thepinkmile/Enigma-NG/.copilot/checkpoints/179-stack-interposer-board-design-complete.md

# Checkpoint 179 — Stack-Interposer Board Design Complete

**Date:** 2026-07-25
**Session work:** Stack-Interposer Board design files created; connector decisions locked; library imports completed; front-view diagram added.

---

## Todo closed this session

| Todo | Status |
| --- | --- |
| `merge-create-stack-interposer` | ✅ done |

---

## Files created

| File | Description |
| --- | --- |
| `design/Electronics/Stack-Interposer/Design_Spec.md` | Full design specification — FR/DR, interconnects, stackup, BOM |
| `design/Electronics/Stack-Interposer/Board_Layout.md` | Pinout reference — J1/J2 connector MPNs, 2×15 pin map, mirror-routing note |
| `design/Datasheets/Samtec-sqt-tmmh-datasheet.md` | Markdown datasheet generated from Samtec-sqt-tmmh-datasheet.pdf |
| `design/Diagrams/renders/03-Mini-Stack-Front-View.png` | Front-elevation render of Rotor Mini-Stack |

---

## Files modified

| File | Change |
| --- | --- |
| `design/Diagrams/cypher-system-layout.drawio` | New page "Mini-Stack Front View" added (page 3) |
| `design/Electronics/Stack-Output/Design_Spec.md` | J6 connector updated: 2BHR-30-VUA → SQT-115-01-L-D-RA; DR-SOUT-06 updated |
| `design/Electronics/Stack-Input/Design_Spec.md` | J6 mating connector reference updated: 2BHR-30-VUA → TMMH-115-01-L-D-ES; DR-SIN-02 pinout ref resolved |
| `design/Datasheets/_generated_markdown_inventory.json` | Entry added for Samtec-sqt-tmmh-datasheet |
| `src/Electronics/Library/SamacSys_Parts.kicad_sym` | TMMH-115-01-L-D-ES + SQT-115-01-L-D-RA + 9 other parts completed |
| `src/Electronics/Library/SamacSys_Parts.lib` / `.dcm` | Same parts — legacy symbol/desc entries added |
| `src/Electronics/Library/SamacSys_Parts.mod` | Same parts — $MODULE blocks added |
| `src/Electronics/Library/SamacSys_Parts.pretty/` | TMMH-115-01-L-D-ES.kicad_mod + SQT-115-01-L-D-RA.kicad_mod + 9 others |
| `src/Electronics/Library/SamacSys_Parts.3dshapes/` | .stp files added for all imported parts |
| `src/Electronics/Library/3D_Models/` | .step files added for all imported parts |
| `src/Electronics/Library/LIBRARY_NOTES.md` | Component inventory + naming equivalences updated |
| `.copilot/agent-scripts/generate_markdown_datasheets.py` | Hardcoded `C:\` path replaced with `Path(__file__).resolve().parent.parent.parent` |
| `.copilot/todos/todos.sql` | merge-create-stack-interposer: pending → done |
| `.copilot/todos/index.md` | merge-create-stack-interposer: file link removed, status done |

---

## Key design decisions

| Decision | Detail |
| --- | --- |
| Stack-Interposer connectors | J1 and J2: TMMH-115-01-L-D-ES (Samtec 30-position 2×15 straight/vertical male) |
| Stack-Output J6 connector | Changed from 2BHR-30-VUA (Adam Tech THT male) to SQT-115-01-L-D-RA (Samtec RA female) — now matches Stack-Input J6 |
| Stack-Input J6 connector | SQT-115-01-L-D-RA (Samtec RA female) — unchanged, confirmed correct |
| Mirror-corrected routing | J1/J2 pin map is pin-to-pin (pin n → pin n); because connectors face each other in mirrored orientation, L2/L3 traces must be laid out as if mirrored (traces will cross). Rows preserved; documented in DR-SINT-04 and Board_Layout.md §3. |
| German data plate name | STAPELBRUCKE (printed on board as STAPELBRÜCKE) |
| Stackup | 4-layer standard GRS §2.3.1; GND pours on L1/L4; all signal traces on L2/L3 |

---

## Library imports completed

| Part | Type | Notes |
| --- | --- | --- |
| TMMH-115-01-L-D-ES | New — all 4 formats | Samtec 2×15 straight/vertical male; mating connector for Stack-Interposer J1/J2 |
| SQT-115-01-L-D-RA | Completed — was missing .pretty, .3dshapes, 3D_Models | Samtec 2×15 RA female; Stack-Input and Stack-Output J6 |
| 3310P-001-503L | Completed — was missing fp, .mod, .step | Bourns rotary potentiometer (Input-Cypher brightness dial) |
| APFA2507Y2G2C-C2 | Completed — was missing lib, dcm, fp, .mod, stp, step | Kingbright bicolor LED |
| DF40C-10DP/10DS/24DP/24DS/90DP/90DS-0.4V(51) | Completed — 6 parts | Hirose BtB connector family |
| PG151101S11 | Completed — was missing fp, .mod, .stp | Kailh hot-swap socket |

---

## Next session start point

Follow `.copilot/SESSION_START.md`, then read checkpoint 179 and resume with `merge-create-cypher-input`.

**Next sub-task: `merge-create-cypher-input`** — keyboard input panel board (ENC module BtB + mechanical keyboard switches + LED circuit). See `design-discussion-merge.md` for scope.

After Cypher-Input:
- `merge-create-cypher-output` — lightboard output panel
- `merge-ctl-dock-usb-allocation` → `merge-update-ctl-board`
- `merge-cypher-board-j3j6-pinouts`
