thepinkmile/Enigma-NG/design/Datasheets/Samtec-sqt-tmmh-datasheet.md

# Series: 2.00 mm (.079”) Pitch Socket & Terminal Strip

## Source

- **Source PDF:** [Samtec-sqt-tmmh-datasheet.pdf](Samtec-sqt-tmmh-datasheet.pdf)
- **Generated Markdown:** `Samtec-sqt-tmmh-datasheet.md`
- **Page count:** 8
- **Conversion method:** automated local PDF text extraction with pypdf/pdfplumber

## PDF Metadata

| Field | Value |
| :--- | :--- |
| Title | «Picture_Description» is depicted |
| Author | John Tozier |
| Subject |  |
| Creator | Microsoft® Word for Microsoft 365 |
| Producer | Microsoft® Word for Microsoft 365 |

## Extracted Technical Index

This markdown datasheet is meant to reduce the need to reopen the PDF during design work.
It preserves design-relevant extracted snippets first, followed by page-by-page text so the source content remains locally searchable.

### Part number and ordering information

- 4.8.1 Traditional Standoffs (SO) – Rigid design to statically support board-to-board applications. See / options here: SO - Board Stacking Standoff / 4.8.2 Jack Screw Standoffs (JSO) – Serve sam…
- construction facilitates the mating and unmating process. This is especially helpful for multiple / connector applications where the mating and unmating forces increase with the number of / conn…

### Pin, pad, and connection designations

- Product Specification / Series: 2.00 mm (.079”) Pitch Socket & Terminal Strip / Revision: A Date: September 26, 2025 © Samtec, Inc.
- 1.1 This specification covers performance, test ing and quality requirements for Samtec’s 0.51mm (.020”) square post / socket and terminal strip. All information contained in this specification …
- 1.1 This specification covers performance, test ing and quality requirements for Samtec’s 0.51mm (.020”) square post / socket and terminal strip. All information contained in this specification …
- 2.0 DETAILED INFORMATION / 2.1 Product prints, footprints, catalog pages, test reports and other specific, detailed information can be found at / SQT: <https://www.samtec.com/products/sqt;> TMMH…
- 3.0 TESTING / 3.1 Current Rating: 5.1 A (One pin powered per row) / 3.2 Voltage Rating: 250 VAC / 3.3 Operating Temperature Range: Gold plating: -55°C to +125°C
- Nitrogen gas infusion) in the reflow process to improve solderability. / 4.8 Hardware: Board-to-board standoffs are recommended to provide a robust mechanical connection. Samtec offers / two dif…
- two different types: / 4.8.1 Traditional Standoffs (SO) – Rigid design to statically support board-to-board applications. See / options here: SO - Board Stacking Standoff
- 5.0 ADDITIONAL RESOURCES / 5.1 For additional mechanical testing or product information, contact our Customer Engineering Support Group at / <CES@samtec.com>
- <CES@samtec.com> / 5.2 For additional information on high speed performance testing, contact our Signal Integrity Group at / <SIG@samtec.com>
- This Product Specification Sheet (“PSS”) is a brief summary of information related to the Product identified. As a summary, it should / only be used for the limited purpose of considering the pu…

### Specifications, ratings, and operating conditions

- Product Specification / Series: 2.00 mm (.079”) Pitch Socket & Terminal Strip
- See <www.samtec.com> for more information. / Product Specification / Series: 2.00 mm (.079”) Pitch Socket & Terminal Strip
- 1.0 SCOPE / 1.1 This specification covers performance, test ing and quality requirements for Samtec’s 0.51mm (.020”) square post / socket and terminal strip. All information contained in this sp…
- 1.1 This specification covers performance, test ing and quality requirements for Samtec’s 0.51mm (.020”) square post / socket and terminal strip. All information contained in this specification …
- 3.0 TESTING / 3.1 Current Rating: 5.1 A (One pin powered per row) / 3.2 Voltage Rating: 250 VAC / 3.3 Operating Temperature Range: Gold plating: -55°C to +125°C
- 3.1 Current Rating: 5.1 A (One pin powered per row) / 3.2 Voltage Rating: 250 VAC / 3.3 Operating Temperature Range: Gold plating: -55°C to +125°C / 3.4 Operating Humidity Range: up to 95% (Per …
- 3.5 Electrical: / ITEM TEST CONDITION REQUIREMENT STATUS / Withstanding Voltage EIA-364-20 (No Flashover, / Sparkover, or Breakdown) 750 VAC Pass / Insulation Resistance EIA-364-21 (1000 MΩ
- Normal Force EIA-364-04 30 grams minimum for Gold / interface Pass / Product Specification / Series: 2.00 mm (.079”) Pitch Socket & Terminal Strip
- ITEM TEST CONDITION RESULT STATUS / Thermal Shock / EIA-364-32 / Thermal Cycles: 100 (30 minute dwell)
- Thermal Shock / EIA-364-32 / Thermal Cycles: 100 (30 minute dwell) / Hot Temp: +85°C / Cold Temp: -55°C
- IR: >10,000 MΩ / Pass / Thermal Aging / (Temp Life) / EIA-364-17
- Exposure / LLCR: Δ 15 mΩ Pass / Product Specification / Series: 2.00 mm (.079”) Pitch Socket & Terminal Strip
- 4.1.2 Allowable final linear misalignment / Product Specification / Series: 2.00 mm (.079”) Pitch Socket & Terminal Strip
- 4.2.2 Allowable final angular misalignment / Product Specification / Series: 2.00 mm (.079”) Pitch Socket & Terminal Strip
- These guidelines should not be considered design requirements for all applications. / Samtec recommends testing interconnects on your boards in your process to guarantee optimum results. / Produ…
- 5.4 For RoHS, REACH or other environmental compliance information, contact our Product Environmental / Compliance Group at <PEC@samtec.com> / Product Specification / Series: 2.00 mm (.079”) Pitc…
- Page 8 / USE OF PRODUCT SPECIFICATION SHEET / This Product Specification Sheet (“PSS”) is a brief summary of information related to the Product identified. As a summary, it should
- USE OF PRODUCT SPECIFICATION SHEET / This Product Specification Sheet (“PSS”) is a brief summary of information related to the Product identified. As a summary, it should / only be used for the …

### Dimensions, package, and mechanical information

- 2.0 DETAILED INFORMATION / 2.1 Product prints, footprints, catalog pages, test reports and other specific, detailed information can be found at / SQT: <https://www.samtec.com/products/sqt;> TMMH…
- (Samtec defined)/ No damage Pass / 3.6 Mechanical: / ITEM TEST CONDITION RESULT STATUS
- No Events / Pass / Mechanical Shock / EIA-364-27 100 G, 6 milliseconds, / Half Sine wave, 12.3 fps, 3
- Nitrogen gas infusion) in the reflow process to improve solderability. / 4.8 Hardware: Board-to-board standoffs are recommended to provide a robust mechanical connection. Samtec offers / two dif…
- 5.0 ADDITIONAL RESOURCES / 5.1 For additional mechanical testing or product information, contact our Customer Engineering Support Group at / <CES@samtec.com>
- This Product Specification Sheet (“PSS”) is a brief summary of information related to the Product identified. As a summary, it should / only be used for the limited purpose of considering the pu…

### Formulas, equations, and configurable calculations

- TMMH Series / Other configurations available for: / Through Hole, Right Angle
- 1.1 This specification covers performance, test ing and quality requirements for Samtec’s 0.51mm (.020”) square post / socket and terminal strip. All information contained in this specification …
- ITEM TEST CONDITION RESULT STATUS / Durability EIA-364-09C 100 cycles Pass / Random Vibration / EIA-364-28 Condition V, Letter B / 7.56 G 'RMS', 50 to 2000 Hz, 2
- Test Temp: +25°C to +65°C Relative / Humidity: 90 to 95% / Test Duration: 240 hours / Visual Inspection: No Damage / LLCR: Δ 15 mΩ
- EIA-364-36 / Gas Exposure: Nitric Acid Vapor / Duration: 60 min. / Drying Temp.: 50°C +/- 3°C / Measurements: Within 1 hour of

### Reference designs, applications, and examples

- Page 6 / 4.3 Due to variances in equipment, solder pastes and applications (board design, component density, etc.), Samtec / does not specify a recommended reflow profile for our connectors. The…
- 4.3.1 / These guidelines should not be considered design requirements for all applications. / Samtec recommends testing interconnects on your boards in your process to guarantee optimum results.…
- two different types: / 4.8.1 Traditional Standoffs (SO) – Rigid design to statically support board-to-board applications. See / options here: SO - Board Stacking Standoff
- 4.8.2 Jack Screw Standoffs (JSO) – Serve same function as traditional standoffs but unique, nested / construction facilitates the mating and unmating process. This is especially helpful for mult…

## Page-by-Page Extracted Content

### Page 1

```text
Product Specification

Series: 2.00 mm (.079”) Pitch Socket & Terminal Strip

Revision: A Date: September 26, 2025 © Samtec, Inc.
 Page 1
SQT Series

 TMMH Series

Other configurations available for:

Through Hole, Right Angle

See www.samtec.com for more information.
```

### Page 2

```text
Product Specification

Series: 2.00 mm (.079”) Pitch Socket & Terminal Strip

Revision: A Date: September 26, 2025 © Samtec, Inc.
 Page 2

1.0 SCOPE

1.1 This specification covers performance, test ing and quality requirements for Samtec’s 0.51mm (.020”) square post
socket and terminal strip. All information contained in this specification is for a surface mount socket / surface mount
terminal mated configuration unless otherwise noted.

2.0 DETAILED INFORMATION

2.1 Product prints, footprints, catalog pages, test reports and other specific, detailed information can be found at
SQT: https://www.samtec.com/products/sqt; TMMH: https://www.samtec.com/products/tmmh

3.0 TESTING

3.1 Current Rating: 5.1 A (One pin powered per row)
3.2 Voltage Rating: 250 VAC
3.3 Operating Temperature Range: Gold plating: -55°C to +125°C
3.4 Operating Humidity Range: up to 95% (Per EIA-364-31)
3.5 Electrical:
ITEM TEST CONDITION REQUIREMENT STATUS
Withstanding Voltage EIA-364-20 (No Flashover,
Sparkover, or Breakdown) 750 VAC Pass
Insulation Resistance EIA-364-21 (1000 MΩ
minimum) >10,000 MΩ Pass
Contact Resistance
(LLCR) EIA-364-23 Δ 15 mΩ maximum
(Samtec defined)/ No damage Pass

3.6 Mechanical:

ITEM TEST CONDITION RESULT STATUS
Durability EIA-364-09C 100 cycles Pass
Random Vibration
EIA-364-28 Condition V, Letter B
7.56 G 'RMS', 50 to 2000 Hz, 2
hours per axis, 3 axis total , PSD
0.04 Nanosecond Event Detection:
EIA-364-87
Visual Inspection: No Damage
LLCR: Δ 15 mΩ
No Events
Pass
Mechanical Shock
EIA-364-27 100 G, 6 milliseconds,
Half Sine wave, 12.3 fps, 3
shocks/direction, 3 axis (18 total
shocks) Nanosecond Event
Detection: EIA-364-87
Visual Inspection: No Damage
LLCR: Δ 15 mΩ
No Events
Pass
Normal Force EIA-364-04 30 grams minimum for Gold
interface Pass
```

### Page 3

```text
Product Specification

Series: 2.00 mm (.079”) Pitch Socket & Terminal Strip

Revision: A Date: September 26, 2025 © Samtec, Inc.
 Page 3

3.7 Environmental:

ITEM TEST CONDITION RESULT STATUS
Thermal Shock
EIA-364-32
Thermal Cycles: 100 (30 minute dwell)
Hot Temp: +85°C
Cold Temp: -55°C
Hot/Cold Transition: Immediate
Visual Inspection: No Damage
LLCR: Δ 15 mΩ
DWV: 750 VAC
IR: >10,000 MΩ
Pass
Thermal Aging
(Temp Life)
EIA-364-17
Test Condition 4 @ 105°C
Condition B for 250 hours
Visual Inspection: No Damage
LLCR: Δ 15 mΩ Pass
Cyclic Humidity
EIA-364-31
Test Temp: +25°C to +65°C Relative
Humidity: 90 to 95%
Test Duration: 240 hours
Visual Inspection: No Damage
LLCR: Δ 15 mΩ
DWV: 750 VAC
IR: >10,000 MΩ
Pass
Gas Tight
EIA-364-36
Gas Exposure: Nitric Acid Vapor
Duration: 60 min.
Drying Temp.: 50°C +/- 3°C
Measurements: Within 1 hour of
Exposure
LLCR: Δ 15 mΩ Pass
```

### Page 4

```text
Product Specification

Series: 2.00 mm (.079”) Pitch Socket & Terminal Strip

Revision: A Date: September 26, 2025 © Samtec, Inc.
 Page 4

4.0 PROCESSING RECOMMENDATIONS:

4.1 Mating Alignment Requirements:

4.1.1 Allowable initial linear misalignment

4.1.2 Allowable final linear misalignment
```

### Page 5

```text
Product Specification

Series: 2.00 mm (.079”) Pitch Socket & Terminal Strip

Revision: A Date: September 26, 2025 © Samtec, Inc.
 Page 5

4.2 Mating Angle Requirements:

4.2.1 Allowable initial angular misalignment

4.2.2 Allowable final angular misalignment
```

### Page 6

```text
Product Specification

Series: 2.00 mm (.079”) Pitch Socket & Terminal Strip

Revision: A Date: September 26, 2025 © Samtec, Inc.
 Page 6

4.3 Due to variances in equipment, solder pastes and applications (board design, component density, etc.), Samtec
does not specify a recommended reflow profile for our connectors. The processing parameters provided by the
solder paste manufacturer should be employed and can usually be found on their website.

All of Samtec’s surface mount components are lead free reflow compatible and compliant with the profile
parameters detailed in IPC/JEDEC J-STD-020 which requires that components be capable of withstanding a peak
temperature of 260°C as well as 30 seconds above 255°C.

Samtec Recommended Temperature Profile Ranges (SMT)

Sn-Pb Eutectic Assembly

Preheat/Soak
(100°C-150°C)
Max Ramp Up
Rate
Reflow Time
(above 183°C)
Peak
Temp
Time within 5°C
of 235°C
Max Ramp
Down Rate
Time 25°C to
Peak Temp
60-120 sec. 3°C/s max. 40-150 sec. 235°C 20 sec. max. 6°C/s max. 6 min. max.

Pb-Free Assembly

Preheat/Soak
(150°C-200°C)
Max Ramp Up
Rate
Reflow Time
(above 217°C)
Peak
Temp
Time within 5°C
of 260°C
Max Ramp
Down Rate
Time 25°C to
Peak Temp
60-120 sec. 3°C/s max. 40-150 sec. 260°C 30 sec. max. 6°C/s max. 8 min. max.

4.3.1

These guidelines should not be considered design requirements for all applications.
Samtec recommends testing interconnects on your boards in your process to guarantee optimum results.
```

### Page 7

```text
Product Specification

Series: 2.00 mm (.079”) Pitch Socket & Terminal Strip

Revision: A Date: September 26, 2025 © Samtec, Inc.
 Page 7

4.4 Maximum Reflow Passes: The parts can withstand three reflow passes at a maximum component temperature of
260°C.

4.5 Stencil Thickness: The stencil thickness is 0.15mm [.006”].

4.6 Placement: Machine placement of the parts in the Z-axis is strongly recommended.

4.7 Reflow Environment: Samtec recommends the use of a low level oxygen environment (typically achieved through
Nitrogen gas infusion) in the reflow process to improve solderability.

4.8 Hardware: Board-to-board standoffs are recommended to provide a robust mechanical connection. Samtec offers
two different types:

4.8.1 Traditional Standoffs (SO) – Rigid design to statically support board-to-board applications. See
options here: SO - Board Stacking Standoff

4.8.2 Jack Screw Standoffs (JSO) – Serve same function as traditional standoffs but unique, nested
construction facilitates the mating and unmating process. This is especially helpful for multiple
connector applications where the mating and unmating forces increase with the number of
connectors used. See options here: JSO - Jack Screw Standoffs

4.9 Cleaning: Samtec, Inc. has verified that our connectors may be cleaned in accordance with the solvents
 and conditions designated in the EIA-364-11 standard.

5.0 ADDITIONAL RESOURCES

5.1 For additional mechanical testing or product information, contact our Customer Engineering Support Group at
CES@samtec.com

5.2 For additional information on high speed performance testing, contact our Signal Integrity Group at
SIG@samtec.com

5.3 For additional processing information, contact our Interconnect Processing Group at IPG@samtec.com.

5.4 For RoHS, REACH or other environmental compliance information, contact our Product Environmental
Compliance Group at PEC@samtec.com
```

### Page 8

```text
Product Specification

Series: 2.00 mm (.079”) Pitch Socket & Terminal Strip

Revision: A Date: September 26, 2025 © Samtec, Inc.
 Page 8

USE OF PRODUCT SPECIFICATION SHEET

This Product Specification Sheet (“PSS”) is a brief summary of information related to the Product identified. As a summary, it should
only be used for the limited purpose of considering the purchase/use of Product. For specific, detailed information, includi ng but not
limited to testing and Product footprint, refer to Section 2.0 of this document and the links there provided to test reports and prints. This
PSS is the property of Samtec, Inc. (“Samtec”) and contains proprietary information of Samtec, our various licensors, or both . Samtec
does not grant express or implied rights or license under any patent, copyright, trademark or other proprietary rights and th e use of the
PSS for building, reverse engineering or replication is strictly prohibited. By using the PSS, the user agrees to not infring e, directly or
indirectly, upon any intellectual property rights of Samtec and acknowledges that Samtec, our various licensors, or both own all
intellectual property therein. The PSS is presented “AS IS”. While Samtec makes every effort to present excellent information, the PSS
is only provided as a guideline and does not, therefore, warrant it is without error or defect or that the PSS contains all necessary and/or
relevant information about the Product. The user agrees that all access and use of the PSS is at its own risk. NO WARRANTIES
EXPRESSED OR IMPLIED, INCLUDING ANY WARRANTY OF MERCHANTABILITY, FITNESS FOR A PARTICULAR
PURPOSE OR OF ANY KIND WHATSOEVER ARE PROVIDED.
```
