thepinkmile/Enigma-NG/.copilot/todos/design-discussion-merge.md

# Merge design discussions into main design

**ID:** design-discussion-merge
**Status:** in-progress
**Category:** Electronics / Software / Mechanical
**Source:** User direction 2026-07-05
**Blocked by:** —

---

## Description

Top-level tracking item for the full migration of all decisions from
.copilot/discussions/cypher-system-discussion/ into the main design documentation.
Covers new board creation, CTL board updates, GRS updates, reviews, and BOM work.

## Notes

Sub-tasks (in approximate execution order):
1. merge-grs-6layer-stackup — GRS §2.3.x for 6-layer boards (NEXT)
2. merge-create-cypher-board — Cypher Board Design_Spec and Board_Layout (in-progress)
3. merge-cypher-board-j3j6-pinouts — Full 50-pin J3-J6 allocation
4. merge-ctl-dock-usb-allocation — USB D+/D- pin alloc in J1
5. merge-create-stack-input, merge-create-stack-output, merge-create-stack-blanking, merge-create-stack-interposer
6. merge-update-ctl-board
7. merge-create-cypher-input, merge-create-cypher-output
8. merge-update-top-level-docs
9. merge-remove-old-boards
10. merge-consistency-review, merge-missing-components, merge-final-review
