thepinkmile/Enigma-NG/.copilot/checkpoints/175-unified-cypher-extension-spec-created-awaiting-completeness-review.md

# Checkpoint 175: Unified Cypher/Extension Spec Created; Completeness Review Pending

**Date**: 2026-06-07  
**Status**: Complete  
**Scope**: Discussion/state consolidation only (no design implementation changes)

## Summary

Created a consolidated point-in-time design modification specification:

- `.copilot/discussions/cypher-extension-unified-discussion.md`

This file merges architecture, grounding model, interconnect maps, signal flows,
component baseline, and active-design modification tracking into one standalone
discussion/specification document.

## Work Completed

1. Created unified specification file with embedded implementation-critical content:
   - new board architecture and lifecycle intent,
   - `GND_CHASSIS` domain model + single-point bond constraints,
   - chassis ring geometry + connector-zone caveat,
   - Cypher interconnect pin map,
   - passive base-board 2x15 map,
   - `SIG-BLOCK-A..I` group table and explicit electronic flow descriptions,
   - consolidated component/procurement baseline,
   - active-design change matrix by standards/board.
2. Updated naming consistency (`GND_CHASSIS`) across the cypher grounding discussion.
3. Aligned board naming to active names (Cypher, Stack-Input, Stack-Output, Stack-Blanking).
4. Updated topology visual orientation in the unified file; user then finalized both unified and source discussion diagrams.
5. Synced session state files for new-session continuity:
   - `.copilot/plan.md`
   - `.copilot/handoff.md`

## Current Risk / Pending Validation

The unified file is now structurally complete, but user has flagged likely missing
historical detail due to the size/depth of the original extension discussion.

Pending work is a user-led completeness pass to identify gaps, followed by direct
patches to the unified file.

## Files Updated

- `.copilot/discussions/cypher-extension-unified-discussion.md` (new)
- `.copilot/discussions/cypher-block-connectors.md` (multiple consolidation/clarity updates)
- `.copilot/discussions/extension-mechanical-usage.md` (diagram iteration; final state user-adjusted)
- `.copilot/plan.md`
- `.copilot/handoff.md`
- `.copilot/checkpoints/index.md`
- `.copilot/checkpoints/175-unified-cypher-extension-spec-created-awaiting-completeness-review.md` (new)

## Next Start Hint

Resume from the unified specification review:

1. Read `.copilot/discussions/cypher-extension-unified-discussion.md` end-to-end.
2. Capture missing-detail list from user.
3. Patch only the unified file until user confirms it is complete and self-contained.
4. Do not start implementation into active design files until explicit user instruction.
