thepinkmile/Enigma-NG/design/Datasheets/2bhr-xx-vua-data-sheet.md

# Adam Tech 2BHR-XX-VUA 2.00 mm dual-row box header (dual-keyed)

## Source Reference

- Source PDF: [2bhr-xx-vua-data-sheet.pdf](2bhr-xx-vua-data-sheet.pdf)
- Source path: `design\Datasheets\2bhr-xx-vua-data-sheet.pdf`
- Generated markdown: `2bhr-xx-vua-data-sheet.md`
- Structured datasheet (JSON): [2BHR-30-VUA-structured-datasheet.json](2BHR-30-VUA-structured-datasheet.json) — comprehensive specifications generated via Google AI analysis
- Page count: 1
- Extracted text characters: 0
- Empty extraction pages: 1
- Conversion method: automated local PDF text extraction with pypdf and pdfplumber
- **Correction note (2026-06-06):** Pitch corrected from incorrectly assumed 2.54 mm to actual 2.00 mm per datasheet review. All specifications verified against Google AI–generated structured datasheet.

## Reviewed Summary

- Exact family: Adam Tech 2BHR-XX-VUA.
- Product: 2-row dual-keyed box header, vertical PCB mount, 2.00 mm pitch (0.0787 in), gold-flash plated.
  Dual-keyed variant of the BHR-XX-VUA series; polarisation key is present at both ends of the
  shroud to prevent misinsertion from either orientation.
- Pin counts available: series covers multiple positions (XX = number of positions per row x 2).
  The 30-pin variant (2x15) is `2BHR-30-VUA`.
- Dimensions / pattern: based on 2.00 mm pitch spacing - dimensions scale accordingly from base dimensions.
- Electrical / environmental: 250 VAC max, 2 A max per pin, 20 mΩ max contact resistance,
  5000 MΩ min insulation resistance, 500 VAC / minute dielectric withstand, -40 to +105 °C.
- Materials: PBT or Nylon 6T UL94V-0 insulator (black), brass or phosphor bronze contacts, gold flash over nickel underplate.
- Mating durability: 100 cycles minimum.
- Dimensions (2x15 variant): overall length A = 35.10 mm, shroud length B = 33.10 mm.

## Approved Part Numbers - 2BHR-30-VUA (30-pin, 2x15)

| Supplier | Part Number | Notes |
| :--- | :--- | :--- |
| DigiKey | 2057-2BHR-30-VUA-ND | MOQ 3000 (for reference only) |
| Mouser | 737-2BHR-30-VUA | MOQ 3000 (for reference only) |
| JLCPCB | C17346400 | MOQ 3 |

## Extraction Notes

- Native extraction was empty; this is an image-only mechanical drawing PDF.
- Reviewed summary and electrical specifications are taken from the same Adam Tech series datasheet
  as `bhr-xx-vua-data-sheet.md` - the 2BHR variant shares identical electrical ratings.

## Page-by-Page Extracted Content

### Page 1

_No text could be extracted from this page with the current local extractor. This is a
mechanical drawing / image-only PDF._
