thepinkmile/Enigma-NG/design/Datasheets/Samtec-sqt-1xx-xx-xxx-x-xxx-xxx-mkt-datasheet.md

# Samtec SQT-115-01-L-D-RA — 30-position shrouded rugged PCB socket (right-angle, 2.00 mm pitch)

## Source Reference

- Source PDF: [Samtec-sqt-1xx-xx-xxx-x-xxx-xxx-mkt-datasheet.pdf](Samtec-sqt-1xx-xx-xxx-x-xxx-xxx-mkt-datasheet.pdf)
- Source path: `design\Datasheets\Samtec-sqt-1xx-xx-xxx-x-xxx-xxx-mkt-datasheet.pdf`
- Generated markdown: `Samtec-sqt-1xx-xx-xxx-x-xxx-xxx-mkt-datasheet.md`
- Page count: 3
- Conversion method: automated local PDF text extraction with pypdf/pdfplumber

## Reviewed Summary

- **Exact family:** Samtec SQT-1XX-XX-XXX-X-XXX-XXX series
- **Product:** 30-position (15 × 2) shrouded rugged PCB socket, female IDC, right-angle mount, 2.00 mm pitch (0.0787 in)
- **Mating:** Mates with 2BHR-XX-VUA male headers (same pitch, dual-row configuration)
- **Contacts:** Brass, gold-flash plated
- **Insulation:** PBT (polybutylene terephthalate)
- **Electrical:** 2 A per contact, 500 V AC (1 min dielectric), 100-cycle durability per IPC-1212
- **Operating range:** −40°C to +105°C
- **Compliance:** Lead-free, RoHS-compliant

---

## PDF Metadata

| Field | Value |
| :--- | :--- |
| Title | SQT-1XX-XX-XXX-X-XXX-XXX-MKT |
| Author | SAMTECNT\34506 (DG-TOBINQIN) |
| Subject | - |
| Creator | SOLIDWORKS 2019 SP5.0 (2019304) |
| Producer | SOLIDWORKS PDF Publisher |

## Extracted Technical Index

This markdown datasheet is meant to reduce the need to reopen the PDF during design work.
It preserves design-relevant extracted snippets first, followed by page-by-page text so the source content remains locally searchable.

### Part number and ordering information

- -STL: 30µ" SELECTIVE GOLD IN CONTACT AREA, / SnPb ON TAIL. / POLARIZATION OPTION / -XXX: INDICATES POSITION / (SEE NOTE 10)
- -XXX: INDICATES POSITION / (SEE NOTE 10) / OPTION / -RA: RIGHT ANGLE / (-01 LEAD STYLE, ROWS -S, -D, -T ONLY)
- 02 / \* = NOT RELEASED FOR PRODUCTION / \*\* = MW OPTION, DO NOT DESIGN IN, SAMTEC WILL / ONLY SUPPORT EXISTING BUSINESS 02/06/2002 / C

### Pin, pad, and connection designations

- \* = NOT RELEASED FOR PRODUCTION / \*\* = MW OPTION, DO NOT DESIGN IN, SAMTEC WILL / ONLY SUPPORT EXISTING BUSINESS 02/06/2002 / C / C
- (5 POS MIN, 30 POS MAX) / \*\* -MW OPION, DO NOT DESIGN IN. SAMTEC WILL / ONLY SUPPORT EXISTING BUSINESS 2/06/02. / SHEET OF / 2MM SOCKET STRIP ASSEMBLY

### Specifications, ratings, and operating conditions

- (PER ROW) / -01 (SEE NOTE 3) / ROW SPECIFICATION / -S: SINGLE (USE SQT-61-S) / -D: DOUBLE (USE SQT-62-D)
- LEAD STYLE / (SEE TABLE 1) / PLATING SPECIFICATION / -F: 3µ" SELECTIVE GOLD IN CONTACT AREA, / MATTE TIN ON TAIL.
- UNLESS OTHERWISE SPECIFIED, / DIMENSIONS ARE IN INCHES. / TOLERANCES ARE: / DECIMALS ANGLES / .XX: .01 [.3] 2

### Dimensions, package, and mechanical information

- SHEET OF / UNLESS OTHERWISE SPECIFIED, / DIMENSIONS ARE IN INCHES. / TOLERANCES ARE: / DECIMALS ANGLES
- SQT-1XX-XX-XXX-X-XXX-XXX / DWG. NO. / DESCRIPTION:DO NOT SCALE DRAWING / BRATCHER 07/24/1995 31 / SHEET SCALE: 2:1
- MAX BOW ALLOWED: .004[.10] IN/IN / NOTES: / 1. REPRESENTS A CRITICAL DIMENSION. / 2. MINIMUM CONTACT RETENTION: .5 LB / 3. -01 POSITION OFFERED FOR SINGLE ROW& ONLY FOR -S, -D, & -T
- DWG. NO. / DESCRIPTION: / DO NOT SCALE DRAWING / BRATCHER 07/24/1995 32 / SHEET SCALE: 2:1
- DWG. NO. / DESCRIPTION: / DO NOT SCALE DRAWING / BRATCHER 07/24/1995 33 / SHEET SCALE: 1:1

### Formulas, equations, and configurable calculations

- No reliable text snippet was automatically extracted for this category. Review the raw page text below.

### Reference designs, applications, and examples

- No reliable text snippet was automatically extracted for this category. Review the raw page text below.

## Page-by-Page Extracted Content

### Page 1

```text
THIS DOCUMENT CONTAINS CONFIDENTIAL AND
PROPRIETARY INFORMATION AND ALL DESIGN,
MANUFACTURING, REPRODUCTION, USE, PATENT RIGHTS
AND SALES RIGHTS ARE EXPRESSLY RESERVED BY SAMTEC,
INC. THIS DOCUMENT SHALL NOT BE DISCLOSED, IN WHOLE
OR PART, TO ANY UNAUTHORIZED PERSON OR ENTITY NOR
REPRODUCED, TRANSFERRED OR INCORPORATED IN ANY
OTHER PROJECT IN ANY MANNER WITHOUT THE EXPRESS
WRITTEN CONSENT OF SAMTEC, INC.
PROPRIETARY NOTE* *
DO NOT
SCALE FROM
THIS PRINT
No OF POSITIONS
-02 THRU -50
 (PER ROW)
-01 (SEE NOTE 3)
ROW SPECIFICATION
-S: SINGLE (USE SQT-61-S)
-D: DOUBLE (USE SQT-62-D)
-T: TRIPLE (USE SQT-62-T)
-Q: QUAD (USE SQT-62-Q)
-5: FIVE ROW (USE SQT-62-5)
-6: SIX ROW (USE SQT-62-6)
LEAD STYLE
(SEE TABLE 1)
PLATING SPECIFICATION
-F: 3µ" SELECTIVE GOLD IN CONTACT AREA,
 MATTE TIN ON TAIL.
-L: 10µ" SELECTIVE GOLD IN CONTACT AREA,
 MATTE TIN ON TAIL.
-G: 20µ" SELECTIVE GOLD IN CONTACT AREA,
 3µ" SELECTIVE GOLD ON TAIL.
-S: 30µ" SELECTIVE GOLD IN CONTACT AREA,
 MATTE TIN ON TAIL.
-H: 50µ" SELECTIVE GOLD IN CONTACT AREA,
 3µ" SELECTIVE GOLD ON TAIL.
-FM: 3µ" SELECTIVE GOLD IN CONTACT AREA,
 MATTE TIN ON TAIL.
-LM: 10µ" SELECTIVE GOLD IN CONTACT AREA,
 MATTE TIN ON TAIL.
-SM: 30µ" SELECTIVE GOLD IN CONTACT AREA,
 MATTE TIN ON TAIL.
-STL: 30µ" SELECTIVE GOLD IN CONTACT AREA,
 SnPb ON TAIL.
POLARIZATION OPTION
-XXX: INDICATES POSITION
 (SEE NOTE 10)
OPTION
-RA: RIGHT ANGLE
 (-01 LEAD STYLE, ROWS -S, -D, -T ONLY)
 (NOT AVAILABLE ON -Q, -5 & -6 ROWS)
 (SINGLE, DOUBLE, TRIPLE ROW: SEE FIG 2, SHT 2)
 *-SD1: SOLDER DONUT (SEE FIG 3, SHT 2)
 (AVAILABLE ON -S, -D, -T ONLY)
**-MW: METAL WASHER (SHT 2, SEE FIG 4)
 (AVAILABLE ON LEAD STYLES -01 & -03 ONLY)
 (5 POS MIN, 30 POS MAX, .300 MAX TAIL)
SQT-1XX-XX-XXX-X-XXX-XXX
.015 0.38
REF
.250 6.35
REF
"A"
.0197 0.500
SQ REF (TYP)
.064 1.63 REF
2 MAX SWAY
(EITHER DIRECTION)
FIG 1
SQT-120-01-XX-6 SHOWN
(SEE NOTE 7)
{(No OF POS x .0787[2.000]) + .0117[0.300] ± .010[0.25]
(No OF POS x .0787[2.000] - .0787[2.000] REF
.0787 2.000
REF (TYP)
01
"B" REF
2 MAX SWAY
(EITHER DIRECTION)
C-79-XX-X
(SEE TABLE 1)
SQT-XX-X
(SEE TABLE 3)
01 02
(POSITON PATTERN SINGLE ROW ONLY)
C
02
 * = NOT RELEASED FOR PRODUCTION
** = MW OPTION, DO NOT DESIGN IN, SAMTEC WILL
 ONLY SUPPORT EXISTING BUSINESS 02/06/2002
C
C
SHEET OF
UNLESS OTHERWISE SPECIFIED,
DIMENSIONS ARE IN INCHES.
TOLERANCES ARE:
DECIMALS ANGLES
.XX: .01 [.3] 2
.XXX: .005 [.13]
.XXXX: .0020 [.051]
MATERIAL:
2MM SOCKET STRIP ASSEMBLY
BY:
SQT-1XX-XX-XXX-X-XXX-XXX
DWG. NO.
DESCRIPTION:DO NOT SCALE DRAWING
BRATCHER 07/24/1995 31
SHEET SCALE: 2:1
INSULATOR: LCP, UL 94 VO, COLOR: BLACK
CONTACT: PHOS BRONZE
REVISION CJ
F:\DWG\MISC\MKTG\SQT-1XX-XX-XXX-X-XXX-XXX-MKT.SLDDRW
MAX BOW ALLOWED: .004[.10] IN/IN
NOTES:
1. REPRESENTS A CRITICAL DIMENSION.
2. MINIMUM CONTACT RETENTION: .5 LB
3. -01 POSITION OFFERED FOR SINGLE ROW& ONLY FOR -S, -D, & -T
 ROWS RIGHT ANGLE ONLY.
4. SEE TABLE 2, SHEET 3 FOR PACKAGING.
5. STOCK 62 POSITION FOR -D AND 61 POSITION FOR
 -S, -01 LEAD STYLE ONLY. TO BE CUT TO POSITION FOR CUSTOMER.
6. MAXIMUM BURR: .005[0.13]
7. ENDWALL AFTER CUTTING: .031[.79]+/-.004[0.10], VOIDS MAY BE PRESENT.
 CONTACTS MUST NOT BE VISIBLE THROUGH THE ENDWALL
8. MAXIMUM CUT FLASH: .020[0.50]
9. MAXIMUM HEIGHT VARIATION: .005[0.13]
10. INSERT PK-07-N INTO SPECIFIED POSITION AND BREAK OFF TAB.
520 PARK EAST BLVD, NEW ALBANY, IN 47150
PHONE: 812-944-6733 FAX: 812-948-5047
e-Mail info@SAMTEC.com code 55322
```

### Page 2

```text
THIS DOCUMENT CONTAINS CONFIDENTIAL AND
PROPRIETARY INFORMATION AND ALL DESIGN,
MANUFACTURING, REPRODUCTION, USE, PATENT RIGHTS
AND SALES RIGHTS ARE EXPRESSLY RESERVED BY SAMTEC,
INC. THIS DOCUMENT SHALL NOT BE DISCLOSED, IN WHOLE
OR PART, TO ANY UNAUTHORIZED PERSON OR ENTITY NOR
REPRODUCED, TRANSFERRED OR INCORPORATED IN ANY
OTHER PROJECT IN ANY MANNER WITHOUT THE EXPRESS
WRITTEN CONSENT OF SAMTEC, INC.
PROPRIETARY NOTE* *
TOP VIEW
TOOLING
OPERATOR
REEL
FRONT VIEW
OPERATORREEL
WASHER REEL ASSEMBLY
ORIENTATION VIEW
90°
.600 15.24.208 5.28
.050±.010 1.27±0.25
.0787±.0050 (TYP)2.000±0.127
.090±.010 2.29±0.254
R.025 0.64
SQT-XX-X
(SEE TABLE 3)
C-79-53-X
(SHEAR TO LENGTH)
C-79-12-X
(SHEAR TO LENGTH)
C-79-12-X
(SHEAR TO LENGTH)
C
01
02
01 02
(POSITON PATTERN SINGLE row ONLY).0200 0.508
REFSD1
'A'
.065 1.65
REF
.025 0.64
REF
DETAIL 'A'
SCALE 4 : 1
'B'
.0030 MAX0.076
MEASURE AT THE TAIL
.0050 MAX0.127
MEASURE AT THE TAIL
2 MAX SWAY
(EITHER DIRECTION)
DETAIL 'B'
SCALE 6 : 1
SQT-01-MW-T
90°
.600 15.24
IN PROCESS 3
(LEAD STYLE -01-T-RA)
IN PROCESS 1
(LEAD STYLE -01-S,D,T-RA)
IN PROCESS 2
(LEAD STYLE -01-D,T-RA)
FIG 2
-RA: RIGHT ANGLE
(LEAD STYLE -01-S,D,T)
FIG 3
*-SD1: SOLDER DONUT
(ONE PER POSITION)
(ROW STYLE -S,-D,-T & -Q ONLY)
*NOT ENGINEERING APPROVED
FIG 4
**-MW: METAL WASHER
(ONE PER POSITION)
(AVAILABLE ON LEADSTYLES -01 & -03 ONLY
(5 POS MIN, 30 POS MAX)
** -MW OPION, DO NOT DESIGN IN. SAMTEC WILL
ONLY SUPPORT EXISTING BUSINESS 2/06/02.
SHEET OF
2MM SOCKET STRIP ASSEMBLY
BY:
SQT-1XX-XX-XXX-X-XXX-XXX
DWG. NO.
DESCRIPTION:
DO NOT SCALE DRAWING
BRATCHER 07/24/1995 32
SHEET SCALE: 2:1
REVISION CJ
F:\DWG\MISC\MKTG\SQT-1XX-XX-XXX-X-XXX-XXX-MKT.SLDDRW
520 PARK EAST BLVD, NEW ALBANY, IN 47150
PHONE: 812-944-6733 FAX: 812-948-5047
e-Mail info@SAMTEC.com code 55322
```

### Page 3

```text
THIS DOCUMENT CONTAINS CONFIDENTIAL AND
PROPRIETARY INFORMATION AND ALL DESIGN,
MANUFACTURING, REPRODUCTION, USE, PATENT RIGHTS
AND SALES RIGHTS ARE EXPRESSLY RESERVED BY SAMTEC,
INC. THIS DOCUMENT SHALL NOT BE DISCLOSED, IN WHOLE
OR PART, TO ANY UNAUTHORIZED PERSON OR ENTITY NOR
REPRODUCED, TRANSFERRED OR INCORPORATED IN ANY
OTHER PROJECT IN ANY MANNER WITHOUT THE EXPRESS
WRITTEN CONSENT OF SAMTEC, INC.
PROPRIETARY NOTE* *
SQT-1XX-05-XX-X
(LOCATE PLUG AS SHOWN)
(SEE TABLE 2)
PACKAGING VIEWS
SQT-1XX-03-XX-6 SHOWN
(SEE TABLE 2)
SQT-1XX-01-XX-D-RA SHOWN
(LOCATE PLUG AS SHOWN)
(SEE TABLE 2)
SQT-1XX-02-XX-D
(LOCATE PLUG AS SHOWN)
(SEE TABLE 2)
SQT-1XX-01-XX-D
(SEE TABLE 2)
SQT-1XX-03-XX-S SHOWN
(SEE TABLE 2)
SHEET OF
2MM SOCKET STRIP ASSEMBLY
BY:
DWG. NO.
DESCRIPTION:
DO NOT SCALE DRAWING
BRATCHER 07/24/1995 33
SHEET SCALE: 1:1
REVISION CJ
F:\DWG\MISC\MKTG\SQT-1XX-XX-XXX-X-XXX-XXX-MKT.SLDDRW
520 PARK EAST BLVD, NEW ALBANY, IN 47150
PHONE: 812-944-6733 FAX: 812-948-5047
e-Mail info@SAMTEC.com code 55322
SQT-1XX-XX-XXX-X-XXX-XXX
```
