thepinkmile/Enigma-NG/design/Datasheets/Yageo-AT_series-datasheet.md

# ⚫ Moisture sensitivity level: MSL 1

## Source

- **Source PDF:** [Yageo-AT_series-datasheet.pdf](Yageo-AT_series-datasheet.pdf)
- **Generated Markdown:** `Yageo-AT_series-datasheet.md`
- **Page count:** 9
- **Conversion method:** automated local PDF text extraction with pypdf/pdfplumber

## PDF Metadata

| Field | Value |
| :--- | :--- |
| Title |  |
| Author | SerenaC |
| Subject |  |
| Creator | 適用於 Microsoft 365 的 Microsoft® Word |
| Producer | 適用於 Microsoft 365 的 Microsoft® Word |

## Extracted Technical Index

This markdown datasheet is meant to reduce the need to reopen the PDF during design work.
It preserves design-relevant extracted snippets first, followed by page-by-page text so the source content remains locally searchable.

### Part number and ordering information

- SERIES AT 0402 to 1206 / ORDERING INFORMATION - GLOBAL PART NUMBER / Part number is identified by the serie s name , size, tolerance, packaging / type , temperature coefficient, t aping reel and…
- ORDERING INFORMATION - GLOBAL PART NUMBER / Part number is identified by the serie s name , size, tolerance, packaging / type , temperature coefficient, t aping reel and resistance value.
- ⚫ Non-forbidden materials used in / products/production / ORDERING EXAMPLE / The orde ring code of a AT0402 chip resistor, TC 25 value 56Ω with ± / 0.5% tolerance, supplied in 7 -inch tape reel …
- 2. On customized label, "LFP" or specific symbol can be printed. / GLOBAL PART NUMBER / A T XXXX X X X XX XXXXX L / (1) (2) (3) (4) (5) (6) (7)
- 1K = 1,000Ω / (7) DEFAULT CODE / Letter L is the system default code for ordering only. (NOTE) / Chip Resistor Surface Mount
- SERIES AT 0402 to 1206 / MARKING / AT0402 / No marking
- MARKING / AT0402 / No marking / AT0603
- E-96 series: including values 10/11/13/15/20/75 of E -24 series, 3 digits / E-24 series: exception values 10/11/13/15/20/75 of E -24 series, one short bar / under marking letter / AT0805 / AT1206
- NOTE / For further marking information, please see special data sheet “Chip resistors marking ”. / Fig. 4 Value = 10 K Ω
- protective coat / marking layer / resistive layer / inner electrode
- ±10 (B) 50 ≤ R < 20K / ±5 (A) 50 ≤ R < 20K --- / NOTE : 1. Global part number (code 7) / 2. Global part number (code 9) / TYPE L (mm) W (mm) H (mm) I1 (mm) I2 (mm)>
- ±5 (A) 50 ≤ R < 20K --- / NOTE : 1. Global part number (code 7) / 2. Global part number (code 9) / TYPE L (mm) W (mm) H (mm) I1 (mm) I2 (mm) / AT0402 1.00 ±0.10 0.50 ±0.05 0.30 ±0.05 0.20 ±0.10 …>

### Pin, pad, and connection designations

- ORDERING INFORMATION - GLOBAL PART NUMBER / Part number is identified by the serie s name , size, tolerance, packaging / type , temperature coefficient, t aping reel and resistance value. / SCOPE
- (3) PACKAGING TYPE / R = Paper taping reel / (4) TEMPERATURE COEFFICIENT OF RESISTANCE / A = ± 5 ppm/°C
- D = ± 25 ppm/°C / E = ± 50 ppm/°C / (5) TAPING REEL / 07 = 7 inch dia. Reel / (6) RESISTANCE VALUE
- For recommended footprint and soldering profiles, please see th e spec ial data sheet “Chip resistors moun ting”. / PRODUCT TYPE PATKING STYLE REEL DIMENSION QUANTITY PER REEL / AT0402 Paper tap…
- PRODUCT TYPE PATKING STYLE REEL DIMENSION QUANTITY PER REEL / AT0402 Paper taping reel 7" (178 mm) 10,000 Units / AT0603 Paper taping reel 7" (178 mm) 5,000 Units / AT0805 Paper taping reel 7" (…
- AT0402 Paper taping reel 7" (178 mm) 10,000 Units / AT0603 Paper taping reel 7" (178 mm) 5,000 Units / AT0805 Paper taping reel 7" (178 mm) 5,000 Units / AT1206 Paper taping reel 7" (178 mm) 5,0…
- AT0603 Paper taping reel 7" (178 mm) 5,000 Units / AT0805 Paper taping reel 7" (178 mm) 5,000 Units / AT1206 Paper taping reel 7" (178 mm) 5,000 Units / NOTE: for paper tape and reel specificati…
- SMD conditions: / (a) Method B, aging 4 hours at 155 °C dry heat, / dipping at 235± 3 °C for 5± 0.5 seconds. / (b) Method B, steam aging 8 hours, dipping at / 215± 3 °C for 5± 0.5 seconds.
- (a) Method B, aging 4 hours at 155 °C dry heat, / dipping at 235± 3 °C for 5± 0.5 seconds. / (b) Method B, steam aging 8 hours, dipping at / 215± 3 °C for 5± 0.5 seconds. / (c) Method D, steam a…
- (b) Method B, steam aging 8 hours, dipping at / 215± 3 °C for 5± 0.5 seconds. / (c) Method D, steam aging 8 hours, dipping at / 260± 3 °C for 7± 0.5 seconds

### Specifications, ratings, and operating conditions

- sizes 0402/0603/0805/1206 / RoHS compliant / Product specification – April 15, 2021 V.6 / Chip Resistor Surface Mount
- Apr. 15, 2021 V6 / Product specification / 2
- ORDERING INFORMATION - GLOBAL PART NUMBER / Part number is identified by the serie s name , size, tolerance, packaging / type , temperature coefficient, t aping reel and resistance value.
- SCOPE / This specification describes AT0402 to / AT1206 high precision-high stability / chip resistors made by thin film
- ORDERING EXAMPLE / The orde ring code of a AT0402 chip resistor, TC 25 value 56Ω with ± / 0.5% tolerance, supplied in 7 -inch tape reel is: AT0402DRD0756RL. / NOTE / 1. All our Rchip products me…
- (1) SIZE / 0402 / 0603 / 0805 / 1206 / (2) TOLERANCE / B = ± 0.1% / C = ± 0.25%
- Apr. 15, 2021 V6 / Product specification / 3
- Apr. 15, 2021 V6 / Product specification / 4
- SERIES AT 0402 to 1206 / ELECTRICAL CHARACTERISTICS / Table 2
- Max. / Working / Voltage / Max. / Overload
- Max. / Overload / Voltage / Dielectric / Withstanding
- Dielectric / Withstanding / Voltage / Resistance Range (E-24/E-96 series)(Ω) & Tolerance(1) / T.C.R.
- Withstanding / Voltage / Resistance Range (E-24/E-96 series)(Ω) & Tolerance(1) / T.C.R. / (ppm/°C)(2)
- Apr. 15, 2021 V6 / Product specification / 5
- AT1206 =1/4 W / RATED VOLTAGE / The DC or AC (rms) continuous workin g voltage / corresponding to the rated power is det ermin ed by
- RATED VOLTAGE / The DC or AC (rms) continuous workin g voltage / corresponding to the rated power is det ermin ed by / the following formula:
- V = / )PxR( / Or max. working voltage whichever is less / Where / V=Continuous rated DC
- Where / V=Continuous rated DC / or AC (rms) working voltage (v) / P=Rated power / R=Resistance value (Ω)
- AT0805 Paper taping reel 7" (178 mm) 5,000 Units / AT1206 Paper taping reel 7" (178 mm) 5,000 Units / NOTE: for paper tape and reel specification/dimensions, please see the special data sheet “p…
- Apr. 15, 2021 V6 / Product specification / 6

### Dimensions, package, and mechanical information

- Table 1 / DIMENSIONS / Chip Resistor Surface Mount
- R=Resistance value (Ω) / FOOTPRINT AND SOLDERING PROFILES / For recommended footprint and soldering profiles, please see th e spec ial data sheet “Chip resistors moun ting”. / PRODUCT TYPE PATKI…
- FOOTPRINT AND SOLDERING PROFILES / For recommended footprint and soldering profiles, please see th e spec ial data sheet “Chip resistors moun ting”. / PRODUCT TYPE PATKING STYLE REEL DIMENSION Q…
- FOOTPRINT AND SOLDERING PROFILES / For recommended footprint and soldering profiles, please see th e spec ial data sheet “Chip resistors moun ting”. / PRODUCT TYPE PATKING STYLE REEL DIMENSION Q…
- AT0805 Paper taping reel 7" (178 mm) 5,000 Units / AT1206 Paper taping reel 7" (178 mm) 5,000 Units / NOTE: for paper tape and reel specification/dimensions, please see the special data sheet “p…
- Version 5 Oct. 24, 2017 - - Add resistance range for ± 15 ppm/°C / Version 4 Mar. 16, 2016 - - Remove FOS 90°C test / Version 3 Dec. 11, 2015 - - Modify Outline / Version 2 May 11, 2015 - - Modi…

### Formulas, equations, and configurable calculations

- exemption / ⚫ Halogen free epoxy / ⚫ Superior resistance against sulfur / containing atmosphere / ⚫ Moisture sensitivity level: MSL 1
- The DC or AC (rms) continuous workin g voltage / corresponding to the rated power is det ermin ed by / the following formula: / V = / )PxR(
- Measurement at 24± 4 hours after test conclusion / ± (0.1%+0.05Ω) / Operational / Life / AEC-Q200 Test 8
- (T.C.R.) / IEC 60115-1 4.8 At +25/–55 °C and / +25/+125°C Formula: / T.C.R= / )1t2t −R1(

### Reference designs, applications, and examples

- process. / APPLICATIONS / ⚫ Automotive electronics / ⚫ Industrial and medical equipment
- ⚫ Non-forbidden materials used in / products/production / ORDERING EXAMPLE / The orde ring code of a AT0402 chip resistor, TC 25 value 56Ω with ± / 0.5% tolerance, supplied in 7 -inch tape reel …
- There are 2~4 digits indicated the resistor value. / Letter R/K/M is decimal point / Example: 100R = 100Ω / 1K = 1,000Ω / (7) DEFAULT CODE
- Yageo makes no representation, warranty, and/or guarantee about the fitness of its produ cts for any particular / purpose or the continuing production of any of its products. To the maximum exte…
- warranties, including warranties of fitness for a particular pur pose, non-infringement and merchantability. / Yageo statements regarding the suitability of products for certain types of applica…
- Yageo statements regarding the suitability of products for certain types of applications are based on Yageo’s / knowledge of typical operating conditions for such types of applications in a gene…
- knowledge of typical operating conditions for such types of applications in a generic nature. Such s tateme nts / are neither binding statements of Yageo nor intended to constitute any warranty …
- are neither binding statements of Yageo nor intended to constitute any warranty concerning the suitability for a / specific customer application or use. They are intended for use only by custome…
- specific customer application or use. They are intended for use only by customers with requisite knowledge and / experience for determi ning w hether Yageo products are the correct products for …
- safeguard measures to ensure tha t product failure would not result in personal injury or property damage. / Yageo products are not designed for application or use in medical, life -saving, or l…
- Yageo products are not designed for application or use in medical, life -saving, or life -sustainin g devic es or for / any other application or use in which the failure of Yageo product s could…

## Page-by-Page Extracted Content

### Page 1

```text
DATA SHEET

THIN FILM CHIP RESISTORS
AUTOMOTIVE GRADE
AT series
0.01% TO 1%, TC5 TO TC50
sizes 0402/0603/0805/1206
RoHS compliant
Product specification – April 15, 2021 V.6
```

### Page 2

```text
Chip Resistor Surface Mount

www.yageo.com
 Apr. 15, 2021 V6

Product specification

2
9

SERIES AT 0402 to 1206

ORDERING INFORMATION - GLOBAL PART NUMBER
Part number is identified by the serie s name , size, tolerance, packaging
type , temperature coefficient, t aping reel and resistance value.

SCOPE
This specification describes AT0402 to
AT1206 high precision-high stability
chip resistors made by thin film
process.

APPLICATIONS
⚫ Automotive electronics
⚫ Industrial and medical equipment
⚫ Test and measuring equipment
⚫ Telecom munications

FEATURES
⚫ AEC-Q200 qualified
⚫ Total lead free without RoHS
exemption
⚫ Halogen free epoxy
⚫ Superior resistance against sulfur
containing atmosphere
⚫ Moisture sensitivity level: MSL 1
⚫ Reducing environmentally
hazardous wastes
⚫ High component and equip ment
reliability
⚫ Non-forbidden materials used in
products/production
ORDERING EXAMPLE
The orde ring code of a AT0402 chip resistor, TC 25 value 56Ω with ±
0.5% tolerance, supplied in 7 -inch tape reel is: AT0402DRD0756RL.
NOTE
1. All our Rchip products meet RoHS compliant and Halogen Free. "LFP" of the
internal 2D reel label mentions "Lead Free Process".
2. On customized label, "LFP" or specific symbol can be printed.

GLOBAL PART NUMBER
A T XXXX X X X XX XXXXX L
 (1) (2) (3) (4) (5) (6) (7)
(1) SIZE
0402 / 0603 / 0805 / 1206
(2) TOLERANCE
 B = ± 0.1%
 C = ± 0.25%
D = ± 0.5%
 F = ± 1%
L = ± 0.01%
P = ± 0.02%
W = ± 0.05%

(3) PACKAGING TYPE
R = Paper taping reel
(4) TEMPERATURE COEFFICIENT OF RESISTANCE
A = ± 5 ppm/°C
B = ± 10 ppm/°C
C = ± 15 ppm/°C
D = ± 25 ppm/°C
 E = ± 50 ppm/°C
(5) TAPING REEL
07 = 7 inch dia. Reel
(6) RESISTANCE VALUE
There are 2~4 digits indicated the resistor value.
Letter R/K/M is decimal point
Example: 100R = 100Ω
 1K = 1,000Ω
(7) DEFAULT CODE
Letter L is the system default code for ordering only. (NOTE)
```

### Page 3

```text
Chip Resistor Surface Mount

www.yageo.com
 Apr. 15, 2021 V6

Product specification

3
9

SERIES AT 0402 to 1206

MARKING
AT0402
 No marking

AT0603
 E-96 series: including values 10/11/13/15/20/75 of E -24 series, 3 digits
 E-24 series: exception values 10/11/13/15/20/75 of E -24 series, one short bar
under marking letter

AT0805 / AT1206
 Both E-24 and E -96 series: 4 digits
First three digits for significant figure and 4th digit for number of zeros

NOTE
For further marking information, please see special data sheet “Chip resistors marking ”.
Fig. 4 Value = 10 K Ω

YNSC004

Fig. 1

ynsc007

CONSTRUCTION
A metal film layer is deposited on a high
grade ceramic body (aluminium oxide ).
This resistive layer is trimmed to its
nominal value and on both ends a contact
is made which will guarantee optimum
solderability. This is achieved by ap plying
several layers and for ease of soldering the
outer layer consists of Ni/matte tin. The
resis tive layer is covered with a protective
coating.

protective coat
marking layer
resistive layer
inner electrode
termination (Ni /matte tin)
ceramic substrate
H
I2
YNSC064
W
L
I1

 Fig. 5 Chip resistor outl ines

OOUUTTLLIINNEESS

Fig. 2 Value = 12.4 KΩ

Fig. 3 Value = 56 KΩ

ynsc003
```

### Page 4

```text
Chip Resistor Surface Mount

www.yageo.com
 Apr. 15, 2021 V6

Product specification

4
9

SERIES AT 0402 to 1206

ELECTRICAL CHARACTERISTICS

Table 2

TYPE
Operating
Temperature
Range
Power
Rating
Max.
Working
Voltage
Max.
Overload
Voltage
Dielectric
Withstanding
Voltage
Resistance Range (E-24/E-96 series)(Ω) & Tolerance(1)
T.C.R.
(ppm/°C)(2)
±0.01%
(L)
±0.02%
(P)
±0.05%
(W)
±0.1%
(B)
±0.25%
(C)
±0.5%
(D)
±1%
(F)
AT0402
–55 ° C
to
 +155 ° C
1/16W 50 V 100 V 100 V
±50 (E)

50 ≤ R < 11K
10 ≤ R ≤ 100K
±25 (D) 10 ≤ R ≤ 100K
±15 (C) 10 ≤ R < 11K
±10 (B) 50 ≤ R < 11K
±5 (A) 50 ≤ R < 11K ---
AT0603 1/10W 75V 150 V 100 V
±50 (E)

50 ≤ R < 14K
10 ≤ R ≤ 330K

±25 (D) 10 ≤ R ≤ 330K
±15 (C) 10 ≤ R < 14K
±10 (B) 50 ≤ R < 14K
±5 (A) 50 ≤ R < 14K ---
AT0805 1/8W 150 V 300 V 300 V
±50 (E)

50 ≤ R < 17K
10 ≤ R ≤ 1M
±25 (D) 10 ≤ R ≤ 1M
±15 (C) 10 ≤ R < 17K
±10 (B) 50 ≤ R < 17K
±5 (A) 50 ≤ R < 17K ---
AT1206 1/4W 200 V 400 V 500 V
±50 (E)

50 ≤ R < 20K
10 ≤ R ≤ 1M
±25 (D) 10 ≤ R ≤ 1M
±15 (C) 10 ≤ R < 20K
±10 (B) 50 ≤ R < 20K
±5 (A) 50 ≤ R < 20K ---
NOTE : 1. Global part number (code 7)
 2. Global part number (code 9)
TYPE L (mm) W (mm) H (mm) I1 (mm) I2 (mm)
AT0402 1.00 ±0.10 0.50 ±0.05 0.30 ±0.05 0.20 ±0.10 0.25 ±0.10
AT0603 1.60 ±0.10 0.80 ±0.10 0.45 ±0.10 0.25 ±0.15 0.25 ±0.15
AT0805 2.00 ±0.10 1.25 ±0.10 0.50 ±0.10 0.35 ±0.20 0.35 ±0.20
AT1206 3.10 ±0.10 1.60 ±0.10 0.55 ±0.10 0.45 ±0.20 0.40 ±0.20

Table 1

DIMENSIONS
```

### Page 5

```text
Chip Resistor Surface Mount

www.yageo.com
 Apr. 15, 2021 V6

Product specification

5
9

SERIES AT 0402 to 1206

P
handbook, halfpage
MLB206_1
70 10055 50
Tamb( C)o
(%P )rated
0
0
50
100
155

Fig. 6 Maximum dissipation (P max) in percentage of rated power
as a function of the operating am bient temperature (T amb)

FUNCTIONAL DESCRIPTION
OOPPEERRAATTIINNGG TTEEMMPPEERRAATTUURREE RRAANNGGEE
Range: –55 °C to +155 °C
PPOOWWEERR RRAATTIINNGG
Each type rated power at 7 0 °C:
AT0402=1/16 W
AT0603 =1/10 W
AT0805 =1/8 W
AT1206 =1/4 W

RATED VOLTAGE
The DC or AC (rms) continuous workin g voltage
corresponding to the rated power is det ermin ed by
the following formula:
V =
)PxR(
Or max. working voltage whichever is less
Where
V=Continuous rated DC
or AC (rms) working voltage (v)
P=Rated power
R=Resistance value (Ω)

FOOTPRINT AND SOLDERING PROFILES
For recommended footprint and soldering profiles, please see th e spec ial data sheet “Chip resistors moun ting”.
PRODUCT TYPE PATKING STYLE REEL DIMENSION QUANTITY PER REEL
AT0402 Paper taping reel 7" (178 mm) 10,000 Units
AT0603 Paper taping reel 7" (178 mm) 5,000 Units
AT0805 Paper taping reel 7" (178 mm) 5,000 Units
AT1206 Paper taping reel 7" (178 mm) 5,000 Units
NOTE: for paper tape and reel specification/dimensions, please see the special data sheet “packing” document.
PACKING STYLE AND PACKAGING QUANTITY

Table 3 Packing style and packaging quantity
```

### Page 6

```text
Chip Resistor Surface Mount

www.yageo.com
 Apr. 15, 2021 V6

Product specification

6
9

SERIES AT 0402 to 1206

TEST TEST METHOD PROCEDURE REQUIREMENTS
Short Time
Overload
IEC60115-1 4.13 2.5 times of rated voltage or maximum
overload voltage, the less of the above, for 5 sec
at room temperature
± (0.05%+0.05Ω)
High
Temperature
Exposure
AEC-Q200 Test 3
MIL-STD-202 Method 108
1,000 hours at Tamb = 125 °C, unpowered ± (0.1%+0.05Ω)
1,000 hours at Tamb = 155 °C, unpowered ± (0.3%+0.05Ω)
Moisture
Resistance
AEC-Q200 Test 6
MIL-STD-202 Method 106
Each temperature / humidity cycle is defined at
8 hours (method 106F), 3 cycles / 24 hours for
10d. with 25 °C / 65 °C 95% R.H, without steps
7a & 7b, unpowered
Parts mounted on test-boards, without
condensation on parts
± (0.1%+0.05Ω)
Biased
Humidity
AEC-Q200 Test 7
MIL-STD-202 Method 103
1,000 hours; 85 °C / 85% RH
10% of operating power
Measurement at 24± 4 hours after test conclusion
± (0.1%+0.05Ω)
Operational
Life
AEC-Q200 Test 8
MIL-STD-202 Method 108
1,000 hours at 70± 5 °C, RCWV applied for 1.5
hours on, 0.5 hour off, still air required
± (0.1%+0.05Ω)
1,000 hours at 125 °C, derated voltage applied for
1.5 hours on, 0.5 hour off, still air required
± (0.3%+0.05Ω)
Resistance to
Soldering
Heat
AEC-Q200 Test 15
MIL-STD-202 Method 210
Condition B, no pre-heat of samples
Lead-free solder, 260± 5 °C, 10± 1 seconds
immersion time
Procedure 2 for SMD: devices fluxed and
cleaned with isopropanol
± (0.05%+0.05Ω)
Thermal
Shock
AEC-Q200 Test 16
MIL-STD-202 Method 107
-55/+125 °C
Number of cycles is 300. Devices mounted
Maximum transfer time is 20 seconds.
Dwell time is 15 minutes. Air – Air
± (0.1%+0.05Ω)
No visible damage
Solderability
- Wetting
AEC-Q200 Test 18
J-STD-002
Electrical Test not required Magnification 50X
SMD conditions:
(a) Method B, aging 4 hours at 155 °C dry heat,
dipping at 235± 3 °C for 5± 0.5 seconds.
(b) Method B, steam aging 8 hours, dipping at
215± 3 °C for 5± 0.5 seconds.
(c) Method D, steam aging 8 hours, dipping at
260± 3 °C for 7± 0.5 seconds

Well tinned
(>95% covered)
No visible damage
Table 4 Test condition, procedure and requirements

TESTS AND REQUIREMENTS
```

### Page 7

```text
Chip Resistor Surface Mount

www.yageo.com
 Apr. 15, 2021 V6

Product specification

7
9

SERIES AT 0402 to 1206

TEST TEST METHOD PROCEDURE REQUIREMENTS
Board Flex /
Bending
AEC-Q200 Test 21
AEC-Q200-005
Chips mounted on a 90mm glass epoxy resin
PCB (FR4)
Bending for 0402: 5 mm
 0603/0805: 3 mm
 1206: 2mm
Holding time: minimum 60 second
± (0.1%+0.05Ω)
Temperature
Coefficient of
Resistance
(T.C.R.)
IEC 60115-1 4.8 At +25/–55 °C and
+25/+125°C Formula:
T.C.R=
)1t2t −R1(
R1-R2 × 106(ppm/°C)
Where
t1=+25 °C or specified room temperature
t2=–55 °C or +125 °C test temperature
R1=resistance at reference temperature in ohms
R2=resistance at test temperature in ohms
Refer to table 2
Flower of
Sulfur
ASTM-B-809-95*
* Modified
Sulfur 750 hours, 105°C, unpowered. ± (4.0%+0.05Ω)
```

### Page 8

```text
Chip Resistor Surface Mount

www.yageo.com
 Apr. 15, 2021 V6

Product specification

8
9

SERIES AT 0402 to 1206

REVISION HISTORY

REVISION DATE CHANGE NOTIFICATION DESCRIPTION
Version 6 Apr. 15, 2021 - - Add tol. ± 0.01%, 0.02%, 0.05% ; TCR 5ppm & 10ppm
Version 5 Oct. 24, 2017 - - Add resistance range for ± 15 ppm/°C
Version 4 Mar. 16, 2016 - - Remove FOS 90°C test
Version 3 Dec. 11, 2015 - - Modify Outline
Version 2 May 11, 2015 - - Modify FOS test
Version 1 Jun. 18, 2014 - - Modify FOS test
Version 0 May 07, 2014 - - First issue of this specification
```

### Page 9

```text
Chip Resistor Surface Mount

www.yageo.com
 Apr. 15, 2021 V6

Product specification

9
9

SERIES AT 0402 to 1206

LEGAL DISCLAIMER

Yageo, its distributors and agents (collectively, “Yageo”), hereby disclaims any and all liabilities for any errors,
inaccuracies or incompleteness co ntaine d in an y product related information, including but not limited to
product specific ations, datasheets, pictures and/or graphics. Yageo may make changes, modifications and/or
improvements to product related information at any time and without notice.

Yageo makes no representation, warranty, and/or guarantee about the fitness of its produ cts for any particular
purpose or the continuing production of any of its products. To the maximum extent permitted by law, Yageo
disclaims (i) any and all liability a rising out of the application or use of any Yageo product, (ii) any and all
liability, in cluding without limitation special, consequential or incidental damages, and (iii) any and all implied
warranties, including warranties of fitness for a particular pur pose, non-infringement and merchantability.

Yageo statements regarding the suitability of products for certain types of applications are based on Yageo’s
knowledge of typical operating conditions for such types of applications in a generic nature. Such s tateme nts
are neither binding statements of Yageo nor intended to constitute any warranty concerning the suitability for a
specific customer application or use. They are intended for use only by customers with requisite knowledge and
experience for determi ning w hether Yageo products are the correct products for their application or use. In
addition, unpredicatable and isolated cases of product failure may still occur, therefore, customer application or
use of Yageo products which requires higher degree of r eliabi lity or safety, shall employ additional protective
safeguard measures to ensure tha t product failure would not result in personal injury or property damage.

Yageo products are not designed for application or use in medical, life -saving, or life -sustainin g devic es or for
any other application or use in which the failure of Yageo product s could result in personal injury or death.
Customers using or selling Yageo products not expressly indicated for above -mentioned purposes shall do so at
their own ris k and agree t o fully indemnify Yageo and hold Yageo harmless.

Information provided here is intend ed to indicate product specifications only. Yageo reserves all the rights for
revising this content without further notification, as long as products are unch anged. Any pr oduct change will
be announced by PCN.
```
