thepinkmile/Enigma-NG/design/Datasheets/Bourns-3310-datasheet.md

# Bourns 3310P-001-503L

## Source

- **Source PDF:** [Bourns-3310-datasheet.pdf](Bourns-3310-datasheet.pdf)
- **Generated Markdown:** `Bourns-3310-datasheet.md`
- **Page count:** 5
- **Conversion method:** automated local PDF text extraction with pypdf/pdfplumber

## PDF Metadata

| Field | Value |
| :--- | :--- |
| Title | 3310 9 mm Square Sealed Panel Control |
| Author | Bourns, Inc. |
| Subject | Bourns® Panel Controls |
| Creator | Adobe InDesign 20.3 (Macintosh) |
| Producer | Adobe PDF Library 17.0 |

## Extracted Technical Index

This markdown datasheet is meant to reduce the need to reopen the PDF during design work.
It preserves design-relevant extracted snippets first, followed by page-by-page text so the source content remains locally searchable.

### Part number and ordering information

- Wave Soldering 96.5Sn/3.0Ag/0.5Cu solder with no-clean flux; 260 °C (500 °F) max for 5 seconds / Wash Processes For recommended wash processes, please refer to `http://wwwbournscom/pdfs/sldclenp…`

### Pin, pad, and connection designations

- Weight (Single Section) 4.5 grams / (Each Additional Section) 2.5 grams / Terminals Solderable pins / Soldering Condition / Manual Soldering 96.5Sn/3.0Ag/0.5Cu solid wire or no-clean rosin cored…
- Wave Soldering 96.5Sn/3.0Ag/0.5Cu solder with no-clean flux; 260 °C (500 °F) max for 5 seconds / Wash Processes For recommended wash processes, please refer to `http://wwwbournscom/pdfs/sldclenp…`
- Model Number Designator / 3310 = 9 mm Panel Control / Terminal Style Designator / Single Cup: / C = In-line Straight Terminals Side Exit 2.54 mm centers
- Terminal Style Designator / Single Cup: / C = In-line Straight Terminals Side Exit 2.54 mm centers / R = In-line Terminals Rear Exit 2.54 mm centers / P = 5.08 mm x 2.54 mm Triangular Pattern Re…
- Single Cup: / C = In-line Straight Terminals Side Exit 2.54 mm centers / R = In-line Terminals Rear Exit 2.54 mm centers / P = 5.08 mm x 2.54 mm Triangular Pattern Rear Exit / Y = 5.08 mm x 5.08…
- Y = 5.08 mm x 5.08 mm Triangular Pattern Rear Exit / Dual Cup (Pot/Pot or Pot/Switch): / H = Dual In-line Straight Terminals Rear Exit 2.54 mm centers / Shaft End Designator / 0 = Shaft End Slot…
- 1 = 6.35 mm x 6.35 mm Plastic / 5 = Bushingless (Board Level Control) / Pot/Switch Bushing Designator (use with “H” terminal style only) / 3 = 6.35 mm x 6.35 mm Plastic / 6 = Bushingless (Board …
- (.020 ± .002) / SOLDER PLATED / COPPER PINS / DIA. / 3.18 ± .05
- (.020 ± .002) / TIN PLATED / COPPER PINS / MOUNTING / SURFACE
- applications. Except as set forth in the bullet points below or unless expressly and specifically approved in writing on a case-by-case basis by an / authorized Bourns’ representative, use of an…
- Bourns® custom products are specially designed. Absent a written agreement between Bourns and the user regarding the use and level of such testing, / the above provisions applicable to Bourns® s…
- the above provisions applicable to Bourns® standard products shall also apply to such Bourns® custom products. / Use of Bourns® products or Bourns’ technology in military/defense applications mu…
- technology or technical data for use in activities which involve the design, development, production, use or stockpiling of nuclear, chemical or / biological weapons or missiles, nor shall they …
- to such devices. Further, Bourns® products and Bourns’ technology and technical data may not under any circumstance be exported or re-exported to / countries subject to international sanctions o…

### Specifications, ratings, and operating conditions

- n Compact package saves board and panel / space / Electrical Characteristics1 / Standard Resistance Range - Linear 1 K ohms to 1 megohm / Total Resistance Tolerance - Linear Tapers ±20 %
- Electrical Characteristics1 / Standard Resistance Range - Linear 1 K ohms to 1 megohm / Total Resistance Tolerance - Linear Tapers ±20 % / Independent Linearity ±5 % / End Resistance 2 % or 2 oh…
- Effective Electrical Angle 270 ° ±15 ° / Contact Resistance Variation 1 % or 1 ohm (whichever is greater) / Dielectric Withstanding Voltage (MIL-STD-202 – Method 301) / Sea Level 900 VAC minimum…
- 70,000 Feet 350 VAC minimum / Insulation Resistance 1,000 megohms minimum / Power Rating @ 70 °C (Derate to 0 at 125 °C - Voltage Limited By Power Dissipation or 200 VAC, Whichever is Less) 0.25…
- Vibration 30 G / Total Resistance Shift ±1 % maximum / Voltage Ratio Shift ±1 % maximum / Shock 100 G / Total Resistance Shift ±1 % maximum
- Shock 100 G / Total Resistance Shift ±1 % maximum / Voltage Ratio Shift ±1 % maximum / Load Life 1,000 hours / Total Resistance Shift ±10 % TRS maximum
- Detent Torque 0.5 oz-in min / Power Rating (Resistive Load) 100 mA @ 16 VDC / 1Electrical specifications tested at 60 RPM, at room ambient: +25 °C nominal / WARNING / Cancer and Reproductive Harm
- <www.P65Warnings.ca.gov> / \*RoHS Directive 2015/863, Mar 31, 2015 and Annex. / Specifications are subject to change without notice. Users should verify actual device performance in their specif…
- RoHS Identifier / L = Compliant / Specifications are subject to change without notice. / Users should verify actual device performance in their specific applications. / The products described he…
- Y YWWM / 3310 – 9 mm Square Sealed Panel Control / Specifications are subject to change without notice. / Users should verify actual device performance in their specific applications. / The prod…
- TYP. / 1/4-32 UNEF / Specifications are subject to change without notice. / Users should verify actual device performance in their specific applications. / The products described herein and this…
- “Bourns”). / Unless otherwise expressly indicated in writing, Bourns® products and data sheets relating thereto are subject to change without notice. Users should check / for and obtain the late…
- To the maximum extent permitted by applicable law, Bourns disclaims (i) any and all liability for special, punitive, consequential, incidental or indirect / damages or lost revenues or lost prof…

### Dimensions, package, and mechanical information

- n Withstands typical industrial washing / processes / n Compact package saves board and panel / space / Electrical Characteristics1
- Moisture Sensitivity Level 1 / ESD Classification (HBM) N/A / Mechanical Characteristics / Stop Strength 5.65 N-cm (8 oz-in) / Mechanical Angle 295 ° ±10 °
- Mechanical Characteristics / Stop Strength 5.65 N-cm (8 oz-in) / Mechanical Angle 295 ° ±10 ° / Torque / Starting 3.53 N-cm (5.0 oz-in) maximum
- Users should verify actual device performance in their specific applications. / The products described herein and this document are subject to specific legal disclaimers as set forth on the last…
- 2 / 3 / COMMON DIMENSIONS / 3310-001 / Plastic Bushing
- Slotted Shaft / MOUNTING HOLE PATTERN / COMMON DIMENSIONS / 3310C-101 / Plastic Flatted Shaft
- MOUNTING / SURFACE / DIMENSIONS: MM / (INCHES) / 3310 – 9 mm Square Sealed Panel Control
- (INCHES) / 3310 – 9 mm Square Sealed Panel Control / Product Dimensions / 6.35 ± .08 / (.250 ± .003)
- NOTE: \* Only recommended shaft length / for bushingless version / DIMENSIONS: MM / (INCHES) / Hardware
- 0.46 ± 0.05 / (.018 ± .002) / DIMENSIONS: MM / (INCHES) / NUT H-38-1
- Users should verify actual device performance in their specific applications. / The products described herein and this document are subject to specific legal disclaimers as set forth on the last…
- DIA. / REV 11/25 / COMMON DIMENSIONS / 3310H-003 / Pot/Switch Dual Cup
- (.125 ± .002) / DIA. / DIMENSIONS: MM / (INCHES) / COMMON DIMENSIONS
- DIMENSIONS: MM / (INCHES) / COMMON DIMENSIONS / 3310H-003 / Pot/Switch Dual Cup

### Formulas, equations, and configurable calculations

- Storage Temperature Range -55 °C to +125 °C (-67 °F to +257 °F) / Temperature Coefficient Over Storage Temperature Range ±1,000 ppm/°C / Vibration 30 G / Total Resistance Shift ±1 % maximum / Vo…
- Vibration 30 G / Total Resistance Shift ±1 % maximum / Voltage Ratio Shift ±1 % maximum / Shock 100 G / Total Resistance Shift ±1 % maximum
- Shock 100 G / Total Resistance Shift ±1 % maximum / Voltage Ratio Shift ±1 % maximum / Load Life 1,000 hours / Total Resistance Shift ±10 % TRS maximum
- authorized Bourns’ representative, use of any Bourns® products in such unauthorized high-risk applications is at the user’s sole risk. / • Bourns considers implantable/invasive devices and devic…
- • Bourns expressly identifies Bourns® standard products that are suitable for use in the typical aviation applications/systems requiring System / Design Assurance Level (RTCA DO-254 DAL) of C, D…

### Reference designs, applications, and examples

- \*RoHS Directive 2015/863, Mar 31, 2015 and Annex. / Specifications are subject to change without notice. Users should verify actual device performance in their specific / applications. The prod…
- L = Compliant / Specifications are subject to change without notice. / Users should verify actual device performance in their specific applications. / The products described herein and this docu…
- 3310 – 9 mm Square Sealed Panel Control / Specifications are subject to change without notice. / Users should verify actual device performance in their specific applications. / The products desc…
- 1/4-32 UNEF / Specifications are subject to change without notice. / Users should verify actual device performance in their specific applications. / The products described herein and this docume…
- for and obtain the latest relevant information and verify that such information is current and complete before placing orders for Bourns® products. / The characteristics and parameters of a Bour…
- The characteristics and parameters of a Bourns® product set forth in its data sheet are based on laboratory conditions, and statements regarding the / suitability of products for certain “typica…
- suitability of products for certain “typical” applications are based on Bourns’ knowledge of typical requirements in generic applications. Bourns assumes / that “typical” applications include fa…
- avoid scrap of a device solely due to malfunctioning Bourns® product. The characteristics and parameters of a Bourns® product in a user application / may vary from the data sheet characteristics…
- may vary from the data sheet characteristics and parameters due to (i) the combination of the Bourns® product with other components in the user’s / application, or (ii) the environment of the us…
- application, or (ii) the environment of the user application itself. The characteristics and parameters of a Bourns® product also can and do vary in / different applications and actual performan…
- different applications and actual performance may vary over time. Thus, users should always verify the actual performance of the Bourns® product in / their specific devices and applications and …
- 16949\) or a particular qualification (e.g., UL listed or recognized), Bourns is not responsible for any failure of an individual Bourns® product to meet / the requirements of such industry stan…
- the requirements of such industry standard or particular qualification even if such industry standard or qualification is a “state of art” . Users of Bourns® / products are responsible for ensur…
- Bourns® products are not recommended, authorized or intended for use in applications where failure or malfunction may result in personal injury, / death, or severe property or environmental dama…
- death, or severe property or environmental damage, such as without limitation nuclear, life-critical medical and certain automotive and aviation / applications. Except as set forth in the bullet…
- authorized Bourns’ representative, use of any Bourns® products in such unauthorized high-risk applications is at the user’s sole risk. / • Bourns considers implantable/invasive devices and devic…
- • Bourns considers implantable/invasive devices and devices/procedures designed as life-supporting or life-sustaining by the U.S. Food and Drug / Administration or equivalent organizations outsi…
- Bourns® standard products that are suitable for use in typical medical applications that are not life-critical in its publication entitled “Bourns / Medical Grade Component Guide. ” / • Bourns e…
- Automate Safety Integrity Level (ASIL) in its publication entitled “Bourns Automotive Grade Component Guide. ” Bourns’ designation of Bourns® / product as compliant with the AEC-Q standard does …
- product as compliant with the AEC-Q standard does not by itself mean that Bourns has approved such product for use in an automotive / application. / • Bourns expressly identifies Bourns® standar…

## Page-by-Page Extracted Content

### Page 1

```text
3310 – 9 mm Square Sealed Panel Control
Features
n Conductive plastic
n PC board and bushing mount
n Plastic bushing and plastic shaft
n Withstands typical industrial washing
processes
n Compact package saves board and panel
space
Electrical Characteristics1
Standard Resistance Range - Linear 1 K ohms to 1 megohm
Total Resistance Tolerance - Linear Tapers ±20 %
Independent Linearity ±5 %
End Resistance 2 % or 2 ohms maximum (whichever is greater)
Effective Electrical Angle 270 ° ±15 °
Contact Resistance Variation 1 % or 1 ohm (whichever is greater)
Dielectric Withstanding Voltage (MIL-STD-202 – Method 301)
 Sea Level 900 VAC minimum
 70,000 Feet 350 VAC minimum
Insulation Resistance 1,000 megohms minimum
Power Rating @ 70 °C (Derate to 0 at 125 °C - Voltage Limited By Power Dissipation or 200 VAC, Whichever is Less) 0.25 watts
Theoretical Resolution Essentially infinite
Environmental Characteristics
Operating Temperature Range -40 °C to +125 °C (-40 °F to +257 °F)
Storage Temperature Range -55 °C to +125 °C (-67 °F to +257 °F)
Temperature Coefficient Over Storage Temperature Range ±1,000 ppm/°C
Vibration 30 G
 Total Resistance Shift ±1 % maximum
 Voltage Ratio Shift ±1 % maximum
Shock 100 G
 Total Resistance Shift ±1 % maximum
 Voltage Ratio Shift ±1 % maximum
Load Life 1,000 hours
 Total Resistance Shift ±10 % TRS maximum
Rotational Life (No Load) 50,000 cycles
 Total Resistance Shift ±5 % TRS maximum
 Contact Resistance Variation 3 % or 3 ohms (whichever is greater)
Moisture Resistance MIL-STD-202, Method 103, Condition B
 Total Resistance Shift ±10 % TRS maximum
IP Rating IP67
Moisture Sensitivity Level 1
ESD Classification (HBM) N/A
Mechanical Characteristics
Stop Strength 5.65 N-cm (8 oz-in)
Mechanical Angle 295 ° ±10 °
Torque
 Starting 3.53 N-cm (5.0 oz-in) maximum
 Running 3.53 N-cm (5.0 oz-in) maximum
 Mounting (Torque on Bushing) 45 N-cm (4.0 lb-in) max [plastic bushing]; 79 N-cm (7.0 lb-in) max [metal bushing]
Weight (Single Section) 4.5 grams
 (Each Additional Section) 2.5 grams
Terminals Solderable pins
 Soldering Condition
 Manual Soldering 96.5Sn/3.0Ag/0.5Cu solid wire or no-clean rosin cored wire; 370 °C (700 °F) max for 3 seconds
 Wave Soldering 96.5Sn/3.0Ag/0.5Cu solder with no-clean flux; 260 °C (500 °F) max for 5 seconds
 Wash Processes For recommended wash processes, please refer to http://wwwbournscom/pdfs/sldclenpdf
Marking Manufacturer’s trademark, model number, product code, terminal style, resistance code and date code
Ganging 2 cups maximum
Hardware One lockwasher (H-37-5) and one mounting nut (H-38-1) is shipped with each potentiometer, except bushingless versions
Flammability Conforms to UL94V-0
Epoxy Conforms to UL 94V-1
IP Rating IP67
Switch Characteristics
Switch Life 10K cycles
Contact Resistance 2 ohms max
Dielectric Strength 350 VDC
Detent Torque 0.5 oz-in min
Power Rating (Resistive Load) 100 mA @ 16 VDC
1Electrical specifications tested at 60 RPM, at room ambient: +25 °C nominal
WARNING
Cancer and Reproductive Harm
www.P65Warnings.ca.gov
*RoHS Directive 2015/863, Mar 31, 2015 and Annex.
Specifications are subject to change without notice. Users should verify actual device performance in their specific
applications. The products described herein and this document are subject to specific legal disclaimers as set forth on the
last page of this document, and at www.bourns.com/docs/legal/disclaimer.pdf.
Additional Information
Click these links for more information:
PRODUCT
SELECTOR
TECHNICAL
LIBRARY
INVENTORY SAMPLES CONTACT
```

### Page 2

```text
3310 – 9 mm Square Sealed Panel Control
Additional Features
n Audio taper versions available as special order
n RoHS compliant*
Standard Resistance Table
 Resistance Resistance
 (Ohms) Code
 1,000 102
 2,000 202
 5,000 502
 10,000 103
 20,000 203
 50,000 503
 100,000 104
 200,000 204
 500,000 504
 1,000,000 105
Popular values listed in boldface Consult factory
for special resistances
 How To Order
3310 Y - 0 0 1 - 103 L
Model Number Designator
 3310 = 9 mm Panel Control
Terminal Style Designator
 Single Cup:
 C = In-line Straight Terminals Side Exit 2.54 mm centers
 R = In-line Terminals Rear Exit 2.54 mm centers
 P = 5.08 mm x 2.54 mm Triangular Pattern Rear Exit
 Y = 5.08 mm x 5.08 mm Triangular Pattern Rear Exit
 Dual Cup (Pot/Pot or Pot/Switch):
 H = Dual In-line Straight Terminals Rear Exit 2.54 mm centers
Shaft End Designator
 0 = Shaft End Slotted
 1 = Shaft End Flatted
Shaft Length Designator
 0 = 12.7 mm FMS Long Plastic Shaft (Available w/bushing only)
 1 = 19.05 mm FMS Long Plastic Shaft (Available w/bushing only)
 2 = 5.59 mm FMS Long Plastic Shaft (Bushingless version only)
Bushing Designator
 Pot (or Pot/Pot):
 1 = 6.35 mm x 6.35 mm Plastic
 5 = Bushingless (Board Level Control)
 Pot/Switch Bushing Designator (use with “H” terminal style only)
 3 = 6.35 mm x 6.35 mm Plastic
 6 = Bushingless (Board Level)
Resistance Code
 (1st 2 digits are significant, 3rd digit is number of 0s to follow)
RoHS Identifier
 L = Compliant
Specifications are subject to change without notice.
Users should verify actual device performance in their specific applications.
The products described herein and this document are subject to specific legal disclaimers as set forth on the last page of this document, and at www.bourns.com/docs/legal/disclaimer.pdf.
Date Code Description
 YY = LAST TWO DIGITS OF YEAR
 MANUFACTURED
 WW = WEEK NUMBER
 M = COUNTRY OF MANUFACTURE
 (MEXICO)
Y YWWM
```

### Page 3

```text
3310 – 9 mm Square Sealed Panel Control
Specifications are subject to change without notice.
Users should verify actual device performance in their specific applications.
The products described herein and this document are subject to specific legal disclaimers as set forth on the last page of this document, and at www.bourns.com/docs/legal/disclaimer.pdf.
Product Dimensions
1
1
1
1
2
2
2
2
3
3
3
3
1
2
3
COMMON DIMENSIONS
3310-001
Plastic Bushing
Slotted Shaft
MOUNTING HOLE PATTERN
COMMON DIMENSIONS
3310C-101
Plastic Flatted Shaft
3310C-001 3310Y-001
3310P-001
3310R-001
9.53 ± .25
(.375 ± .010)
9.53 ± .25
(.375 ± .010)
9.53 ± .25
(.375 ± .010)
9.53 ± .25
(.375 ± .010)
9.53 ± .25
(.375 ± .010)
.391 ± .38
(.154 ± .015)
9.53 ± .25
(.375 ± .010)
5.97 ± .89
(.235 ± .035)
2.54 ± .25
(.100 ± .010)
2.54 ± .25
(.100 ± .010)
2.54 ± .25
(.100 ± .010)
2.54 ± .38
(.100 ± .015)
MOUNTING
SURFACE
4.83
(.190)
2.39
(.094)
5.08 ± .25
(.200 ± .010)
5.97 ± .89
(.235 ± .035)
2.54 ± .25
(.100 ± .010)
2.54 ± .25
(.100 ± .010)
2.54 ± .25
(.100 ± .010)
2.54 ± .25
(.100 ± .010)
2.54 ± .25
(.100 ± .010)
2.54 ± .25
(.100 ± .010)
5.97 ± .89
(.235 ± .035)
5.97 ± .89
(.235 ± .035)
2.54 ± .25
(.100 ± .010)
.51 ± .05
(.020 ± .002)
SOLDER PLATED
COPPER PINS
DIA.
3.18 ± .05
(.125 ± .002)
DIA.
.64 ± .10
(.025 ± .004) WIDE
.76 ± .25
(.030 ± .010) DEEPX
.51
(.020) 4 PLACES
DIA. MOUNTING
SURFACE
1.70 ± 0.03
(.067 ± .001)
DIA.
6.53 ± 0.03
(.257 ± .001)
DIA.
4.78
(.188)
4.78
(.188)
7.62
(.300)
.38
(.015)
MIN.
STANDOFF
.76 ± .05 X .76
(.030 ± .002 X .030)
ANTI-ROTATION
BOSS
HIGHR
6.35 ± .08
(.250 ± .003)
MOUNTING
DIA.
4.83 ± .25
(.190 ± .010)
4.83 ± .38
(.190 ± .015) 6.35 ± .08
(.250 ± .003)
MOUNTING DIA.
12.70 ± .64
(.500 ± .025)
FROM MOUNTING
SURFACE
5.18 ± .38
(.204 ± .015)
12.70 ± .64
(.500 ± .025)
ADJUSTMENT SLOT
4.75
(.187)
MIN. FULL
THREAD
6.35
(.250)
.38
(.015)
MIN.
STANDOFF
1/4-32 UNEF-2A
THREADED PLASTIC
BUSHING
MOUNTING
SURFACE
DIMENSIONS: MM
(INCHES)
```

### Page 4

```text
3310 – 9 mm Square Sealed Panel Control
Product Dimensions
6.35 ± .08
(.250 ± .003)
MOUNTING DIA.
7.62 ± .20
(.300 ± .008)DIA.
6.35 ± .20
(.250 ± .008)DIA.
.51 ± .10
(.020 ± .004)
5.18 ± .64
(.204 ± .025)
5.59 ± .38
(.220 ± .015)
4.83 ± .25
(.190 ± .009)
6.35 ± .64
(.250 ± .025)
12.70 ± .64
(.500 ± .025)
.38
(.015)
MIN. STANDOFF
.38
(.015)
MIN. STANDOFF
.38
(.015)
MIN. STANDOFF
.76
(.030)
6.35
(.250)
1/4-32 UNEF-2A
THREADED METAL
BUSHING
MOUNTING
SURFACE
.76 ± .05 X .97
(.030 ± .002 X .038)
ANTI-ROTATION
BOSS
HIGHR
DIA. MOUNTING
SURFACE
7.62
(.300)
.38
(.015)
MIN.
STANDOFF
.51
(.020)2 PLACES
5.08 ± .51
(.200 ± .020)BC A
NOTE: * Only recommended shaft length
 for bushingless version
DIMENSIONS: MM
(INCHES)
Hardware
LOCKWASHER H-37-5
6.5 ± 0.23
(.256 ± .011)
10.06 ± 0.31
(.396 ± .012)
0.46 ± 0.05
(.018 ± .002)
DIMENSIONS: MM
(INCHES)
NUT H-38-1
7.95 +0/-0.30
(.313 +0/-.012)
9.17 +0/-0.43
(.361 +0/-.017)
1.98 ± 0.25
(.078 ± .010)
30 ° ± 5 °
TYP.
1/4-32 UNEF
Specifications are subject to change without notice.
Users should verify actual device performance in their specific applications.
The products described herein and this document are subject to specific legal disclaimers as set forth on the last page of this document, and at www.bourns.com/docs/legal/disclaimer.pdf.
COMMON DIMENSIONS
3310H-003
Pot/Switch Dual Cup
Plastic Bushing
3310H-025*
Pot/Pot Dual Cup
Bushingless
Pot/Pot Dual Cup Pot/Switch Dual Cup
Pot Single Cup
3310H-002
Pot/Pot Dual Cup
Metal Bushing
9.53 ± .25
(.375 ± .010)
PRIMARY
ELEMENT
PRIMARY
ELEMENT
SECONDARY
ELEMENT
SWITCH
32 1
BC A
32 1
65 4
PRIMARY
ELEMENT
SECONDARY
ELEMENT
MOUNTING
SURFACE
ANTI-ROTATION LUG
1/4-32 UNEF-2A
THREADED
METAL BUSHING
32 1
65 4
2.54 ± .25
(0.10 ± .010)
5.08 ± .25
(0.20 ± .010)
7.54 ± .64
(0.297 ± .025)
12.70 ± .64
(0.50 ± .025)
6.35 ± .08
(0.25 ± .003)
MOUNTING DIA.
5.59 ± .38
(0.220 ± .015)
1
2
3
4
5
6
PRIMARY
WIPER
SECONDARY
CWCCW
CWCCW
CLOCKWISE
CLOCKWISE
1
2
3
A
C
B
PRIMARY
CWCCW
CW
COMMON
SWITCH
CCW
CLOCKWISE
CLOCKWISE
1
2
3
PRIMARY
CWCCW
CLOCKWISE
6.35 ± .08
(0.25 ± .003)MOUNTING DIA.
.36 ± .10
(0.14 ± .004)
12.70 ± .64
(0.50 ± .025)
7.62 ± .64
(0.29 ± .025)
5.97 ± .89
(0.235 ± .035)
.64 ± .10
(.025 ± .004)ADJ. SLOT DEEPWIDE X .76 ± .08
(.03 ± .004)
.69 ± .10
(.027 ± .004)ADJ. SLOT DEEPWIDE X .76 ± .08
(.03 ± .004)
5.97 ± .89
(.235 ± .035)
2.54 ± .25
(0.10 ± .010)
3.18 ± .05
(.125 ± .002)
DIA.
9.75 ± .38
(.383 ± .015)
.38
(.015)
MIN.
STANDOFF
.38
(.015)
MIN.
STANDOFF
.38
(.015)
MIN.
STANDOFF
.76
(.03)
6.35
(0.25)
7.62
(0.30) TYP.
1.14
(0.045)TYP.
6.35
(0.25)
.51 ± .05
(.020 ± .002)
TIN PLATED
COPPER PINS
MOUNTING
SURFACE
ANTI-ROTATION LUG
1/4-32 UNEF-2A
THREADED
PLASTIC BUSHING
DIA.
.48
(.019)
4 PLCS.
NOTE: * Only recommended shaft length
 for bushingless version
7.62 ± .20
(0.30 ± .008)
MOUNTING
SURFACE
DIA. 3.18 ± .05
(.125 ± .002)
DIA.
REV 11/25
COMMON DIMENSIONS
3310H-003
Pot/Switch Dual Cup
Plastic Bushing
3310H-025*
Pot/Pot Dual Cup
Bushingless
Pot/Pot Dual Cup Pot/Switch Dual Cup
Pot Single Cup
3310H-002
Pot/Pot Dual Cup
Metal Bushing
9.53 ± .25
(.375 ± .010)
PRIMARY
ELEMENT
PRIMARY
ELEMENT
SECONDARY
ELEMENT
SWITCH
32 1
BC A
32 1
65 4
PRIMARY
ELEMENT
SECONDARY
ELEMENT
MOUNTING
SURFACE
ANTI-ROTATION LUG
1/4-32 UNEF-2A
THREADED
METAL BUSHING
32 1
65 4
2.54 ± .25
(0.10 ± .010)
5.08 ± .25
(0.20 ± .010)
7.54 ± .64
(0.297 ± .025)
12.70 ± .64
(0.50 ± .025)
6.35 ± .08
(0.25 ± .003)
MOUNTING DIA.
5.59 ± .38
(0.220 ± .015)
1
2
3
4
5
6
PRIMARY
WIPER
SECONDARY
CWCCW
CWCCW
CLOCKWISE
CLOCKWISE
1
2
3
A
C
B
PRIMARY
CWCCW
CW
COMMON
SWITCH
CCW
CLOCKWISE
CLOCKWISE
1
2
3
PRIMARY
CWCCW
CLOCKWISE
6.35 ± .08
(0.25 ± .003)MOUNTING DIA.
.36 ± .10
(0.14 ± .004)
12.70 ± .64
(0.50 ± .025)
7.62 ± .64
(0.29 ± .025)
5.97 ± .89
(0.235 ± .035)
.64 ± .10
(.025 ± .004)ADJ. SLOT DEEPWIDE X .76 ± .08
(.03 ± .004)
.69 ± .10
(.027 ± .004)ADJ. SLOT DEEPWIDE X .76 ± .08
(.03 ± .004)
5.97 ± .89
(.235 ± .035)
2.54 ± .25
(0.10 ± .010)
3.18 ± .05
(.125 ± .002)
DIA.
9.75 ± .38
(.383 ± .015)
.38
(.015)
MIN.
STANDOFF
.38
(.015)
MIN.
STANDOFF
.38
(.015)
MIN.
STANDOFF
.76
(.03)
6.35
(0.25)
7.62
(0.30) TYP.
1.14
(0.045)TYP.
6.35
(0.25)
.51 ± .05
(.020 ± .002)
TIN PLATED
COPPER PINS
MOUNTING
SURFACE
ANTI-ROTATION LUG
1/4-32 UNEF-2A
THREADED
PLASTIC BUSHING
DIA.
.48
(.019)
4 PLCS.
NOTE: * Only recommended shaft length
 for bushingless version
7.62 ± .20
(0.30 ± .008)
MOUNTING
SURFACE
DIA. 3.18 ± .05
(.125 ± .002)
DIA.
DIMENSIONS: MM
(INCHES)
COMMON DIMENSIONS
3310H-003
Pot/Switch Dual Cup
Plastic Bushing
3310H-025*
Pot/Pot Dual Cup
Bushingless
Pot/Pot Dual Cup Pot/Switch Dual Cup
Pot Single Cup
3310H-002
Pot/Pot Dual Cup
Metal Bushing
9.53 ± .25
(.375 ± .010)
PRIMARY
ELEMENT
PRIMARY
ELEMENT
SECONDARY
ELEMENT
SWITCH
32 1
BC A
32 1
65 4
PRIMARY
ELEMENT
SECONDARY
ELEMENT
MOUNTING
SURFACE
ANTI-ROTATION LUG
1/4-32 UNEF-2A
THREADED
METAL BUSHING
32 1
65 4
2.54 ± .25
(0.10 ± .010)
5.08 ± .25
(0.20 ± .010)
7.54 ± .64
(0.297 ± .025)
12.70 ± .64
(0.50 ± .025)
6.35 ± .08
(0.25 ± .003)
MOUNTING DIA.
5.59 ± .38
(0.220 ± .015)
1
2
3
4
5
6
PRIMARY
WIPER
SECONDARY
CWCCW
CWCCW
CLOCKWISE
CLOCKWISE
1
2
3
A
C
B
PRIMARY
CWCCW
CW
COMMON
SWITCH
CCW
CLOCKWISE
CLOCKWISE
1
2
3
PRIMARY
CWCCW
CLOCKWISE
6.35 ± .08
(0.25 ± .003)MOUNTING DIA.
.36 ± .10
(0.14 ± .004)
12.70 ± .64
(0.50 ± .025)
7.62 ± .64
(0.29 ± .025)
5.97 ± .89
(0.235 ± .035)
.64 ± .10
(.025 ± .004)ADJ. SLOT DEEPWIDE X .76 ± .08
(.03 ± .004)
.69 ± .10
(.027 ± .004)ADJ. SLOT DEEPWIDE X .76 ± .08
(.03 ± .004)
5.97 ± .89
(.235 ± .035)
2.54 ± .25
(0.10 ± .010)
3.18 ± .05
(.125 ± .002)
DIA.
9.75 ± .38
(.383 ± .015)
.38
(.015)
MIN.
STANDOFF
.38
(.015)
MIN.
STANDOFF
.38
(.015)
MIN.
STANDOFF
.76
(.03)
6.35
(0.25)
7.62
(0.30) TYP.
1.14
(0.045)TYP.
6.35
(0.25)
.51 ± .05
(.020 ± .002)
TIN PLATED
COPPER PINS
MOUNTING
SURFACE
ANTI-ROTATION LUG
1/4-32 UNEF-2A
THREADED
PLASTIC BUSHING
DIA.
.48
(.019)
4 PLCS.
NOTE: * Only recommended shaft length
 for bushingless version
7.62 ± .20
(0.30 ± .008)
MOUNTING
SURFACE
DIA. 3.18 ± .05
(.125 ± .002)
DIA.
```

### Page 5

```text
This legal disclaimer applies to purchasers and users of Bourns® products manufactured by or on behalf of Bourns, Inc. and its affiliates (collectively,
“Bourns”).
Unless otherwise expressly indicated in writing, Bourns® products and data sheets relating thereto are subject to change without notice. Users should check
for and obtain the latest relevant information and verify that such information is current and complete before placing orders for Bourns® products.
The characteristics and parameters of a Bourns® product set forth in its data sheet are based on laboratory conditions, and statements regarding the
suitability of products for certain “typical” applications are based on Bourns’ knowledge of typical requirements in generic applications. Bourns assumes
that “typical” applications include failsafe/backup features to address critical risks to users and are designed to allow rework of Bourns® product to
avoid scrap of a device solely due to malfunctioning Bourns® product. The characteristics and parameters of a Bourns® product in a user application
may vary from the data sheet characteristics and parameters due to (i) the combination of the Bourns® product with other components in the user’s
application, or (ii) the environment of the user application itself. The characteristics and parameters of a Bourns® product also can and do vary in
different applications and actual performance may vary over time. Thus, users should always verify the actual performance of the Bourns® product in
their specific devices and applications and make their own independent judgments regarding the suitability of Bourns® product and the amount of
additional test margin to design into their device or application to compensate for differences between laboratory and real-world conditions.
Unless Bourns has explicitly designated an individual Bourns® product as meeting the requirements of a particular industry standard (e.g., IATF
16949) or a particular qualification (e.g., UL listed or recognized), Bourns is not responsible for any failure of an individual Bourns® product to meet
the requirements of such industry standard or particular qualification even if such industry standard or qualification is a “state of art” . Users of Bourns®
products are responsible for ensuring compliance with safety-related requirements and standards applicable to their devices or applications.
Bourns® products are not recommended, authorized or intended for use in applications where failure or malfunction may result in personal injury,
death, or severe property or environmental damage, such as without limitation nuclear, life-critical medical and certain automotive and aviation
applications. Except as set forth in the bullet points below or unless expressly and specifically approved in writing on a case-by-case basis by an
authorized Bourns’ representative, use of any Bourns® products in such unauthorized high-risk applications is at the user’s sole risk.
• Bourns considers implantable/invasive devices and devices/procedures designed as life-supporting or life-sustaining by the U.S. Food and Drug
 Administration or equivalent organizations outside of the United States as “life-critical” medical applications. Bourns expressly identifies those
 Bourns® standard products that are suitable for use in typical medical applications that are not life-critical in its publication entitled “Bourns
 Medical Grade Component Guide. ”
• Bourns expressly identifies those Bourns® standard products that are suitable for use in typical automotive applications associated with any
 Automate Safety Integrity Level (ASIL) in its publication entitled “Bourns Automotive Grade Component Guide. ” Bourns’ designation of Bourns®
 product as compliant with the AEC-Q standard does not by itself mean that Bourns has approved such product for use in an automotive
 application.
• Bourns expressly identifies Bourns® standard products that are suitable for use in the typical aviation applications/systems requiring System
 Design Assurance Level (RTCA DO-254 DAL) of C, D or E in its publication entitled “Bourns Civilian Aerospace/Aviation Grade Component Guide. ”
 Bourns does not test its products for compliance with United States Federal Aviation Administration standards or any other generally equivalent
 governmental organization standard applicable to products designed or manufactured for use in aviation applications. Use of Bourns® standard
 components in aviation applications associated with RTCA DO-254 DAL A or B without proper approval noted above shall be at the user’s sole
 risk.
• Bourns will review and authorize on a case-by-case basis the use of Bourns® standard products which are at least AEC-Q compliant in space-
 related civil applications (rockets, satellites) with a negotiated cross-waiver and indemnity agreement.
The use and level of testing applicable to Bourns® custom products shall be negotiated on a case-by-case basis by Bourns and the user for which such
Bourns® custom products are specially designed. Absent a written agreement between Bourns and the user regarding the use and level of such testing,
the above provisions applicable to Bourns® standard products shall also apply to such Bourns® custom products.
Use of Bourns® products or Bourns’ technology in military/defense applications must be reviewed with Bourns for compliance with applicable export
control laws and embargoes. Users shall not sell, transfer, export or re-export (which includes transfers within a country) any Bourns® products or
technology or technical data for use in activities which involve the design, development, production, use or stockpiling of nuclear, chemical or
biological weapons or missiles, nor shall they use Bourns® products or technology or technical data in any facility which engages in activities relating
to such devices. Further, Bourns® products and Bourns’ technology and technical data may not under any circumstance be exported or re-exported to
countries subject to international sanctions or embargoes. Bourns® products and technology may not, without prior authorization from Bourns and/or
the Government of a country where such product/technology is designed and/or manufactured, be resold, transferred, or re-exported (including within
the same country) to any party not eligible to receive commodities, software, and technical data originating in such country.
To the maximum extent permitted by applicable law, Bourns disclaims (i) any and all liability for special, punitive, consequential, incidental or indirect
damages or lost revenues or lost profits, and (ii) any and all implied warranties (those not based on parameters specified in Bourns’ data sheets and/or
specifications), including implied warranties of fitness for particular purpose, non-infringement and merchantability.
For your convenience, copies of this Legal Disclaimer Notice with German, Spanish, Japanese, Traditional Chinese and Simplified Chinese bilingual versions are
available at:
 Web Page: https://www.bourns.com/legal/disclaimers-terms-and-policies
 PDF: https://www.bourns.com/docs/Legal/disclaimer.pdf
 Legal Disclaimer Notice
K2540 05/26R
```
