thepinkmile/Enigma-NG/design/Datasheets/Cherry-MX2A SILENT RED-datasheet.md

# Cherry MX2A SILENT RED

## Source

- **Source PDF:** [Cherry-MX2A SILENT RED-datasheet.pdf](Cherry-MX2A SILENT RED-datasheet.pdf)
- **Generated Markdown:** `Cherry-MX2A SILENT RED-datasheet.md`
- **Page count:** 2
- **Conversion method:** automated local PDF text extraction with pypdf/pdfplumber

## PDF Metadata

| Field | Value |
| :--- | :--- |
| Title | Datasheet BU-components pdfreactor |
| Author | `cherry.scriptuser@sdzecom.de` |
| Subject | |
| Creator | RealObjects PDFreactor(R) 11.6.12 (16335), Serial No: 5501, Licensed for: Cherry Europe GmbH |
| Producer | RealObjects PDFreactor(R) 11.6.12 (16335), Serial No: 5501, Licensed for: Cherry Europe GmbH |

## Extracted Technical Index

This markdown datasheet is meant to reduce the need to reopen the PDF during design work.
It preserves design-relevant extracted snippets first, followed by page-by-page text so the source content remains locally searchable.

### Part number and ordering information

- No reliable text snippet was automatically extracted for this category. Review the raw page text below.

### Pin, pad, and connection designations

- unprecedented production quality "Made in / Germany" are unique. The MX2A series introduces a / new level typing experience, setting a new standard / for mechanical key switches. / FUNCTION AND …
- 5 cN / 1 / 2 © Cherry Americas • 9522 58th Place Suite 100 • Kenosha WI 53144 • USA / Phone: 262.942.6508 • <keyboardsupport@cherryamericas.com> • cherryamericas.com / Produktname Bestellnummer …
- 1 / 2 © Cherry Americas • 9522 58th Place Suite 100 • Kenosha WI 53144 • USA / Phone: 262.942.6508 • <keyboardsupport@cherryamericas.com> • cherryamericas.com / Produktname Bestellnummer Mountin…
- bridge RGB Switches / MX2A SILENT / RED MX2A-71NA without pins - faceplate / mount (3 Pins) / without
- MX2A SILENT / RED MX2A-71NA without pins - faceplate / mount (3 Pins) / without / diode yes
- diode yes / MX2A SILENT / RED MX2A-71NB with pin - PCB mount (5 / Pins) / without
- MX2A SILENT / RED MX2A-71NB with pin - PCB mount (5 / Pins) / without / diode yes
- diode yes / MX2A SILENT / RED MX2A-71NN without pins - faceplate / mount (3 Pins) / without
- MX2A SILENT / RED MX2A-71NN without pins - faceplate / mount (3 Pins) / without / diode no
- diode no / MX2A SILENT / RED MX2A-71NW with pin - PCB mount (5 / Pins) / without
- MX2A SILENT / RED MX2A-71NW with pin - PCB mount (5 / Pins) / without / diode no
- without / diode no / Please contact your local CHERRY service and support teams or your CHERRY sales partners for versions available in your country. / 2 / 2 © Cherry Americas • 9522 58th Place …
- Please contact your local CHERRY service and support teams or your CHERRY sales partners for versions available in your country. / 2 / 2 © Cherry Americas • 9522 58th Place Suite 100 • Kenosha W…

### Specifications, ratings, and operating conditions

- dimension: / 19,05 mm / Switching voltage: 2 - 12V AC/DC / Switching current: max. 10 mA / min. 10 μA
- 19,05 mm / Switching voltage: 2 - 12V AC/DC / Switching current: max. 10 mA / min. 10 μA / Spring: Stainless steel

### Dimensions, package, and mechanical information

- Models may vary from the image shown / Original CHERRY MX is the world´s leading precision / technology for mechanical key switches. The / CHERRY Gold Crosspoint contact concept and the / unprec…
- Germany" are unique. The MX2A series introduces a / new level typing experience, setting a new standard / for mechanical key switches. / FUNCTION AND PERFORMANCE / Linear switching characteristi…
- Actuation force: 45 cN / Standard grid / dimension: / 19,05 mm / Switching voltage: 2 - 12V AC/DC

### Formulas, equations, and configurable calculations

- No reliable text snippet was automatically extracted for this category. Review the raw page text below.

### Reference designs, applications, and examples

- No reliable text snippet was automatically extracted for this category. Review the raw page text below.

## Page-by-Page Extracted Content

### Page 1

```text
MX2A SILENT RED
Smooth and silent
Models may vary from the image shown
Original CHERRY MX is the world´s leading precision
technology for mechanical key switches. The
CHERRY Gold Crosspoint contact concept and the
unprecedented production quality "Made in
Germany" are unique. The MX2A series introduces a
new level typing experience, setting a new standard
for mechanical key switches.
FUNCTION AND PERFORMANCE
 Linear switching characteristics
 45 cN operating force
 1.9 mm pre travel
 3.7 mm total travel
 > 50 mil. keystrokes
 Lubricated
 Silent
→
→
→
→
→
→
→
TECHNICAL DATA
Actuation
characteristic:
linear
Actuator travel: 3,7 mm
Pre-Travel: 1,9 mm
Actuation force: 45 cN
Standard grid
dimension:
19,05 mm
Switching voltage: 2 - 12V AC/DC
Switching current: max. 10 mA
min. 10 μA
Spring: Stainless steel
IP protection class: 40
Bounce time: typically < 1 ms
Designation: CHERRY MX2A SILENT RED
Hotswap: no
USP: Smooth and silent
Noise level: Silent
Actuation force: medium (45-55 cN)
Reset force –
automatic:
5 cN
1 / 2 © Cherry Americas • 9522 58th Place Suite 100 • Kenosha WI 53144 • USA
Phone: 262.942.6508 • keyboardsupport@cherryamericas.com • cherryamericas.com
```

### Page 2

```text
Produktname Bestellnummer Mounting pins LED diode LED wire
bridge RGB Switches
MX2A SILENT
RED MX2A-71NA without pins - faceplate
mount (3 Pins)
without
diode yes
MX2A SILENT
RED MX2A-71NB with pin - PCB mount (5
Pins)
without
diode yes
MX2A SILENT
RED MX2A-71NN without pins - faceplate
mount (3 Pins)
without
diode no
MX2A SILENT
RED MX2A-71NW with pin - PCB mount (5
Pins)
without
diode no
Please contact your local CHERRY service and support teams or your CHERRY sales partners for versions available in your country.
2 / 2 © Cherry Americas • 9522 58th Place Suite 100 • Kenosha WI 53144 • USA
Phone: 262.942.6508 • keyboardsupport@cherryamericas.com • cherryamericas.com
```
