thepinkmile/Enigma-NG/design/Datasheets/erm8-erf8-product-spec.md

# Series: ERF8 / ERM8 0,80 mm (.0315”) Edge Rate™ Rugged High Speed Socket / Terminal Strip

## Source

- **Source PDF:** [erm8-erf8-product-spec.pdf](erm8-erf8-product-spec.pdf)
- **Generated Markdown:** `erm8-erf8-product-spec.md`
- **Page count:** 9
- **Conversion method:** automated local PDF text extraction with pypdf/pdfplumber

## PDF Metadata

| Field | Value |
| :--- | :--- |
| Title | «Picture_Description» is depicted |
| Author | John Tozier |
| Subject |  |
| Creator | Microsoft® Word for Microsoft 365 |
| Producer | Microsoft® Word for Microsoft 365 |

## Extracted Technical Index

This markdown datasheet is meant to reduce the need to reopen the PDF during design work.
It preserves design-relevant extracted snippets first, followed by page-by-page text so the source content remains locally searchable.

### Part number and ordering information

- Other configurations available for: / Coplanar and perpendicular board-to-board applications / Rugged features / end options / Packaging options
- Coplanar and perpendicular board-to-board applications / Rugged features / end options / Packaging options / See <www.samtec.com> for more information.

### Pin, pad, and connection designations

- Product Specification / Series:  ERF8 / ERM8 0,80 mm (.0315”) Edge Rate™ Rugged High Speed Socket / Terminal Strip / Revision: L Date: May 23, 2025 © 2013 Samtec, Inc.
- ERF8 Series – Socket, Vertical Orientation / ERM8 Series – Terminal, Vertical Orientation / Other configurations available for:
- 2.0 DETAILED INFORMATION / 2.1 Product prints, footprints, catalog pages, test reports and other specific, detailed information can be found at / <www.samtec.com?ERF8> and <www.samtec.com?ERM8.>
- 6.1 Based on a 3 dB insertion loss / Stack Height Single-Ended Signaling Differential Pair Signaling / 7 mm 12.00 GHz / 24 Gbps 15.50 GHz / 31 Gbps / 10 mm 16.00 GHz / 32 Gbps 20.00 GHz / 40 Gbps
- Nitrogen gas infusion) in the reflow process to improve solderability. / 7.8 Hardware: Board-to-board standoffs are recommended to provide a robust mechanical connection.  Samtec offers / severa…
- 8.0 ADDITIONAL RESOURCES / 8.1 For additional mechanical testing or product information, contact our Customer Engineering Support Group at / <CES@samtec.com> / 8.2 For additional information on …
- 8.1 For additional mechanical testing or product information, contact our Customer Engineering Support Group at / <CES@samtec.com> / 8.2 For additional information on high speed performance test…
- This Product Specification Sheet (“PSS”) is a brief summary of information related to the Product identified.  As a summary, it should / only be used for the limited purpose  of considering the …

### Specifications, ratings, and operating conditions

- Product Specification / Series:  ERF8 / ERM8 0,80 mm (.0315”) Edge Rate™ Rugged High Speed Socket / Terminal Strip
- See <www.samtec.com> for more information. / Product Specification / Series:  ERF8 / ERM8 0,80 mm (.0315”) Edge Rate™ Rugged High Speed Socket / Terminal Strip
- 1.0 SCOPE / 1.1 This specification covers performance, testing and quality requirements for Samtec’s ERF8/ERM8 Series 0,80 mm / pitch Edge Rate™ Rugged High Speed connectors.  All information co…
- 1.1 This specification covers performance, testing and quality requirements for Samtec’s ERF8/ERM8 Series 0,80 mm / pitch Edge Rate™ Rugged High Speed connectors.  All information contained in t…
- 3.0 TESTING / 3.1 Current Rating: 2.2A / 3.2 Voltage Rating: 225 VAC / 3.3 Operating Temperature Range: -55°C to +125°C
- 3.1 Current Rating: 2.2A / 3.2 Voltage Rating: 225 VAC / 3.3 Operating Temperature Range: -55°C to +125°C / 3.4 Operating Humidity Range: 90% to 95% (Per EIA-364-31)
- ITEM TEST CONDITION REQUIREMENT STATUS / Withstanding Voltage EIA-364-20 (No Flashover, / Sparkover, or Breakdown) 675 VAC Pass / Insulation Resistance EIA-364-21 (1000 MΩ
- Normal Force EIA-364-04 30 grams minimum for gold / interface Pass / Product Specification / Series:  ERF8 / ERM8 0,80 mm (.0315”) Edge Rate™ Rugged High Speed Socket / Terminal Strip
- ITEM TEST CONDITION REQUIREMENT STATUS / Thermal Shock / EIA-364-32 / Thermal Cycles: 100 (30 minute dwell)
- Thermal Shock / EIA-364-32 / Thermal Cycles: 100 (30 minute dwell) / Hot Temp: 85°C / Cold Temp: -55°C
- IR: >50,000 MΩ / Pass / Thermal Aging / (Temp Life) / EIA-364-17
- Mated view information can be found at link below: / <http://www.samtec.com/documents/webfiles/cpdf/ERX8%20Mated%20Document> -MKT.pdf / Product Specification / Series:  ERF8 / ERM8 0,80 mm (.031…
- 6.2 System Impedance: 50 ohm for single-ended and 100 ohm for differential pair / Product Specification / Series:  ERF8 / ERM8 0,80 mm (.0315”) Edge Rate™ Rugged High Speed Socket / Terminal Str…
- 7.1.2 Allowable final linear misalignment. / Product Specification / Series:  ERF8 / ERM8 0,80 mm (.0315”) Edge Rate™ Rugged High Speed Socket / Terminal Strip
- 7.2.2 Allowable final angular misalignment / Product Specification / Series:  ERF8 / ERM8 0,80 mm (.0315”) Edge Rate™ Rugged High Speed Socket / Terminal Strip
- These guidelines should not be considered design requirements for all applications. / Samtec recommends testing interconnects on your boards in your process to guarantee optimum results. / Produ…
- -08.0 13.00 XXXX-1300 15.00 XXXX-1500 17.00 XXXX-1700 18.00 XXXX-1800 / -09.0 14.00 XXXX-1400 16.00 XXXX-1600 18.00 XXXX-1800 19.00 XXXX-1900 / Product Specification / Series:  ERF8 / ERM8 0,80 …
- Compliance Group at <PEC@samtec.com> / USE OF PRODUCT SPECIFICATION SHEET / This Product Specification Sheet (“PSS”) is a brief summary of information related to the Product identified.  As a su…
- USE OF PRODUCT SPECIFICATION SHEET / This Product Specification Sheet (“PSS”) is a brief summary of information related to the Product identified.  As a summary, it should / only be used for the…

### Dimensions, package, and mechanical information

- 2.0 DETAILED INFORMATION / 2.1 Product prints, footprints, catalog pages, test reports and other specific, detailed information can be found at / <www.samtec.com?ERF8> and <www.samtec.com?ERM8.>
- (Samtec defined)/ No damage Pass / 3.6 Mechanical: / ITEM TEST CONDITION REQUIREMENT STATUS
- 50 nanoseconds / Pass / Mechanical Shock / EIA-364-27  100 G, 6 / milliseconds, sawtooth wave,
- Nitrogen gas infusion) in the reflow process to improve solderability. / 7.8 Hardware: Board-to-board standoffs are recommended to provide a robust mechanical connection.  Samtec offers / severa…
- 8.0 ADDITIONAL RESOURCES / 8.1 For additional mechanical testing or product information, contact our Customer Engineering Support Group at / <CES@samtec.com> / 8.2 For additional information on …
- This Product Specification Sheet (“PSS”) is a brief summary of information related to the Product identified.  As a summary, it should / only be used for the limited purpose  of considering the …

### Formulas, equations, and configurable calculations

- ERM8 Series – Terminal, Vertical Orientation / Other configurations available for: / Coplanar and perpendicular board-to-board applications / Rugged features / end options
- 1.1 This specification covers performance, testing and quality requirements for Samtec’s ERF8/ERM8 Series 0,80 mm / pitch Edge Rate™ Rugged High Speed connectors.  All information contained in t…
- ITEM TEST CONDITION REQUIREMENT STATUS / Durability EIA-364-09C 1000 cycles (30µ Au) Pass / Random Vibration / EIA-364-28 Condition V, Letter B / 7.56 G 'RMS', 50 to 2000 Hz, 2
- Test Temp:  25°C to 65°C / Relative Humidity: 90 to 95% / Test Duration: 240 hours / Visual Inspection:  No Damage / LLCR: Δ 15 mΩ
- EIA-364-36 / Gas Exposure:  Nitric Acid Vapor / Duration:  60 min. / Drying Temp.:  50°C +/- 3°C / Measurements:  Within 1 hour of

### Reference designs, applications, and examples

- Other configurations available for: / Coplanar and perpendicular board-to-board applications / Rugged features / end options / Packaging options
- Revision: L Date: May 23, 2025 © 2013 Samtec, Inc. / Page 7 / 7.3 Due to variances in equipment, solder pastes and applications (board design, component density, etc.), Samtec / does not specify…
- 7.3.1 / These guidelines should not be considered design requirements for all applications. / Samtec recommends testing interconnects on your boards in your process to guarantee optimum results.…

## Page-by-Page Extracted Content

### Page 1

```text
Product Specification

Series:  ERF8 / ERM8 0,80 mm (.0315”) Edge Rate™ Rugged High Speed Socket / Terminal Strip

Revision: L Date: May 23, 2025 © 2013 Samtec, Inc.
 Page 1
ERF8 Series – Socket, Vertical Orientation

ERM8 Series – Terminal, Vertical Orientation

Other configurations available for:
Coplanar and perpendicular board-to-board applications
Rugged features / end options
Packaging options

See www.samtec.com for more information.
```

### Page 2

```text
Product Specification

Series:  ERF8 / ERM8 0,80 mm (.0315”) Edge Rate™ Rugged High Speed Socket / Terminal Strip

Revision: L Date: May 23, 2025 © 2013 Samtec, Inc.
 Page 2

1.0 SCOPE

1.1 This specification covers performance, testing and quality requirements for Samtec’s ERF8/ERM8 Series 0,80 mm
pitch Edge Rate™ Rugged High Speed connectors.  All information contained in this specification is for a 10 mm
mated height vertical configuration unless otherwise noted.

2.0 DETAILED INFORMATION

2.1 Product prints, footprints, catalog pages, test reports and other specific, detailed information can be found at
www.samtec.com?ERF8 and www.samtec.com?ERM8.

3.0 TESTING

3.1 Current Rating: 2.2A
3.2 Voltage Rating: 225 VAC
3.3 Operating Temperature Range: -55°C to +125°C
3.4 Operating Humidity Range: 90% to 95% (Per EIA-364-31)
3.5 Electrical:

ITEM TEST CONDITION REQUIREMENT STATUS
Withstanding Voltage EIA-364-20 (No Flashover,
Sparkover, or Breakdown) 675 VAC Pass
Insulation Resistance EIA-364-21 (1000 MΩ
minimum) 50,000 MΩ Pass
Contact Resistance
(LLCR) EIA-364-23 Δ 15 mΩ maximum
(Samtec defined)/ No damage Pass

3.6 Mechanical:

ITEM TEST CONDITION REQUIREMENT STATUS
Durability EIA-364-09C 1000 cycles (30µ Au) Pass
Random Vibration
EIA-364-28 Condition V, Letter B
7.56 G 'RMS', 50 to 2000 Hz, 2
hours per axis, 3 axis total, PSD
0.04
Visual Inspection: No Damage
LLCR: Δ 15 mΩ maximum
Event Detection: No interruption >
50 nanoseconds
Pass
Mechanical Shock
EIA-364-27  100 G, 6
milliseconds, sawtooth wave,
11.3 fps, 3 shocks/direction, 3
axis (18 total shocks)
Visual Inspection: No Damage
LLCR: Δ 15 mΩ maximum
Event Detection: No interruption >
50 nanoseconds
Pass
Normal Force EIA-364-04 30 grams minimum for gold
interface Pass
```

### Page 3

```text
Product Specification

Series:  ERF8 / ERM8 0,80 mm (.0315”) Edge Rate™ Rugged High Speed Socket / Terminal Strip

Revision: L Date: May 23, 2025 © 2013 Samtec, Inc.
 Page 3
3.7 Environmental:

ITEM TEST CONDITION REQUIREMENT STATUS
Thermal Shock
EIA-364-32
Thermal Cycles: 100 (30 minute dwell)
Hot Temp: 85°C
Cold Temp: -55°C
Hot/Cold Transition:  Immediate
Visual Inspection:  No Damage
LLCR: Δ 15 mΩ
DWV: 675 VAC
IR: >50,000 MΩ
Pass
Thermal Aging
(Temp Life)
EIA-364-17
Test Condition 4 @ 105°C Condition B
for 250 hours
Visual Inspection:  No Damage
LLCR: Δ 15 mΩ
DWV: 675 VAC
IR: >50,000 MΩ
Pass
Cyclic Humidity
EIA-364-31
Test Temp:  25°C to 65°C
Relative Humidity: 90 to 95%
Test Duration: 240 hours
Visual Inspection:  No Damage
LLCR: Δ 15 mΩ
DWV: 675 VAC
IR: >50,000 MΩ
Pass
Gas Tight
EIA-364-36
Gas Exposure:  Nitric Acid Vapor
Duration:  60 min.
Drying Temp.:  50°C +/- 3°C
Measurements:  Within 1 hour of
Exposure
LLCR:  Δ 15 mΩ Pass

4.0 MATED SYSTEM

4.1 Mated Views
Mated view information can be found at link below:
http://www.samtec.com/documents/webfiles/cpdf/ERX8%20Mated%20Document -MKT.pdf
```

### Page 4

```text
Product Specification

Series:  ERF8 / ERM8 0,80 mm (.0315”) Edge Rate™ Rugged High Speed Socket / Terminal Strip

Revision: L Date: May 23, 2025 © 2013 Samtec, Inc.
 Page 4
5.0 POLARIZING FEATURES

6.0 HIGH SPEED PERFORMANCE

6.1 Based on a 3 dB insertion loss

Stack Height Single-Ended Signaling Differential Pair Signaling
7 mm 12.00 GHz / 24 Gbps 15.50 GHz / 31 Gbps
10 mm 16.00 GHz / 32 Gbps 20.00 GHz / 40 Gbps
16 mm 16.00 GHz / 32 Gbps 20.00 GHz / 40 Gbps
ERM8-EM/ERF8 13.50 GHz / 27 Gbps 14.00 GHz / 28 Gbps
ERM8-RA/ERF8
(Short Row) 17.00 GHz / 34 Gbps 17.50 GHz / 35 Gbps
ERM8-RA/ERF8-RA
(Short Row)  8.00 GHz / 16 Gbps 7.50 GHz / 15 Gbps

6.2 System Impedance: 50 ohm for single-ended and 100 ohm for differential pair
```

### Page 5

```text
Product Specification

Series:  ERF8 / ERM8 0,80 mm (.0315”) Edge Rate™ Rugged High Speed Socket / Terminal Strip

Revision: L Date: May 23, 2025 © 2013 Samtec, Inc.
 Page 5
7.0 PROCESSING RECOMMENDATIONS

7.1 Mating Alignment Requirements:

7.1.1 Allowable initial linear misalignment.

7.1.2 Allowable final linear misalignment.
```

### Page 6

```text
Product Specification

Series:  ERF8 / ERM8 0,80 mm (.0315”) Edge Rate™ Rugged High Speed Socket / Terminal Strip

Revision: L Date: May 23, 2025 © 2013 Samtec, Inc.
 Page 6

7.2 Mating Angle Requirements:

7.2.1 Allowable initial angular misalignment

7.2.2 Allowable final angular misalignment
```

### Page 7

```text
Product Specification

Series:  ERF8 / ERM8 0,80 mm (.0315”) Edge Rate™ Rugged High Speed Socket / Terminal Strip

Revision: L Date: May 23, 2025 © 2013 Samtec, Inc.
 Page 7
7.3 Due to variances in equipment, solder pastes and applications (board design, component density, etc.), Samtec
does not specify a recommended reflow profile for our connectors. The processing parameters provided by the
solder paste manufacturer should be employed and can usually be found on their website.

All of Samtec’s surface mount components are lead free reflow compatible and compliant with the profile
parameters detailed in IPC/JEDEC J-STD-020 which requires that components be capable of withstanding a peak
temperature of 260°C as well as 30 seconds above 255°C.

Samtec Recommended Temperature Profile Ranges (SMT)

Sn-Pb Eutectic Assembly

Preheat/Soak
(100°C-150°C)
Max Ramp Up
Rate
Reflow Time
(above 183°C)
Peak
Temp
Time within 5°C
of 235°C
Max Ramp
Down Rate
Time 25°C to
Peak Temp
60-120 sec. 3°C/s max. 40-150 sec. 235°C 20 sec. max. 6°C/s max. 6 min. max.

Pb-Free Assembly

Preheat/Soak
(150°C-200°C)
Max Ramp Up
Rate
Reflow Time
(above 217°C)
Peak
Temp
Time within 5°C
of 260°C
Max Ramp
Down Rate
Time 25°C to
Peak Temp
60-120 sec. 3°C/s max. 40-150 sec. 260°C 30 sec. max. 6°C/s max. 8 min. max.

7.3.1

These guidelines should not be considered design requirements for all applications.
Samtec recommends testing interconnects on your boards in your process to guarantee optimum results.
```

### Page 8

```text
Product Specification

Series:  ERF8 / ERM8 0,80 mm (.0315”) Edge Rate™ Rugged High Speed Socket / Terminal Strip

Revision: L Date: May 23, 2025 © 2013 Samtec, Inc.
 Page 8
7.4 Maximum Reflow Passes: The parts can withstand three reflow passes at a maximum component temperature of
260°C.

7.5 Stencil Thickness: The stencil thickness is 0.15 [.006].

7.6 Placement: Machine placement of the parts in the Z-axis is strongly recommended.

7.7 Reflow Environment:  Samtec recommends the use of a low level oxygen environment (typically achieved through
Nitrogen gas infusion) in the reflow process to improve solderability.

7.8 Hardware: Board-to-board standoffs are recommended to provide a robust mechanical connection.  Samtec offers
several different types, which can be found here: Samtec Standoff Offerings.

ERF8 LEAD STYLE
-05.0 -07.0 -09.0 -10.0
ERM8
LEAD STYLE
Nominal
Connector
Stack Height
"A" (mm)
Standoff
Nominal
Connector
Stack Height
"A" (mm)
Standoff
Nominal
Connector
Stack Height
"A" (mm)
Standoff
Nominal
Connector
Stack Height
"A" (mm)
Standoff
-02.0 7.00 XXXX-0700 9.00 XXXX-0900 11.00 XXXX-1100 12.00 XXXX-1200
-03.0 8.00 XXXX-0800 10.00 XXXX-1000 12.00 XXXX-1200 13.00 XXXX-1300
-05.0 10.00 XXXX-1000 12.00 XXXX-1200 14.00 XXXX-1400 15.00 XXXX-1500
-08.0 13.00 XXXX-1300 15.00 XXXX-1500 17.00 XXXX-1700 18.00 XXXX-1800
-09.0 14.00 XXXX-1400 16.00 XXXX-1600 18.00 XXXX-1800 19.00 XXXX-1900
```

### Page 9

```text
Product Specification

Series:  ERF8 / ERM8 0,80 mm (.0315”) Edge Rate™ Rugged High Speed Socket / Terminal Strip

Revision: L Date: May 23, 2025 © 2013 Samtec, Inc.
 Page 9
7.9 Cleaning: Samtec, Inc. has verified that our connectors may be cleaned in accordance with the solvents and
conditions designated in the EIA-364-11 standard.

8.0 ADDITIONAL RESOURCES

8.1 For additional mechanical testing or product information, contact our Customer Engineering Support Group at
CES@samtec.com
8.2 For additional information on high speed performance testing, contact our Signal Integrity Group at
SIG@samtec.com
8.3 For additional processing information, contact our Interconnect Processing Group at IPG@samtec.com.
8.4 For RoHS, REACH or other environmental compliance information, contact our Product Environmental
Compliance Group at PEC@samtec.com

USE OF PRODUCT SPECIFICATION SHEET

This Product Specification Sheet (“PSS”) is a brief summary of information related to the Product identified.  As a summary, it should
only be used for the limited purpose  of considering the purchase/use of Product.  For specific, detailed information, including but not
limited to testing and Product footprint, refer to Section 2.0 of this document and the links there provided to test reports and prints.  This
PSS is the property of  Samtec, Inc. (“Samtec”) and contains proprietary information of Samtec, our various licensors, or both. Samtec
does not grant express or implied rights or license under any patent, copyright, trademark or other proprietary rights and the use of the
PSS for building, reverse engineering or replication is strictly prohibited. By using the PSS, the u ser agrees to not infringe, directly or
indirectly, upon any intellectual property rights of Samtec and acknowledges that Samtec , our various licensors, or both  own all
intellectual property therein. The PSS is presented “AS IS”. While Samtec makes every effort to present excellent information, the PSS
is only provided as a guideline and does not, therefore, warrant it is without error or defect or that the PSS contains all necessary and/or
relevant information about the Product.  The user agrees that all access and use of the PSS is at its own risk. NO WARRANTIES
EXPRESSED OR IMPLIED, INCLUDING ANY WARRANTY OF MERCHANTABILITY, FITNESS FOR A PARTICULAR
PURPOSE OR OF ANY KIND WHATSOEVER ARE PROVIDED.
```
