thepinkmile/Enigma-NG/design/Datasheets/HanElectricity-CPG151101S11-16-datasheet.md

# HanElectricity CPG151101S11-16

## Source

- **Source PDF:** [HanElectricity-CPG151101S11-16-datasheet.pdf](HanElectricity-CPG151101S11-16-datasheet.pdf)
- **Generated Markdown:** `HanElectricity-CPG151101S11-16-datasheet.md`
- **Page count:** 1
- **Conversion method:** automated local PDF text extraction with pypdf/pdfplumber

## PDF Metadata

| Field | Value |
| :--- | :--- |
| Title | 模型 |
| Author | |
| Subject | |
| Creator | AutoCAD 2019 - 简体中文 (Simplified Chinese) 2019 (23.0s (LMS Tech)) |
| Producer | pdfplot15.hdi 15.00.046.000 |

## Extracted Technical Index

This markdown datasheet is meant to reduce the need to reopen the PDF during design work.
It preserves design-relevant extracted snippets first, followed by page-by-page text so the source content remains locally searchable.

### Part number and ordering information

- No reliable text snippet was automatically extracted for this category. Review the raw page text below.

### Pin, pad, and connection designations

- No reliable text snippet was automatically extracted for this category. Review the raw page text below.

### Specifications, ratings, and operating conditions

- HanElectricity  Co.,LTD / UNLESS OTHERWISE / SPECIFIED,TOLERANCE: / X.                 ±0.25 / X.x               ±0.20
- ■ / Specification : / ●1.Rating: / Voltage :12V AC/DC max.,2V DC min.
- Specification : / ●1.Rating: / Voltage :12V AC/DC max.,2V DC min. / Current: 10mA AC/DC max.,10µA DC min. / ●2.Contact Resistance : 100m
- ●1.Rating: / Voltage :12V AC/DC max.,2V DC min. / Current: 10mA AC/DC max.,10µA DC min. / ●2.Contact Resistance : 100m / Ω Max
- Ω Max / ●3.Insulation Resistance :100MΩ at 500V / ●4.Withstand Voltage :AC100V(50-60Hz) / for 1 minute / ●5.Mating Force :3.0kgf max

### Dimensions, package, and mechanical information

- Mikey / FILE.NO.3RD ANGLE PROJ / SCALE: 3:1DESIGNED CHECKED APPROVAL DRAWING NUMBER / PART NAME / MODEL NAMETom Jerry

### Formulas, equations, and configurable calculations

- No reliable text snippet was automatically extracted for this category. Review the raw page text below.

### Reference designs, applications, and examples

- No reliable text snippet was automatically extracted for this category. Review the raw page text below.

## Page-by-Page Extracted Content

### Page 1

```text
DATE.
Mikey
FILE.NO.3RD ANGLE PROJ
SCALE: 3:1DESIGNED CHECKED APPROVAL DRAWING NUMBER
PART NAME
MODEL NAMETom Jerry
ECN BO.
DESCRIPTION.
new
REV.
A
SCALT: 1/2
2015/5/3
瀚源
HanElectricity  Co.,LTD
UNLESS OTHERWISE
SPECIFIED,TOLERANCE:
X.                 ±0.25
X.x               ±0.20
X.xx             ±0.15
ANGULAR   ±3°
■

Specification :
●1.Rating:
   Voltage :12V AC/DC max.,2V DC min.
   Current: 10mA AC/DC max.,10µA DC min.
●2.Contact Resistance : 100m
Ω Max
●3.Insulation Resistance :100MΩ at 500V
●4.Withstand Voltage :AC100V(50-60Hz)
   for 1 minute
●5.Mating Force :3.0kgf max
●6.Operating Life :5000 Cycles
CPG151101S11-16
CPG151101S11-16
```
