thepinkmile/Enigma-NG/design/Datasheets/Kingbright-APFA2507Y2G2C_C2-datasheet.md

# © 2023 Kingbright. All Rights Reserved. Spec No: DSAQ1758 / 1203016110 Rev No: V.3B Date: 05/18/2023

## Source

- **Source PDF:** [Kingbright-APFA2507Y2G2C_C2-datasheet.pdf](Kingbright-APFA2507Y2G2C_C2-datasheet.pdf)
- **Generated Markdown:** `Kingbright-APFA2507Y2G2C_C2-datasheet.md`
- **Page count:** 4
- **Conversion method:** automated local PDF text extraction with pypdf/pdfplumber

## PDF Metadata

| Field | Value |
| :--- | :--- |
| Title | APFA2507Y2G2C-C2(Ver.3B) |
| Author | rd15f15 |
| Subject |  |
| Creator | PScript5.dll Version 5.2.2 |
| Producer | Acrobat Distiller 9.0.0 (Windows) |

## Extracted Technical Index

This markdown datasheet is meant to reduce the need to reopen the PDF during design work.
It preserves design-relevant extracted snippets first, followed by page-by-page text so the source content remains locally searchable.

### Part number and ordering information

- RECOMMENDED SOLDERING PATTERN / (units : mm; tolerance : ± 0.1) / Part Number  Emitting Color / (Material)  Lens Type / Iv (mcd) @ 20mA [2]                                          Viewing Angle…
- PRECAUTIONARY NOTES / 1. The information included in this document reflects represent ative usage scenarios and is intended for technical reference only. / 2. The part number, type, and specific…

### Pin, pad, and connection designations

-   Package: 3000 pcs / reel /  Moisture sensitivity level: 3 /   Tinned pads for improved solderability /   Halogen-free /  RoHS compliant
-  Status indicator /  Home and smart appliances /  Wearable and portable devices /  Healthcare applications
- Notes: / 1. 1/10 Duty Cycle, 0.1ms Pulse Width. / 2. Rth JA ,Rth JS  Results from mounting on PC board FR4 (pad size ≥ 16 mm 2 per pad). / 3. Relative humidity levels maintained between 40% and …

### Specifications, ratings, and operating conditions

- 2.5 x 0.7 mm Right Angle SMD Chip LED Lamp / RECOMMENDED SOLDERING PATTERN / (units : mm; tolerance : ± 0.1) / Part Number  Emitting Color / (Material)  Lens Type
- Notes: / 1. All dimensions are in millimeters (inches). / 2. Tolerance is ±0.15(0.006") unless otherwise noted. / 3. The specifications, characteristics and technical data described in the datas…
- 1. All dimensions are in millimeters (inches). / 2. Tolerance is ±0.15(0.006") unless otherwise noted. / 3. The specifications, characteristics and technical data described in the datasheet are …
- 3. The specifications, characteristics and technical data described in the datasheet are subject to / change without prior notice. / 4. The device has a single mounting surface. The device must …
- ELECTRICAL / OPTICAL CHARACTERISTICS at TA=25°C / Notes: / 1. The dominant wavelength (λd) above is the setup value of the sorting machine. (Tolerance  λd: ±1nm. ) / 2. Forward voltage: ±0.1V. /…
- Notes: / 1. The dominant wavelength (λd) above is the setup value of the sorting machine. (Tolerance  λd: ±1nm. ) / 2. Forward voltage: ±0.1V. / 3. Wavelength value is traceable to CIE127-2007 s…
- 2. Forward voltage: ±0.1V. / 3. Wavelength value is traceable to CIE127-2007 standards. / 4. Excess driving current and / or operating temperature higher than recommended conditions may result i…
- 15 / - pF / Forward Voltage IF = 20mA     VF [2] Super Bright Yellow / Green / 2.0
- 2.5 / V / Reverse Current (VR = 5V)    IR Super Bright Yellow / Green - 10 / 10
- -1.9 / - mV/°C / ABSOLUTE MAXIMUM RATINGS at TA=25°C / Parameter  Symbol / Value
- Super Bright Yellow  Green / Power Dissipation PD 75 75 mW / Reverse Voltage VR 5 5 V / Junction Temperature TJ 115 115 °C / Operating Temperature Top -40 To +85  °C
- Operating Temperature Top -40 To +85  °C / Storage Temperature Tstg -40 To +85  °C / DC Forward Current  IF 30 30 mA / Peak Forward Current  IFM [1] 175 150 mA / Electrostatic Discharge Threshol…
- Storage Temperature Tstg -40 To +85  °C / DC Forward Current  IF 30 30 mA / Peak Forward Current  IFM [1] 175 150 mA / Electrostatic Discharge Threshold (HBM)  - 3000 3000 V / Thermal Resistance…
- Peak Forward Current  IFM [1] 175 150 mA / Electrostatic Discharge Threshold (HBM)  - 3000 3000 V / Thermal Resistance (Junction / Ambient)  Rth JA [2] 680 700 °C/W / Thermal Resistance (Junctio…
- Electrostatic Discharge Threshold (HBM)  - 3000 3000 V / Thermal Resistance (Junction / Ambient)  Rth JA [2] 680 700 °C/W / Thermal Resistance (Junction / Solder point)     Rth JS [2] 580 590 °C…
- 1.5 1.7 1.9 2.1 2.3 2.5 / Ta = 25 °C / Forward voltage (V) / Forward current (mA) / 0.0
- Ta = 25 °C / Forward voltage (V) / Forward current (mA) / 0.0 / 0.5
- 0 1 02 03 04 05 0 / Ta = 25 °C / Forward current (mA) / Luminous intensity normalised at / 20 mA
- - 4 0 - 2 0 0 2 04 06 08 0 1 0 0 / Ambient temperature (°C) / Permissible forward current (mA) 0.0 / 0.5 / 1.0
- Luminous intensity normalised at / Ta = 25 °C / Forward Current vs. / Forward Voltage / Luminous Intensity vs.

### Dimensions, package, and mechanical information

-  Wide viewing angle /  Ideal for backlight and indicator /   Package: 3000 pcs / reel /  Moisture sensitivity level: 3 /   Tinned pads for improved solderability
- Observe precautions for handling / electrostatic discharge sensitive devices / PACKAGE DIMENSIONS / SELECTION GUIDE / Notes:
- ■ Green (AlGaInP) 20 45 / Notes: / 1. All dimensions are in millimeters (inches). / 2. Tolerance is ±0.15(0.006") unless otherwise noted. / 3. The specifications, characteristics and technical d…
- PACKING & LABEL SPECIFICATIONS / TAPE SPECIFICATIONS (units : mm) / REEL DIMENSION (units : mm) / REFLOW SOLDERING PROFILE for LEAD-FREE SMD PROCESS / APFA2507Y2G2C-C2

### Formulas, equations, and configurable calculations

- DESCRIPTIONS /  The Super Bright Yellow device is made with / AlGaInP (on GaAs substrate) light emitting diode chip /  The Green source color devices are made with / AlGaInP on GaAs substrate …
- AlGaInP (on GaAs substrate) light emitting diode chip /  The Green source color devices are made with / AlGaInP on GaAs substrate Light Emitting Diode /  Electrostatic discharge and power surg…
- APFA2507Y2G2C-C2 / ■ Super Bright Yellow / (AlGaInP) / Water Clear / 80 130
- 80 130 / 130° / ■ Green (AlGaInP) 20 45 / Notes: / 1. All dimensions are in millimeters (inches).

### Reference designs, applications, and examples

-  RoHS compliant / APPLICATIONS /  Backlight /  Status indicator
-  Home and smart appliances /  Wearable and portable devices /  Healthcare applications / ATTENTION
- 3. When using the products referenced in this document, please make sure the product is being operated within the environmenta l and electrical limits specified in the datasheet. If / customer u…
- liabilities, such as automotive or medical usage, please consult with Kingbright representative for further assistance. / 5. The contents and information of this document may not be rep roduced …

## Page-by-Page Extracted Content

### Page 1

```text
© 2023 Kingbright. All Rights Reserved.   Spec No: DSAQ1758 / 1203016110   Rev No: V.3B   Date: 05/18/2023
 Page  1 / 4
DESCRIPTIONS
 The Super Bright Yellow device is made with
   AlGaInP (on GaAs substrate) light emitting diode chip
 The Green source color devices are made with
   AlGaInP on GaAs substrate Light Emitting Diode
 Electrostatic discharge and power surge could
   damage the LEDs
 It is recommended to use a wrist band or
   anti-electrostatic glove when handling the LEDs
 All devices, equipments and machineries must be
   electrically grounded

FEATURES
  2.5 x 1.0 x 0.7 mm right angle SMD LED, 0.7 mm
   thickness
 Low power consumption
 Wide viewing angle
 Ideal for backlight and indicator
  Package: 3000 pcs / reel
 Moisture sensitivity level: 3
  Tinned pads for improved solderability
  Halogen-free
 RoHS compliant

APPLICATIONS
 Backlight
 Status indicator
 Home and smart appliances
 Wearable and portable devices
 Healthcare applications

ATTENTION
Observe precautions for handling
electrostatic discharge sensitive devices
PACKAGE DIMENSIONS
SELECTION GUIDE
Notes:
1. θ1/2 is the angle from optical centerline where the luminous intensity is 1/2 of the optical peak value.
2. Luminous intensity / luminous flux: +/-15%.
3. Luminous intensity value is traceable to CIE127-2007 standards.
APFA2507Y2G2C-C2
2.5 x 0.7 mm Right Angle SMD Chip LED Lamp
RECOMMENDED SOLDERING PATTERN
(units : mm; tolerance : ± 0.1)
Part Number  Emitting Color
(Material)  Lens Type
Iv (mcd) @ 20mA [2]                                          Viewing Angle [1]
Min.  Typ.  2θ1/2
APFA2507Y2G2C-C2
 ■ Super Bright Yellow
       (AlGaInP)
Water Clear
80 130
130°
 ■ Green (AlGaInP) 20 45
Notes:
1. All dimensions are in millimeters (inches).
2. Tolerance is ±0.15(0.006") unless otherwise noted.
3. The specifications, characteristics and technical data described in the datasheet are subject to
    change without prior notice.
4. The device has a single mounting surface. The device must be mounted according to the specifications.
5. For right angle SMD LEDs, the solder stencil should be at least 5mil in thickness, to prevent poor solder wetting
   due to insufficient solder paste.
```

### Page 2

```text
© 2023 Kingbright. All Rights Reserved.   Spec No: DSAQ1758 / 1203016110   Rev No: V.3B   Date: 05/18/2023
 Page  2 / 4
ELECTRICAL / OPTICAL CHARACTERISTICS at TA=25°C
Notes:
1. The dominant wavelength (λd) above is the setup value of the sorting machine. (Tolerance  λd: ±1nm. )
2. Forward voltage: ±0.1V.
3. Wavelength value is traceable to CIE127-2007 standards.
4. Excess driving current and / or operating temperature higher than recommended conditions may result in severe light degradation or premature failure.
APFA2507Y2G2C-C2
Parameter  Symbol   Emitting Color
Value
Unit
Typ. Max.
Wavelength at Peak Emission IF = 20mA     λpeak Super Bright Yellow
Green
590
574
- nm
Dominant Wavelength IF = 20mA    λdom [1] Super Bright Yellow
Green
590
570
- nm
Spectral Bandwidth at 50% Φ REL MAX
 IF = 20mA  Δλ Super Bright Yellow
Green
20
20
- nm
Capacitance C Super Bright Yellow
Green
20
15
- pF
Forward Voltage IF = 20mA     VF [2] Super Bright Yellow
Green
2.0
2.1
2.5
2.5
V
Reverse Current (VR = 5V)    IR Super Bright Yellow
Green - 10
10
μA
Temperature Coefficient of λpeak
IF = 20mA, -10°C ≤ T ≤ 85°C      TCλpeak Super Bright Yellow
Green
0.12
0.12
- nm/°C
Temperature Coefficient of λdom
IF = 20mA, -10°C ≤ T ≤ 85°C      TCλdom Super Bright Yellow
Green
0.07
0.08
- nm/°C
Temperature Coefficient of  VF
IF = 20mA, -10°C ≤ T ≤ 85°C      TCV Super Bright Yellow
Green
-1.9
-1.9
- mV/°C
ABSOLUTE MAXIMUM RATINGS at TA=25°C
Parameter  Symbol
Value
Unit
Super Bright Yellow  Green
Power Dissipation PD 75 75 mW
Reverse Voltage VR 5 5 V
Junction Temperature TJ 115 115 °C
Operating Temperature Top -40 To +85  °C
Storage Temperature Tstg -40 To +85  °C
DC Forward Current  IF 30 30 mA
Peak Forward Current  IFM [1] 175 150 mA
Electrostatic Discharge Threshold (HBM)  - 3000 3000 V
Thermal Resistance (Junction / Ambient)  Rth JA [2] 680 700 °C/W
Thermal Resistance (Junction / Solder point)     Rth JS [2] 580 590 °C/W
Notes:
1. 1/10 Duty Cycle, 0.1ms Pulse Width.
2. Rth JA ,Rth JS  Results from mounting on PC board FR4 (pad size ≥ 16 mm 2 per pad).
3. Relative humidity levels maintained between 40% and 60% in production area are recommended to avoid the build-up of static electricity – Ref JEDEC/JESD625-A and JEDEC/J-STD-033.
```

### Page 3

```text
© 2023 Kingbright. All Rights Reserved.   Spec No: DSAQ1758 / 1203016110   Rev No: V.3B   Date: 05/18/2023
 Page  3 / 4
0.5 0.5 0.0
-90°
-75°
-60°
-45°
-30°
-15°
75°
60°
45°
30°
0° 15°
90°
1.0 1.0
Ta = 25 °C
TECHNICAL DATA
0%
20%
40%
60%
80%
100%
350 400 450 500 550 600 650 700 750 800
T
a = 25 °C
Green
Wavelength (nm)
Relative Intensity (a. u.)
Yellow
RELATIVE INTENSITY vs. WAVELENGTH SPATIAL DISTRIBUTION
APFA2507Y2G2C-C2
0
10
20
30
40
50
1.5 1.7 1.9 2.1 2.3 2.5
Ta = 25 °C
Forward voltage (V)
Forward current (mA)
0.0
0.5
1.0
1.5
2.0
2.5
0 1 02 03 04 05 0
Ta = 25 °C
Forward current (mA)
Luminous intensity normalised at
20 mA
0
10
20
30
40
50
- 4 0 - 2 0 0 2 04 06 08 0 1 0 0
Ambient temperature (°C)
Permissible forward current (mA) 0.0
0.5
1.0
1.5
2.0
2.5
- 4 0 - 2 00 2 04 06 08 0 1 0 0
Ambient temperature (°C)
Luminous intensity normalised at
Ta = 25 °C
0
10
20
30
40
50
1.5 1.7 1.9 2.1 2.3 2.5
Ta = 25 °C
Forward voltage (V)
Forward current (mA)
0.0
0.5
1.0
1.5
2.0
2.5
0 1 02 03 04 05 0
Ta = 25 °C
Forward current (mA)
Luminous intensity normalised at
20 mA
0
10
20
30
40
50
- 4 0 - 2 0 0 2 04 06 08 0 1 0 0
Ambient temperature (°C)
Permissible forward current (mA) 0.0
0.5
1.0
1.5
2.0
2.5
- 4 0 - 2 00 2 04 06 08 0 1 0 0
Ambient temperature (°C)
Luminous intensity normalised at
Ta = 25 °C
Forward Current vs.
Forward Voltage
Luminous Intensity vs.
Forward Current
Forward Current Derating  Curve Luminous Intensity vs.
Ambient Temperature
SUPER BRIGHT YELLOW
Forward Current vs.
Forward Voltage
Luminous Intensity vs.
Forward Current
Forward Current Derating  Curve Luminous Intensity vs.
Ambient Temperature
GREEN
```

### Page 4

```text
© 2023 Kingbright. All Rights Reserved.   Spec No: DSAQ1758 / 1203016110   Rev No: V.3B   Date: 05/18/2023
 Page  4 / 4
PACKING & LABEL SPECIFICATIONS
TAPE SPECIFICATIONS (units : mm)
 REEL DIMENSION (units : mm)
REFLOW SOLDERING PROFILE for LEAD-FREE SMD PROCESS
APFA2507Y2G2C-C2
Notes:
1. Don't cause stress to the LEDs while it is exposed to high temperature.
2. The maximum number of reflow soldering passes is 2 times.
3. Reflow soldering is recommended. Other soldering methods are not recommended as they might
    cause damage to the product.
PRECAUTIONARY NOTES
1. The information included in this document reflects represent ative usage scenarios and is intended for technical reference only.
2. The part number, type, and specifications mentioned in this document are subject to future change and improvement without n otice. Before production usage customer should refer
to the latest datasheet for the updated specifications.
3. When using the products referenced in this document, please make sure the product is being operated within the environmenta l and electrical limits specified in the datasheet. If
customer usage exceeds the specified limits, Kingbright will not be responsible for any subsequent issues.
4. The information in this document applies to typical usage in  consumer electronics applications. If customer's application h as special reliability requirements or have life-threatening
liabilities, such as automotive or medical usage, please consult with Kingbright representative for further assistance.
5. The contents and information of this document may not be rep roduced or re-transmitted without permission by Kingbright.
6. All design applications should refer to Kingbright applicati on notes available at https://www.KingbrightUSA.com/ApplicationNotes
```
