thepinkmile/Enigma-NG/design/Datasheets/Samtec-hsc-report_qts-qss-05mm.md

# Report Revision: 5/12/2005

## Source

- **Source PDF:** [Samtec-hsc-report_qts-qss-05mm.pdf](Samtec-hsc-report_qts-qss-05mm.pdf)
- **Generated Markdown:** `Samtec-hsc-report_qts-qss-05mm.md`
- **Page count:** 34
- **Conversion method:** automated local PDF text extraction with pypdf/pdfplumber

## PDF Metadata

| Field | Value |
| :--- | :--- |
| Title | Microsoft Word - hsc-report_QTS-QSS-05mm_05-12-2005_final.doc |
| Author | coreyk |
| Subject |  |
| Creator | PScript5.dll Version 5.2 |
| Producer | Acrobat Distiller 5.0.5 (Windows) |

## Extracted Technical Index

This markdown datasheet is meant to reduce the need to reopen the PDF during design work.
It preserves design-relevant extracted snippets first, followed by page-by-page text so the source content remains locally searchable.

### Part number and ordering information

- No reliable text snippet was automatically extracted for this category. Review the raw page text below.

### Pin, pad, and connection designations

- 520 Park East Blvd. 1-800-SAMTEC-9 (US & Canada) Fax: 812-948-5047 / New Albany IN 47151-1147 USA <SIG@samtec.com> / Report Revision: 5/12/2005 / ©Samtec, Inc. 2005   All Rights Reserved
- ©Samtec, Inc. 2005   All Rights Reserved / High Speed Characterization Report / QTS-025-01-L-D-A
- Description: / Parallel Board-to-Board, 0.635mm Pitch, 5mm (0.197”) Stack Height / High Speed Characterization Report / Series:  QSS / QTS
- 520 Park East Blvd. 1-800-SAMTEC-9 (US & Canada) Fax: 812-948-5047 / New Albany IN 47151-1147 USA <SIG@samtec.com> / Report Revision: 5/12/2005 / ©Samtec, Inc. 2005 Page:ii All Rights Reserved
- Characterization Details .................................................................................................. 5 / Differential and Single-Ended Data................................…
- Differential Application – Propagation Delay.............................................................. 19 / Differential Application – NEXT, “Worst Case” Configuration ......................…
- 520 Park East Blvd. 1-800-SAMTEC-9 (US & Canada) Fax: 812-948-5047 / New Albany IN 47151-1147 USA <SIG@samtec.com> / Report Revision: 5/12/2005 / ©Samtec, Inc. 2005 Page:iii All Rights Reserved
- Crosstalk ................................................................................................................ 30 / Appendix F – Glossary of Terms....................................…
- 520 Park East Blvd. 1-800-SAMTEC-9 (US & Canada) Fax: 812-948-5047 / New Albany IN 47151-1147 USA <SIG@samtec.com> / Report Revision: 5/12/2005 / ©Samtec, Inc. 2005 Page:1 All Rights Reserved
- Q Strip® .635mm (.025”) pitch interfaces (QSS/QTS Series) are available with up to 250 / I/Os and with standard board-to-board spacing of 5mm (0.197"), 8mm (0.315"), 11mm / (0.433"),  and 16mm (…
- QSS/QTS Series, / Parallel Board-to-Board, 0.635mm Pitch, 5mm (0.197")Stack Height / Signaling Speed Rating / Single-Ended: 9.0 GHz / 18 Gbps / Differential: 8.5 GHz / 17 Gbps
- The Speed Rating is based on the -3 dB insertion loss point of the connector system. / The -3 dB point can be used to estimate usable system bandwidth in a typical, two-level / signaling environ…
- To calculate the Speed Rating, the measured -3 dB point is rounded up to the nearest / half-GHz level.  The up-rounding corrects for a portion of the test board’s trace loss, / since trace losse…
- To calculate the Speed Rating, the measured -3 dB point is rounded up to the nearest / half-GHz level.  The up-rounding corrects for a portion of the test board’s trace loss, / since trace losse…
- GHz/ 16 Gbps.  A connector with a -3 dB point of 7.2 GHz would have a Speed Rating / of 7.5 GHz/ 15 Gbps. / High Speed Characterization Report / Series:  QSS / QTS
- 520 Park East Blvd. 1-800-SAMTEC-9 (US & Canada) Fax: 812-948-5047 / New Albany IN 47151-1147 USA <SIG@samtec.com> / Report Revision: 5/12/2005 / ©Samtec, Inc. 2005 Page:2 All Rights Reserved
- Xrow, GAAG to GQQG < -40dB to 8.08GHz / Connector System Insertion Loss / Single E nded & Differential Signal Response / Series QSS-01 / QTS-01 / -9
- single ended / differential / High Speed Characterization Report / Series:  QSS / QTS
- 520 Park East Blvd. 1-800-SAMTEC-9 (US & Canada) Fax: 812-948-5047 / New Albany IN 47151-1147 USA <SIG@samtec.com> / Report Revision: 5/12/2005 / ©Samtec, Inc. 2005 Page:3 All Rights Reserved
- Table 3 - Single-Ended Impedance (Ω) / Signal Risetime 30±5ps 50 ps 100 ps 250 ps 500 ps 750 ps 1 ns / Maximum / Impedance 59.5 53.2 52.1 51.8 51.3 51.1 50.9

### Specifications, ratings, and operating conditions

- Samtec connectors are most often designed for generic applications, and can be im- / plemented using various signal and ground pin assignments.  In high speed systems, / provisions must be made …
- ing.  For example, in a single-ended system, a pin-out of “SSSS”, or four adjacent single / ended signals, might be encountered, as opposed to the “GSG” and “GSSG” configura- / tions tested in t…
- Crosstalk or coupled noise data is provided for various signal configurations.  All meas- / urements are single disturber. Crosstalk is calculated as a ratio of the input line voltage / to the c…
- Crosstalk or coupled noise data is provided for various signal configurations.  All meas- / urements are single disturber. Crosstalk is calculated as a ratio of the input line voltage / to the c…
- the delay of the mated SUT. The measurement is a one-way propagation result.  Termi- / nation of the adjacent signal lines into the test systems characteristic impedance elimi- / nate alternate …

### Dimensions, package, and mechanical information

- Sampling Head.  For this series of tests, four of the eight TDR/Sampling Head capability / is used (Figure 4).  The 8720ES serves as a supporting test instrument for verification / or troublesho…
- The probe stations illuminated video microscopy system, microprobe positioners, and / 40GHz capable probes provide both the mechanical properties and electrical character- / istics for obtaining…

### Formulas, equations, and configurable calculations

- Characterization Details .................................................................................................. 5 / Differential and Single-Ended Data................................…
- Single-Ended Application – Impedance..................................................................... 14 / Single-Ended Application – Propagation Delay ......................................…
- Single-Ended Application – Propagation Delay ......................................................... 14 / Single-Ended Application – NEXT, “Worst Case” Configuration...........................…
- Single-Ended Application – NEXT, “Worst Case” Configuration................................ 15 / Single-Ended Application – FEXT, “Worst Case” Configuration ................................ 15 /…
- Single-Ended Application – FEXT, “Worst Case” Configuration ................................ 15 / Single-Ended Application – NEXT, “Best Case” Configuration .................................. 16…
- Differential Application – Impedance ......................................................................... 19 / Differential Application – Propagation Delay..................................…
- ©Samtec, Inc. 2005 Page:iii All Rights Reserved / Differential Application – FEXT, “Worst Case” Configuration..................................... 20 / Differential Application – NEXT, “Best Cas…
- Differential Application – FEXT, “Worst Case” Configuration..................................... 20 / Differential Application – NEXT, “Best Case” Configuration .................................…
- Differential Application – FEXT, “Worst Case” Configuration..................................... 20 / Differential Application – NEXT, “Best Case” Configuration .................................…
- signaling environment. / To calculate the Speed Rating, the measured -3 dB point is rounded up to the nearest / half-GHz level.  The up-rounding corrects for a portion of the test board’s trace …
- Table 1 - Single-Ended Connector System Performance / Test Parameter Configuration / Insertion Loss GSG -3dB @ 8.72GHz / Return Loss GSG < -5 dB to 8.72GHz
- Table 2 - Differential Connector System Bandwidth / Test Parameter Configuration / Insertion Loss GSSG -3dB @ 8.08GHz / Return Loss GSSG < -5dB to 8.08GHz
- Additionally, intermediate test signal connections can mask the connectors’ true per- / formance.   Such connection effects are minimized by using high performance test ca- / bles, adapters, and…
- narios. / Connector Signal to Ground Ratio / Samtec connectors are most often designed for generic applications, and can be im- / plemented using various signal and ground pin assignments.  In h…
- In general, the more pins dedicated to ground, the better electrical performance will be. / But dedicating pins to ground reduces signal density of a connector. So care must be / taken when choo…
- ©Samtec, Inc. 2005 Page:6 All Rights Reserved / For this connector, the following configurations were evaluated: / Single-Ended Impedance:
- urements. / Other configurations can be evaluated upon request. Please contact <sig@samtec.com> / for more information.
- In this report, propagation delay is defined as the signal propagation time through the / PCB connector pads and connector pair. It does not include PCB traces. Delay is / measured at 30 ± 5 pic…
- ©Samtec, Inc. 2005 Page:8 All Rights Reserved / Crosstalk or coupled noise data is provided for various signal configurations.  All meas- / urements are single disturber. Crosstalk is calculated…
- Crosstalk or coupled noise data is provided for various signal configurations.  All meas- / urements are single disturber. Crosstalk is calculated as a ratio of the input line voltage / to the c…

### Reference designs, applications, and examples

- Time Domain Data....................................................................................................... 7 / Appendix A – Frequency Domain Response Graphs.........................…
- Appendix A – Frequency Domain Response Graphs...................................................... 9 / Single-Ended Application – Insertion Loss ................................................…
- Single-Ended Application – Insertion Loss .................................................................. 9 / Single-Ended Application – Return Loss ..........................................…
- Single-Ended Application – Return Loss ..................................................................... 9 / Single-Ended Application – NEXT .................................................…
- Single-Ended Application – NEXT ............................................................................. 10 / Single-Ended Application – FEXT................................................…
- Single-Ended Application – FEXT.............................................................................. 10 / Differential Application – Insertion Loss......................................…
- Differential Application – Insertion Loss..................................................................... 11 / Differential Application – Return Loss........................................…
- Differential Application – Return Loss........................................................................ 11 / Differential Application – NEXT ..............................................…
- Differential Application – FEXT.................................................................................. 12 / Appendix B – Time Domain Response Graphs...................................…
- Appendix B – Time Domain Response Graphs............................................................. 13 / Single-Ended Application – Input Pulse.................................................…
- Single-Ended Application – Input Pulse..................................................................... 13 / Single-Ended Application – Impedance.............................................…
- Single-Ended Application – Impedance..................................................................... 14 / Single-Ended Application – Propagation Delay ......................................…
- Single-Ended Application – Propagation Delay ......................................................... 14 / Single-Ended Application – NEXT, “Worst Case” Configuration...........................…
- Single-Ended Application – NEXT, “Worst Case” Configuration................................ 15 / Single-Ended Application – FEXT, “Worst Case” Configuration ................................ 15 /…
- Single-Ended Application – FEXT, “Worst Case” Configuration ................................ 15 / Single-Ended Application – NEXT, “Best Case” Configuration .................................. 16…
- Single-Ended Application – NEXT, “Best Case” Configuration .................................. 16 / Single-Ended Application – FEXT, “Best Case” Configuration .................................. 1…
- Single-Ended Application – FEXT, “Best Case” Configuration .................................. 16 / Single-Ended Application – NEXT, Across Power/Ground Blade .............................. 17 / …
- Single-Ended Application – NEXT, Across Power/Ground Blade .............................. 17 / Single-Ended Application – FEXT, Across Power/Ground Blade .............................. 17 / Diff…
- Single-Ended Application – FEXT, Across Power/Ground Blade .............................. 17 / Differential Application – Input Pulse ............................................................…
- Differential Application – Input Pulse ......................................................................... 18 / Differential Application – Impedance .......................................…

## Page-by-Page Extracted Content

### Page 1

```text
Samtec Inc. WWW.SAMTEC.COM Phone: 812-944-6733
520 Park East Blvd. 1-800-SAMTEC-9 (US & Canada) Fax: 812-948-5047
New Albany IN 47151-1147 USA SIG@samtec.com
 Report Revision: 5/12/2005
©Samtec, Inc. 2005   All Rights Reserved

High Speed Characterization Report

QTS-025-01-L-D-A

Mated With

QSS-025-01-L-D-A

Description:
Parallel Board-to-Board, 0.635mm Pitch, 5mm (0.197”) Stack Height
```

### Page 2

```text
High Speed Characterization Report

Series:  QSS / QTS
Description: Parallel Board-to-Board, 0.635mm Pitch, 5mm (0.197”) Stack Height

Samtec Inc. WWW.SAMTEC.COM Phone: 812-944-6733
520 Park East Blvd. 1-800-SAMTEC-9 (US & Canada) Fax: 812-948-5047
New Albany IN 47151-1147 USA SIG@samtec.com
 Report Revision: 5/12/2005
©Samtec, Inc. 2005 Page:ii All Rights Reserved

Table of Contents

Connector Overview........................................................................................................ 1
Connector System Speed Rating .................................................................................... 1
Frequency Domain Data Summary ................................................................................. 2
Table 1 - Single-Ended Connector System Performance ............................................ 2
Table 2 - Differential Connector System Bandwidth .................................................... 2
Time Domain Data Summary .......................................................................................... 3
Table 3 - Single-Ended Impedance (Ω) ....................................................................... 3
Table 4 - Differential Impedance (Ω)............................................................................ 3
Table 5 - Single-Ended Crosstalk (%).......................................................................... 4
Table 6 - Differential Crosstalk (%).............................................................................. 4
Table 7 - Propagation Delay (Mated Connector) ......................................................... 4
Characterization Details .................................................................................................. 5
Differential and Single-Ended Data.............................................................................. 5
Connector Signal to Ground Ratio............................................................................... 5
Frequency Domain Data.............................................................................................. 7
Time Domain Data....................................................................................................... 7
Appendix A – Frequency Domain Response Graphs...................................................... 9
Single-Ended Application – Insertion Loss .................................................................. 9
Single-Ended Application – Return Loss ..................................................................... 9
Single-Ended Application – NEXT ............................................................................. 10
Single-Ended Application – FEXT.............................................................................. 10
Differential Application – Insertion Loss..................................................................... 11
Differential Application – Return Loss........................................................................ 11
Differential Application – NEXT ................................................................................. 12
Differential Application – FEXT.................................................................................. 12
Appendix B – Time Domain Response Graphs............................................................. 13
Single-Ended Application – Input Pulse..................................................................... 13
Single-Ended Application – Impedance..................................................................... 14
Single-Ended Application – Propagation Delay ......................................................... 14
Single-Ended Application – NEXT, “Worst Case” Configuration................................ 15
Single-Ended Application – FEXT, “Worst Case” Configuration ................................ 15
Single-Ended Application – NEXT, “Best Case” Configuration .................................. 16
Single-Ended Application – FEXT, “Best Case” Configuration .................................. 16
Single-Ended Application – NEXT, Across Power/Ground Blade .............................. 17
Single-Ended Application – FEXT, Across Power/Ground Blade .............................. 17
Differential Application – Input Pulse ......................................................................... 18
Differential Application – Impedance ......................................................................... 19
Differential Application – Propagation Delay.............................................................. 19
Differential Application – NEXT, “Worst Case” Configuration .................................... 20
```

### Page 3

```text
High Speed Characterization Report

Series:  QSS / QTS
Description: Parallel Board-to-Board, 0.635mm Pitch, 5mm (0.197”) Stack Height

Samtec Inc. WWW.SAMTEC.COM Phone: 812-944-6733
520 Park East Blvd. 1-800-SAMTEC-9 (US & Canada) Fax: 812-948-5047
New Albany IN 47151-1147 USA SIG@samtec.com
 Report Revision: 5/12/2005
©Samtec, Inc. 2005 Page:iii All Rights Reserved

Differential Application – FEXT, “Worst Case” Configuration..................................... 20
Differential Application – NEXT, “Best Case” Configuration ...................................... 21
Differential Application – FEXT, “Best Case” Configuration....................................... 21
Differential Application – NEXT, Across Power/Ground Blade .................................. 22
Differential Application – FEXT, Across Power/Ground Blade................................... 22
Appendix C – Product and Test System Descriptions................................................... 23
Product Description ................................................................................................... 23
Test System Description............................................................................................ 23
Appendix D – Test and Measurement Setup................................................................. 25
Test Instruments........................................................................................................ 26
Measurement Station Accessories ............................................................................ 26
Test Cables & Adapters............................................................................................. 26
Appendix E - Frequency and Time Domain Measurements.......................................... 27
Frequency (S-Parameter) Domain Procedures ......................................................... 27
CSA8000 Setup ..................................................................................................... 27
Insertion Loss......................................................................................................... 28
Return Loss............................................................................................................ 28
Near-End Crosstalk (NEXT)................................................................................... 29
Far-End Crosstalk (FEXT)...................................................................................... 29
Time Domain Procedures .......................................................................................... 30
Impedance ............................................................................................................. 30
Propagation Delay.................................................................................................. 30
Crosstalk ................................................................................................................ 30
Appendix F – Glossary of Terms................................................................................... 31
```

### Page 4

```text
High Speed Characterization Report

Series:  QSS / QTS
Description: Parallel Board-to-Board, 0.635mm Pitch, 5mm (0.197”) Stack Height

Samtec Inc. WWW.SAMTEC.COM Phone: 812-944-6733
520 Park East Blvd. 1-800-SAMTEC-9 (US & Canada) Fax: 812-948-5047
New Albany IN 47151-1147 USA SIG@samtec.com
 Report Revision: 5/12/2005
©Samtec, Inc. 2005 Page:1 All Rights Reserved

Connector Overview
Q Strip® .635mm (.025”) pitch interfaces (QSS/QTS Series) are available with up to 250
I/Os and with standard board-to-board spacing of 5mm (0.197"), 8mm (0.315"), 11mm
(0.433"),  and 16mm (0.630") between boards.   The data in this report is applicable
only to the 5mm (0.197") board-to-board stack height version.

Connector System Speed Rating

QSS/QTS Series,
Parallel Board-to-Board, 0.635mm Pitch, 5mm (0.197")Stack Height
Signaling Speed Rating
Single-Ended: 9.0 GHz / 18 Gbps
Differential: 8.5 GHz / 17 Gbps

The Speed Rating is based on the -3 dB insertion loss point of the connector system.
The -3 dB point can be used to estimate usable system bandwidth in a typical, two-level
signaling environment.

To calculate the Speed Rating, the measured -3 dB point is rounded up to the nearest
half-GHz level.  The up-rounding corrects for a portion of the test board’s trace loss,
since trace losses are included in the loss data in this report.  The resulting loss value is
then doubled to determine the approximate maximum data rate in Gigabits per second
(Gbps).

For example, a connector with a -3 dB point of 7.8 GHz would have a Speed Rating of 8
GHz/ 16 Gbps.  A connector with a -3 dB point of 7.2 GHz would have a Speed Rating
of 7.5 GHz/ 15 Gbps.
```

### Page 5

```text
High Speed Characterization Report

Series:  QSS / QTS
Description: Parallel Board-to-Board, 0.635mm Pitch, 5mm (0.197”) Stack Height

Samtec Inc. WWW.SAMTEC.COM Phone: 812-944-6733
520 Park East Blvd. 1-800-SAMTEC-9 (US & Canada) Fax: 812-948-5047
New Albany IN 47151-1147 USA SIG@samtec.com
 Report Revision: 5/12/2005
©Samtec, Inc. 2005 Page:2 All Rights Reserved

Frequency Domain Data Summary

Table 1 - Single-Ended Connector System Performance
Test Parameter Configuration
Insertion Loss GSG -3dB @ 8.72GHz
Return Loss GSG < -5 dB to 8.72GHz
GAQG < -8 dB to 8.72GHz
GAGQG < -22 dB to 8.72GHz Near-End Crosstalk
Xrow, GAG to GQG < -38 dB to 8.72GHz
GAQG < -25 dB to 8.72GHz
GAGQG < -25 dB to 8.72GHz Far-End Crosstalk
Xrow, GAG to GQG < -38 dB to 8.72GHz

Table 2 - Differential Connector System Bandwidth
Test Parameter Configuration
Insertion Loss GSSG -3dB @ 8.08GHz
Return Loss GSSG < -5dB to 8.08GHz
GAAQQG < -18dB to 8.08GHz
GAAGQQG < -35dB to 8.08GHz Near-End Crosstalk
Xrow, GAAG to GQQG < -40dB to 8.08GHz
GAAQQG                                           < -30dB to 8.08GHz
GAAGQQG                                        < -32dB to 8.08GHz Far-End Crosstalk
Xrow, GAAG to GQQG < -40dB to 8.08GHz
Connector System Insertion Loss
Single E nded & Differential Signal Response
Series QSS-01 / QTS-01
-9
-8
-7
-6
-5
-4
-3
-2
-1
0
1
0.0 1.0 2.0 3.0 4.0 5.0 6.0 7.0 8.0 9.0
Frequency (GHz)
Insertion Loss (dB)
single ended
differential
```

### Page 6

```text
High Speed Characterization Report

Series:  QSS / QTS
Description: Parallel Board-to-Board, 0.635mm Pitch, 5mm (0.197”) Stack Height

Samtec Inc. WWW.SAMTEC.COM Phone: 812-944-6733
520 Park East Blvd. 1-800-SAMTEC-9 (US & Canada) Fax: 812-948-5047
New Albany IN 47151-1147 USA SIG@samtec.com
 Report Revision: 5/12/2005
©Samtec, Inc. 2005 Page:3 All Rights Reserved

Time Domain Data Summary

Table 3 - Single-Ended Impedance (Ω)
Signal Risetime 30±5ps 50 ps 100 ps 250 ps 500 ps 750 ps 1 ns
Maximum
Impedance 59.5 53.2 52.1 51.8 51.3 51.1 50.9
Minimum
Impedance 39.0 44.0 47.0 48.3 49.3 49.7 49.7

 Single-Ended Application
Im pedan ce vs. Risetim e
30
35
40
45
50
55
60
65
70
75
35 50 1 0 0 2 50 50 0 750 100 0
Risetime (pSec)
maximum
minimum

Table 4 - Differential Impedance (Ω)
Signal Risetime 30±5ps 50 ps 100 ps 250 ps 500 ps 750 ps 1 ns
Maximum
Impedance 106.5 106.2 106.0 105.5 104.9 104.5 104.2
Minimum
Impedance 71.4 80.7 86.0 90.8 95.6 97.5 98.4

 Differential Application
Im pedan ce vs. Risetim e
50
60
70
80
90
10 0
110
12 0
35 50 1 0 0 250 50 0 750 100 0
Risetime (pSec)
maximum
minimum
```

### Page 7

```text
High Speed Characterization Report

Series:  QSS / QTS
Description: Parallel Board-to-Board, 0.635mm Pitch, 5mm (0.197”) Stack Height

Samtec Inc. WWW.SAMTEC.COM Phone: 812-944-6733
520 Park East Blvd. 1-800-SAMTEC-9 (US & Canada) Fax: 812-948-5047
New Albany IN 47151-1147 USA SIG@samtec.com
 Report Revision: 5/12/2005
©Samtec, Inc. 2005 Page:4 All Rights Reserved

Table 5 - Single-Ended Crosstalk (%)
Input
(tr)
  30±5ps  50 ps  100 ps  250 ps  500 ps  750 ps  1 ns
GAQG 14.7 13.2 11.1 6.3 3.6 2.5 2.0
GAGQG 3.2 2.4 1.9 1.1 < 1.0 < 1.0 < 1.0 NEXT
Xrowse < 1.0 < 1.0 < 1.0 < 1.0 < 1.0 < 1.0 < 1.0
GAQG 4.0 2.7 1.9 < 1. 0 < 1.0 < 1.0 < 1.0
GAGQG 2.8 2.0 1.2 < 1. 0 < 1.0 < 1.0 < 1.0 FEXT
Xrowse < 1.0 < 1.0 < 1.0 < 1.0 < 1.0 < 1.0 < 1.0
Table 6 - Differential Crosstalk (%)
Input
(tr)
  30±5ps  50 ps  100 ps  250 ps  500 ps  750 ps  1 ns
GAAQQG 4.3 4.0 3.4 2. 0 1.1 < 1.0 < 1.0
GAAGQQG < 1.0 < 1.0 < 1.0 < 1.0 < 1.0 < 1.0 < 1.0 NEXT
Xrowdiff < 1.0 < 1.0 < 1.0 < 1.0 < 1.0 < 1.0 < 1.0
GAAQQG 1.0 < 1.0 < 1.0 < 1.0 < 1.0 < 1.0 < 1.0
GAAGQQG < 1.0 < 1.0 < 1.0 < 1.0 < 1.0 < 1.0 < 1.0 FEXT
Xrowdiff < 1.0 < 1.0 < 1.0 < 1.0 < 1.0 < 1.0 < 1.0
Table 7 - Propagation Delay (Mated Connector)
Single-Ended 81.0 ps
Differential  84.0 ps
```

### Page 8

```text
High Speed Characterization Report

Series:  QSS / QTS
Description: Parallel Board-to-Board, 0.635mm Pitch, 5mm (0.197”) Stack Height

Samtec Inc. WWW.SAMTEC.COM Phone: 812-944-6733
520 Park East Blvd. 1-800-SAMTEC-9 (US & Canada) Fax: 812-948-5047
New Albany IN 47151-1147 USA SIG@samtec.com
 Report Revision: 5/12/2005
©Samtec, Inc. 2005 Page:5 All Rights Reserved

Characterization Details
This report presents data which characterizes the signal integrity response of a connec-
tor pair in a controlled printed circuit board (PCB) environment.  All efforts are made to
reveal typical best-case responses inherent to the system under test (SUT).

In this report, the SUT includes the test PCB from drive side probe tips to receive side
probe tips.  PCB effects are not removed or de-embedded from the test data. PCB de-
signs with impedance mismatch, large losses, skew, cross talk, or similar impairments
can have a significant impact on observed test data.  Therefore, great design effort is
put forth to limit these effects in the PCB utilized in these tests. Some board related ef-
fects, such as pad-to-ground capacitance and trace loss, are included in the data pre-
sented in this report. But other effects, such as via coupling or stub resonance, are not
evaluated here.  Such effects are addressed and characterized fully by the Samtec
Final Inch®
 products.

Additionally, intermediate test signal connections can mask the connectors’ true per-
formance.   Such connection effects are minimized by using high performance test ca-
bles, adapters, and microwave probes.  Where appropriate, calibration and de-
embedding routines are also used to reduce residual effects.

Differential and Single-Ended Data
Most Samtec connectors can be used successfully in both differential and single-ended
applications. However, electrical performance will differ depending on the signal drive
type.  In this report, data is presented for both differential and single-ended drive sce-
narios.

Connector Signal to Ground Ratio
Samtec connectors are most often designed for generic applications, and can be im-
plemented using various signal and ground pin assignments.  In high speed systems,
provisions must be made in the interconnect for signal return currents. Such paths are
often referred to as “ground”. In some connectors, a ground plane or blade, or an outer
shield is used as the signal return, while in others, connector pins are used as signal
returns.  Various combinations of signal pins, ground blades, and shields can also be
utilized.  Electrical performance can vary significantly depending upon the number and
location of ground pins.

In general, the more pins dedicated to ground, the better electrical performance will be.
But dedicating pins to ground reduces signal density of a connector. So care must be
taken when choosing signal/ground ratios in cost- or density-sensitive applications.
```

### Page 9

```text
High Speed Characterization Report

Series:  QSS / QTS
Description: Parallel Board-to-Board, 0.635mm Pitch, 5mm (0.197”) Stack Height

Samtec Inc. WWW.SAMTEC.COM Phone: 812-944-6733
520 Park East Blvd. 1-800-SAMTEC-9 (US & Canada) Fax: 812-948-5047
New Albany IN 47151-1147 USA SIG@samtec.com
 Report Revision: 5/12/2005
©Samtec, Inc. 2005 Page:6 All Rights Reserved

For this connector, the following configurations were evaluated:

Single-Ended Impedance:

• GSG (ground-signal-ground)

Single-Ended Crosstalk:
• Electrical “worst case”: GA QG (ground-active-quiet-ground)
• Electrical “best case”: GAGQG (ground-active-ground-quiet-ground)
• Across row: Xrow se  (from one row of terminals to the other row across the ground
blade)

Differential Impedance:

• GSSG (Ground-positive si gnal-negative signal-ground)

Differential Crosstalk:

• Electrical “worst case”: GAAQQG (g round-active-active-quiet-quiet-ground)
• Electrical “best case”: GAAGQQG (ground-active-active-ground-quiet-quiet-
ground)
• Across row:Xrow diff (from one row of terminals to the other row across the ground
blade)

In all cases in this report, the center ground blade of the connector was grounded to the
PCB. Only one single-ended signal or differential pair was driven for crosstalk meas-
urements.

Other configurations can be evaluated upon request. Please contact sig@samtec.com

for more information.

In a real system environment, active signals might be located at the outer edges of the
signal contacts of concern, as opposed to the ground signals utilized in laboratory test-
ing.  For example, in a single-ended system, a pin-out of “SSSS”, or four adjacent single
ended signals, might be encountered, as opposed to the “GSG” and “GSSG” configura-
tions tested in the laboratory.  Electrical characteristics in such applications could vary
slightly from laboratory results. But in most applications, performance can safely be con-
sidered equivalent.
```

### Page 10

```text
High Speed Characterization Report

Series:  QSS / QTS
Description: Parallel Board-to-Board, 0.635mm Pitch, 5mm (0.197”) Stack Height

Samtec Inc. WWW.SAMTEC.COM Phone: 812-944-6733
520 Park East Blvd. 1-800-SAMTEC-9 (US & Canada) Fax: 812-948-5047
New Albany IN 47151-1147 USA SIG@samtec.com
 Report Revision: 5/12/2005
©Samtec, Inc. 2005 Page:7 All Rights Reserved

Signal Edge Speed (Rise Time):
In pulse signaling applications, the perceived performance of an interconnect can vary
significantly depending on the edge rate or rise time of the exciting signal.  For this re-
port, the fastest rise time used was 30 +/-5 ps.  Generally, this should demonstrate
worst case performance.

In many systems, the signal edge rate will be significantly slower at the connector than
at the driver launch point. To estimate interconnect performance at other edge rates,
data is provided for several rise times between 30 ps and 1.0 ns.

For this report, rise times were measured at 10%-90% signal levels.

Frequency Domain Data
Frequency domain parameters are helpful in evaluating the connector system’s signal
loss and crosstalk characteristics across a range of sinusoidal frequencies.  In this re-
port, parameters presented in the frequency domain are insertion loss, return loss, and
near-end and far-end crosstalk. Other parameters or formats, such as VSWR or S-
parameters, may be available upon request. Please contact our Signal Integrity Group
at sig@samtec.com
 for more information.

Frequency performance characteristics for the SUT are generated from time domain
measurements using Fourier Transform calculations. Procedures and methods used in
generating the SUT’s frequency domain data are provided in the frequency domain test
procedures in Appendix E
 of this report.

Time Domain Data
Time Domain parameters indicate impedance mismatch versus length, signal propaga-
tion time, and crosstalk in a pulsed signal environment.  Time Domain data is provided
in Appendix E of this report. Parameters or formats not included in this report may be
available upon request. Please contact our Signal Integrity Group at sig@samtec.com
for more information.

Reference plane impedance is 50 ohms for single-ended measurements and 100 ohms
for differential measurements.   The fastest risetime signal exciting the SUT is 30 ± 5
picoseconds.

In this report, propagation delay is defined as the signal propagation time through the
PCB connector pads and connector pair. It does not include PCB traces. Delay is
measured at 30 ± 5 picoseconds signal risetime.  Delay is calculated as the difference
in time measured between the 50% amplitude levels of the input and output pulses.
```

### Page 11

```text
High Speed Characterization Report

Series:  QSS / QTS
Description: Parallel Board-to-Board, 0.635mm Pitch, 5mm (0.197”) Stack Height

Samtec Inc. WWW.SAMTEC.COM Phone: 812-944-6733
520 Park East Blvd. 1-800-SAMTEC-9 (US & Canada) Fax: 812-948-5047
New Albany IN 47151-1147 USA SIG@samtec.com
 Report Revision: 5/12/2005
©Samtec, Inc. 2005 Page:8 All Rights Reserved

Crosstalk or coupled noise data is provided for various signal configurations.  All meas-
urements are single disturber. Crosstalk is calculated as a ratio of the input line voltage
to the coupled line voltage.  The input line is sometimes described as the active or drive
line. The coupled line is sometimes described as the quiet or victim line.   Crosstalk ratio
is tabulated in this report as a percentage.  Measurements are made at both the near-
end and far-end of the SUT.

Data for other configurations may be available. Please contact our Signal Integrity
Group at sig@samtec.com
 for further information.

As a rule of thumb, 10% crosstalk levels are often used as a general first pass limit for
determining acceptable interconnect performance. But modern system crosstalk toler-
ance can vary greatly.  For advice on connector suitability for specific applications,
please contact our Signal Integrity Group at sig@samtec.com
.

Additional information concerning test conditions and procedures is located in the ap-
pendices of this report.  Further information may be obtained by contacting our Signal
Integrity Group at sig@samtec.com
.
```

### Page 12

```text
High Speed Characterization Report

Series:  QSS / QTS
Description: Parallel Board-to-Board, 0.635mm Pitch, 5mm (0.197”) Stack Height

Samtec Inc. WWW.SAMTEC.COM Phone: 812-944-6733
520 Park East Blvd. 1-800-SAMTEC-9 (US & Canada) Fax: 812-948-5047
New Albany IN 47151-1147 USA SIG@samtec.com
 Report Revision: 5/12/2005
©Samtec, Inc. 2005 Page:9 All Rights Reserved

Appendix A – Frequency Domain Response Graphs

Single-Ended Application – Insertion Loss
PCB /Connector Test System
Single E nded Application
Series QSS-01 / QTS-01
-9
-8
-7
-6
-5
-4
-3
-2
-1
0
1
0.0 1.0 2.0 3.0 4.0 5.0 6.0 7.0 8.0 9.0
Frequency (GHz)
Insertion Loss (dB)
single ended

Single-Ended Application – Return Loss
PCB /Connector Test System
Single E nded Application
Series QSS-01 / QTS-01
-90
-80
-70
-60
-50
-40
-30
-20
-10
0
0.0 1.0 2.0 3.0 4.0 5.0 6.0 7.0 8.0 9.0
Frequency (GHz)
Return Loss (dB)
single ended
```

### Page 13

```text
High Speed Characterization Report

Series:  QSS / QTS
Description: Parallel Board-to-Board, 0.635mm Pitch, 5mm (0.197”) Stack Height

Samtec Inc. WWW.SAMTEC.COM Phone: 812-944-6733
520 Park East Blvd. 1-800-SAMTEC-9 (US & Canada) Fax: 812-948-5047
New Albany IN 47151-1147 USA SIG@samtec.com
 Report Revision: 5/12/2005
©Samtec, Inc. 2005 Page:10 All Rights Reserved

Single-Ended Application – NEXT
PCB /Connector Test System
Single E nded Application
Series QSS-01 / QTS-01
-90.0
-80.0
-70.0
-60.0
-50.0
-40.0
-30.0
-20.0
-10.0
0.0
0.0 1.0 2.0 3.0 4.0 5.0 6.0 7.0 8.0 9.0
Frequency (GHz)
Near-End Crosstalk (dB)
w orst case
best case
across ground blade

Single-Ended Application – FEXT
PCB /Connector Test System
Single E nded Application
Series QSS-01 / QTS-01
-90.0
-80.0
-70.0
-60.0
-50.0
-40.0
-30.0
-20.0
-10.0
0.0
0.0 1.0 2.0 3.0 4.0 5.0 6.0 7.0 8.0 9.0
Frequency (GHz)
Far-End Crosstalk (dB)
w orst case
best case
across ground blade
```

### Page 14

```text
High Speed Characterization Report

Series:  QSS / QTS
Description: Parallel Board-to-Board, 0.635mm Pitch, 5mm (0.197”) Stack Height

Samtec Inc. WWW.SAMTEC.COM Phone: 812-944-6733
520 Park East Blvd. 1-800-SAMTEC-9 (US & Canada) Fax: 812-948-5047
New Albany IN 47151-1147 USA SIG@samtec.com
 Report Revision: 5/12/2005
©Samtec, Inc. 2005 Page:11 All Rights Reserved

Differential Application – Insertion Loss
PCB /Connector Test System
Differential Application
Series QSS-01 / QTS-01
-9
-8
-7
-6
-5
-4
-3
-2
-1
0
1
0.0 1.0 2.0 3.0 4.0 5.0 6.0 7.0 8.0 9.0
Frequency (GHz)
Insertion Loss (dB)
differential

Differential Application – Return Loss
PCB /Connector Test System
Differential Application
Series QSS-01 / QTS-01
-90
-80
-70
-60
-50
-40
-30
-20
-10
0
0.0 1.0 2.0 3.0 4.0 5.0 6.0 7.0 8.0 9.0
Frequency (GHz)
Return Loss (dB)
differential
```

### Page 15

```text
High Speed Characterization Report

Series:  QSS / QTS
Description: Parallel Board-to-Board, 0.635mm Pitch, 5mm (0.197”) Stack Height

Samtec Inc. WWW.SAMTEC.COM Phone: 812-944-6733
520 Park East Blvd. 1-800-SAMTEC-9 (US & Canada) Fax: 812-948-5047
New Albany IN 47151-1147 USA SIG@samtec.com
 Report Revision: 5/12/2005
©Samtec, Inc. 2005 Page:12 All Rights Reserved

Differential Application – NEXT
PCB /Connector Test System
Differential Application
Series QSS-01 / QTS-01
-90.0
-80.0
-70.0
-60.0
-50.0
-40.0
-30.0
-20.0
-10.0
0.0
0.0 1.0 2.0 3.0 4.0 5.0 6.0 7.0 8.0 9.0
Frequency (GHz)
Near-End Crosstalk (dB)
w orst case
best case
across ground blade

Differential Application – FEXT
PCB /Connector Test System
Differential Application
Series QSS-01 / QTS-01
-90.0
-80.0
-70.0
-60.0
-50.0
-40.0
-30.0
-20.0
-10.0
0.0
0.0 1.0 2.0 3.0 4.0 5.0 6.0 7.0 8.0 9.0
Frequency (GHz)
Far-End Crosstalk (dB)
w orst case
best case
across ground blade
```

### Page 16

```text
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
 Report Revision: 5/12/2005
©Samtec, Inc. 2005 Page:21 All Rights Reserved

Differential Application – NEXT, “Best Case” Configuration

Differential Application – FEXT, “Best Case” Configuration
```

### Page 25

```text
High Speed Characterization Report

Series:  QSS / QTS
Description: Parallel Board-to-Board, 0.635mm Pitch, 5mm (0.197”) Stack Height

Samtec Inc. WWW.SAMTEC.COM Phone: 812-944-6733
520 Park East Blvd. 1-800-SAMTEC-9 (US & Canada) Fax: 812-948-5047
New Albany IN 47151-1147 USA SIG@samtec.com
 Report Revision: 5/12/2005
©Samtec, Inc. 2005 Page:22 All Rights Reserved

Differential Application – NEXT, Across Power/Ground Blade

Differential Application – FEXT, Across Power/Ground Blade
```

### Page 26

```text
High Speed Characterization Report

Series:  QSS / QTS
Description: Parallel Board-to-Board, 0.635mm Pitch, 5mm (0.197”) Stack Height

Samtec Inc. WWW.SAMTEC.COM Phone: 812-944-6733
520 Park East Blvd. 1-800-SAMTEC-9 (US & Canada) Fax: 812-948-5047
New Albany IN 47151-1147 USA SIG@samtec.com
 Report Revision: 5/12/2005
©Samtec, Inc. 2005 Page:23 All Rights Reserved

Appendix C – Product and Test System Descriptions

Product Description
Product samples are the 5mm (0.197”) stack height Q Strip® High Speed QSS Series
sockets P/N QSS-025-01-X-D-A and P/N QSS-050-01-X-D-A. The mating QTS Series
headers are P/N QTS-025-01-X-D-A and P/N QTS-050-01-X-D-A respectively.

Each connector structure consists of 2 rows of 25 or 50 positions mounted into a plastic
housing with a surface mount design.   A conductive ground/power blade lies lengthwise
between terminal rows in the housing.  The contacts are evenly spaced at a.635mm
(.025”) pitch

Test System Description

The Test fixtures are composed of a 4-layer FR-4 material with 50Ω and100Ω signal
trace and pad configurations designed for the electrical characterization of Samtec hi-
speed connector products.  The pictured fixtures are specific to the QSS/QTS series
connector and are identified by Samtec P/N PCB-100245-TST-01 and P/N PCB-
100245-TST-02 (Figure 1)

Terminated onto P/N PCB-100245-TST-01 (Figure 2) are three QSS socket series con-
nectors.  The 25 position (Rt.) standard connector is setup for characterizing single
ended type signals (GSG).  The 50 position connector (Lt.) characterizes differential
type signals(GSSG).  The 16 pair connector pictured in the middle characterizes differ-
ential pairs with specified grounded terminals or in a totally open pin field fashion.
However, test results from this connector type are documented in a separate report
Figure 1 Mated PCB Test Fixture with Mounted Test Connectors
```

### Page 27

```text
High Speed Characterization Report

Series:  QSS / QTS
Description: Parallel Board-to-Board, 0.635mm Pitch, 5mm (0.197”) Stack Height

Samtec Inc. WWW.SAMTEC.COM Phone: 812-944-6733
520 Park East Blvd. 1-800-SAMTEC-9 (US & Canada) Fax: 812-948-5047
New Albany IN 47151-1147 USA SIG@samtec.com
 Report Revision: 5/12/2005
©Samtec, Inc. 2005 Page:24 All Rights Reserved

P/N PCB-100245-TST-02 accepts the QTS terminal connectors (Figure 3) and is de-
signed to mate with PCB-100245-TST-01.   Design differences are that signal traces
propagate through the board through via's to signal trace and probing pads located on
the opposite side from the connector.  QTS trace transitions can be observed on the top
board of Figure 1.

Test point signal paths coincide with each other upon mating and are marked accord-
ingly.   Single ended 25 position signal terminal paths are J4, J7, J8, J46 and J48. Dif-
ferential signal terminal paths for the 50 position connector are J4_6, J9_11, J10_12,
J78_80 and J82_84.  All signal paths are for monitoring through or adjacent signaling
test conditions with the exception of the J7 and J9_11.  These conditions are setup for
monitoring signal conditions across the terminal rows.

Both the single-ended and differential fixtures “J” number represents each terminal’s
designated position within the connector.  Signals can be launched or received from ei-
ther the socket or header side of the connector.  All data and waveforms presented in
the report are results from a socket side signal launch.
Figure 3 (Lt. to Rt.)  QTS-050-01-X-D-A, QTS-016-01-X-D-A, QTS-025-01-X-D-A
Figure 2 (Lt. to Rt.)  QSS-050-01-X-D-A, QSS-016-01-X-D-A, QSS-025-01-X-D-A
```

### Page 28

```text
High Speed Characterization Report

Series:  QSS / QTS
Description: Parallel Board-to-Board, 0.635mm Pitch, 5mm (0.197”) Stack Height

Samtec Inc. WWW.SAMTEC.COM Phone: 812-944-6733
520 Park East Blvd. 1-800-SAMTEC-9 (US & Canada) Fax: 812-948-5047
New Albany IN 47151-1147 USA SIG@samtec.com
 Report Revision: 5/12/2005
©Samtec, Inc. 2005 Page:25 All Rights Reserved

Appendix D – Test and Measurement Setup

Test instruments are a Tektronix CSA8000 Communication Signal Analyzer Mainframe
and the Agilent 8720ES Vector Network Analyzer.  Four bays of the CSA8000 are oc-
cupied with three Tektronix 80E04 TDR/Sampling Heads and one Tektronix 80E03
Sampling Head.  For this series of tests, four of the eight TDR/Sampling Head capability
is used (Figure 4).  The 8720ES serves as a supporting test instrument for verification
or troubleshooting results obtained from the TDA Systems IConnect Software package.
IConnect is a TDR based measurement software tool used in generating frequency do-
main related responses from high speed interconnects.

The probe stations illuminated video microscopy system, microprobe positioners, and
40GHz capable probes provide both the mechanical properties and electrical character-
istics for obtaining the precise signal launch and calibrations that are critical in obtaining
accurate high speed measurements. The 450 micron pitch probes are located to PCB
launch points with 25X to 175X magnification and XYZ fine positioning adjustments
available from both the probe table and micro-probe positioners.  Electrically the micro-
wave probes rate a < 1.0 dB insertion loss, a < 18 dB return loss, and an isolation of 38
dB to 40 GHz (Figure 4).   Test cables and interconnect adapters are high quality and
insure high-bandwidth and low parasitic measurements.

 Figure 4 – Probe Station Measurements Capability
```

### Page 29

```text
High Speed Characterization Report

Series:  QSS / QTS
Description: Parallel Board-to-Board, 0.635mm Pitch, 5mm (0.197”) Stack Height

Samtec Inc. WWW.SAMTEC.COM Phone: 812-944-6733
520 Park East Blvd. 1-800-SAMTEC-9 (US & Canada) Fax: 812-948-5047
New Albany IN 47151-1147 USA SIG@samtec.com
 Report Revision: 5/12/2005
©Samtec, Inc. 2005 Page:26 All Rights Reserved

Test Instruments
QTY Description
1 Tektronix CSA8000 Comm unication Signal Analyzer
3 Tektronix 80E04 Dual Channel  20 GHz TDR Sampling Module
1 Tektronix 80E03 Dual Channel  20 GHz  Sampling Module
1 Agilent 8720ES Vector Networ k Analyzer, 50 MHz to 20 GHz

Measurement Station Accessories
QTY Description
1 GigaTest Labs Model (GTL3030) Probe Station
4 GTL Micro-Probe Positioners
2 Picoprobe by GGB Ind. Model 40A  GSG (single ended applications)
2 Picoprobe by GGB Ind. Dual Model 40A  GSG-GSG (differential applications)
1 Keyence VH-5910 High Resolution Video Microscope
1 Keyence VH-W100 Fixed Magnification Lens 100 X
1 Keyence VH-Z25 Standard Zoom Lens 25X-175X
1 CS-9 GSG Picoprobe Cali bration Substrate (U9450.sq)
1 CS-11 GS-SG Picoprobe Cali bration Substrate (U11450.sq)

Test Cables & Adapters
QTY
 Description
4 Micro-Coax Cable Assembly 48” 3. 5mm Male to 3.5mm Female, 26.5 GHz
(IL = .33 dB@ 10 GHz)
2 Huber-Suhner Cable Assembly 36” SM A Female to SMA Female 26.5 GHz
(IL = .34 dB @ 10 GHz)
4 Pasternack Precision Adapters, 3. 5 mm Male to 2.9(K) Male,
Max.VSWR 1.25 @ 34GHz
Figure 5 – 40 GHz High Performance Microwave Probes
```

### Page 30

```text
High Speed Characterization Report

Series:  QSS / QTS
Description: Parallel Board-to-Board, 0.635mm Pitch, 5mm (0.197”) Stack Height

Samtec Inc. WWW.SAMTEC.COM Phone: 812-944-6733
520 Park East Blvd. 1-800-SAMTEC-9 (US & Canada) Fax: 812-948-5047
New Albany IN 47151-1147 USA SIG@samtec.com
 Report Revision: 5/12/2005
©Samtec, Inc. 2005 Page:27 All Rights Reserved

Appendix E - Frequency and Time Domain Measurements

It is important to note before gathering measurement data that TDA Systems IConnect
measurements and CSA8000 measurements are virtually the same measurements with
diverse formats.  This means that the operator, being extremely aware, can obtain SI
time and frequency characteristics in an almost simultaneous fashion.

Since IConnect setup procedures are specific to the frequency information sought, it is
mandatory that the sample preparation
 and CSA8000 functional setups be consistent
throughout the waveform gathering process.   If the operators test equipment permits
recall sequencing between the various test parameter setups, it insures IConnect func-
tional setups remain consistent with the TDR/TDT waveforms previously recorded.  Re-
lated time and frequency test parameter data recorded for this report were gathered si-
multaneously.

Frequency (S-Parameter) Domain Procedures
Frequency data extraction involves two steps that first measure the frequency related
time domain waveform followed by post-processing of the time domain waveforms into
loss and crosstalk response parameters versus frequency.  The first step utilizes the
Tektronix CSA8000 time based instrument to capture frequency related single-ended or
differential signal types propagating through an appropriately prepared SUT.  The sec-
ond step involves a correlation of the time based waveforms using the TDA Systems
IConnect software tool to post-process these waveforms into frequency response pa-
rameters. TDA Systems labels these frequency related waveform relationships as the
Step and DUT reference.  This report establishes the setup procedures for defining the
Step and DUT reference for frequency parameters of interest.  Once established, the
Step and DUT references are post-processed in IConnect’s S-parameter computations
window.

CSA8000 Setup

Listed below are the CSA 8000 functional menu setups used for single-ended and dif-
ferential frequency response extractions.  Both signal types utilize I-Connect software
tools to generate S-parameter upper and lower frequency boundaries along with the
step frequency.  These frequency boundaries are determined by a time domain instru-
ments functional settings such as window length, number of points and averaging capa-
bility. Once window length, number of points and averaging functions are set, maintain
the same instrument settings throughout the extraction process.
```

### Page 31

```text
High Speed Characterization Report

Series:  QSS / QTS
Description: Parallel Board-to-Board, 0.635mm Pitch, 5mm (0.197”) Stack Height

Samtec Inc. WWW.SAMTEC.COM Phone: 812-944-6733
520 Park East Blvd. 1-800-SAMTEC-9 (US & Canada) Fax: 812-948-5047
New Albany IN 47151-1147 USA SIG@samtec.com
 Report Revision: 5/12/2005
©Samtec, Inc. 2005 Page:28 All Rights Reserved

 Single-Ended Signal  Differential Signal
Vertical Scale: 100 mV/ Div:  100 mV/ Div:
Offset: Default / Scroll Default / Scroll
Horizontal Scale: 1nSec/ Div = 20 MHz step
frequency
1nSec/ Div = 20 MHz step
frequency
Max. Record Length: 4000 = Min. Resolution 4000 = Min. Resolution
Averages: ≥ 128 ≥ 128

Insertion Loss

SUT Preparation – Use J8 or J4 signal paths to establish single ended waveforms and
J10_12 or J4_6 signal paths to establish differential waveforms (Figure 1) Adjacent
transmission paths are terminated 50Ω to GND single-ended or 100Ω differential.

Step Reference - Establish this waveform by making a TDT transmission measurement
that includes all cables, adapters, and probes connected in the test systems transmis-
sion path.  The transmission path is completed by inserting a negligible length of trans-
mission standard (Figure 5) between the microwave probes.

DUT Reference - Establish this waveform by making an active TDT transmission meas-
urement that includes all cables, adapters, and probes connected in the test systems
transmission path.  Manually insert the SUT between the probes in place of the trans-
mission standard (Figure 5).

Return Loss

SUT Preparation – Use J8 or J4 signal paths to establish single ended waveforms and
J10_12 or J4_6 signal paths to establish differential waveforms (Figure 1) Adjacent
transmission paths are terminated 50Ω to GND single-ended or 100Ω differential.

Step Reference - Establish the waveform by making an active TDR reflection measure-
ment that includes all cables, adapters, and probes connected in the test systems elec-
trical path to the open standard.

DUT Reference - Establish the waveform by making a TDT (matched) transmission
measurement that includes all cables, adapters, and probes connected in the test sys-
tems transmission path (Figure 5).  Cables and adapters located on the far-end of the
inserted SUT providing a resistive load impedance that matches the test system input
impedance condition. (i.e.; 50Ω single-ended or 100Ω differential)
```

### Page 32

```text
High Speed Characterization Report

Series:  QSS / QTS
Description: Parallel Board-to-Board, 0.635mm Pitch, 5mm (0.197”) Stack Height

Samtec Inc. WWW.SAMTEC.COM Phone: 812-944-6733
520 Park East Blvd. 1-800-SAMTEC-9 (US & Canada) Fax: 812-948-5047
New Albany IN 47151-1147 USA SIG@samtec.com
 Report Revision: 5/12/2005
©Samtec, Inc. 2005 Page:29 All Rights Reserved

Near-End Crosstalk (NEXT)
SUT Preparation - Establish 50Ω to GND terminations at J4, J7, J8, J46, & J48 on the
PCB (-02) terminal fixture.   Establish 50Ω to GND terminations or 100Ω across signal
paths at J4_6, J9_11 , J10_12, J78_80 & J82_84 on the PCB (-02) terminal fixture (Fig-
ure 3).

Step Reference - Establish this waveform by making an active measurement that in-
cludes all cables, adapters, and probes connected in the test systems electrical path to
the open standard.

DUT Reference - Establish these waveforms by driving an active signal line (i.e.; J8)
and recording the TDR coupled energy at the adjacent near-end (i.e.; J4).  Maintain
same procedures to establish the waveforms for worse case, best case, and across row
(xrow) crosstalk conditions.  These conditions are present for both single-ended and dif-
ferential configurations.

Far-End Crosstalk (FEXT)

SUT Preparation - Establish 50Ω to GND terminations at J4, J7, & J46 on the PCB (-01)
socket fixture (Figure 2) and at J8 & J48 of the PCB (-02) terminal fixture (Figure 3).
Differential paths are terminated 50Ω to GND or 100Ω across signal paths at J4_6,
J9_11, & J78_80 on the PCB (-01) socket fixture (Figure 2) and at J1012 & J82_84 of the
PCB (-02) terminal fixture (Figure 3)

Step Reference - Establish this waveform by making a TDT transmission measurement
that includes all cables, adapters, and probes connected in the test systems transmis-
sion path.  The transmission path is completed by inserting a negligible length of trans-
mission standard (Figure 5) between the microwave probes.

DUT Reference - Establish these waveforms by driving an active signal line (i.e.; J8)
and recording the TDR coupled energy at the adjacent near-end (i.e., J4).  Maintain
same procedures to establish the waveforms for worse case, best case, and across row
(xrow) crosstalk conditions.  These conditions are present for both single-ended and dif-
ferential configurations.
```

### Page 33

```text
High Speed Characterization Report

Series:  QSS / QTS
Description: Parallel Board-to-Board, 0.635mm Pitch, 5mm (0.197”) Stack Height

Samtec Inc. WWW.SAMTEC.COM Phone: 812-944-6733
520 Park East Blvd. 1-800-SAMTEC-9 (US & Canada) Fax: 812-948-5047
New Albany IN 47151-1147 USA SIG@samtec.com
 Report Revision: 5/12/2005
©Samtec, Inc. 2005 Page:30 All Rights Reserved

Time Domain Procedures
Measurements involving digital type pulses are performed utilizing either Time Domain
Reflectometer (TDR) or Time Domain Transmission (TDT) methods. For this series of
tests, TDR methods are employed for the impedance and propagation delay measure-
ments. Crosstalk measurements utilize TDT methods. The Tektronix 80E04 TDR/ Sam-
pling Head provide both the signaling type and sampling capability necessary to accurately
and fully characterize the SUT.

Impedance

The signal line(s) of the SUT’s signal configuration is energized with a TDR pulse.  The
far-end of the energized signal line is terminated in the test systems characteristic im-
pedance (e.g.; 50Ω or 100Ω terminations).  By terminating the adjacent signal lines in
the test systems characteristic impedance, the effects on the resultant impedance
shape of the waveform is limited.

Propagation Delay

This connector series uses the fastest edge rate (30ps) of the TDR impedance wave-
form to measure propagation delay.  .  Differential or single ended signal delay is the
measured difference of propagation between the known signal trace length delay and
the delay of the mated SUT. The measurement is a one-way propagation result.  Termi-
nation of the adjacent signal lines into the test systems characteristic impedance elimi-
nate alternate current paths providing for better measurement accuracy.

Crosstalk
An active pulsed waveform is transmitted through a selected SUT signal line.  The adja-
cent quiet signal lines are monitored for the coupled energy at the near-end and far-end.
Active and quiet lines not being monitored are terminated in the test systems character-
istic impedance. Signal lines adjacent to the quiet lines remain terminated on both ends
throughout the test sequence.   Failing to terminate the active near or far end, quiet
lines, or in some cases, signal lines adjacent to the quiet line may have an effect on
amplitude and shape of the coupled energy.
```

### Page 34

```text
High Speed Characterization Report

Series:  QSS / QTS
Description: Parallel Board-to-Board, 0.635mm Pitch, 5mm (0.197”) Stack Height

Samtec Inc. WWW.SAMTEC.COM Phone: 812-944-6733
520 Park East Blvd. 1-800-SAMTEC-9 (US & Canada) Fax: 812-948-5047
New Albany IN 47151-1147 USA SIG@samtec.com
 Report Revision: 5/12/2005
©Samtec, Inc. 2005 Page:31 All Rights Reserved

Appendix F – Glossary of Terms

BC – Best Case crosstalk configuration
DP – Differential Pair signal configuration
DUT – Device under test; TDA IConnect reference waveform
FEXT – Far-End Crosstalk
GSG – Ground–Signal-Ground; geometric configuration
NEXT – Near-End Crosstalk
PCB – Printed Circuit Board
SE – Single-Ended
SI – Signal Integrity
SUT – System under test
TDR – Time Domain Reflectometry
TDT – Time Domain Transmission
WC – Worse Case crosstalk configuration
Xrowse – Cross ground/ power bar crosstalk, single-ended signal
Xrowdiff – Cross ground/ power bar crosstalk, differential signal
Z – Impedance (expressed in ohms)
```
