thepinkmile/Enigma-NG/design/Datasheets/Samtec-qss-qts-product-specification.md

# Series: QSS / QTS 0,635mm High Speed Socket / Terminal Strips

## Source

- **Source PDF:** [Samtec-qss-qts-product-specification.pdf](Samtec-qss-qts-product-specification.pdf)
- **Generated Markdown:** `Samtec-qss-qts-product-specification.md`
- **Page count:** 9
- **Conversion method:** automated local PDF text extraction with pypdf/pdfplumber

## PDF Metadata

| Field | Value |
| :--- | :--- |
| Title | «Picture_Description» is depicted |
| Author | John Tozier |
| Subject |  |
| Creator | Microsoft® Word for Microsoft 365 |
| Producer | Microsoft® Word for Microsoft 365 |

## Extracted Technical Index

This markdown datasheet is meant to reduce the need to reopen the PDF during design work.
It preserves design-relevant extracted snippets first, followed by page-by-page text so the source content remains locally searchable.

### Part number and ordering information

- Other configurations available for: / Co-planar and perpendicular board-to-board applications / Rugged features / end options / Packaging options
- Co-planar and perpendicular board-to-board applications / Rugged features / end options / Packaging options / See <www.samtec.com> for more information.

### Pin, pad, and connection designations

- Product Specification / Series:  QSS / QTS 0,635mm High Speed Socket / Terminal Strips / Revision: K Date: February 20, 2025 © 2012 Samtec, Inc.
- QSS Series – Socket, Vertical Orientation / QTS Series – Terminal, Vertical Orientation / Other configurations available for:
- 1.1 This specification covers performance, testing and quality requirements for Samtec QSS/QTS Series 0,635 mm / High Speed Socket/Terminal Strips.  These socket and terminal strips are availabl…
- 2.0 DETAILED INFORMATION / 2.1 Product prints, footprints, catalog pages, test reports and other specific, detailed information can be found at / <www.samtec.com?QSS> and <www.samtec.com?QTS.>
- 6.2 System Impedance: 50 ohm for single-ended and 100 ohm for differential pair / Stack Height Single-Ended Signaling Differential Pair Signaling / 5mm 9.00 GHz 8.50 GHz / 11mm 6.00 GHz 5.50 GHz
- Rework Methods / 7.10 Hardware: Board-to-board standoffs are recommended to provide a robust mechanical connection. Samtec offers / several different types, which can be found here: Samtec Stand…
- 9.0 ADDITIONAL RESOURCES / 9.1 For additional mechanical testing or product information, contact our Customer Engineering Support Group at / <CES@samtec.com>
- <CES@samtec.com> / 9.2 For additional information on high speed performance testing, contact our Signal Integrity Group at / <SIG@samtec.com>
- This Product Specification Sheet (“PSS”) is a brief summary of information related to the Product identified.  As a summary, it should / only be used for the limited purpose  of considering the …

### Specifications, ratings, and operating conditions

- Product Specification / Series:  QSS / QTS 0,635mm High Speed Socket / Terminal Strips
- See <www.samtec.com> for more information. / Product Specification / Series:  QSS / QTS 0,635mm High Speed Socket / Terminal Strips
- 1.0 SCOPE / 1.1 This specification covers performance, testing and quality requirements for Samtec QSS/QTS Series 0,635 mm / High Speed Socket/Terminal Strips.  These socket and terminal strips …
- High Speed Socket/Terminal Strips.  These socket and terminal strips are available in vertical, edge mount and right / angle configurations for parallel, perpendicular and co-planar board-to-boa…
- 3.0 TESTING / 3.1 Current Rating: 1.3A / 3.2 Voltage Rating: 275 VAC / 3.3 Operating Temperature Range: -55°C to +125°C
- 3.1 Current Rating: 1.3A / 3.2 Voltage Rating: 275 VAC / 3.3 Operating Temperature Range: -55°C to +125°C / 3.4 Electrical:
- ITEM TEST CONDITION REQUIREMENT STATUS / Withstanding Voltage EIA-364-20 (No Flashover, / Sparkover, or Breakdown) 825 VAC Pass / Insulation Resistance EIA-364-21 (5000 MΩ
- Normal Force EIA-364-04 30 grams minimum for gold / interface Pass / Product Specification / Series:  QSS / QTS 0,635mm High Speed Socket / Terminal Strips
- ITEM TEST CONDITION REQUIREMENT STATUS / Thermal Shock / EIA-364-32 / Thermal Cycles: 100 (30 minute dwell)
- Thermal Shock / EIA-364-32 / Thermal Cycles: 100 (30 minute dwell) / Hot Temp: 85°C / Cold Temp: -55°C
- IR: >15,000 MΩ / Pass / Thermal Aging / (Temp Life) / EIA-364-17
- Exposure / LLCR:  Δ 15 mΩ Pass / Product Specification / Series:  QSS / QTS 0,635mm High Speed Socket / Terminal Strips
- 11mm 6.00 GHz 5.50 GHz / 16mm 5.00 GHz 5.00 Ghz / Product Specification / Series:  QSS / QTS 0,635mm High Speed Socket / Terminal Strips
- 7.1.2 Allowable final linear misalignment / Product Specification / Series:  QSS / QTS 0,635mm High Speed Socket / Terminal Strips
- 7.3 Multiple Connector Applications: Not recommended for applications in which multiple connectors are mated to a single / daughtercard. For more information, please contact <IPG@samtec.com>. / …
- These guidelines should not be considered design requirements for all applications. / Samtec recommends testing interconnects on your boards in your process to guarantee optimum results. / Produ…
- -05 .748 [19.00] XXXX-1915 / -06 .866 [22.00] XXXX-2015 / Product Specification / Series:  QSS / QTS 0,635mm High Speed Socket / Terminal Strips
- Compliance Group at <PEC@samtec.com> / USE OF PRODUCT SPECIFICATION SHEET / This Product Specification Sheet (“PSS”) is a brief summary of information related to the Product identified.  As a su…
- USE OF PRODUCT SPECIFICATION SHEET / This Product Specification Sheet (“PSS”) is a brief summary of information related to the Product identified.  As a summary, it should / only be used for the…

### Dimensions, package, and mechanical information

- 2.0 DETAILED INFORMATION / 2.1 Product prints, footprints, catalog pages, test reports and other specific, detailed information can be found at / <www.samtec.com?QSS> and <www.samtec.com?QTS.>
- (Samtec defined)/ No damage Pass / 3.5 Mechanical: / ITEM TEST CONDITION REQUIREMENT STATUS
- 1.0 microsecond / Pass / Mechanical Shock / EIA-364-27  100 G, 6 / milliseconds, sawtooth wave,
- Rework Methods / 7.10 Hardware: Board-to-board standoffs are recommended to provide a robust mechanical connection. Samtec offers / several different types, which can be found here: Samtec Stand…
- 9.0 ADDITIONAL RESOURCES / 9.1 For additional mechanical testing or product information, contact our Customer Engineering Support Group at / <CES@samtec.com>
- This Product Specification Sheet (“PSS”) is a brief summary of information related to the Product identified.  As a summary, it should / only be used for the limited purpose  of considering the …

### Formulas, equations, and configurable calculations

- QTS Series – Terminal, Vertical Orientation / Other configurations available for: / Co-planar and perpendicular board-to-board applications / Rugged features / end options
- 1.1 This specification covers performance, testing and quality requirements for Samtec QSS/QTS Series 0,635 mm / High Speed Socket/Terminal Strips.  These socket and terminal strips are availabl…
- High Speed Socket/Terminal Strips.  These socket and terminal strips are available in vertical, edge mount and right / angle configurations for parallel, perpendicular and co-planar board-to-boa…
- Durability EIA-364-09C 100 cycles (10µ" Au), 500 cycles / (30µ" Au) Pass / Random Vibration / EIA-364-28 Condition V, Letter B / 7.56 G 'RMS', 50 to 2000 Hz, 2
- Test Temp:  25°C to 65°C / Relative Humidity: 90 to 95% / Test Duration: 240 hours / Visual Inspection:  No Damage / LLCR: Δ 15 mΩ
- EIA-364-36 / Gas Exposure:  Nitric Acid Vapor / Duration:  60 min. / Drying Temp.:  50°C +/- 3°C / Measurements:  Within 1 hour of
- 8.0 DIRECTION OF BOARD TRAVEL THROUGH REFLOW OVEN / 8.1  To minimize the potential for connector warpage, Samtec recommends the layout configuration shown below left. / This allows the connector…

### Reference designs, applications, and examples

- Other configurations available for: / Co-planar and perpendicular board-to-board applications / Rugged features / end options / Packaging options
- 1.1 This specification covers performance, testing and quality requirements for Samtec QSS/QTS Series 0,635 mm / High Speed Socket/Terminal Strips.  These socket and terminal strips are availabl…
- 7.2.2 Allowable final angular misalignment / 7.3 Multiple Connector Applications: Not recommended for applications in which multiple connectors are mated to a single / daughtercard. For more inf…
- Revision: K Date: February 20, 2025 © 2012 Samtec, Inc. / Page 7 / 7.4 Due to variances in equipment, solder pastes and applications (board design, component density, etc.) , Samtec / does not s…
- 7.4.1 / These guidelines should not be considered design requirements for all applications. / Samtec recommends testing interconnects on your boards in your process to guarantee optimum results.…

## Page-by-Page Extracted Content

### Page 1

```text
Product Specification

Series:  QSS / QTS 0,635mm High Speed Socket / Terminal Strips

Revision: K Date: February 20, 2025 © 2012 Samtec, Inc.
 Page 1
QSS Series – Socket, Vertical Orientation

QTS Series – Terminal, Vertical Orientation

Other configurations available for:
Co-planar and perpendicular board-to-board applications
Rugged features / end options
Packaging options

See www.samtec.com for more information.
```

### Page 2

```text
Product Specification

Series:  QSS / QTS 0,635mm High Speed Socket / Terminal Strips

Revision: K Date: February 20, 2025 © 2012 Samtec, Inc.
 Page 2

1.0 SCOPE

1.1 This specification covers performance, testing and quality requirements for Samtec QSS/QTS Series 0,635 mm
High Speed Socket/Terminal Strips.  These socket and terminal strips are available in vertical, edge mount and right
angle configurations for parallel, perpendicular and co-planar board-to-board applications.  All information
contained in this specification is for a 5,00 mm mated height vertical configuration unless otherwise noted.

2.0 DETAILED INFORMATION

2.1 Product prints, footprints, catalog pages, test reports and other specific, detailed information can be found at
www.samtec.com?QSS and www.samtec.com?QTS.

3.0 TESTING

3.1 Current Rating: 1.3A
3.2 Voltage Rating: 275 VAC
3.3 Operating Temperature Range: -55°C to +125°C
3.4 Electrical:

ITEM TEST CONDITION REQUIREMENT STATUS
Withstanding Voltage EIA-364-20 (No Flashover,
Sparkover, or Breakdown) 825 VAC Pass
Insulation Resistance EIA-364-21 (5000 MΩ
minimum) 15,000 MΩ Pass
Contact Resistance
(LLCR) EIA-364-23 Δ 15 mΩ maximum
(Samtec defined)/ No damage Pass

3.5 Mechanical:

ITEM TEST CONDITION REQUIREMENT STATUS
Durability EIA-364-09C 100 cycles (10µ" Au), 500 cycles
(30µ" Au) Pass
Random Vibration
EIA-364-28 Condition V, Letter B
7.56 G 'RMS', 50 to 2000 Hz, 2
hours per axis, 3 axis total , PSD
0.04
Visual Inspection: No Damage
LLCR: Δ 15 mΩ maximum
Event Detection: No interruption >
1.0 microsecond
Pass
Mechanical Shock
EIA-364-27  100 G, 6
milliseconds, sawtooth wave,
11.3 fps, 3 shocks/direction, 3
axis (18 total shocks)
Visual Inspection: No Damage
LLCR: Δ 15 mΩ maximum
Event Detection: No interruption >
1.0 microsecond
Pass
Normal Force EIA-364-04 30 grams minimum for gold
interface Pass
```

### Page 3

```text
Product Specification

Series:  QSS / QTS 0,635mm High Speed Socket / Terminal Strips

Revision: K Date: February 20, 2025 © 2012 Samtec, Inc.
 Page 3

3.6 Environmental:

ITEM TEST CONDITION REQUIREMENT STATUS
Thermal Shock
EIA-364-32
Thermal Cycles: 100 (30 minute dwell)
Hot Temp: 85°C
Cold Temp: -55°C
Hot/Cold Transition:  Immediate
Visual Inspection:  No Damage
LLCR: Δ 15 mΩ
DWV: 825 VAC
IR: >15,000 MΩ
Pass
Thermal Aging
(Temp Life)
EIA-364-17
Test Condition 4 @ 105°C Condition B
for 250 hours
Visual Inspection:  No Damage
LLCR: Δ 15 mΩ
DWV: 825 VAC
IR: >15,000 MΩ
Pass
Cyclic Humidity
EIA-364-31
Test Temp:  25°C to 65°C
Relative Humidity: 90 to 95%
Test Duration: 240 hours
Visual Inspection:  No Damage
LLCR: Δ 15 mΩ
DWV: 825 VAC
IR: >15,000 MΩ
Pass
Gas Tight
EIA-364-36
Gas Exposure:  Nitric Acid Vapor
Duration:  60 min.
Drying Temp.:  50°C +/- 3°C
Measurements:  Within 1 hour of
Exposure
LLCR:  Δ 15 mΩ Pass
```

### Page 4

```text
Product Specification

Series:  QSS / QTS 0,635mm High Speed Socket / Terminal Strips

Revision: K Date: February 20, 2025 © 2012 Samtec, Inc.
 Page 4

4.0 MATED SYSTEM

4.1 Mated Views:
Mated view information can be found at link below:
             https://suddendocs.samtec.com/prints/qss - qts mated document-mkt.pdf

5.0 POLARIZING FEATURES

6.0 HIGH SPEED PERFORMANCE

6.1 Based on a 3 dB insertion loss
6.2 System Impedance: 50 ohm for single-ended and 100 ohm for differential pair

Stack Height Single-Ended Signaling Differential Pair Signaling
5mm 9.00 GHz 8.50 GHz
11mm 6.00 GHz 5.50 GHz
16mm 5.00 GHz 5.00 Ghz
```

### Page 5

```text
Product Specification

Series:  QSS / QTS 0,635mm High Speed Socket / Terminal Strips

Revision: K Date: February 20, 2025 © 2012 Samtec, Inc.
 Page 5
7.0 PROCESSING RECOMMENDATIONS

7.1 Mating Alignment Requirements:

7.1.1 Allowable initial linear misalignment

7.1.2 Allowable final linear misalignment
```

### Page 6

```text
Product Specification

Series:  QSS / QTS 0,635mm High Speed Socket / Terminal Strips

Revision: K Date: February 20, 2025 © 2012 Samtec, Inc.
 Page 6

7.2 Mating Angle Requirements:

7.2.1 Allowable initial angular misalignment

7.2.2 Allowable final angular misalignment

7.3 Multiple Connector Applications: Not recommended for applications in which multiple connectors are mated to a single
daughtercard. For more information, please contact IPG@samtec.com.
```

### Page 7

```text
Product Specification

Series:  QSS / QTS 0,635mm High Speed Socket / Terminal Strips

Revision: K Date: February 20, 2025 © 2012 Samtec, Inc.
 Page 7
7.4 Due to variances in equipment, solder pastes and applications (board design, component density, etc.) , Samtec
does not specify a recommended reflow profile for our connectors. The processing parameters provided by the
solder paste manufacturer should be employed and can usually be found on their website.

All of Samtec’s surface mount components are lead free reflow compatible and compliant with the profile
parameters detailed in IPC/JEDEC J-STD-020 which requires that components be capable of withstanding a peak
temperature of 260°C as well as 30 seconds above 255°C.

Samtec Recommended Temperature Profile Ranges (SMT)

Sn-Pb Eutectic Assembly

Preheat/Soak
(100°C-150°C)
Max Ramp Up
Rate
Reflow Time
(above 183°C)
Peak
Temp
Time within 5°C
of 235°C
Max Ramp
Down Rate
Time 25°C to
Peak Temp
60-120 sec. 3°C/s max. 40-150 sec. 235°C 20 sec. max. 6°C/s max. 6 min. max.

Pb-Free Assembly

Preheat/Soak
(150°C-200°C)
Max Ramp Up
Rate
Reflow Time
(above 217°C)
Peak
Temp
Time within 5°C
of 260°C
Max Ramp
Down Rate
Time 25°C to
Peak Temp
60-120 sec. 3°C/s max. 40-150 sec. 260°C 30 sec. max. 6°C/s max. 8 min. max.

7.4.1

These guidelines should not be considered design requirements for all applications.
Samtec recommends testing interconnects on your boards in your process to guarantee optimum results.
```

### Page 8

```text
Product Specification

Series:  QSS / QTS 0,635mm High Speed Socket / Terminal Strips

Revision: K Date: February 20, 2025 © 2012 Samtec, Inc.
 Page 8
7.5 Maximum Reflow Passes: The parts can withstand 3 reflow passes at a maximum component temperature of
260°C.

7.6 Stencil Thickness: The recommended stencil thickness is .006” (.15mm).

7.7 Placement: Machine placement of the parts is recommended.

7.8 Reflow Environment:  Samtec recommends the use of a low level oxygen environment (typically achieved
through Nitrogen gas infusion) in the reflow process to improve solderability.

7.9 Rework Guidelines:  Samtec recommends following these rework guidelines as needed: QXX/BXX Connector
Rework Methods

7.10 Hardware: Board-to-board standoffs are recommended to provide a robust mechanical connection. Samtec offers
several different types, which can be found here: Samtec Standoff Offerings.

QSS LEAD STYLE
-01
QTS LEAD STYLE Nominal Connector Stack Height
"A" in [mm] Standoff
-01 .197 [5.00] XXXX-0515
-02 .315 [8.00] XXXX-0815
-03 .433 [11.00] XXXX-1115
-04 .630 [16.00] XXXX-1615
-05 .748 [19.00] XXXX-1915
-06 .866 [22.00] XXXX-2015
```

### Page 9

```text
Product Specification

Series:  QSS / QTS 0,635mm High Speed Socket / Terminal Strips

Revision: K Date: February 20, 2025 © 2012 Samtec, Inc.
 Page 9
7.11 Cleaning: Samtec, Inc. has verified that our connectors may be cleaned in accordance with the solvents and
conditions designated in the EIA-364-11 standard.

8.0 DIRECTION OF BOARD TRAVEL THROUGH REFLOW OVEN

8.1  To minimize the potential for connector warpage, Samtec recommends the layout configuration shown below left.
This allows the connectors to heat more evenly.

9.0 ADDITIONAL RESOURCES

9.1 For additional mechanical testing or product information, contact our Customer Engineering Support Group at
CES@samtec.com

9.2 For additional information on high speed performance testing, contact our Signal Integrity Group at
SIG@samtec.com

9.3 For additional processing information, contact our Interconnect Processing Group at IPG@samtec.com.

9.4 For RoHS, REACH or other environmental compliance information, contact our Product Environmental
Compliance Group at PEC@samtec.com

USE OF PRODUCT SPECIFICATION SHEET

This Product Specification Sheet (“PSS”) is a brief summary of information related to the Product identified.  As a summary, it should
only be used for the limited purpose  of considering the purchase/use of Product.  For specific, detailed information, including but not
limited to testing and Product footprint, refer to Section 2.0 of this document and the links there provided to test reports and prints.  This
PSS is the property of  Samtec, Inc. (“Samtec”) and contains proprietary information of Samtec, our various licensors, or both. Samtec
does not grant express or implied rights or license under any patent, copyright, trademark or other proprietary rights and the use of the
PSS for building, reverse engineering or replication is strictly prohibited. By using the PSS, the u ser agrees to not infringe, directly or
indirectly, upon any intellectual property rights of Samtec and acknowledges that Samtec , our various licensors, or both  own all
intellectual property therein. The PSS is presented “AS IS”. While Samtec makes every effort to present excellent information, the PSS
is only provided as a guideline and does not, therefore, warrant it is without error or defect or that the PSS contains all necessary and/or
relevant information about the Product.  The user agrees that all access and use of the PSS is at its own risk. NO WARRANTIES
EXPRESSED OR IMPLIED, INCLUDING ANY WARRANTY OF MERCHANTABILITY, FITNESS FOR A PARTICULAR
PURPOSE OR OF ANY KIND WHATSOEVER ARE PROVIDED.
```
