thepinkmile/Enigma-NG/design/Datasheets/Samtec-qss-xxx-xx-xxx-d-ra-xx-xxx-mkt-datasheet.md

# D: DOUBLE

## Source

- **Source PDF:** [Samtec-qss-xxx-xx-xxx-d-ra-xx-xxx-mkt-datasheet.pdf](Samtec-qss-xxx-xx-xxx-d-ra-xx-xxx-mkt-datasheet.pdf)
- **Generated Markdown:** `Samtec-qss-xxx-xx-xxx-d-ra-xx-xxx-mkt-datasheet.md`
- **Page count:** 6
- **Conversion method:** automated local PDF text extraction with pypdf/pdfplumber

## PDF Metadata

| Field | Value |
| :--- | :--- |
| Title | QSS-XXX-XX-XXX-D-RA-XX-XXX-MKT |
| Author | SAMTECNT\hensont (DG-HENSONT) |
| Subject |  |
| Creator | SOLIDWORKS 2017 SP5.0 (2017317) |
| Producer | SOLIDWORKS PDF Publisher |

## Extracted Technical Index

This markdown datasheet is meant to reduce the need to reopen the PDF during design work.
It preserves design-relevant extracted snippets first, followed by page-by-page text so the source content remains locally searchable.

### Part number and ordering information

- SEE TABLE 8, SHEET 6 / -RA: RIGHT ANGLE / OPTION / -LS1: LOCKING SCREW / (SEE FIG 2, SHT 4)
- -MTI: THREADED INSERT / (NOT AVAILABLE / W/ LS1 OPTION) / (SEE FIG 5, SHT 6) / -SP: SOLDER PIN
- -SP: SOLDER PIN / (NOT AVAILABLE / W/LS1 OPTION) / (USE SP-19-T) / (SEE FIG 3, SHT 5)
- 3.  MINIMUM PUSHOUT FORCE: 6 OZ. / 4.  WELD TABS (WT-16-XX-T) NOT AVAILABLE ON -025 POSITION. / WT OPTION MUST BE SELECTED FOR -050, -075 & -100 POSITIONS. / 5.  IF NEEDED, -L PLATING CAN BE SUB…
- C / FIG 4 / -K OPTION / QSS-075-01-XXX-D-RA-WT-K SHOWN / (SAME AS FIG. 1, EXCEPT AS SHOWN)
- QSS-075-01-XXX-D-RA-WT-SP SHOWN / (SAME AS FIG. 1, EXCEPT AS SHOWN) / (NOT AVAILABLE WITH LS1 OPTION) / (SOME CENTER DETAILS REMOVED FOR CLARITY) / \* = SEE NOTE 12 SHEET     OF

### Pin, pad, and connection designations

- W/ LS1 OPTION) / (SEE FIG 5, SHT 6) / -SP: SOLDER PIN / (NOT AVAILABLE / W/LS1 OPTION)
- (USE SP-19-T) / (SEE FIG 3, SHT 5) / -K: KAPTON PAD / (SEE FIG 4, SHT 5) / (USE K-500-300)
- SHEET SCALE: 1.5:1 / INSULATOR: LCP, COLOR: BLACK / TERMINAL, GROUND PLANE & / WELD TAB: PHOS BRONZE / F:\\DWG\\MISC\\MKTG\\QSS-XXX-XX-XXX-D-RA-XX-XXX-MKT.SLDDRW

### Specifications, ratings, and operating conditions

- (SEE NOTE 4) / \*(SEE NOTE 12) / ROW SPECIFICATION / -D: DOUBLE / (USE QSS-25-01-D-XX-RA)
- (USE QSS-25-01-D-XX-RA) / LEAD STYLE / PLATING SPECIFICATION / SEE TABLE 8, SHEET 6 / -RA: RIGHT ANGLE
- UNLESS  OTHERWISE  SPECIFIED, / DIMENSIONS ARE IN INCHES. / TOLERANCES  ARE: / DECIMALS                     ANGLES / .XX: .01 [.3]               2

### Dimensions, package, and mechanical information

- SHEET     OF / UNLESS  OTHERWISE  SPECIFIED, / DIMENSIONS ARE IN INCHES. / TOLERANCES  ARE: / DECIMALS                     ANGLES
- QSS-XXX-XX-XXX-D-RA-XX-XXX / DWG.  NO. / DESCRIPTION:DO  NOT  SCALE  DRAWING / KEVIN B 01/22/02 61 / SHEET SCALE: 1.5:1
- F:\\DWG\\MISC\\MKTG\\QSS-XXX-XX-XXX-D-RA-XX-XXX-MKT.SLDDRW / NOTES: / 1.         REPRESENTS A CRITICAL DIMENSION. / 2.  BURR ALLOWANCE: .0010 MAX. / 3.  MINIMUM PUSHOUT FORCE: 6 OZ.
- TO SECOND ROW FILL. / 7.  DESIGNED FOR USE WITH A .062 OR .093 THICK PCB / 8.  ASSEMBLIES TO BE PACKAGED IN TRAYS. / 9.  NOTE DELETED / 10. TORQUE TO BE 10.0 IN-OZ USING 4-40 UNC SCREW.
- DWG.  NO. / DESCRIPTION: / DO  NOT  SCALE  DRAWING / KEVIN B 01/22/02 62 / SHEET SCALE: 6:1
- DWG.  NO. / DESCRIPTION: / DO  NOT  SCALE  DRAWING / KEVIN B 01/22/02 63 / SHEET SCALE: 1.5:1
- DWG.  NO. / DESCRIPTION: / DO  NOT  SCALE  DRAWING / KEVIN B 01/22/02 64 / SHEET SCALE: 1.5:1
- DWG.  NO. / DESCRIPTION: / DO  NOT  SCALE  DRAWING / KEVIN B 01/22/02 65 / SHEET SCALE: 1:0.666667
- DWG.  NO. / DESCRIPTION: / DO  NOT  SCALE  DRAWING / KEVIN B 01/22/02 66 / SHEET SCALE: 1:0.666667

### Formulas, equations, and configurable calculations

- No reliable text snippet was automatically extracted for this category. Review the raw page text below.

### Reference designs, applications, and examples

- No reliable text snippet was automatically extracted for this category. Review the raw page text below.

## Page-by-Page Extracted Content

### Page 1

```text
THIS DOCUMENT CONTAINS CONFIDENTIAL AND
PROPRIETARY INFORMATION AND ALL DESIGN,
MANUFACTURING, REPRODUCTION, USE, PATENT RIGHTS
AND SALES RIGHTS ARE EXPRESSLY RESERVED BY SAMTEC,
INC. THIS DOCUMENT SHALL NOT BE DISCLOSED, IN WHOLE
OR PART, TO ANY UNAUTHORIZED PERSON OR ENTITY NOR
REPRODUCED, TRANSFERRED OR INCORPORATED IN ANY
OTHER PROJECT IN ANY MANNER WITHOUT THE EXPRESS
WRITTEN CONSENT OF SAMTEC, INC.
PROPRIETARY NOTE* *
DO NOT
SCALE FROM
THIS PRINT
QSS-XXX-XX-XXX-D-RA-XX-XXX
No OF POSITIONS
-025, -050, -075, *-100
(PER ROW)
(SEE NOTE 4)
*(SEE NOTE 12)
ROW SPECIFICATION
-D: DOUBLE
     (USE QSS-25-01-D-XX-RA)
LEAD STYLE
PLATING SPECIFICATION
SEE TABLE 8, SHEET 6
-RA: RIGHT ANGLE
OPTION
-LS1: LOCKING SCREW
        (SEE FIG 2, SHT 4)
        (FOR MATING WITH
         QTS-...-RA-..LS1)
-MTI: THREADED INSERT
        (NOT AVAILABLE
         W/ LS1 OPTION)
         (SEE FIG 5, SHT 6)
-SP: SOLDER PIN
       (NOT AVAILABLE
         W/LS1 OPTION)
        (USE SP-19-T)
        (SEE FIG 3, SHT 5)
  -K: KAPTON PAD
       (SEE FIG 4, SHT 5)
       (USE K-500-300)
-WT: WELD TAB
(SEE NOTE 4)
(USE WT-16-XX-T)
-01: .062 BOARD
-02: .093 BOARD
.012  REF0.30
.025  SQ0.64
 REF (TYP)
 (SEE NOTE 4)
"D"  REF
.7838  REF19.91
.069  REF1.75
(SEE TABLE 2)
 "E" REF
"C"  REF
.186  REF4.71
.328  REF8.33
.245  6.22
REF
 .600  15.24
24 EQ SPACES
@ .0250[.635] =
.560 14.22
7 EQ SPACES @ .080[2.03] =
.096  REF2.44
.114 ±.003 2.89 ±0.08
   (TYP) (SEE NOTE 4)
01CL
C
C
C
CL CL
QSS-25-01-D-XX-RA
02
.250  REF (TYP)6.35
"A"  REF
.280  REF7.11
.006  REF0.15
"B"  REF
.560 14.22
REF
.250  MAX REF (TYP)6.35
.1240  INSCRIBED3.15
    REF (TYP)
CONNECTOR TO
PCB MOUNTING
POINT (2 PLCS)
(SEE NOTE 10)
C
.125  REF3.18
FIG 1
QSS-075-01-XXX-D-RA-WT SHOWN
(SOME CENTER DETAILS REMOVED FOR CLARITY)
* = SEE NOTE 12
C
SHEET     OF
UNLESS  OTHERWISE  SPECIFIED,
DIMENSIONS ARE IN INCHES.
TOLERANCES  ARE:
DECIMALS                     ANGLES
.XX: .01 [.3]               2
.XXX: .005 [.13]
.XXXX: .0020 [.051]
MATERIAL:
.635mm DOUBLE ROW RIGHT ANGLE SOCKET STRIP
BY:
QSS-XXX-XX-XXX-D-RA-XX-XXX
DWG.  NO.
DESCRIPTION:DO  NOT  SCALE  DRAWING
KEVIN B 01/22/02 61
SHEET SCALE: 1.5:1
INSULATOR: LCP, COLOR: BLACK
TERMINAL, GROUND PLANE &
  WELD TAB: PHOS BRONZE
F:\DWG\MISC\MKTG\QSS-XXX-XX-XXX-D-RA-XX-XXX-MKT.SLDDRW
NOTES:
1.         REPRESENTS A CRITICAL DIMENSION.
2.  BURR ALLOWANCE: .0010 MAX.
3.  MINIMUM PUSHOUT FORCE: 6 OZ.
4.  WELD TABS (WT-16-XX-T) NOT AVAILABLE ON -025 POSITION.
     WT OPTION MUST BE SELECTED FOR -050, -075 & -100 POSITIONS.
5.  IF NEEDED, -L PLATING CAN BE SUBSTITUTED FOR -F PLATING.
6.  IM-1G18-XX-1-XX RETENTION TO BE 1.0 LBS. MINIMUM PRIOR
     TO SECOND ROW FILL.
7.  DESIGNED FOR USE WITH A .062 OR .093 THICK PCB
8.  ASSEMBLIES TO BE PACKAGED IN TRAYS.
9.  NOTE DELETED
10. TORQUE TO BE 10.0 IN-OZ USING 4-40 UNC SCREW.
11. USE -Z- DATUM ZONE ONLY FOR MEASUREMENTS.
12. AVAILABLE FOR EXISTING CUSTOMERS ONLY.
520 PARK EAST BLVD, NEW ALBANY, IN 47150
PHONE: 812-944-6733       FAX: 812-948-5047
e-Mail   info@SAMTEC.com        code  55322
REVISION AQ
```

### Page 2

```text
THIS DOCUMENT CONTAINS CONFIDENTIAL AND
PROPRIETARY INFORMATION AND ALL DESIGN,
MANUFACTURING, REPRODUCTION, USE, PATENT RIGHTS
AND SALES RIGHTS ARE EXPRESSLY RESERVED BY SAMTEC,
INC. THIS DOCUMENT SHALL NOT BE DISCLOSED, IN WHOLE
OR PART, TO ANY UNAUTHORIZED PERSON OR ENTITY NOR
REPRODUCED, TRANSFERRED OR INCORPORATED IN ANY
OTHER PROJECT IN ANY MANNER WITHOUT THE EXPRESS
WRITTEN CONSENT OF SAMTEC, INC.
PROPRIETARY NOTE* *
"F"
(SEE NOTE 4 & 11)
.442  REF11.21
.010  REF0.25
"G" REF
(SEE NOTE 11)
.113 2.87
REF
.040  REF1.02.025  REF0.64
.285  REF7.24
.1700 4.318  REF
 .148 3.75
 (SEE NOTE 4)
.354  REF8.99
.0040 0.102
"F"
C-178-02-XXX
(SEE TABLE 8, SHEET 6)
IM-1G18-XX-1-XXX
 (SEE TABLE 4 & TABLE 8, SHEET 6)
C-177-01-XXX
(SEE TABLE 8, SHEET 6)
C
C
C
C
C
C
(LOCATE ASSY ON DATUM -C-
FOR MEASUREMENT)
C
SEE BOTTOM ROW-TAIL DETAIL
          WT-16-XX-T
(SEE NOTE 4 )
(SEE TABLE 4)
C
C
SEE TOP ROW-TAIL DETAIL
SEE TABLE 3
TOP ROW & BOTTOM ROW
-C-
.018  0.457
REF
30°  TYP REF
DETAIL "F"
SCALE 10 : 1
.004 REF0.10
(BOTTOM ROW)
(MEAS BOTH ENDS)
(SEE NOTE 11)
C-177-01-XXX
(SEE TABLE 8, SHEET 6)C
BOTTOM ROW - TAIL DETAIL
(LOCATE ASSEMBLY ON
DATUM -C- FOR MEASUREMENT)
-C-
.004  REF0.10
(TOP ROW)
(MEAS BOTH ENDS)
(SEE NOTE 11)
TOP ROW - TAIL DETAIL
(LOCATE ASSEMBLY ON
DATUM -C- FOR MEASUREMENT)
C-178-02-XXX
(SEE TABLE 8, SHEET 6)
C
-C-
* = SEE NOTE 12
SHEET     OF
.635mm DOUBLE ROW RIGHT ANGLE SOCKET STRIP
BY:
QSS-XXX-XX-XXX-D-RA-XX-XXX
DWG.  NO.
DESCRIPTION:
DO  NOT  SCALE  DRAWING
KEVIN B 01/22/02 62
SHEET SCALE: 6:1
F:\DWG\MISC\MKTG\QSS-XXX-XX-XXX-D-RA-XX-XXX-MKT.SLDDRW
REVISION AQ
520 PARK EAST BLVD, NEW ALBANY, IN 47150
PHONE: 812-944-6733       FAX: 812-948-5047
e-Mail   info@SAMTEC.com        code  55322
```

### Page 3

```text
THIS DOCUMENT CONTAINS CONFIDENTIAL AND
PROPRIETARY INFORMATION AND ALL DESIGN,
MANUFACTURING, REPRODUCTION, USE, PATENT RIGHTS
AND SALES RIGHTS ARE EXPRESSLY RESERVED BY SAMTEC,
INC. THIS DOCUMENT SHALL NOT BE DISCLOSED, IN WHOLE
OR PART, TO ANY UNAUTHORIZED PERSON OR ENTITY NOR
REPRODUCED, TRANSFERRED OR INCORPORATED IN ANY
OTHER PROJECT IN ANY MANNER WITHOUT THE EXPRESS
WRITTEN CONSENT OF SAMTEC, INC.
PROPRIETARY NOTE* *
.285  REF7.24 .004  REF0.10
(BOTTOM ROW)
(SEE NOTE 11)
QSS-25-01-D-XX-RA
IN-PROCESS 1
(FILL BOTTOM ROW)
(SEE INSPECTION VIEW 1 FOR ORIENTATION AND CPC'S)
C-177-01-XXX
(SEE TABLE 8, SHEET 6)
-C-
SEE TABLE 3, SHT 2
WITHIN ROW
"G"  REF
(SEE NOTE 11)
(SEE TABLE 4, SHEET 2)
.354  REF8.99
.424  REF10.77
IM-1G18-XX-1-XXX
 (SEE TABLE 4, SHEET 2
& TABLE 8, SHEET 6)
IN-PROCESS 2
(FILL IM-1G18)
(SEE INSPECTION VIEW 2 FOR ORIENTATION AND CPC'S)
-C-
.285  (TYP)7.24
.046 1.17
REF
INSPECTION VIEW 1
(FILL BOTTOM ROW)
(LOCATE ASSEMBLY ON DATUM -C- FOR MEASURMENT)
C-177-01-XXX
(SEE TABLE 8, SHEET 6)
C
-C-
Z1
Z2
'G' 'H'
.004 ±.002 0.10 ±0.05
(BOTTOM ROW)
(SEE NOTE 11)
DETAIL 'G'
SCALE 6 : 1
C
Z1
.004 ±.002 0.10 ±0.05
(BOTTOM ROW)
(SEE NOTE 11)
DETAIL 'H'
SCALE 6 : 1
C
C
SEE TABLE 3, SHT 2
WITHIN ROW
Z2
.354 8.99
.046 1.17  REF
INSPECTION VIEW 2
(FILL IM-1G18)
IM-1G18-XX-1-XXX
 (SEE TABLE 4, SHEET 2
& TABLE 8, SHEET 6)
C
-C-
Z1 Z2
"G"
(SEE TABLE 4, SHEET 2)
(SEE NOTE 11)
"G"
(SEE TABLE 4, SHEET 2)
(SEE NOTE 11)
C C
Z1 Z2
.046  REF1.17
ISO VIEW OF
-Z- DATUM ZONE
Zx
SHEET     OF
.635mm DOUBLE ROW RIGHT ANGLE SOCKET STRIP
BY:
QSS-XXX-XX-XXX-D-RA-XX-XXX
DWG.  NO.
DESCRIPTION:
DO  NOT  SCALE  DRAWING
KEVIN B 01/22/02 63
SHEET SCALE: 1.5:1
F:\DWG\MISC\MKTG\QSS-XXX-XX-XXX-D-RA-XX-XXX-MKT.SLDDRW
REVISION  AQ
520 PARK EAST BLVD, NEW ALBANY, IN 47150
PHONE: 812-944-6733       FAX: 812-948-5047
e-Mail   info@SAMTEC.com        code  55322
```

### Page 4

```text
THIS DOCUMENT CONTAINS CONFIDENTIAL AND
PROPRIETARY INFORMATION AND ALL DESIGN,
MANUFACTURING, REPRODUCTION, USE, PATENT RIGHTS
AND SALES RIGHTS ARE EXPRESSLY RESERVED BY SAMTEC,
INC. THIS DOCUMENT SHALL NOT BE DISCLOSED, IN WHOLE
OR PART, TO ANY UNAUTHORIZED PERSON OR ENTITY NOR
REPRODUCED, TRANSFERRED OR INCORPORATED IN ANY
OTHER PROJECT IN ANY MANNER WITHOUT THE EXPRESS
WRITTEN CONSENT OF SAMTEC, INC.
PROPRIETARY NOTE* *
FIG 2
QSS-075-01-XXX-D-RA-WT-LS1 SHOWN
(SAME AS FIG. 1, EXCEPT AS SHOWN)
(SOME CENTER DETAILS REMOVED FOR CLARITY)
"H"  REF
"E"  REF (SEE TABLE 2, SHEET 1)
C
.442  REF11.21
.004  REF0.10
(TOP ROW)
(SEE NOTE 11)
.1700 4.318
C-178-02-XXX
(SEE TABLE 8, SHEET 6)
IN-PROCESS 3
(FILL TOP ROW)
(SEE INSPECTION VIEW 3 FOR ORIENTATION AND CPC'S)
SEE TABLE 3, SHT 2
WITHIN ROW
'J'
INSPECTION VIEW 3
(FILL TOP ROW)
(LOCATE ASSEMBLY ON DATUM -C- FOR MEASURMENT)
.1700 - .005
+.001
4.318 - 0.13
+0.03

DETAIL 'J'
SCALE 6 : 1
C
.442 11.21
.046 1.17  REF
C
-C-
Z1 Z2
'K' 'L'C-178-02-XXX
(SEE TABLE 8, SHEET 6)
.004 ±.002 0.10 ±0.05
(TOP ROW)
(SEE NOTE 11)
DETAIL 'K'
SCALE 6 : 1
C
Z1
.004 ±.002 0.10 ±0.05
TOP ROW
(SEE NOTE 11)
DETAIL 'L'
SCALE 6 : 1
C
C
SEE TABLE 3, SHT 2
WITHIN ROW
Z2
* = SEE NOTE 12
SHEET     OF
.635mm DOUBLE ROW RIGHT ANGLE SOCKET STRIP
BY:
QSS-XXX-XX-XXX-D-RA-XX-XXX
DWG.  NO.
DESCRIPTION:
DO  NOT  SCALE  DRAWING
KEVIN B 01/22/02 64
SHEET SCALE: 1.5:1
F:\DWG\MISC\MKTG\QSS-XXX-XX-XXX-D-RA-XX-XXX-MKT.SLDDRW
REVISION  AQ
520 PARK EAST BLVD, NEW ALBANY, IN 47150
PHONE: 812-944-6733       FAX: 812-948-5047
e-Mail   info@SAMTEC.com        code  55322
```

### Page 5

```text
THIS DOCUMENT CONTAINS CONFIDENTIAL AND
PROPRIETARY INFORMATION AND ALL DESIGN,
MANUFACTURING, REPRODUCTION, USE, PATENT RIGHTS
AND SALES RIGHTS ARE EXPRESSLY RESERVED BY SAMTEC,
INC. THIS DOCUMENT SHALL NOT BE DISCLOSED, IN WHOLE
OR PART, TO ANY UNAUTHORIZED PERSON OR ENTITY NOR
REPRODUCED, TRANSFERRED OR INCORPORATED IN ANY
OTHER PROJECT IN ANY MANNER WITHOUT THE EXPRESS
WRITTEN CONSENT OF SAMTEC, INC.
PROPRIETARY NOTE* *
.065 ±.010 1.65 ±0.25
.790  REF20.07
.250  REF6.35
"J" ±.020  [0.51]
C
FIG 4
-K OPTION
QSS-075-01-XXX-D-RA-WT-K SHOWN
(SAME AS FIG. 1, EXCEPT AS SHOWN)
(SOME CENTER DETAILS REMOVED FOR CLARITY)
"B"
(SEE TABLE 1, SHEET 1)
.035  REF0.89
.055 1.40
SP-19-T
QSS-25-01-D-XX-RA-SP
C
C
.081  REF2.06
.333  REF8.46
FIG 3
QSS-075-01-XXX-D-RA-WT-SP SHOWN
(SAME AS FIG. 1, EXCEPT AS SHOWN)
(NOT AVAILABLE WITH LS1 OPTION)
(SOME CENTER DETAILS REMOVED FOR CLARITY)
* = SEE NOTE 12 SHEET     OF
.635mm DOUBLE ROW RIGHT ANGLE SOCKET STRIP
BY:
QSS-XXX-XX-XXX-D-RA-XX-XXX
DWG.  NO.
DESCRIPTION:
DO  NOT  SCALE  DRAWING
KEVIN B 01/22/02 65
SHEET SCALE: 1:0.666667
F:\DWG\MISC\MKTG\QSS-XXX-XX-XXX-D-RA-XX-XXX-MKT.SLDDRW
REVISION  AQ
520 PARK EAST BLVD, NEW ALBANY, IN 47150
PHONE: 812-944-6733       FAX: 812-948-5047
e-Mail   info@SAMTEC.com        code  55322
```

### Page 6

```text
THIS DOCUMENT CONTAINS CONFIDENTIAL AND
PROPRIETARY INFORMATION AND ALL DESIGN,
MANUFACTURING, REPRODUCTION, USE, PATENT RIGHTS
AND SALES RIGHTS ARE EXPRESSLY RESERVED BY SAMTEC,
INC. THIS DOCUMENT SHALL NOT BE DISCLOSED, IN WHOLE
OR PART, TO ANY UNAUTHORIZED PERSON OR ENTITY NOR
REPRODUCED, TRANSFERRED OR INCORPORATED IN ANY
OTHER PROJECT IN ANY MANNER WITHOUT THE EXPRESS
WRITTEN CONSENT OF SAMTEC, INC.
PROPRIETARY NOTE* *
.274 6.96
REF
FIG 5
QSS-075-01-XXX-D-RA-WT-MTI SHOWN
(SAME AS FIG. 1, EXCEPT AS SHOWN)
(SOME CENTER DETAILS REMOVED FOR CLARITY)
"K"  REF
"L"  REF
#4-40 THREAD REF
C
C
* = SEE NOTE 12
SHEET     OF
.635mm DOUBLE ROW RIGHT ANGLE SOCKET STRIP
BY:
QSS-XXX-XX-XXX-D-RA-XX-XXX
DWG.  NO.
DESCRIPTION:
DO  NOT  SCALE  DRAWING
KEVIN B 01/22/02 66
SHEET SCALE: 1:0.666667
F:\DWG\MISC\MKTG\QSS-XXX-XX-XXX-D-RA-XX-XXX-MKT.SLDDRW
REVISION  AQ
520 PARK EAST BLVD, NEW ALBANY, IN 47150
PHONE: 812-944-6733       FAX: 812-948-5047
e-Mail   info@SAMTEC.com        code  55322
```
