thepinkmile/Enigma-NG/design/Datasheets/Samtec-qss-xxx-xx-xxx-d-xxx-x-xx-mkt-datasheet.md

# D: DOUBLE (USE QSS-25-XX-D-XX)

## Source

- **Source PDF:** [Samtec-qss-xxx-xx-xxx-d-xxx-x-xx-mkt-datasheet.pdf](Samtec-qss-xxx-xx-xxx-d-xxx-x-xx-mkt-datasheet.pdf)
- **Generated Markdown:** `Samtec-qss-xxx-xx-xxx-d-xxx-x-xx-mkt-datasheet.md`
- **Page count:** 3
- **Conversion method:** automated local PDF text extraction with pypdf/pdfplumber

## PDF Metadata

| Field | Value |
| :--- | :--- |
| Title | QSS-XXX-XX-XXX-D-XXX-X-XX-MKT |
| Author | SAMTECNT\41440 (CR-OWENV) |
| Subject |  |
| Creator | SOLIDWORKS 2022 SP5.0 (2022290) |
| Producer | SOLIDWORKS PDF Publisher |

## Extracted Technical Index

This markdown datasheet is meant to reduce the need to reopen the PDF during design work.
It preserves design-relevant extracted snippets first, followed by page-by-page text so the source content remains locally searchable.

### Part number and ordering information

- \*SEE NOTES 11 & 14 / -D: DOUBLE (USE QSS-25-XX-D-XX) / OPTION / PLATING SPECIFICATION / LEAD STYLE
- CONTACT AREA, TIN LEAD ON TAIL / (USE C-126-21-FTL & T-1G2-01-FTL) / (SEE NOTES 8 & 11) PICK AND PLACE OPTION / PACKAGING / BLANK: TRAY (SEE NOTES 15 & 16)
- C / FIG 1 / -A: ALIGNMENT PIN OPTION / (QSS-075-01-XXX-D-A SHOWN) / SHEET     OF
- 10. NOTE DELETED. / 11. FOR -100 AND -125 POSITIONS USE C-269-11-X, DO NOT SUB C-126-01-X. / 12. DUE TO THE HIGH AMOUNT OF INSERTION FORCE NEEDED, THE –LC OPTION / IS NOT COMPATIBLE WITH AUTO PL…
- 12. DUE TO THE HIGH AMOUNT OF INSERTION FORCE NEEDED, THE –LC OPTION / IS NOT COMPATIBLE WITH AUTO PLACEMENT. SAMTEC RECOMMENDS / MANUAL PLACEMENT FOR ALL ASSEMBLIES WITH THE –LC OPTION. / 13. C…
- LC-08-TM-01 / FIG 2 / -LC: LOCKING CLIP OPTION / (QSS-075-01-XXX-D-LC SHOWN) / (DIFFERENT AS SHOWN, OTHERWISE SAME AS FIG 1)
- QSS-25-01-D-XXX-A-GP / FIG 4 / -GP: GUIDE POST OPTION / (QSS-075-01-XXX-D-GP SHOWN) / (DIFFERENT AS SHOWN, OTHERWISE SAME AS FIG 1)
- "F" REF / FIG 5 / -LS2: LOCKING SCREW OPTION / (QSS-075-01-XXX-D-LS2 SHOWN) / (DIFFERENT AS SHOWN, OTHERWISE SAME AS FIG 1)
- (QSS-075-01-XXX-D-LS2 SHOWN) / (DIFFERENT AS SHOWN, OTHERWISE SAME AS FIG 1) / (NOT AVAILABLE WITH -GP OPTION) / C / SHEET     OF

### Pin, pad, and connection designations

- No OF BANKS / ROW SPECIFICATION / -A: ALIGNMENT PINS / (USE QSS-25-XX-D-XX-A) / (NOT AVAILABLE WITH -LC)
- FOR 75 POS MAX, 50 POS MAX / FOR -GP) / -K: POLYIMIDE FILM PAD / (USE K-DOT-.325-.450-.005) / (SEE FIG 3, SHT 2)
- C / FIG 1 / -A: ALIGNMENT PIN OPTION / (QSS-075-01-XXX-D-A SHOWN) / SHEET     OF
- 17. ATTACH LABEL -4X2 TO EACH REEL. / 18. ANY CHANGES TO SHOULD ALSO BE APPLIED TO QSE, QSS, BSH, BSE, AND BSS. / 19. DIMENSION MEASURED, ON EACH BANK, FROM A PLANE CREATED FROM THE SIGNAL PINS.…
- 18. ANY CHANGES TO SHOULD ALSO BE APPLIED TO QSE, QSS, BSH, BSE, AND BSS. / 19. DIMENSION MEASURED, ON EACH BANK, FROM A PLANE CREATED FROM THE SIGNAL PINS. / 20. COPLANARITY INCLUDES SIGNAL PIN…
- "S"±.020[0.51] / FIG 3 / -K: POLYIMIDE FILM PAD / (USE K-DOT-.325-.450-.005) / C

### Specifications, ratings, and operating conditions

- -D: DOUBLE (USE QSS-25-XX-D-XX) / OPTION / PLATING SPECIFICATION / LEAD STYLE / -01: .1430[3.632]
- -01: .1430[3.632] / No OF BANKS / ROW SPECIFICATION / -A: ALIGNMENT PINS / (USE QSS-25-XX-D-XX-A)
- UNLESS  OTHERWISE  SPECIFIED, / DIMENSIONS ARE IN INCHES[MM] / TOLERANCES  ARE: / DECIMALS                     ANGLES / .XX: .01[.3]                  2

### Dimensions, package, and mechanical information

- SHEET     OF / UNLESS  OTHERWISE  SPECIFIED, / DIMENSIONS ARE IN INCHES[MM] / TOLERANCES  ARE: / DECIMALS                     ANGLES
- QSS-XXX-XX-XXX-D-XXX-X-XX / DWG.  NO. / DESCRIPTION:DO  NOT  SCALE  DRAWING / DEAN P 6/28/1999 31 / SHEET SCALE: 1.5:1
- 1. MINIMUM CONTACT RETENTION: 6 OZ / 2. MINIMUM GROUND PLANE RETENTION: 8 OZ / 3.       REPRESENTS A CRITICAL DIMENSION. / 4. PARTS ARE MOLD TO POSITION. / 5. NOTE DELETED.
- 14. AVAILABLE FOR EXISTING CUSTOMERS ONLY. / 15. TRAYS ARE STANDARD PACKAGING. / 16. ORDERS WILL BE PACKAGED ACCORDING TO THE SAMTEC PACKAGING EFFICIENCY / STANDARDS (SPES) FOUND ON WWW.SAMTEC.C…
- 17. ATTACH LABEL -4X2 TO EACH REEL. / 18. ANY CHANGES TO SHOULD ALSO BE APPLIED TO QSE, QSS, BSH, BSE, AND BSS. / 19. DIMENSION MEASURED, ON EACH BANK, FROM A PLANE CREATED FROM THE SIGNAL PINS.…
- DWG.  NO. / DESCRIPTION: / DO  NOT  SCALE  DRAWING / DEAN P 6/28/1999 32 / SHEET SCALE: 2:1
- DWG.  NO. / DESCRIPTION: / DO  NOT  SCALE  DRAWING / DEAN P 6/28/1999 33 / SHEET SCALE: 2.5:1

### Formulas, equations, and configurable calculations

- No reliable text snippet was automatically extracted for this category. Review the raw page text below.

### Reference designs, applications, and examples

- No reliable text snippet was automatically extracted for this category. Review the raw page text below.

## Page-by-Page Extracted Content

### Page 1

```text
THIS DOCUMENT CONTAINS CONFIDENTIAL AND
PROPRIETARY INFORMATION AND ALL DESIGN,
MANUFACTURING, REPRODUCTION, USE, PATENT RIGHTS
AND SALES RIGHTS ARE EXPRESSLY RESERVED BY SAMTEC,
INC. THIS DOCUMENT SHALL NOT BE DISCLOSED, IN WHOLE
OR PART, TO ANY UNAUTHORIZED PERSON OR ENTITY NOR
REPRODUCED, TRANSFERRED OR INCORPORATED IN ANY
OTHER PROJECT IN ANY MANNER WITHOUT THE EXPRESS
WRITTEN CONSENT OF SAMTEC, INC.
PROPRIETARY NOTE* *
DO NOT
SCALE FROM
THIS PRINT
.2850  REF7.239
.2450 6.223
        REF
.6250 15.875
         REF
"A" REF
.7875 20.003  (TYP)
.144 3.66  REF
.006 0.15  REF
=.600[15.24]
24 EQ SPCS
 @ .0250[0.635]
.0275 0.699
REF
C
02
01
QSS-XXX-XX-XXX-D-XXX-X-XX
No OF POSITIONS
-025, -050, -075,
*-100, *-125
*SEE NOTES 11 & 14
-D: DOUBLE (USE QSS-25-XX-D-XX)
OPTION
PLATING SPECIFICATION
LEAD STYLE
-01: .1430[3.632]
No OF BANKS
ROW SPECIFICATION
-A: ALIGNMENT PINS
     (USE QSS-25-XX-D-XX-A)
     (NOT AVAILABLE WITH -LC)
-LC: LOCKING CLIPS (SEE NOTE 12)
     (USE LC-08-TM-01, SEE FIG 2, SHT 2)
     (NOT AVAILABLE WITH -A)
-GP: GUIDE POSTS (SEE FIG 4, SHT 3)
      (USE QSS-25-01-D-XX-X-GP)
      (NOT AVAILABLE WITH -LS2)
-LS2: LOCKING SCREW (SEE FIG 5, SHT 3)
      (USE QSS-25-01-D-XX-LS2)
      (NOT AVAILABLE WITH -GP)
      (FOR MATING WITH
         QTS-...-RA-..LS2)
-F: 3µ" FLASH SELECTIVE GOLD IN
     CONTACT AREA, MATTE TIN ON TAIL
    (USE C-126-21-F & T-1G2-01-F)
    (SEE NOTE 8)
-L: 10µ" LIGHT SELECTIVE GOLD, IN
      CONTACT AREA, MATTE TIN ON TAIL
    (USE C-126-21-L & T-1G2-01-L)
-H: 30µ" HEAVY GOLD IN CONTACT
      AREA, 3µ" GOLD ON TAIL
    (USE C-126-21-H & T-1G2-01-G)
-C: 50µ" HEAVY GOLD IN CONTACT
      AREA, MATTE TIN ON TAIL
    (USE C-126-21-C & T-1G2-01-L)
-STL: 30µ" HEAVY SELECTIVE GOLD IN
        CONTACT AREA, TIN LEAD ON TAIL
    (USE C-126-21-STL & T-1G2-01-STL)
-FTL: 3µ" FLASH SELECTIVE GOLD IN
        CONTACT AREA, TIN LEAD ON TAIL
    (USE C-126-21-FTL & T-1G2-01-FTL)
(SEE NOTES 8 & 11) PICK AND PLACE OPTION
PACKAGING
BLANK: TRAY (SEE NOTES 15 & 16)
-TR: TAPE & REEL (SEE NOTES 16&17)
-FR: FULL REEL QTY TAPE & REEL
       (SEE NOTES 16&17)
(-TR & -FR PACKAGING AVAILABLE
 FOR 75 POS MAX, 50 POS MAX
  FOR -GP)
-K: POLYIMIDE FILM PAD
     (USE K-DOT-.325-.450-.005)
     (SEE FIG 3, SHT 2)
.135 3.43
REF
.7250  REF18.415
 "B" REF
.0375 0.953
REF
"A"
"A"
QSS-25-01-D-XX-A
.035 0.89  REF
.105 2.65  REFT-1G2-01-XXX
.1430-.001
+.003  3.632-0.03
+0.08
.295 7.49
.0070  REF0.178
.165+
-
.006
.002 4.19+
-
0.152
0.051
.0030  REF0.076
.017±.005 0.44±0.13
(SEE NOTE 13)
.070 1.765  REF
'B'
SECTION "A"-"A"
SCALE 3 : 1
C
C-126-21-XXX
C
C
C
(SEE NOTE 18)
SEE TABLE 1
(SEE NOTE 20)
.0010+
-
.0025
.0020 0.025+
-
0.064
0.051
(SEE NOTE 19)
DETAIL 'B'
SCALE 6 : 1
C
FIG 1
-A: ALIGNMENT PIN OPTION
(QSS-075-01-XXX-D-A SHOWN)
SHEET     OF
UNLESS  OTHERWISE  SPECIFIED,
DIMENSIONS ARE IN INCHES[MM]
TOLERANCES  ARE:
DECIMALS                     ANGLES
.XX: .01[.3]                  2
.XXX: .005[.13]
.XXXX: .0020.051]
MATERIAL:
.635mm DOUBLE ROW HS SOCKET ASSEMBLY
BY:
QSS-XXX-XX-XXX-D-XXX-X-XX
DWG.  NO.
DESCRIPTION:DO  NOT  SCALE  DRAWING
DEAN P 6/28/1999 31
SHEET SCALE: 1.5:1
INSULATOR: LCP, UL94V-0; COLOR: BLACK
CONTACT: PHOS BRONZE
GROUND PLANE: PHOS BRONZE
c:\enterprisevault\DWG\MISC\MKTG\QSS-XXX-XX-XXX-D-XXX-X-XX-MKT.SLDDRW
NOTES:
   1. MINIMUM CONTACT RETENTION: 6 OZ
   2. MINIMUM GROUND PLANE RETENTION: 8 OZ
   3.       REPRESENTS A CRITICAL DIMENSION.
   4. PARTS ARE MOLD TO POSITION.
   5. NOTE DELETED.
   6. NOTE DELETED.
   7. NOTE DELETED.
   8. -L PLATING CAN BE SUBSTITUTED FOR -F PLATING.
   9. NOTE DELETED.
 10. NOTE DELETED.
 11. FOR -100 AND -125 POSITIONS USE C-269-11-X, DO NOT SUB C-126-01-X.
 12. DUE TO THE HIGH AMOUNT OF INSERTION FORCE NEEDED, THE –LC OPTION
       IS NOT COMPATIBLE WITH AUTO PLACEMENT. SAMTEC RECOMMENDS
       MANUAL PLACEMENT FOR ALL ASSEMBLIES WITH THE –LC OPTION.
 13. CHECK ONCE PER BANK ALTERNATING SIDES FOR MULTIPLE BANK PARTS.
 14. AVAILABLE FOR EXISTING CUSTOMERS ONLY.
 15. TRAYS ARE STANDARD PACKAGING.
 16. ORDERS WILL BE PACKAGED ACCORDING TO THE SAMTEC PACKAGING EFFICIENCY
       STANDARDS (SPES) FOUND ON WWW.SAMTEC.COM.
 17. ATTACH LABEL -4X2 TO EACH REEL.
 18. ANY CHANGES TO SHOULD ALSO BE APPLIED TO QSE, QSS, BSH, BSE, AND BSS.
 19. DIMENSION MEASURED, ON EACH BANK, FROM A PLANE CREATED FROM THE SIGNAL PINS.
 20. COPLANARITY INCLUDES SIGNAL PINS AND GROUND PLANES.
520 PARK EAST BLVD, NEW ALBANY, IN 47150
PHONE: 812-944-6733       FAX: 812-948-5047
e-Mail   info@SAMTEC.com        code  55322
REVISION BB
```

### Page 2

```text
THIS DOCUMENT CONTAINS CONFIDENTIAL AND
PROPRIETARY INFORMATION AND ALL DESIGN,
MANUFACTURING, REPRODUCTION, USE, PATENT RIGHTS
AND SALES RIGHTS ARE EXPRESSLY RESERVED BY SAMTEC,
INC. THIS DOCUMENT SHALL NOT BE DISCLOSED, IN WHOLE
OR PART, TO ANY UNAUTHORIZED PERSON OR ENTITY NOR
REPRODUCED, TRANSFERRED OR INCORPORATED IN ANY
OTHER PROJECT IN ANY MANNER WITHOUT THE EXPRESS
WRITTEN CONSENT OF SAMTEC, INC.
PROPRIETARY NOTE* *
"R" REF
.020±.020 0.51±0.51
.325 8.26
"S"±.020[0.51]
FIG 3
-K: POLYIMIDE FILM PAD
(USE K-DOT-.325-.450-.005)
C
C
.1480 3.759
.055 1.40
"B"±.003[0.08]
(SEE TABLE 2, SHT 1)
.010 0.25  REF
QSS-25-XXX-D-XX
LC-08-TM-01
FIG 2
-LC: LOCKING CLIP OPTION
(QSS-075-01-XXX-D-LC SHOWN)
(DIFFERENT AS SHOWN, OTHERWISE SAME AS FIG 1)
C
.056 1.42  REF
.0375 0.953
SHEET     OF
.635mm DOUBLE ROW HS SOCKET ASSEMBLY
BY:
QSS-XXX-XX-XXX-D-XXX-X-XX
DWG.  NO.
DESCRIPTION:
DO  NOT  SCALE  DRAWING
DEAN P 6/28/1999 32
SHEET SCALE: 2:1
REVISION BB
c:\enterprisevault\DWG\MISC\MKTG\QSS-XXX-XX-XXX-D-XXX-X-XX-MKT.SLDDRW
520 PARK EAST BLVD, NEW ALBANY, IN 47150
PHONE: 812-944-6733       FAX: 812-948-5047
e-Mail   info@SAMTEC.com        code  55322
```

### Page 3

```text
THIS DOCUMENT CONTAINS CONFIDENTIAL AND
PROPRIETARY INFORMATION AND ALL DESIGN,
MANUFACTURING, REPRODUCTION, USE, PATENT RIGHTS
AND SALES RIGHTS ARE EXPRESSLY RESERVED BY SAMTEC,
INC. THIS DOCUMENT SHALL NOT BE DISCLOSED, IN WHOLE
OR PART, TO ANY UNAUTHORIZED PERSON OR ENTITY NOR
REPRODUCED, TRANSFERRED OR INCORPORATED IN ANY
OTHER PROJECT IN ANY MANNER WITHOUT THE EXPRESS
WRITTEN CONSENT OF SAMTEC, INC.
PROPRIETARY NOTE* *
"C" REF
.140  THRU REF3.556
"D" REF.102  REF2.59
.207  REF5.245
C
.139  REF3.53
QSS-25-01-D-XXX-A-GP
FIG 4
-GP: GUIDE POST OPTION
(QSS-075-01-XXX-D-GP SHOWN)
(DIFFERENT AS SHOWN, OTHERWISE SAME AS FIG 1)
(50 POS MAX FOR TAPE & REEL OFFERING)
"E" REF
.110  REF2.79
.096  REF2.44
(CLEARANCE HOLE FOR USE
WITH 2-56 SCREW)
 "F" REF
FIG 5
-LS2: LOCKING SCREW OPTION
(QSS-075-01-XXX-D-LS2 SHOWN)
(DIFFERENT AS SHOWN, OTHERWISE SAME AS FIG 1)
 (NOT AVAILABLE WITH -GP OPTION)
C
SHEET     OF
.635mm DOUBLE ROW HS SOCKET ASSEMBLY
BY:
QSS-XXX-XX-XXX-D-XXX-X-XX
DWG.  NO.
DESCRIPTION:
DO  NOT  SCALE  DRAWING
DEAN P 6/28/1999 33
SHEET SCALE: 2.5:1
REVISION  BB
c:\enterprisevault\DWG\MISC\MKTG\QSS-XXX-XX-XXX-D-XXX-X-XX-MKT.SLDDRW
520 PARK EAST BLVD, NEW ALBANY, IN 47150
PHONE: 812-944-6733       FAX: 812-948-5047
e-Mail   info@SAMTEC.com        code  55322
```
