thepinkmile/Enigma-NG/design/Datasheets/Samtec-qts-xxx-xx-xxx-d-ra-xx-xxx-mkt-datasheet.md

# .XX: .01[0.3] 2

## Source

- **Source PDF:** [Samtec-qts-xxx-xx-xxx-d-ra-xx-xxx-mkt-datasheet.pdf](Samtec-qts-xxx-xx-xxx-d-ra-xx-xxx-mkt-datasheet.pdf)
- **Generated Markdown:** `Samtec-qts-xxx-xx-xxx-d-ra-xx-xxx-mkt-datasheet.md`
- **Page count:** 5
- **Conversion method:** automated local PDF text extraction with pypdf/pdfplumber

## PDF Metadata

| Field | Value |
| :--- | :--- |
| Title | QTS-XXX-XX-XXX-D-RA-XX-XXX-MKT |
| Author | SAMTECNT\jennbr (NA-JENNIFERB) |
| Subject |  |
| Creator | SOLIDWORKS 2017 SP5.0 (2017317) |
| Producer | SOLIDWORKS PDF Publisher |

## Extracted Technical Index

This markdown datasheet is meant to reduce the need to reopen the PDF during design work.
It preserves design-relevant extracted snippets first, followed by page-by-page text so the source content remains locally searchable.

### Part number and ordering information

- PLATING SPECIFICATION / -RA: RIGHT ANGLE / OPTION / -WT: WELD TAB / (SEE NOTE 5, USE WT-16-XX-T)
- (USE PPP-63, SEE FIG 4, SHT 5) / -SP: SOLDER PIN / (NOT AVAILABLE W/ LSX OPTIONS) / (USE SP-19-T, SEE FIG 5, SHT 5) / OPTION
- (NOT AVAILABLE W/ LSX OPTIONS) / (USE SP-19-T, SEE FIG 5, SHT 5) / OPTION / (SEE TABLE 4, SHT 4) / -025, -050, -075, \*-100
- 3. MINIMUM PUSHOUT FORCE: 5 OZ. / 4. NOTE DELETED. / 5. -WT OPTION MUST BE SELECTED FOR -050, -075 & -100 POSITIONS. / 6. TIPS OF TERMINALS MAY NOT EXTEND BEYOND THIS SURFACE. / 7. IF NEEDED, -L…
- "H" / PPP-63 / -P OPTION / (QTS-075-01-XXX-D-RA-WT-P SHOWN) / (SAME AS FIG 1, EXCEPT AS SHOWN)
- QTS-25-01-D-XX-RA-LS2 / FIG 3 / -LS2 OPTION / (QTS-075-01-XXX-D-RA-WT-LS2 SHOWN) / (SAME AS FIG 2, EXCEPT AS SHOWN)
- "A" / FIG 2 / -LS1 OPTION / (QTS-075-01-XXX-D-RA-WT-LS1 SHOWN) / (SAME AS FIG 1, EXCEPT AS SHOWN)
- C / FIG 5 / -SP OPTION / (QTS-075-01-XXX-D-RA-WT-SP SHOWN) / (SAME AS FIG 1, EXCEPT AS SHOWN)

### Pin, pad, and connection designations

- -LS1: LOCKING SCREW / (FOR MATING WITH QSS...-RA...-LS1) / (USE WITH SP-18-01-TM SOLDER PIN) / (SEE NOTE 11 & FIG 2, SHT 5) / -LS2: LOCKING SCREW
- -LS2: LOCKING SCREW / (FOR MATING WITH QSS...-LS2) / (USE WITH SP-18-01-TM SOLDER PIN) / (SEE NOTE 11 & FIG 3, SHT 5) / -P: PICK AND PLACE PAD
- (USE WITH SP-18-01-TM SOLDER PIN) / (SEE NOTE 11 & FIG 3, SHT 5) / -P: PICK AND PLACE PAD / (USE PPP-63, SEE FIG 4, SHT 5) / -SP: SOLDER PIN
- -P: PICK AND PLACE PAD / (USE PPP-63, SEE FIG 4, SHT 5) / -SP: SOLDER PIN / (NOT AVAILABLE W/ LSX OPTIONS) / (USE SP-19-T, SEE FIG 5, SHT 5)
- SHEET     OF / MATERIAL: / .635mm DOUBLE ROW RIGHT ANGLE TERMINAL STRIP / BY: / QTS-XXX-XX-XXX-D-RA-XX-XXX
- SHEET SCALE: 1:0.8 / INSULATOR: LCP, COLOR: BLACK / TERMINAL, WELD TAB & GROUND PLANE: / PHOS BRONZE / SCREW: STEEL
- 4. NOTE DELETED. / 5. -WT OPTION MUST BE SELECTED FOR -050, -075 & -100 POSITIONS. / 6. TIPS OF TERMINALS MAY NOT EXTEND BEYOND THIS SURFACE. / 7. IF NEEDED, -L PLATING CAN BE SUBSTITUTED FOR -F…
- .1540 3.912 / (MEASURED / TERMINAL TO / TERMINAL)
- (MEASURED / TERMINAL TO / TERMINAL) / .025  REF0.64
- \* = SEE NOTE 14 / SHEET     OF / .635mm DOUBLE ROW RIGHT ANGLE TERMINAL STRIP / BY: / QTS-XXX-XX-XXX-D-RA-XX-XXX
- (SEE INSPECTION VIEW 2 FOR ORIENTATION AND CPC'S) / SHEET     OF / .635mm DOUBLE ROW RIGHT ANGLE TERMINAL STRIP / BY: / QTS-XXX-XX-XXX-D-RA-XX-XXX
- .1540 3.912  (TYP) / (MEASURED / TERMINAL TO / TERMINAL) / DETAIL 'K'
- (MEASURED / TERMINAL TO / TERMINAL) / DETAIL 'K' / SCALE 6 : 1
- (SEE INSPECTION VIEW 3 FOR ORIENTATION AND CPC'S) / SHEET     OF / .635mm DOUBLE ROW RIGHT ANGLE TERMINAL STRIP / BY: / QTS-XXX-XX-XXX-D-RA-XX-XXX
- C / SHEET     OF / .635mm DOUBLE ROW RIGHT ANGLE TERMINAL STRIP / BY: / QTS-XXX-XX-XXX-D-RA-XX-XXX

### Specifications, ratings, and operating conditions

- .XXX: .005[0.13] / .XXXX: .0020[0.051] / TOLERANCES  ARE: / UNLESS  OTHERWISE  SPECIFIED, / DIMENSIONS ARE IN INCHES.
- QTS-XXX-XX-XXX-D-RA-XX-XXX / No OF POSITIONS / ROW SPECIFICATION / -D: DOUBLE (USE QTS-25-01-D-XX-RA) / LEAD STYLE
- -01: .062 [1.57] BOARD / -02: .093 [2.36] BOARD / PLATING SPECIFICATION / -RA: RIGHT ANGLE / OPTION

### Dimensions, package, and mechanical information

- TOLERANCES  ARE: / UNLESS  OTHERWISE  SPECIFIED, / DIMENSIONS ARE IN INCHES. / DO NOT / SCALE FROM
- QTS-XXX-XX-XXX-D-RA-XX-XXX / DWG.  NO. / DESCRIPTION:DO  NOT  SCALE  DRAWING / KEVIN B 08/03/01 51 / SHEET SCALE: 1:0.8
- F:\\DWG\\MISC\\MKTG\\QTS-XXX-XX-XXX-D-RA-XX-XXX-MKT.SLDDRW / NOTES: / 1.       REPRESENTS A CRITICAL DIMENSION. / 2. MAXIMUM BURR ALLOWANCE: .0010 [0.025] . / 3. MINIMUM PUSHOUT FORCE: 5 OZ.
- 7. IF NEEDED, -L PLATING CAN BE SUBSTITUTED FOR -F PLATING. / 8. DESIGNED FOR USE WITH A .062 [1.57] OR .093 [2.36] THICK PCB. / 9. PACKAGE IN TRAYS AS STANDARD. / 10. NOTE DELETED. / 11. MAXIMU…
- DWG.  NO. / DESCRIPTION: / DO  NOT  SCALE  DRAWING / KEVIN B 08/03/01 52 / SHEET SCALE: 6:1
- DWG.  NO. / DESCRIPTION: / DO  NOT  SCALE  DRAWING / KEVIN B 08/03/01 53 / SHEET SCALE: 6:1
- DWG.  NO. / DESCRIPTION: / DO  NOT  SCALE  DRAWING / KEVIN B 08/03/01 54 / SHEET SCALE: 1.5:1
- DWG.  NO. / DESCRIPTION: / DO  NOT  SCALE  DRAWING / KEVIN B 08/03/01 55 / SHEET SCALE: 1.5:1

### Formulas, equations, and configurable calculations

- No reliable text snippet was automatically extracted for this category. Review the raw page text below.

### Reference designs, applications, and examples

- No reliable text snippet was automatically extracted for this category. Review the raw page text below.

## Page-by-Page Extracted Content

### Page 1

```text
THIS DOCUMENT CONTAINS CONFIDENTIAL AND
PROPRIETARY INFORMATION AND ALL DESIGN,
MANUFACTURING, REPRODUCTION, USE, PATENT RIGHTS
AND SALES RIGHTS ARE EXPRESSLY RESERVED BY SAMTEC,
INC. THIS DOCUMENT SHALL NOT BE DISCLOSED, IN WHOLE
OR PART, TO ANY UNAUTHORIZED PERSON OR ENTITY NOR
REPRODUCED, TRANSFERRED OR INCORPORATED IN ANY
OTHER PROJECT IN ANY MANNER WITHOUT THE EXPRESS
WRITTEN CONSENT OF SAMTEC, INC.
PROPRIETARY NOTE* *
DECIMALS                     ANGLES
.XX: .01[0.3]              2
.XXX: .005[0.13]
.XXXX: .0020[0.051]
TOLERANCES  ARE:
UNLESS  OTHERWISE  SPECIFIED,
DIMENSIONS ARE IN INCHES.
DO NOT
SCALE FROM
THIS PRINT
QTS-XXX-XX-XXX-D-RA-XX-XXX
No OF POSITIONS
ROW SPECIFICATION
-D: DOUBLE (USE QTS-25-01-D-XX-RA)
LEAD STYLE
-01: .062 [1.57] BOARD
-02: .093 [2.36] BOARD
PLATING SPECIFICATION
-RA: RIGHT ANGLE
OPTION
-WT: WELD TAB
(SEE NOTE 5, USE WT-16-XX-T)
-LS1: LOCKING SCREW
(FOR MATING WITH QSS...-RA...-LS1)
(USE WITH SP-18-01-TM SOLDER PIN)
(SEE NOTE 11 & FIG 2, SHT 5)
-LS2: LOCKING SCREW
(FOR MATING WITH QSS...-LS2)
(USE WITH SP-18-01-TM SOLDER PIN)
(SEE NOTE 11 & FIG 3, SHT 5)
-P: PICK AND PLACE PAD
(USE PPP-63, SEE FIG 4, SHT 5)
-SP: SOLDER PIN
(NOT AVAILABLE W/ LSX OPTIONS)
(USE SP-19-T, SEE FIG 5, SHT 5)
OPTION
(SEE TABLE 4, SHT 4)
-025, -050, -075, *-100
[PER ROW]
* = SEE NOTE 14
.371  REF9.42
.7875  REF20.00
"C" REF
.235  REF5.97
.015  REF0.38
.025  SQ REF (TYP)0.64
 (SEE NOTE 5)
.008  REF0.20
.062 1.56  REF
.186 4.71
7 EQ SPACES
@ .080[2.03]
 @ .0250[.635]
24 EQ SPACES
.094  REF2.38
.09375±.0030 2.3813±0.076
(TYP) (SEE NOTE 5)
(TYP)
2  MAX SWAY
QTS-25-01-D-XX-RA
02
01
CL
CL
C
C
FIG 1
QTS-075-01-XXX-D-RA-WT SHOWN
(SOME CENTER DETAIL REMOVED FOR CLARITY)
CL
"B" REF
"A"
.280  REF7.11
.405  REF10.29
.120  REF3.05
.250  REF (TYP)6.35 .250  MAX REF (TYP)6.35
.124 3.15  INSCRIBED
REF (TYP)
C
CONNECTOR TO PCB
MOUNTING POINT (2 PLCS)
(SEE NOTE 12)
.125  REF3.18
C * = SEE NOTE 14
SHEET     OF
MATERIAL:
.635mm DOUBLE ROW RIGHT ANGLE TERMINAL STRIP
BY:
QTS-XXX-XX-XXX-D-RA-XX-XXX
DWG.  NO.
DESCRIPTION:DO  NOT  SCALE  DRAWING
KEVIN B 08/03/01 51
SHEET SCALE: 1:0.8
INSULATOR: LCP, COLOR: BLACK
TERMINAL, WELD TAB & GROUND PLANE:
   PHOS BRONZE
SCREW: STEEL
F:\DWG\MISC\MKTG\QTS-XXX-XX-XXX-D-RA-XX-XXX-MKT.SLDDRW
NOTES:
 1.       REPRESENTS A CRITICAL DIMENSION.
 2. MAXIMUM BURR ALLOWANCE: .0010 [0.025] .
 3. MINIMUM PUSHOUT FORCE: 5 OZ.
 4. NOTE DELETED.
 5. -WT OPTION MUST BE SELECTED FOR -050, -075 & -100 POSITIONS.
 6. TIPS OF TERMINALS MAY NOT EXTEND BEYOND THIS SURFACE.
 7. IF NEEDED, -L PLATING CAN BE SUBSTITUTED FOR -F PLATING.
 8. DESIGNED FOR USE WITH A .062 [1.57] OR .093 [2.36] THICK PCB.
 9. PACKAGE IN TRAYS AS STANDARD.
10. NOTE DELETED.
11. MAXIMUM TORQUE ON STS-02 TO BE 20 IN-OZ.
12. TORQUE TO BE 10.0 IN-OZ USING 4-40 UNC SCREW.
13. USE -Z- DATUM ZONE ONLY FOR MEASUREMENTS.
14. AVAILABLE FOR EXISTING CUSTOMERS ONLY.
520 PARK EAST BLVD, NEW ALBANY, IN 47150
PHONE: 812-944-6733       FAX: 812-948-5047
e-Mail   info@SAMTEC.com        code  55322
REVISION BF
```

### Page 2

```text
THIS DOCUMENT CONTAINS CONFIDENTIAL AND
PROPRIETARY INFORMATION AND ALL DESIGN,
MANUFACTURING, REPRODUCTION, USE, PATENT RIGHTS
AND SALES RIGHTS ARE EXPRESSLY RESERVED BY SAMTEC,
INC. THIS DOCUMENT SHALL NOT BE DISCLOSED, IN WHOLE
OR PART, TO ANY UNAUTHORIZED PERSON OR ENTITY NOR
REPRODUCED, TRANSFERRED OR INCORPORATED IN ANY
OTHER PROJECT IN ANY MANNER WITHOUT THE EXPRESS
WRITTEN CONSENT OF SAMTEC, INC.
PROPRIETARY NOTE* *
.299 7.59
.024  REF0.61
.012  REF0.30
"E"
(SEE NOTES 5 & 13)
.1540 3.912
(MEASURED
TERMINAL TO
TERMINAL)

.025  REF0.64
.040  REF1.02
.098  REF2.49
.110 2.79
"F"
(SEE TABLE 2)
(SEE NOTE 13)
.052  REF  (SEE NOTE 5)1.31
.184±.008 4.66±0.20
.132  (SEE NOTE 5)3.35
T-1S52-01-XXX
IM-1G14-XX-1-XXX
(SEE TABLE 2)
T-1S53-03-XXX
WT-16-XX-XX
(SEE TABLE 2)
(SEE NOTE 5)
SEE BOTTOM ROW-TAIL DETAIL
SEE TOP ROW-TAIL DETAIL
C
C
C
C
C
C
(LOCATE ASSY ON
DATUM -C- FOR
MEASUREMENT)
C
C
C
SEE NOTE 6 SEE TABLE 3
TOP ROW & BOTTOM ROW
-C-
.004±.002 0.09±0.05
(BOTTOM ROW)
(MEAS BOTH ENDS)
(SEE NOTE 13)
BOTTOM ROW - TAIL DETAIL
(LOCATE ASSEMBLY ON
DATUM -C- FOR MEASUREMENT)
T-1S52-01-XXX
C
-C-
.002+
-
.006
.000 0.05+

0.15
0.00

(TOP ROW)
(MEAS BOTH ENDS)
(SEE NOTE 13)
TOP ROW - TAIL DETAIL
(LOCATE ASSEMBLY ON
DATUM -C- FOR MEASUREMENT)
C
T-1S53-03-XXX-C-
* = SEE NOTE 14
SHEET     OF
.635mm DOUBLE ROW RIGHT ANGLE TERMINAL STRIP
BY:
QTS-XXX-XX-XXX-D-RA-XX-XXX
DWG.  NO.
DESCRIPTION:
DO  NOT  SCALE  DRAWING
KEVIN B 08/03/01 52
SHEET SCALE: 6:1
REVISION  BF
F:\DWG\MISC\MKTG\QTS-XXX-XX-XXX-D-RA-XX-XXX-MKT.SLDDRW
520 PARK EAST BLVD, NEW ALBANY, IN 47150
PHONE: 812-944-6733       FAX: 812-948-5047
e-Mail   info@SAMTEC.com        code  55322
```

### Page 3

```text
THIS DOCUMENT CONTAINS CONFIDENTIAL AND
PROPRIETARY INFORMATION AND ALL DESIGN,
MANUFACTURING, REPRODUCTION, USE, PATENT RIGHTS
AND SALES RIGHTS ARE EXPRESSLY RESERVED BY SAMTEC,
INC. THIS DOCUMENT SHALL NOT BE DISCLOSED, IN WHOLE
OR PART, TO ANY UNAUTHORIZED PERSON OR ENTITY NOR
REPRODUCED, TRANSFERRED OR INCORPORATED IN ANY
OTHER PROJECT IN ANY MANNER WITHOUT THE EXPRESS
WRITTEN CONSENT OF SAMTEC, INC.
PROPRIETARY NOTE* *
"F"
(SEE NOTE 13)
.184  REF4.66
.275 6.99  REF
IM-IG14-XXX-1-X
.110  REF2.79
.004  REF0.09
(BOTTOM ROW)
(SEE NOTE 13)
QTS-25-01-D-XX-RA
T-1S52-01-XXX
SEE TABLE 3
WITHIN ROW
.110  (TYP)2.79C
T-1S52-01-XXX
C C
INSPECTION VIEW 1
(FILL BOTTOM ROW)
-C-
Z2Z1
'D' 'E'T-1S52-01-XXX
(BOTTOM ROW)
.004±.002 0.09±0.05
(BOTTOM ROW)
(SEE NOTE 13)
DETAIL 'D'
SCALE 8 : 1
C
Z1
.004±.002 0.09±0.05
(BOTTOM ROW)
(SEE NOTE 13) DETAIL 'E'
SCALE 8 : 1
C
C
SEE TABLE 3
WITHIN ROW
Z2
.184 4.66
IM-IG14-XXX-1-X
C
CL
-C-
Z1 Z2
"F"
(SEE SHEET 2)
(SEE NOTE 13)
"F"
(SEE SHEET 2)
(SEE NOTE 13)Z1 Z2
INSPECTION VIEW 2
(FILL IM-1G14)
IN-PROCESS 1
(FILL BOTTOM ROW)
(SEE INSPECTION VIEW 1 FOR ORIENTATION AND CPC'S)
IN-PROCESS 2
(FILL IM-1G14)
(SEE INSPECTION VIEW 2 FOR ORIENTATION AND CPC'S)
SHEET     OF
.635mm DOUBLE ROW RIGHT ANGLE TERMINAL STRIP
BY:
QTS-XXX-XX-XXX-D-RA-XX-XXX
DWG.  NO.
DESCRIPTION:
DO  NOT  SCALE  DRAWING
KEVIN B 08/03/01 53
SHEET SCALE: 6:1
REVISION  BF
F:\DWG\MISC\MKTG\QTS-XXX-XX-XXX-D-RA-XX-XXX-MKT.SLDDRW
520 PARK EAST BLVD, NEW ALBANY, IN 47150
PHONE: 812-944-6733       FAX: 812-948-5047
e-Mail   info@SAMTEC.com        code  55322
```

### Page 4

```text
THIS DOCUMENT CONTAINS CONFIDENTIAL AND
PROPRIETARY INFORMATION AND ALL DESIGN,
MANUFACTURING, REPRODUCTION, USE, PATENT RIGHTS
AND SALES RIGHTS ARE EXPRESSLY RESERVED BY SAMTEC,
INC. THIS DOCUMENT SHALL NOT BE DISCLOSED, IN WHOLE
OR PART, TO ANY UNAUTHORIZED PERSON OR ENTITY NOR
REPRODUCED, TRANSFERRED OR INCORPORATED IN ANY
OTHER PROJECT IN ANY MANNER WITHOUT THE EXPRESS
WRITTEN CONSENT OF SAMTEC, INC.
PROPRIETARY NOTE* *
'F' 'G'
T-1S53-03-XXX
(TOP ROW)
.002+
-
.006
.000 0.05+

0.15
0.00

(TOP ROW)
(SEE NOTE 13)
DETAIL 'G'
SCALE 8 : 1
C
C
SEE TABLE 3
WITHIN ROW
Z2
.002-.000
+.006 0.05 0.00
+0.15
(TOP ROW)
(SEE NOTE 13)
DETAIL 'F'
SCALE 8 : 1
C
Z1
.299 7.59 C
-C-
Z1 Z2
.299  REF7.59 .002  REF0.05
(TOP ROW)
(SEE NOTE 13)
.154 3.91
REF (TYP)

T-1S53-03-XXX
SEE TABLE 3
WITHIN ROW
'K'
.1540 3.912  (TYP)
(MEASURED
TERMINAL TO
TERMINAL)
DETAIL 'K'
SCALE 6 : 1
C
INSPECTION VIEW 3
(FILL TOP ROW)
IN-PROCESS 3
(FILL TOP ROW)
(SEE INSPECTION VIEW 3 FOR ORIENTATION AND CPC'S)
SHEET     OF
.635mm DOUBLE ROW RIGHT ANGLE TERMINAL STRIP
BY:
QTS-XXX-XX-XXX-D-RA-XX-XXX
DWG.  NO.
DESCRIPTION:
DO  NOT  SCALE  DRAWING
KEVIN B 08/03/01 54
SHEET SCALE: 1.5:1
REVISION BF
F:\DWG\MISC\MKTG\QTS-XXX-XX-XXX-D-RA-XX-XXX-MKT.SLDDRW
520 PARK EAST BLVD, NEW ALBANY, IN 47150
PHONE: 812-944-6733       FAX: 812-948-5047
e-Mail   info@SAMTEC.com        code  55322
```

### Page 5

```text
THIS DOCUMENT CONTAINS CONFIDENTIAL AND
PROPRIETARY INFORMATION AND ALL DESIGN,
MANUFACTURING, REPRODUCTION, USE, PATENT RIGHTS
AND SALES RIGHTS ARE EXPRESSLY RESERVED BY SAMTEC,
INC. THIS DOCUMENT SHALL NOT BE DISCLOSED, IN WHOLE
OR PART, TO ANY UNAUTHORIZED PERSON OR ENTITY NOR
REPRODUCED, TRANSFERRED OR INCORPORATED IN ANY
OTHER PROJECT IN ANY MANNER WITHOUT THE EXPRESS
WRITTEN CONSENT OF SAMTEC, INC.
PROPRIETARY NOTE* *
.575  REF14.61 "D"±.020 [0.51]
.195+
-
.005
.010 4.95+
-
0.13
0.25
"H"
"H"
PPP-63
-P OPTION
(QTS-075-01-XXX-D-RA-WT-P SHOWN)
(SAME AS FIG 1, EXCEPT AS SHOWN)
FIG 4
C
.055  (TYP)1.40
(SEE NOTE 13).035  REF0.89
"B"±.005 [0.13]
C C .097 2.45
SP-19-T
.900  REF22.86
.432  REF10.96
.300  7.62
VIEW "H"-"H"
SCALE 1 : 1
(ROTATED 90 CW)
.096  REF2.44
(CLEARANCE HOLE
 FOR USE WITH 2-56 SCREW)
.035 0.89
"B"±.005 [.0.13]
.055  (TYP)1.40
(SEE NOTE 13)
QTS-25-01-D-XX-RA-LS2
FIG 3
-LS2 OPTION
(QTS-075-01-XXX-D-RA-WT-LS2 SHOWN)
(SAME AS FIG 2, EXCEPT AS SHOWN)
CC
SP-18-01-TM
.100  REF2.54
(STS SCREW REMOVED FOR CLARITY)
2  MAX SWAY
(EITHER DIRECTION)
"A"
"A"
FIG 2
-LS1 OPTION
(QTS-075-01-XXX-D-RA-WT-LS1 SHOWN)
(SAME AS FIG 1, EXCEPT AS SHOWN)
(AVAILABLE ON -01 LEADSTYLE ONLY)
.097 2.45
.301±.010 7.65±0.25
SECTION "A"-"A"
SCALE 2:1
SCREW CANNOT
PROTRUDE BEYOND
THIS SURFACE STS-02
(SEE NOTE 11)C
SP-18-01-TM
.055  (TYP)1.40
(SEE NOTE 13).035  REF0.89
"B"±.005 [.0.13]
.072 1.83
REF
QTS-25-01-D-XX-RA-LS1
C
C
FIG 5
-SP OPTION
(QTS-075-01-XXX-D-RA-WT-SP SHOWN)
(SAME AS FIG 1, EXCEPT AS SHOWN)
C
C
SHEET     OF
.635mm DOUBLE ROW RIGHT ANGLE TERMINAL STRIP
BY:
QTS-XXX-XX-XXX-D-RA-XX-XXX
DWG.  NO.
DESCRIPTION:
DO  NOT  SCALE  DRAWING
KEVIN B 08/03/01 55
SHEET SCALE: 1.5:1
REVISION  BF
F:\DWG\MISC\MKTG\QTS-XXX-XX-XXX-D-RA-XX-XXX-MKT.SLDDRW
520 PARK EAST BLVD, NEW ALBANY, IN 47150
PHONE: 812-944-6733       FAX: 812-948-5047
e-Mail   info@SAMTEC.com        code  55322
```
