thepinkmile/Enigma-NG/design/Datasheets/Samtec-qts-xxx-xx-xxx-d-xx-x-xx-mkt-datasheet.md

# A: ALIGNMENT PIN OPTION

## Source

- **Source PDF:** [Samtec-qts-xxx-xx-xxx-d-xx-x-xx-mkt-datasheet.pdf](Samtec-qts-xxx-xx-xxx-d-xx-x-xx-mkt-datasheet.pdf)
- **Generated Markdown:** `Samtec-qts-xxx-xx-xxx-d-xx-x-xx-mkt-datasheet.md`
- **Page count:** 3
- **Conversion method:** automated local PDF text extraction with pypdf/pdfplumber

## PDF Metadata

| Field | Value |
| :--- | :--- |
| Title | QTS-XXX-XX-XXX-D-XX-X-XX-MKT |
| Author | SAMTECNT\41440 (CR-OWENV) |
| Subject |  |
| Creator | SOLIDWORKS 2022 SP5.0 (2022290) |
| Producer | SOLIDWORKS PDF Publisher |

## Extracted Technical Index

This markdown datasheet is meant to reduce the need to reopen the PDF during design work.
It preserves design-relevant extracted snippets first, followed by page-by-page text so the source content remains locally searchable.

### Part number and ordering information

- "A" T-1G1-XX-XXX / FIG 1 / -A: ALIGNMENT PIN OPTION / (QTS-075-01-XXX-D-A SHOWN) / QTS-25-XX-D-XX-A
- (-TR & -FR PACKAGING N/A ON / STYLE -05 & -06, 75 POS MAX) / PICK & PLACE OPTION / -K: POLYIMIDE FILM PAD / (USE K-DOT-.276-.375-.005,
- (USE K-DOT-.276-.375-.005, / SEE FIG 3, SHT 2) / OPTION / -LC: LOCKING CLIPS (SEE NOTE 10 &15) / (USE LC-08-TM-01)
- 8. NOTE DELETED. / 9. NOTE DELETED. / 10. LEAD STYLES -03 AND -05: TOP BODY (QTS) CANNOT HAVE -A OPTION AND / -04 AND -06 CAN USE EITHER -A OR -LC BODY. / 11. T-1SXX-XX-L CAN BE SUBSTITUTED FOR …
- 14. NOTE DELETED. / 15. DUE TO THE HIGH AMOUNT OF INSERTION FORCE NEEDED, THE –LC / OPTION IS NOT COMPATIBLE WITH AUTO PLACEMENT. SAMTEC / RECOMMENDS MANUAL PLACEMENT FOR ALL ASSEMBLIES WITH THE…
- 15. DUE TO THE HIGH AMOUNT OF INSERTION FORCE NEEDED, THE –LC / OPTION IS NOT COMPATIBLE WITH AUTO PLACEMENT. SAMTEC / RECOMMENDS MANUAL PLACEMENT FOR ALL ASSEMBLIES WITH THE –LC OPTION. / 16. P…
- LC-08-TM-01 / FIG 2 / -LC: LOCKING CLIP OPTION / (QTS-075-01-XXX-D-LC SHOWN) / (DIFFERENT AS SHOWN, OTHERWISE SAME AS FIG 1)
- (USE K-DOT-.276-.375-.005) / FIG 4 / -GP: GUIDE POST OPTION / (QTS-075-01-XXX-D-GP SHOWN) / (DIFFERENT AS SHOWN, OTHERWISE SAME AS FIG 1)

### Pin, pad, and connection designations

- "A" T-1G1-XX-XXX / FIG 1 / -A: ALIGNMENT PIN OPTION / (QTS-075-01-XXX-D-A SHOWN) / QTS-25-XX-D-XX-A
- STYLE -05 & -06, 75 POS MAX) / PICK & PLACE OPTION / -K: POLYIMIDE FILM PAD / (USE K-DOT-.276-.375-.005, / SEE FIG 3, SHT 2)
- -LC: LOCKING CLIPS (SEE NOTE 10 &15) / (USE LC-08-TM-01) / -A: ALIGNMENT PINS (SEE NOTE 10) / (USE QTS-25-XX-D-XX-A) / -GP: GUIDE POST,  (SEE FIG 4, SHT 2)
- .XXXX: .0020[.051] / MATERIAL: / H.635mm DOUBLE ROW HS TERMINAL ASSEMBLY / BY: / QTS-XXX-XX-XXX-D-XX-X-XX
- SHEET SCALE: 1.5:1 / INSULATOR: LCP, UL94V-0; COLOR: BLACK / TERMINAL: PHOS BRONZE / GROUND PLANE: PHOS BRONZE / c:\\enterprisevault\\DWG\\MISC\\MKTG\\QTS-XXX-XX-XXX-D-XX-X-XX-MKT.SLDDRW
- 2. NOTE DELETED. / 3. NOTE DELETED. / 4. MINIMUM TERMINAL RETENTION: 6 OZ. / 5. MINIMUM GROUND PLANE RETENTION: 1 LB. / 6.  NOTE DELETED.
- OPTION IS NOT COMPATIBLE WITH AUTO PLACEMENT. SAMTEC / RECOMMENDS MANUAL PLACEMENT FOR ALL ASSEMBLIES WITH THE –LC OPTION. / 16. PIN CAN EXTEND PAST WALL .003[0.08] MAX. / 17. AVAILABLE FOR EXIS…
- 21.ATTACH LABEL-4X2 TO EACH REEL. / 22. ANY CHANGES SHOULD ALSO BE APPLIED TO QTH, QTE, QTS, BTH, BTE, AND BTS. / 23. DIMENSION MEASURED, ON EACH BANK, FROM A PLANE CREATED FROM THE SIGNAL PINS.…
- 22. ANY CHANGES SHOULD ALSO BE APPLIED TO QTH, QTE, QTS, BTH, BTE, AND BTS. / 23. DIMENSION MEASURED, ON EACH BANK, FROM A PLANE CREATED FROM THE SIGNAL PINS. / 24. COPLANARITY INCLUDES SIGNAL P…
- .0800 2.032 / FIG 3 / -K: POLYIMIDE FILM PAD / (USE K-DOT-.276-.375-.005) / FIG 4
- (AVAILABLE ON STYLE -01 ONLY) / SHEET     OF / H.635mm DOUBLE ROW HS TERMINAL ASSEMBLY / BY: / QTS-XXX-XX-XXX-D-XX-X-XX
- (DIFFERENT AS SHOWN, OTHERWISE SAME AS FIG 1) / SHEET     OF / H.635mm DOUBLE ROW HS TERMINAL ASSEMBLY / BY: / QTS-XXX-XX-XXX-D-XX-X-XX

### Specifications, ratings, and operating conditions

- (PER ROW) / \*\* (SEE NOTE 17) / ROW SPECIFICATION / -D: DOUBLE (USE QTS-25-XX-D-XX / & QTSH-25-XX-D-XX )
- -D: DOUBLE (USE QTS-25-XX-D-XX / & QTSH-25-XX-D-XX ) / PLATING SPECIFICATION / LEAD STYLE / -01: .1680[4.267]
- UNLESS  OTHERWISE  SPECIFIED, / DIMENSIONS ARE IN INCHES. / TOLERANCES  ARE: / DECIMALS                       ANGLES / .XX: .01[.3]               2

### Dimensions, package, and mechanical information

- SHEET     OF / UNLESS  OTHERWISE  SPECIFIED, / DIMENSIONS ARE IN INCHES. / TOLERANCES  ARE: / DECIMALS                       ANGLES
- QTS-XXX-XX-XXX-D-XX-X-XX / DWG.  NO. / DESCRIPTION:DO  NOT  SCALE  DRAWING / DEAN P 09-14-2010 31 / SHEET SCALE: 1.5:1
- c:\\enterprisevault\\DWG\\MISC\\MKTG\\QTS-XXX-XX-XXX-D-XX-X-XX-MKT.SLDDRW / NOTES: / 1.         REPRESENTS A CRITICAL DIMENSION. / 2. NOTE DELETED. / 3. NOTE DELETED.
- 18. NOTE DELETED. / 19. TRAYS ARE STANDARD PACKAGING. / 20. ORDERS WILL BE PACKAGED ACCORDING TO THE SAMTEC PACKAGING EFFICIENCY / STANDARDS (SPES) FOUND ON WWW.SAMTEC.COM. / 21.ATTACH LABEL-4X2…
- 21.ATTACH LABEL-4X2 TO EACH REEL. / 22. ANY CHANGES SHOULD ALSO BE APPLIED TO QTH, QTE, QTS, BTH, BTE, AND BTS. / 23. DIMENSION MEASURED, ON EACH BANK, FROM A PLANE CREATED FROM THE SIGNAL PINS.…
- DWG.  NO. / DESCRIPTION: / DO  NOT  SCALE  DRAWING / DEAN P 09-14-2010 32 / SHEET SCALE: 2:1
- DWG.  NO. / DESCRIPTION: / DO  NOT  SCALE  DRAWING / DEAN P 09-14-2010 33 / SHEET SCALE: 1.75:1

### Formulas, equations, and configurable calculations

- No reliable text snippet was automatically extracted for this category. Review the raw page text below.

### Reference designs, applications, and examples

- No reliable text snippet was automatically extracted for this category. Review the raw page text below.

## Page-by-Page Extracted Content

### Page 1

```text
THIS DOCUMENT CONTAINS CONFIDENTIAL AND
PROPRIETARY INFORMATION AND ALL DESIGN,
MANUFACTURING, REPRODUCTION, USE, PATENT RIGHTS
AND SALES RIGHTS ARE EXPRESSLY RESERVED BY SAMTEC,
INC. THIS DOCUMENT SHALL NOT BE DISCLOSED, IN WHOLE
OR PART, TO ANY UNAUTHORIZED PERSON OR ENTITY NOR
REPRODUCED, TRANSFERRED OR INCORPORATED IN ANY
OTHER PROJECT IN ANY MANNER WITHOUT THE EXPRESS
WRITTEN CONSENT OF SAMTEC, INC.
PROPRIETARY NOTE* *
DO NOT
SCALE FROM
THIS PRINT
"B" REF
.7450  REF18.923
.0375 0.953
REF
"E" REF
"A"
"A" T-1G1-XX-XXX
FIG 1
-A: ALIGNMENT PIN OPTION
(QTS-075-01-XXX-D-A SHOWN)
QTS-25-XX-D-XX-A
R
"D" REF
.155  REF3.94
(SEE NOTE 16)
.235  REF5.97
.0080  REF0.203
.639  REF16.24
.7875 20.003
(TYP)
(TYP)
24 EQ SPACES
 @ .0250[0.635]
=.600[15.24]
.0325  REF0.826
C
02
01SEE NOTE 13
No OF POSITIONS
-025, -050, -075,
**-100, **-125
(PER ROW)
** (SEE NOTE 17)
ROW SPECIFICATION
-D: DOUBLE (USE QTS-25-XX-D-XX
                       & QTSH-25-XX-D-XX )
PLATING SPECIFICATION
LEAD STYLE
-01: .1680[4.267]
-02: .2861[7.264]
-03: .4043[10.269]
-04: .6001[15.246]
-05: .7181[18.240]
-06: .8361[21.237]
No OF BANKS
 = SEE SHEET 3
 *
 *
 * = NOT TOOLED
-F: 3µ" FLASH SELECTIVE GOLD IN
     CONTACT AREA, MATTE TIN ON TAIL
     (USE T-1SXX-XX-F & T-1G1-XX-F)
     (SEE NOTE 11)
-L: 10µ" LIGHT SELECTIVE GOLD IN
     CONTACT AREA, MATTE TIN ON TAIL
    (USE T-1SXX-XX-L & T-1G1-XX-L)
-H: 30µ" HEAVY GOLD IN CONTACT AREA,
     3µ" GOLD ON TAIL
    (USE T-1SXX-XX-H & T-1G1-XX-G)
-C: 50µ" HEAVY GOLD IN CONTACT AREA,
     MATTE TIN ON TAIL
    (USE T-1SXX-XX-C & T-1G1-XX-L)
-STL: 30µ" HEAVY SELECTIVE GOLD IN
     CONTACT AREA, TIN LEAD ON TAIL
    (USE T-1SXX-XX-STL & T-1G1-XX-STL)
-FTL: 3µ" FLASH SELECTIVE GOLD IN
     CONTACT AREA, TIN LEAD ON TAIL
    (USE T-1SXX-XX-FTL & T-1G1-XX-FTL)
PACKAGING
BLANK: TRAY (SEE NOTES 19 & 20)
-TR: TAPE & REEL (SEE NOTES 20 & 21)
-FR: FULL REEL QTY TAPE & REEL
       (SEE NOTES 20 & 21)

(-TR & -FR PACKAGING N/A ON
STYLE -05 & -06, 75 POS MAX)
PICK & PLACE OPTION
-K: POLYIMIDE FILM PAD
     (USE K-DOT-.276-.375-.005,
     SEE FIG 3, SHT 2)
OPTION
 -LC: LOCKING CLIPS (SEE NOTE 10 &15)
        (USE LC-08-TM-01)
   -A: ALIGNMENT PINS (SEE NOTE 10)
        (USE QTS-25-XX-D-XX-A)
-GP: GUIDE POST,  (SEE FIG 4, SHT 2)
        (AVAILABLE ON STYLE -01 ONLY)
QTS-XXX-XX-XXX-D-XX-X-XX
.015  REF0.38
"A"
.155-.005
+.003 3.94-0.115
+0.076
(SEE NOTE 16 & 22)
.280 7.11
.035 0.90  REF
SEE TABLE 2
'C'
SECTION "A"-"A"
SCALE 3:1
C
C
.003[.08]
.001[.03]
(SEE NOTE 24)
T-1S56-XX-XXX
C
.035 0.89  REF
.080 2.03
REF
.0010+
-
.0025
.0020 0.025+
-
0.064
0.051
(SEE NOTE 23)
DETAIL 'C'
SCALE 6 : 1
C
SHEET     OF
UNLESS  OTHERWISE  SPECIFIED,
DIMENSIONS ARE IN INCHES.
TOLERANCES  ARE:
DECIMALS                       ANGLES
.XX: .01[.3]               2
.XXX: .005[.13]
.XXXX: .0020[.051]
MATERIAL:
H.635mm DOUBLE ROW HS TERMINAL ASSEMBLY
BY:
QTS-XXX-XX-XXX-D-XX-X-XX
DWG.  NO.
DESCRIPTION:DO  NOT  SCALE  DRAWING
DEAN P 09-14-2010 31
SHEET SCALE: 1.5:1
INSULATOR: LCP, UL94V-0; COLOR: BLACK
TERMINAL: PHOS BRONZE
GROUND PLANE: PHOS BRONZE
c:\enterprisevault\DWG\MISC\MKTG\QTS-XXX-XX-XXX-D-XX-X-XX-MKT.SLDDRW
NOTES:
1.         REPRESENTS A CRITICAL DIMENSION.
2. NOTE DELETED.
3. NOTE DELETED.
4. MINIMUM TERMINAL RETENTION: 6 OZ.
5. MINIMUM GROUND PLANE RETENTION: 1 LB.
6.  NOTE DELETED.
7. PARTS TO BE MOLDED TO POSITION.
8. NOTE DELETED.
9. NOTE DELETED.
10. LEAD STYLES -03 AND -05: TOP BODY (QTS) CANNOT HAVE -A OPTION AND
      -04 AND -06 CAN USE EITHER -A OR -LC BODY.
11. T-1SXX-XX-L CAN BE SUBSTITUTED FOR T-1SXX-XX-F.
12. NOTE DELETED.
13. WINDOW NOT PRESENT ON LEAD STYLES -02 THRU -06 HEIGHT
      PER REV. E OF THE QTS-25-XX-D-XX-X-XX.
14. NOTE DELETED.
15. DUE TO THE HIGH AMOUNT OF INSERTION FORCE NEEDED, THE –LC
      OPTION IS NOT COMPATIBLE WITH AUTO PLACEMENT. SAMTEC
      RECOMMENDS MANUAL PLACEMENT FOR ALL ASSEMBLIES WITH THE –LC OPTION.
16. PIN CAN EXTEND PAST WALL .003[0.08] MAX.
17. AVAILABLE FOR EXISTING CUSTOMERS ONLY.
18. NOTE DELETED.
19. TRAYS ARE STANDARD PACKAGING.
20. ORDERS WILL BE PACKAGED ACCORDING TO THE SAMTEC PACKAGING EFFICIENCY
      STANDARDS (SPES) FOUND ON WWW.SAMTEC.COM.
21.ATTACH LABEL-4X2 TO EACH REEL.
22. ANY CHANGES SHOULD ALSO BE APPLIED TO QTH, QTE, QTS, BTH, BTE, AND BTS.
23. DIMENSION MEASURED, ON EACH BANK, FROM A PLANE CREATED FROM THE SIGNAL PINS.
24. COPLANARITY INCLUDES SIGNAL PINS AND GROUND PLANES.
520 PARK EAST BLVD, NEW ALBANY, IN 47150
PHONE: 812-944-6733       FAX: 812-948-5047
e-Mail: info@SAMTEC.com          code: 55322
REVISION AN
```

### Page 2

```text
THIS DOCUMENT CONTAINS CONFIDENTIAL AND
PROPRIETARY INFORMATION AND ALL DESIGN,
MANUFACTURING, REPRODUCTION, USE, PATENT RIGHTS
AND SALES RIGHTS ARE EXPRESSLY RESERVED BY SAMTEC,
INC. THIS DOCUMENT SHALL NOT BE DISCLOSED, IN WHOLE
OR PART, TO ANY UNAUTHORIZED PERSON OR ENTITY NOR
REPRODUCED, TRANSFERRED OR INCORPORATED IN ANY
OTHER PROJECT IN ANY MANNER WITHOUT THE EXPRESS
WRITTEN CONSENT OF SAMTEC, INC.
PROPRIETARY NOTE* *
"R" REF
.020±.020 0.508±0.50"S"±.020[0.50]
.276  REF7.010
         "C"
(SEE TABLE 3)
.3230 8.204
REF
.055 1.40
REF
QTS-25-01-D-XX-X-GP
"G"REF
"F"REF
.125 3.18
REF.206  REF5.24
.055 1.40
.010 0.25  REF
"E"±.003[0.08]
(SEE TABLE 6, SHT 1)
LC-08-TM-01
FIG 2
-LC: LOCKING CLIP OPTION
(QTS-075-01-XXX-D-LC SHOWN)
(DIFFERENT AS SHOWN, OTHERWISE SAME AS FIG 1)
QTS-25-XX-D-XX
.056 1.42  REF
.0800 2.032
FIG 3
-K: POLYIMIDE FILM PAD
(USE K-DOT-.276-.375-.005)
FIG 4
-GP: GUIDE POST OPTION
(QTS-075-01-XXX-D-GP SHOWN)
(DIFFERENT AS SHOWN, OTHERWISE SAME AS FIG 1)
(AVAILABLE ON STYLE -01 ONLY)
SHEET     OF
H.635mm DOUBLE ROW HS TERMINAL ASSEMBLY
BY:
QTS-XXX-XX-XXX-D-XX-X-XX
DWG.  NO.
DESCRIPTION:
DO  NOT  SCALE  DRAWING
DEAN P 09-14-2010 32
SHEET SCALE: 2:1
REVISION AN
c:\enterprisevault\DWG\MISC\MKTG\QTS-XXX-XX-XXX-D-XX-X-XX-MKT.SLDDRW
520 PARK EAST BLVD, NEW ALBANY, IN 47150
PHONE: 812-944-6733       FAX: 812-948-5047
e-Mail: info@SAMTEC.com          code: 55322
```

### Page 3

```text
THIS DOCUMENT CONTAINS CONFIDENTIAL AND
PROPRIETARY INFORMATION AND ALL DESIGN,
MANUFACTURING, REPRODUCTION, USE, PATENT RIGHTS
AND SALES RIGHTS ARE EXPRESSLY RESERVED BY SAMTEC,
INC. THIS DOCUMENT SHALL NOT BE DISCLOSED, IN WHOLE
OR PART, TO ANY UNAUTHORIZED PERSON OR ENTITY NOR
REPRODUCED, TRANSFERRED OR INCORPORATED IN ANY
OTHER PROJECT IN ANY MANNER WITHOUT THE EXPRESS
WRITTEN CONSENT OF SAMTEC, INC.
PROPRIETARY NOTE* *
.2781 7.064
        REF
.010  REF0.25
.055 1.40
"E"±.003[0.08]
(SEE TABLE 6, SHT 1)
"B"
"B" T-1G1-XX-XXX
QTS-25-02-D-XX (SEE NOTE 10)
QTSH-25-XX-D-XX
LC-08-TM-01
01
02
.2650 6.731
        REF
.035  REF0.89
"E" REF
(SEE TABLE 6, SHT 1)
QTSH-25-XX-D-XX-A
QTS-25-02-D-XX (SEE NOTE 10)
R
(STYLE -03, -04, -05 & -06)
.0525 1.334
        REF
.0375 0.953
        REF
 "A"
.037  REF0.94
.281 7.14
SECTION "B"-"B"
T-1S51-XX-XXX
.003[.08]
.001[.03]
(SEE SHEET 1)
C
SEE TABLE 2
FIG 5
(QTS-075-03-XXX-D-LC SHOWN)
(DIFFERENT AS SHOWN, OTHERWISE SAME AS FIG 1)
FIG 6
(QTS-075-04-XXX-D-A SHOWN)
(DIFFERENT AS SHOWN, OTHERWISE SAME AS FIG 1)
SHEET     OF
H.635mm DOUBLE ROW HS TERMINAL ASSEMBLY
BY:
QTS-XXX-XX-XXX-D-XX-X-XX
DWG.  NO.
DESCRIPTION:
DO  NOT  SCALE  DRAWING
DEAN P 09-14-2010 33
SHEET SCALE: 1.75:1
REVISION  AN
c:\enterprisevault\DWG\MISC\MKTG\QTS-XXX-XX-XXX-D-XX-X-XX-MKT.SLDDRW
520 PARK EAST BLVD, NEW ALBANY, IN 47150
PHONE: 812-944-6733       FAX: 812-948-5047
e-Mail: info@SAMTEC.com          code: 55322
```
