thepinkmile/Enigma-NG/design/Datasheets/TE-1-1674231-1-datasheet.md

# TE Connectivity 1-1674231-1 2.5 mm battery receptacle assembly

## Source

- Source PDF: [TE-1-1674231-1-datasheet.pdf](TE-1-1674231-1-datasheet.pdf)
- Generated Markdown: `TE-1-1674231-1-datasheet.md`
- Page count: 1
- Conversion method: automated local extraction with pypdf and pdfplumber

## Reviewed Summary

- Exact part: TE Connectivity 1-1674231-1.
- Product: 2.5 mm pitch battery connector receptacle assembly, 10 positions.
- Mechanical: reference PCB layout is for 0.8 to 1.2 mm PCB thickness; the drawing shows a 2.5 x 10 = 25 mm contact span and about 32.7 mm overall width.
- Materials / plating: black nylon housing UL94V-0, copper-alloy contacts, nickel underplate, gold on contact area, and tin on lead area.
- Special note: the laser-marking position is called out for 1-1674231-1 only.

## Electrical and Environmental Ratings (Source: Product Spec 108-5775)

> These ratings apply to the full 2.5 mm battery connector family and are sourced from TE Product
> Specification 108-5775 Rev. B2 (18 JUL 2019). See
> [TE-108-5775-product-specification.md](TE-108-5775-product-specification.md) for the full specification.

| Parameter | Rating |
| --- | --- |
| Voltage Rating | 30V DC max |
| **Current Rating** | **6A per contact** |
| **Operating Temperature** | **−20°C to +80°C** |
| Thermal shock qualification | −40°C / 30 min ↔ +85°C / 30 min × 5 cycles — passes (ΔR ≤ 20 mΩ) |
| Temperature rise at rated current | 30°C max at 6A |
| Contact resistance — initial | 30 mΩ max |
| Contact resistance — ΔR after tests | 20 mΩ max |
| Dielectric withstanding voltage | 1 kVAC for 1 min; leakage ≤ 0.5 mA |
| Insulation resistance | 1,000 MΩ min (initial); 100 MΩ min (after tests) |

> **DEFSTAN temperature note:** The operating rating lower bound (−20°C) does not cover the
> DEFSTAN design target (−40°C). The thermal shock test to −40°C is cited as supporting evidence.
> See `Certification_Evidence.md §5.1` for the full exception record.

## Extraction Notes

- Native extraction was empty; OCR text was inserted so the title block and drawing notes are searchable locally.
- As with any drawing-led document, use the original PDF for final tolerances and footprint release.

## Page-by-page extracted content

### Page 1

#### OCR extracted text

```text
4
3
2
RELEASED FOR PUBLICATION
OCT,2002.
LOC
DIST
REVISIONS
COPYRIGHT 2002Tyco Electronics Japan G.K.
ALL RIGHTS RESERVED.
ES
变更
P
LTR
DESCRIPTION
DATE
DWN
APVD
C2
REVISED (ECR-14017817)
24FEB2015
E.L
V.P
+0.1
+0.1
10°
28.7
10
D
@1
0.2x45°
1.4
32.7
5
2.5×10=25
±0.
0.8
基板取付参考寸法
REFERENCE P.C.BOARD LAYOUT
P.C.BOARD THK 0.8~1.2
(VIEW FROM CONNECTOR MOUNTING SIDE)
材料
0.3
：6、94、黑
0.9
：鋼合金
仕上试
：下地2m以上
接触部金0.3μm以上
R1
半田付部锡2～5μm
116742311の指位置
MATERIAL
·HOUSING:6T NYLON、UL94V-O、BLACK
0.2×45°
1.5
·CONTACT:COPPER ALLOY
2.5
△FINISH
B
·CONTACT: Ni ALL OVER UNDER PL. 2μm MIN.
B
2.5
GOLD PL. O.3μm MIN.AT CONTACT AREA
2.5x10=25
TIN PL. 2~5u m AT LEAD AREA
LASER MARKING TO THIS POSITION,
1-1674231-1 ONLY
1-1674231-1
1674231-1
NOTE
PART NO
WIRE RANGE
INSULATION DIA
抱合電镍断面
被覆外径
THIS DRAWING IS A CONTROLLED DOCUMENT.
DWN
010CT02
T.KATANO
TE
TE Connectivity
CHK
020CT02
K.IKEGAMI
:SNOISN3WIO
TOLERANCES UNLESS
单位：耗
OTHERWISE SPECIFIED:
APVD
030CT02
NAME
mm
般公差
K.KODAIRA
名称
2.5mm PITCH BATTERY CONNECTOR
OPLC
± 0.3
PRODUCT SPEC
A
1PLC
± 0.3
裂品规
-5775
RECEPTACLE ASSEMBLY (10P)
A
2 PLC
± 0.3
3 PLC
± 0.3
APPLICATION SPEC
4 PLC
± 0.3
取付適用规格
SIZE
CAGE CODE
DRAWING NO
RESTRICTEDFO
ANGLES
±3
号
MATERIAL
FINISH
WEIGHT
仕上
1.19
g
A3
00779
1674231
材料
RESTRICTED CUSTOMER
SCALE
SHEET
OF
REV
尺度
C2
1470-19(3/11)
```
