thepinkmile/Enigma-NG/design/Datasheets/TE-1123684-7-datasheet.md

# TE Connectivity 1-1123684-7 2.5 mm battery plug assembly

## Source

- Source PDF: [TE-1123684-7-datasheet.pdf](TE-1123684-7-datasheet.pdf)
- Generated Markdown: `TE-1123684-7-datasheet.md`
- Page count: 2
- Conversion method: automated local extraction with pypdf and pdfplumber

## Reviewed Summary

- Exact part: TE Connectivity 1-1123684-7.
- Product: 2.5 mm pitch battery connector plug assembly, 10 positions.
- Mechanical: recommended PCB layout is for 0.8 to 1.2 mm board thickness; this drawing is the mating plug in the same 2.5 mm battery connector family.
- Materials / plating: thermoplastic housing UL94V-0 black, copper-alloy contacts, stainless nut plate, nickel underplate, and gold in the contact area.
- Packaging / wiring: OCR shows reel-packaging details on page 2 plus wire-range / insulation-diameter information on page 1.

## Electrical and Environmental Ratings (Source: Product Spec 108-5775)

> These ratings apply to the full 2.5 mm battery connector family and are sourced from TE Product
> Specification 108-5775 Rev. B2 (18 JUL 2019). See
> [TE-108-5775-product-specification.md](TE-108-5775-product-specification.md) for the full specification.

| Parameter | Rating |
| --- | --- |
| Voltage Rating | 30V DC max |
| **Current Rating** | **6A per contact** |
| **Operating Temperature** | **−20°C to +80°C** |
| Thermal shock qualification | −40°C / 30 min ↔ +85°C / 30 min × 5 cycles — passes (ΔR ≤ 20 mΩ) |
| Temperature rise at rated current | 30°C max at 6A |
| Contact resistance — initial | 30 mΩ max |
| Contact resistance — ΔR after tests | 20 mΩ max |
| Dielectric withstanding voltage | 1 kVAC for 1 min; leakage ≤ 0.5 mA |
| Insulation resistance | 1,000 MΩ min (initial); 100 MΩ min (after tests) |

> **DEFSTAN temperature note:** The operating rating lower bound (−20°C) does not cover the
> DEFSTAN design target (−40°C). The thermal shock test to −40°C is cited as supporting evidence.
> See `Certification_Evidence.md §5.1` for the full exception record.

## Extraction Notes

- Native extraction was empty; OCR text was inserted. Some OCR on bilingual notes remains imperfect, but it is materially more searchable than the original blank extraction.

## Page-by-page extracted content

### Page 1

#### OCR extracted text

```text
4
3
2
TE Connectivity. All Rights Reserved.
REVISIONS
变更
(11.05)
P
LTR
DESCRIPTION
DATE
DWN
APVD
C4
REVISED AS PER ECR-25-239510
27MAR2025
MK
MS
(1.0)
(15.0)
D
D
5
-7/1-7:ASSHOWN
本
±0.05
MYLAR
11123684-7
AS SHOWN
M2
TYP.(2)
0OE
E
K
M
5
5
7
M
5
+ 0.1
10-01.4-0.05
0.1×Y
基板取付推奖寸法
RECOMMENDED P.C.BOARD LAYOUT
P.C.BOARDTHK0.8~1.2
0.7
(VIE記FROM CONNECTOR MOUNTING
SIDE)
5
材料：热可塑性树脂UL94V-0
5
2.5
3.5
色：黑
4
：合金
4
2
4
M
：
仕上：Ni下地
接触部金×y≠
半田付部金
0.8
COLOR;BLACK
2
B
2.3
CONTACT:COPPERALLOY
B
NUT-PLATE:STAINLESSSTEEL
2
 FINISH
CONTACT:NiALLOVERUNDERPL
GOLDPL.AT
CONTACTAREA
1
GOLD FLUSH
PL. AT LEAD AREA
中
中
FOR PACKAGING
TAPE& REEL WITH MYLAR.
28.7
32.9
3
7
25
10
1-1123684 - 7
25
10
1123684-7
WIRE RANGE
28
7
INSULATION DIA
7
6
3
拖合掌控断面精
根覆外径
26.2
30
34
6
9
1123684-6
THIS DRAWING IS A CONTROLLED DOCUMENT.
DWN
12FEB98
T.KUSUHARA
=TE
TE Connectivity
23.7
27.9
3
2
20
8
1123684-5
CHK
12FEB98
I.ENOMOTO
DIMENSIONS:
TOLERANCES UNLESS
单位：耗
OTHERWISE SPECIFIED:
APVO
12FEB98
NAME
21.
2
25
十
29
6
7
1123684-4
mm
一般公差
1.ENOMOTO
名称
PLUG ASSY
e=Pte
± 0.15
PRODUCT SPEC
A
18
7
22
2
15
6
1123684-3
PE
製品规格
2.5mm PITCH BATTERY CONNECTOR (1OPOS.)
3-5775
A
2PLC
16
2
20
24
12.5
5
1123684-2
3Pte
APPLICATION SPEC
6
4PLC
取付適用规格
SIZE
CAGE CODE
DRAWING NO
RESTRICTEDTO
X
ANGLES
13
垂号
2
10
4
1123684-1
MATERIAL
FINISH
材料
仕上
WEIGHT
100779
1123684
D
B
A
N
P /N
POS
CUSTOMER DRAWING
SCALE
2:1
SHEET
0F2
REV
尺度
C4
1470-19 (1/15)
```

### Page 2

#### OCR extracted text

```text
4
3
2
TE Connectivity. All Rights Reserved.
REVISIONS
变更
LTR
DESCRIPTION
DATE
DWN
APVD
SEE SHEET 1
2.0
4.0
1.75
1-1123684-7
D
β 1.5
ASSHOWN
ROUND SPROCKET HOLES
2
56.0
2
ENLONGATED SPROCKET HOLES
中中中中中中中中中中中中中中中中中中中
USER DIRECTION
F UNREELING
56.4
TRAILER
LOADED PRODUCTS
LEADER
200 MM MIN
62.4 REF
500PCS
200 MM MIN
B
TE
B
00800
?
100.0
QTY: 500 pcs per Reel
2000 pcs per Shipping Box
THIS DRAWING IS A CONTROLLED DOCUMENT.
DWN
12FEB98
T.KUSUHARA
=TE
TE Connectivity
CHK
12FEB98
DIMENSIONS:
TOLERANCES UNLESS
I.ENOMOTO
单位：耗
OTHERWISE SPECIFIED:
APVD
12FEB98
NAME
mm
一般公差
1.ENOMOTO
名称
PLUG ASSY
0PLC
土
PRODUCT SPEC
PLC
製品规择
2.5mm PITCH BATTERY CONNECTOR (1OPOS.)
A
108
3-5775
<
2
PLC
土
3 PLC
土
APPLICATION SPEC
4PLC
取付適用规格
SIZE
CAGE CODE
DRAWING NO
RESTRICTED TO
ANGLES
垂号
MATERIAL
FINISH
WEIGHT
0.000000
A300779
1123684
材料
仕上
CUSTOMERDRAWING
SCALE
2:1
SHEET
20 2
REV
尺度
C4
1470-19 (1/15)
```
