thepinkmile/Enigma-NG/.copilot/checkpoints/090-datasheet-design-content-clean.md

<overview>
This session continued the Enigma-NG BOM restructure and RefDes cleanup work. The primary goals were: completing minor BOM/RefDes corrections (Stator SW1/SW2 removal, Encoder BT1–BT64 rename to J3–J66), registering a deferred Rotor variant design todo, creating a persistent repo-local todo tracking file (`.copilot/todo-list.md`), and fixing an incorrect design-specific content leak into the SaiBuy jack socket pseudo-datasheet. All work follows strict directives: no commits without explicit "Let's lock this in", Design Log is append-only, and MPNs/supplier PNs must never be modified without user confirmation.
</overview>

<history>

1. **Session resumed from prior compaction (checkpoint 098/099)**
   - Prior sessions had completed: all 10 board-level BOM tables restructured to 12-column format, DEC-028 reverted, DEC-049 appended, agent-directives.md hardened
   - Pending at resumption: Encoder `BT1–BT64` RefDes correction, todo-list.md creation

2. **Stator SW1/SW2 removal** (carried from prior session summary)
   - User noted SW1 and SW2 on the Stator were shown with strikethrough "Removed — relocated to Settings Board"
   - Directive enforced: design specs are current-state-only snapshots; no historical/removed content
   - Both rows fully deleted from `design/Electronics/Stator/Design_Spec.md`

3. **Encoder BT1–BT64 → J3–J66 rename**
   - `BT` is IPC/EDA standard prefix for batteries only; blade terminals should be `J` (connector)
   - J1 = plugboard panel jacks (off-board), J2 = IDC service connector already taken → blade terminals start at J3, end at J66
   - Applied across 6 files / 10 occurrences
   - DEC-050 appended to Design Log with full rationale, alternatives, and impact list
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
