thepinkmile/Enigma-NG/.copilot/checkpoints/160-jtag-usm-ctl-library-imports-all-board-bom-ticks.md

# Checkpoint 160 — JTAG/USM/CTL Fixes, Library Imports, All-Board BOM Ticks

## Date
2026-05-15

## Summary
Post-Pass-9 housekeeping covering two phases of work: (1) JTAG formatting fixes, USM/CTL BOM
partial ticks, and initial ERJ-2RKF imports; (2) comprehensive Group 1/2/3 library imports and
full all-board `Pending` → `✔` BOM tick sweep. Also includes USM `Last Updated` date correction.

---

## Work Done

### Phase 1 — JTAG/USM/CTL Fixes and Initial Imports

#### design/Electronics/JTAG_Module/Design_Spec.md
- Code block (lines 119-121): C10 column realigned to position 76 across header, R1, R2 rows
- Markdown table (lines 124-145): Signal column widened to 11-char content width throughout
  (header, separator, all 20 data rows)
- `Last Updated`: 2026-05-14 → 2026-05-15

#### design/Electronics/User_Settings_Module/Design_Spec.md — Phase 1 (11 rows)
- BOM ticked Pending → ✔: C1-C4 (CL05B104KB5NNNC), R1 (ERJ-3EKF1002V),
  R18-R29 (ERJ-3EKF1500V), R30-R53 (ERJ-3EKF1000V), R66-R77 (SG73S1ERTTP4702D),
  SW1-SW10 (200MSP1T2B4M2QE), U1-U3 (MCP23017T-E/SO),
  D1-D12 (WP154A4SEJ3VBDZGW/CA), Q1-Q18 (BSS138), R2-R11 (ERJ-2RKF3300X),
  R78-R95 (ERJ-2RKF1003X)
- USM `Last Updated` corrected: 2026-05-27 → 2026-05-15

#### design/Electronics/Controller/Design_Spec.md
- D2 (1.5SMBJ36CA) footprint: Pending → ✔ (confirmed already in library)

#### src/Electronics/Library — ERJ-2RKF3300X, ERJ-2RKF1003X, WP154A4SEJ3VBDZGW/CA
- Both ERJ parts imported into `.lib`, `.kicad_sym` (30,532 → 30,625 lines)
- `ERJ-2RKF1003X.stp` added to `.3dshapes/`
- `WP154A4SEJ3VBDZGW_CA.stp` added to `.3dshapes/`
- `L-154A4SUREQBFZGEC.kicad_mod` added to `.pretty/`

Approved supplier PNs (user-confirmed):

| Part | DigiKey | Mouser | JLCPCB |
|---|---|---|---|
| ERJ-2RKF3300X | P330LCT-ND | 667-ERJ-2RKF3300X | C278592 |
| ERJ-2RKF1003X | P100KLCT-ND | 667-ERJ-2RKF1003X | C242161 |
| BSS138 → BSS138LT1G | BSS138CT-ND | 512-BSS138 | C52895 |
| WP154A4SEJ3VBDZGW/CA | 754-2029-ND | 604-WP154A43VBDZGWCA | C7151795 |
| 1.5SMBJ36CA | 118-1.5SMBJ36CACT-ND | 652-1.5SMBJ36CA | C5439937 |

---

### Phase 2 — Group 1/2/3 Comprehensive Library Imports and All-Board BOM Ticks

#### src/Electronics/Library — 17 parts imported
All imported into `.lib` (3287 → 3704 lines), `.dcm`, and `.kicad_sym` (30,625 → 31,943 lines):

| MPN | Footprint | 3D |
|-----|---|-----|
| ERJ-2RKF1001X | ERJ2RKD1004X (shared, existed) | ✔ |
| ERJ-2RKF75R0X | ERJ2RKD1004X (shared, existed) | ✔ |
| ERJ-2RKF10R0X | ERJ2RKD1004X (shared, existed) | ✔ |
| ERJ-2RKF8202X | ERJ2RKD1004X (shared, existed) | ✔ |
| ERJ-2RKF5232X | ERJ2RKD1004X (shared, existed) | ✔ |
| ERJ-3EKF2200V | RESC1608X55N (shared, existed) | ✔ |
| STD25NF20 | STD25NF20.kicad_mod (NEW) | ✔ |
| HI1206P121R-10 | BEADC3216X130N.kicad_mod (NEW) | ✔ |
| KAM05CR71A105KH | CAPC1005X70N.kicad_mod (NEW) | ✔ |
| 150060VS75000 | LEDC1608X70N.kicad_mod (NEW) | ✔ |
| SQ2319ADS-T1_BE3 | SOT95P237X112-3N.kicad_mod (NEW) | ✔ |
| ERF8-010-05.0-S-DV-K-TR | ERF8-010-XX.X-XXX-DV-K-TR.kicad_mod (NEW) | ✔ |
| BHR-20-VUA | SHDR20W64P254_2X10_3300X880X910P.kicad_mod (NEW) | ✔ |
| CWF1610A-180K | CWF1610A100K.kicad_mod (NEW) | ✔ |
| 219-6LPST (= 219-6LPSTR) | 2196LPST.kicad_mod (NEW) | ✔ |
| PH1-07-UA | HDRV7W64P0X254_1X7_1778X250X850P.kicad_mod (NEW) | ✔ |
| ERM8-005-05.0-S-DV-K-TR | ERM8-005-YYYY-XXX-DV-K-TR.kicad_mod (NEW) | — (no 3D in zip) |

Already in library before this session (confirmed, no import needed): `1.5SMBJ36CA`, `43650-0519`

**Note on 219-6LPST vs 219-6LPSTR**: Downloaded zip and library entry use `219-6LPST` (without
trailing R). BOM MPN `219-6LPSTR` unchanged per PRIMARY directive; same physical part.

#### All-board BOM footprint ticks (~179 rows total across 10 boards)

| Board | Rows ticked |
|---|---|
| Actuation_Module | 11 |
| Controller | 28 |
| Encoder_Module | 9 |
| Extension_Module | 9 |
| JTAG_Module | 8 |
| Power_Module | 62 (incl. J4 / 43650-0519 confirmed in lib) |
| Reflector_Module | 4 |
| Rotor_Module | 15 |
| Stator_Module | 17 |
| User_Settings_Module | 16 |

All 10 `Design_Spec.md` files set to `Last Updated: 2026-05-15`.

---

## Remaining `Pending` Footprints (no downloads available)

| Board | RefDes | MPN | Reason |
|---|---|-----|---|
| Extension | J3 | ERM8-010-05.0-S-DV-K-TR | 10-pin variant — not downloaded |
| Extension | J7, J8 | 2BHR-30-VUA | Not downloaded |
| Reflector | J3 | ERM8-010-05.0-S-DV-K-TR | Not downloaded |
| Reflector | J4 | 2BHR-30-VUA | Not downloaded |
| Rotor | C16-C19 | AC0402FRNPO9BN330 | No download available |
| Rotor | J3 | ERM8-010-05.0-S-DV-K-TR | Not downloaded |
| Rotor | J10 | RS1-07-G | Not downloaded |
| Rotor | R5-R6 | SG73S1ERTTP4701F | No download available |
| Stator | J10 | 2BHR-30-VUA | Not downloaded |
| Stator | J11, J12 | 2195620015 | Not downloaded |

---

## Files Modified

- `src/Electronics/Library/SamacSys_Parts.lib` — 21 new DEF blocks total; 3287 → 3704 lines
- `src/Electronics/Library/SamacSys_Parts.dcm` — 21 new $CMP blocks total
- `src/Electronics/Library/SamacSys_Parts.kicad_sym` — 19 new symbol blocks; 30,532 → 31,943 lines
- `src/Electronics/Library/SamacSys_Parts.pretty\` — 12 new `.kicad_mod` files added
- `src/Electronics/Library/SamacSys_Parts.3dshapes\` — 18 new `.stp` files added
- `design/Electronics/Actuation_Module/Design_Spec.md`
- `design/Electronics/Controller/Design_Spec.md`
- `design/Electronics/Encoder_Module/Design_Spec.md`
- `design/Electronics/Extension_Module/Design_Spec.md`
- `design/Electronics/JTAG_Module/Design_Spec.md`
- `design/Electronics/Power_Module/Design_Spec.md`
- `design/Electronics/Reflector_Module/Design_Spec.md`
- `design/Electronics/Rotor_Module/Design_Spec.md`
- `design/Electronics/Stator_Module/Design_Spec.md`
- `design/Electronics/User_Settings_Module/Design_Spec.md`

---

## Key Numbers
- Next checkpoint: **160** (to be assigned when user approves)
- Next DEC entry: **DEC-073**
- `review-report.md`: ~1487 lines, complete through Pass 9

## Standing Directives (all active)
- PRIMARY: Never modify MPN/supplier PN
- SECONDARY: NEVER git commit/add/unstage; trigger = "Let's lock this in" or "Save state"
- TERTIARY: `design/Design_Log.md` append-only; next entry = DEC-073
- QUATERNARY: Never permanently delete — move to `.recycle-bin/`
- QUINARY: Review sub-agents READ-ONLY
- SENARY: No file changes without explicit user approval
- SEPTENARY: Every sub-agent prompt must start with mandatory preamble block
- OCTONARY: Two-layer todo system (`todo-list.md` table + `.copilot/todos/<id>.md` detail files)
- No unsolicited checkpoints — write only when user approves
