thepinkmile/Enigma-NG/.copilot/checkpoints/174-extension-mechanical-components-final-locked.md

# Checkpoint 174: Extension Mechanical Components Finalised (All Remaining Parts Locked)

**Date**: 2026-06-07  
**Status**: Complete  
**Scope**: Discussion-state completion (no implementation changes — design files remain untouched)

## Summary

Completed the final unresolved discussion item in `.copilot/discussions/extension-mechanical-usage.md`:
all three remaining new component rows (14–17) are now fully specified with confirmed MPNs, manufacturers, and supplier part numbers.

The **New Component Requirements** table (rows 1–18) is now 100% populated with confirmed components across all boards.

## Work Completed

1. **Row 14: Keyboard LEDs (Kingbright APFA2507Y2G2C-C2)**
   - Status: Confirmed with full KiCAD assets (✓ symbol, ✓ footprint, ✓ 3D model)
   - Supplier coverage: Mouser, DigiKey, JLCPCB — all stocked
   - Variant documentation: 26-char (26 LEDs) and 64-char (41 LEDs) explicitly noted

2. **Row 15: Lightboard LEDs (identical Kingbright APFA2507Y2G2C-C2)**
   - Status: Confirmed as identical to row 14, reusing same supplier part numbers and KiCAD assets
   - Variant documentation: 26-char (26 LEDs) and 64-char (41 LEDs) with explicit resistor-value scaling

3. **Row 16: Keyboard LED Current-Limiting Resistor — Yellow (130 Ω, 0402)**
   - **MPN**: Yageo AT0402CRD07130RL
   - **Manufacturer**: Yageo
   - **Supplier PNs**:
     - DigiKey: `AT0402CRD07130RL-ND` (MOQ: 10,000)
     - Mouser: `603-AT0402CRD07130RL` (MOQ: 10,000)
     - JLCPCB: `C2142705` (MOQ: 110)
   - **Specs**: Thin-film ±0.25% tolerance, ±25 ppm/°C TCR, AEC-Q200 automotive grade, 1/16W power rating
   - **Notes**: MOQ documentation explicitly included; achievable with 2 prototype boards minimum
   - **KiCAD Assets**: Pending library import (symbol, footprint, 3D model)
   - **Variant documentation**: 26-char (×26 per board) and 64-char (×41 per board)

4. **Row 17: Keyboard LED Current-Limiting Resistor — Green (120 Ω, 0402)**
   - **MPN**: Yageo AT0402CRD07120RL
   - **Manufacturer**: Yageo
   - **Supplier PNs**:
     - DigiKey: `AT0402CRD07120RL-ND` (MOQ: 10,000)
     - JLCPCB: `C4286960` (MOQ: 90)
     - Mouser: Not Currently Stocking (documented in notes)
   - **Specs**: Thin-film ±0.25% tolerance, ±25 ppm/°C TCR, AEC-Q200 automotive grade, 1/16W power rating
   - **Notes**: MOQ documentation included; achievable with prototype build
   - **KiCAD Assets**: Pending library import (symbol, footprint, 3D model)
   - **Variant documentation**: 26-char (×26 per board) and 64-char (×41 per board)

5. **Datasheet Generation & Validation**
   - Generated markdown datasheets for both Yageo resistors from PDF sources
   - Confirmed electrical specifications against design requirements:
     - 130 Ω / 120 Ω values from E-24 standard series ✓
     - 0402 package (1.0 × 0.5 mm) ✓
     - 1/16W (62.5 mW) power rating handling 13 mW / 12 mW dissipation ✓
     - 50V max operating voltage >> 3.3V application ✓
     - AEC-Q200 qualified ✓

6. **Discussion Cleanup**
   - Removed completed "### 2026-06-04 — Next discussion order" section (all 3 items done)
   - Confirmed all 18 rows in "New Component Requirements" table are now populated and locked

## Critical Context for Next Session

### State of Extension Mechanical Usage Discussion

**Location**: `.copilot/discussions/extension-mechanical-usage.md`

**Current Status**:
- ✅ All 18 rows of "New Component Requirements" table fully populated
- ✅ Entries 1–20 complete (no open discussion items remain in scope)
- ✅ "Next discussion order" section removed (all items closed)
- **NOTE**: This discussion document is NOT ready for design implementation yet — it is still in discussion/pre-design phase

**Signal-Flow & Mapping Authority**:
- Entry 11: Mini-stack J1–J8 connector mappings (authoritative)
- Entry 19: Cypher-owned Input/Output-Cypher interconnect mapping (authoritative)
- Entry 20: Signal-block model + passive base-board mini-stack internal link (authoritative)
- All entries preserved for future reference; no entries modified

### What Must Happen Next

**BEFORE this discussion can be closed and merged into design specifications:**

1. **Library Import Task** (required for design implementation):
   - Yageo AT0402CRD07130RL: create symbol, footprint, and 3D model in both modern and legacy KiCAD library formats
   - Yageo AT0402CRD07120RL: create symbol, footprint, and 3D model in both modern and legacy KiCAD library formats
   - Update row 16 and 17 KiCAD asset columns from `–` to `✓` after import completion

2. **PR Merge Task** (per user instruction):
   - User instructed: "merge a PR with one of the other discussions"
   - This discussion (`extension-mechanical-usage`) will be merged with the other discussion once the PR is complete
   - **Next target**: Get that PR done and merge its discussion thread into the current one

3. **Design Implementation Gate**:
   - Once the library import is complete AND the external PR is merged with this discussion:
   - The combined discussion will be ready for formal implementation (DEC creation, board Design_Spec updates, schematic/PCB changes)
   - Current blockers before implementation:
     - [ ] Yageo resistor symbols/footprints/3D models imported to both KiCAD formats
     - [ ] External PR discussion merged into this discussion
     - [ ] Explicit user implementation approval (SENARY DIRECTIVE)

## Files Updated

- `.copilot/discussions/extension-mechanical-usage.md`
  - Rows 16–17 populated with full MPN / supplier / MOQ details
  - "### 2026-06-04 — Next discussion order" section removed
  - "New Component Requirements" table now 100% complete (18 rows, all locked)

- `.copilot/plan.md` (updated)
- `.copilot/handoff.md` (updated)
- `.copilot/checkpoints/index.md` (new entry added)

## New Datasheets Generated

- `design/Datasheets/VikingTech-TAR_Series-datasheet.md` (130 Ω candidate evaluation)
- `design/Datasheets/Yageo-AT_series-datasheet.md` (final 130 Ω & 120 Ω parts)

## Session State Sync Completed

- **Session-local memory preserved**: All component details, supplier coverage, and MOQ constraints documented in discussion file
- **Handoff clarity**: Next session will NOT need to re-ask for component specifications — all locked in place
- **PR merge roadmap**: User's instruction to merge external PR with this discussion is now documented in repo-local session state

## Implementation Prerequisites Status

| Item | Status | Notes |
| --- | --- | --- |
| All open questions answered | ✅ | 46 discussion entries complete; no unresolved architectural questions remain |
| All new component MPNs confirmed | ✅ | 18 components locked with full supplier part numbers and MOQ |
| KiCAD assets for new components | ⏳ | Yageo resistors pending library import; all others confirmed present |
| Review Pass 11 complete | ⏳ | Blocked by external PR merge; not required before library import |
| Explicit user implementation approval | ⏳ | Required gate; awaits user signal |
| DEC entries drafted | ⏳ | Will be created during implementation phase per TERTIARY DIRECTIVE |

## State After This Checkpoint

- **"Next discussion order"**: All items complete; section removed from discussion file
- **"New Component Requirements" table**: All 18 rows locked; no placeholders remain
- **Remaining blocking work**: 
  1. External PR completion & discussion merge (user instruction)
  2. Yageo resistor library import (KiCAD asset creation)
  3. User implementation approval (design file changes)
