thepinkmile/Enigma-NG/.copilot/checkpoints/086-rotor-j11-j14-renumber-bom-rewrite-complete.md

# Checkpoint 051 — Rotor J11–J14 renumber and BOM rewrite complete

## Status

All Rotor Board B connector renumbering (J7→J11, J8→J12, J9→J13, J10→J14) and Rotor BOM
description cleanup are complete. All files lint-clean.

## Files Modified This Session (checkpoint 050 → 051)

- `design/Electronics/Rotor/Design_Spec.md`
  - §5 BOM table fully rewritten: description cleanup (no circuit-function text), J1–J2/J4–J5/J7–J8/J11–J12/SW1–SW3/U5–U12 merged into ranges, Board B connectors renumbered J11–J14
  - §3.4 J_INT section updated: keying paragraph now explicit J11/J12 male, J13/J14 female; assembly note updated to 8 headers / 240 total; section headers updated to J7/J11, J8/J12, J9/J13, J10/J14; connector lines updated with (J_n) board callouts

- `design/Electronics/Rotor/Board_Layout.md`
  - Board A component summary: J10 reordered to after J9; "J10/J9 male on Board A" note removed
  - Board B ASCII diagram: `[ J10 F ] [ J7 M ] [ J8 M ] [ J9 F ]` → `[ J14 F ] [ J11 M ] [ J12 M ] [ J13 F ]`
  - Board B component summary: J7→J11, J8→J12, J9→J13, J10→J14; reordered J11, J12, J13, J14; "J10/J9 female on Board B" note removed

- `design/Electronics/Consolidated_BOM.md`
  - Board B J rows renumbered: J10→J14, J7–J8→J11–J12, J9→J13; reordered; descriptions updated with mating callouts

- `design/Mechanical/Rotor/Design_Spec.md`
  - Section 6: Updated to describe 8 headers (4 per board); Board A J7–J10 and Board B J11–J14 named with genders; J10/J14 unique footprint keying

- `design/Design_Log.md`
  - DEC-028: Connector count updated from 4 (22 pins) to 8 (44 pins) with explicit Board A/B callouts; section impact updated from J10/J7/J8/J9 to J7–J10 Board A, J11–J14 Board B; Consolidated_BOM impact updated to 240 total headers

- `design/Electronics/Stator/Design_Spec.md`
  - U9+U10-U12 merged to `U9–U12` (done in prior session, confirmed complete)

## Pending Work

- Settings_Board → User_Settings_Module rename (~17 files + Design_Log DEC entry)
- BOM description cleanup for Batches 1–4 boards (flagged as future work, not blocking)
- R2–R7 missing from Board_Layout.md Board A component summary (gap, not blocking)
