thepinkmile/Enigma-NG/.copilot/checkpoints/069-category-b-parts-sourced-datash.md

# Checkpoint 069 — Category B parts sourced, datasheets generated, committed

**Date:** 2026-05-06
**Scope:** All Category B parts for the Rotor board and Settings Board have been fully sourced.
Five new datasheet PDFs have been added, matching markdown companions generated via the canonical
script, and all changes committed.

## Outcome

The electronics deep-review sourcing cycle is now complete for Category A and Category B items.
Category C items remain deferred pending supplier email responses.
The `Consolidated_BOM.md` contains no remaining "Cat B, part TBD" placeholders.

## Approved parts (this session)

| Ref | Value | MPN | DigiKey | Mouser | JLCPCB |
| --- | ----- | --- | --- | --- | --- |
| Rotor L1 | 18 µH 600mA ferrite shielded inductor | Bourns CWF1610A-180K | 118-CWF1610A-180KCT-ND | 652-CWF1610A-180K | global/consignment |
| Rotor C15/C17/C19 | 33 pF NP0 50V 0402 AEC-Q200 | YAGEO AC0402FRNPO9BN330 | 13-AC0402FRNPO9BN330CT-ND | 603-0402FRNPO9BN330 | C1852937 |
| Rotor C20–C31 | 1 µF X7R 0402 AEC-Q200 | Kyocera KAM05CR71A105KH | 478-KAM05CR71A105KHCT-ND | 581-KAM05CR71A105KH | global/consignment |
| Rotor R6/R7 | 4.70 kΩ ±1% 0402 AEC-Q200 thin-film | KOA SG73S1ERTTP4701F | 2019-SG73S1ERTTP4701FTR-ND | 660-SG73S1ERTTP4701F | C6483673 |
| Settings R66–R77 | 47.0 kΩ ±0.5% 0402 AEC-Q200 thin-film | KOA SG73S1ERTTP4702D | 2019-SG73S1ERTTP4702DTR-ND | 660-SG73S1ERTTP4702D | C5915648 |
| Settings Q19–Q30 | P-Channel MOSFET SOT-323 AEC-Q101 | Vishay SQ2319ADS-T1\_BE3 | 742-SQ2319ADS-T1\_BE3CT-ND | 78-SQ2319ADS-T1\_BE3 | C3280190 |

## Files modified / created

### New datasheet PDFs (binary, untracked → tracked)

- `design/Datasheets/Bourns-cwf1610a-datasheet.pdf`
- `design/Datasheets/KAM05CR71A105KH-Datasheet.pdf`
- `design/Datasheets/KOA-SG73S-RT-Datasheet.pdf`
- `design/Datasheets/YAGEO-AC_NP0X7RX7S-datasheet.pdf`
- `design/Datasheets/vishay-sq2319ads-datasheet.pdf`

### New markdown datasheets (generated by canonical script)

- `design/Datasheets/Bourns-cwf1610a-datasheet.md` — Rotor L1
- `design/Datasheets/KAM05CR71A105KH-Datasheet.md` — Rotor C20–C31
- `design/Datasheets/KOA-SG73S-RT-Datasheet.md` — Rotor R6/R7 and Settings R66–R77
- `design/Datasheets/YAGEO-AC_NP0X7RX7S-datasheet.md` — Rotor C15/C17/C19
- `design/Datasheets/vishay-sq2319ads-datasheet.md` — Settings Q19–Q30
- `design/Datasheets/_generated_markdown_inventory.json` — rebuilt to include all 5 new entries

### Design specs and BOM (updated in prior sessions, lint-clean)

- `design/Electronics/Settings_Board/Design_Spec.md` — Q19–Q30 PMOS row updated for SQ2319ADS-T1\_BE3
- `design/Electronics/Consolidated_BOM.md` — SQ2319ADS-T1\_BE3 rows entered; no remaining TBD entries

### Canonical script improvements

- `.copilot/agent-scripts/generate_markdown_datasheets.py` — four fixes:
  1. `pick_title()` now strips trailing punctuation (MD026 prevention)
  2. `pick_title()` now filters out address/contact lines containing `www.`, `fax:`, phone numbers
  3. Page content rendered in ` ```text ``` ` fences (prevents MD004/MD013/MD029/MD034/MD037 in raw pages)
  4. Snippet bullet text escaped via `escape_snippet()`: `*`→`\*`, `_`→`\_`, bare URLs/emails wrapped in `<>`, lines truncated at 195 chars (prevents MD004/MD013/MD034/MD037 in snippet sections)

## Lint status

All 5 new markdown files: **only MD060** errors (pre-existing table-column-style; acceptable across
all generated datasheets including the pre-existing KEM file).

## Next session start point

Read `.copilot/plan.md`, `.copilot/handoff.md`, and this checkpoint.
Category C sourcing items are still pending supplier responses; those will be addressed in a future
session when responses arrive. No other sourcing work is outstanding.
