thepinkmile/Enigma-NG/.copilot/checkpoints/065-extension-am-bom-sync.md

# Checkpoint 065 — Extension review closed, AM BOM sync
## Date
2026-04-26

## Overview
This checkpoint captures the closeout of the non-mechanical Extension notch pass-through review in the
repo-local state and the matching consolidated-BOM completion work for the current shared Actuation
Module baseline.

## Work Done
### Extension review state sync
- Confirmed the non-mechanical Extension notch pass-through todo is closed
- Removed the stale repo-local open-workstream entry that still treated the architectural Extension
  pass-through question as active
- Preserved the separate mechanical Extension workstream because switch / linkage geometry remains a
  later mechanical-design task

### Consolidated BOM completion
- Checked active board BOM tables for open `TBD` / blank-supplier placeholders
- Confirmed the only intentional exception is the distributor-only CM5 row
- Updated the consolidated AM section to include explicit per-board/module quantities and Rev A totals
  for the current two-module baseline

## Validation
- Repo-local `.copilot/` state now matches the SQL todo state for the closed non-mechanical Extension
  review
- The consolidated BOM now records explicit AM quantities for the current Rev A baseline
- Updated repo-local markdown files lint cleanly with the repository markdownlint rules

## Commits
- Pending at checkpoint write time; the next commit should include the AM BOM sync, repo-local state
  refresh, and this checkpoint

## Technical Decisions
- The architectural answer to Extension boundary carry remains the shared local AM approach
- No additional electrical pass-through circuitry is currently required beyond the documented AM host /
  module contract
- Remaining Extension work in this area is mechanical, not electrical

## Open Questions
- Detailed mechanical Extension linkage / switch geometry remains to be defined later
- Coupon / PAS testing coverage still needs its dedicated review pass

## Next Steps
1. Commit the current AM documentation, BOM sync, datasheet, and repo-local checkpoint updates
2. Start the next session from `.copilot/plan.md`, `.copilot/handoff.md`, and this checkpoint
3. Continue with the remaining mechanical Extension workstream or the coupon / PAS testing review

## Files Updated
- `design/Electronics/Consolidated_BOM.md`
- `.copilot/plan.md`
- `.copilot/handoff.md`
- `.copilot/checkpoints/index.md`
- `.copilot/checkpoints/065-extension-am-bom-sync.md`
