thepinkmile/Enigma-NG/.copilot/checkpoints/045-components-todo-coverage-sync.md

# Checkpoint 045 — Components todo coverage sync
## Date
2026-04-16
## Overview
This checkpoint resyncs repo-local `.copilot\` state after the component verification workspace
advanced beyond what was recorded in `plan.md` and the checkpoint history. The handoff should now
reflect that `.copilot/components-todo.md` is no longer just a short TBD list: it includes both the
30-row supplier-detail table and a full BOM coverage checklist.
## Work Done
### Components verification handoff corrected
- Confirmed `.copilot/components-todo.md` now has two layers:
  - a 30-row detailed supplier-verification table
  - a 106-line BOM coverage checklist mirroring the active Consolidated BOM summary
- Confirmed connector verification work has already started in the detailed table
- Verified connector-related rows currently marked `VERIFIED`:
  - row 3 — `J_DSI1`
  - row 5 — `J_CFG` / `J_I2C`
  - row 23 — `J_SERVO`
  - row 26 — `J_FAN`
### Repo-local handoff rules tightened
- Updated `.github/copilot-instructions.md` to make repo-local `.copilot\` syncing explicit
- Clarified that a checkpoint is not complete until the checkpoint file, checkpoint index, plan,
  and related handoff artifacts all exist in repo-local `.copilot\`
### Repo-local `.copilot` guidance aligned
- Updated `.copilot/README.md` to match how the folder is actually being used
- Updated `.copilot/plan.md` so future sessions do not assume the component table is still only
  a 30-row TBD list
## Commits
None. These are repo-local handoff updates only.
## Key Technical Notes
### `.copilot` content review
No credentials, tokens, or API secrets were found in a targeted scan of `.copilot\`.
The folder does contain machine-specific metadata in markdown history, including absolute local
paths and Copilot session UUIDs, so that should still be reviewed before any future decision to
commit `.copilot\` into version control.
### Why this checkpoint was needed
Repo-local handoff state had drifted behind the actual table contents:

- `plan.md` still described `.copilot/components-todo.md` as a 30-row table
- checkpoint history did not yet capture the expansion to BOM-wide coverage tracking

This checkpoint records that expanded scope so later sessions start from the correct assumption.
## Next Steps
1. Continue the manual component re-verification pass from `.copilot/components-todo.md`
2. Promote remaining `NEEDS DETAIL ROW` coverage items into the detailed verification table as needed
3. Decide later whether `.copilot\` should remain gitignored or be normalized for version control
## Files Updated
- `.github/copilot-instructions.md`
- `.copilot/README.md`
- `.copilot/plan.md`
- `.copilot/checkpoints/045-components-todo-coverage-sync.md`
- `.copilot/checkpoints/index.md`
