thepinkmile/Enigma-NG/.copilot/checkpoints/056-component-closeout-and-handoff-consolidation.md

# Checkpoint 056 — Component closeout and handoff consolidation
## Date
2026-04-19
## Overview
This checkpoint closes the repo-local component verification phase and consolidates the Copilot
handoff state into a simpler persistent structure. The old component-tracker and per-topic
historical note files were audited against the active design docs, confirmed to be redundant as
design truth, and removed. A single generic repo-local handoff note now remains in
`.copilot/handoff.md`.
## Work Done
### Component verification closeout
- Removed the final stale resistor bucket rows from the component tracker before retiring it
- Confirmed there were no genuine unresolved component rows still hidden behind those bucket entries
- Verified the active design docs already carried the important final component selections and
  supplier references
### Handoff note audit and consolidation
- Audited:
  - `.copilot/components-todo.md`
  - `.copilot/component-types-summary.md`
  - all markdown files previously under `.copilot/files/`
- Confirmed the design-bearing content from those notes was already represented in the active
  design docs, especially:
  - final Settings Board RGB architecture, address map, resistor values, and current budget
  - 40-position HID keyboard layout and shift-key behavior
  - verified component selections and supplier references
- Added `.copilot/handoff.md` as the single generic repo-local handoff note
- Removed the obsolete note files after the audit
### Repo-local state refresh
- Rewrote `.copilot/plan.md` to reflect the new clean-session starting point
- Updated `.copilot/README.md` so it describes the new handoff layout
- Updated `.copilot/checkpoints/index.md` with this checkpoint
## Validation
- Repo-local `.copilot/` state now contains the updated plan, README, handoff, checkpoint index,
  and this checkpoint file
- The retired note files are gone from the repo-local handoff tree
- The remaining open work is now represented as actual design follow-ups rather than handoff cleanup
## Commits
- Pending at checkpoint write time; the next commit should include the `.copilot/` consolidation
  together with the already-prepared design-document changes in the working tree
## Technical Decisions
- `.copilot/handoff.md` is now the preferred generic persistent handoff note in the repo root
- Historical one-off session notes should not be recreated under `.copilot/files/` unless a future
  task genuinely needs a separate durable artifact
- The active `design/` documents remain the authoritative source of design truth; repo-local
  handoff notes must not become shadow specifications
## Open Questions
- Whether `GND_CHASSIS` rules should remain globally phrased or become more board-specific remains
  open for later review
- The mechanical / architectural follow-up items around Extensions and the Encoder physical split
  are still pending and intentionally not locked by this checkpoint
## Next Steps
1. Create the commit for the current working tree and repo-local handoff sync
2. Start the next session from `.copilot/plan.md`, `.copilot/handoff.md`, and this checkpoint
3. Resume the real open design follow-ups:
   - grounding-rule cleanup
   - rerun deep reviews after future material changes
   - extension mechanics / Encoder split / notch pass-through review
## Files Updated
- `.copilot/README.md`
- `.copilot/handoff.md`
- `.copilot/plan.md`
- `.copilot/checkpoints/index.md`
- `.copilot/checkpoints/056-component-closeout-and-handoff-consolidation.md`
- `.copilot/component-types-summary.md` (deleted)
- `.copilot/components-todo.md` (deleted)
- `.copilot/files/5v-rgb-upgrade-changelog.md` (deleted)
- `.copilot/files/component-batch-1-handoff.md` (deleted)
- `.copilot/files/settings-board-5v-rgb-upgrade.md` (deleted)
