thepinkmile/Enigma-NG/Docs/Electronics/Consolidated_BOM.md

# Enigma-NG Consolidated BOM & Spares

## 1. Critical Spares (MOQ Recommendations)

* **Bourns AC72 TCO:** Order 5 (MOQ) - (2x Spares).
* **Eaton 15F Supercap:** Order 10 (MOQ) - (2x Spares + 2x Testing).
* **Samtec ERM8 (Gold):** Order 3 (MOQ) - (1x Spare).
* **0.1% Thin-Film Resistors:** Order 50 (MOQ) - (High attrition risk).

## 2. Common Passives

* **0.1uF Decoupling:** Samsung CL10B104KB8NNNC (0603).
* **10uF Bulk:** Murata GRM188R61C106MA73D (0603).
* **10k Pull-ups:** Panasonic ERJ-3EKF1002V (0603).
