thepinkmile/Enigma-NG/.copilot/todos/prototype-pcb-manufacturing.md

# Prototype PCB manufacturing (JLCPCB)

**ID:** `prototype-pcb-manufacturing`
**Status:** pending
**Category:** Project Milestone
**Source:** —
**Blocked by:** `review-mounting-holes`, `interim-electronics-review-3`, `bom-pre-prototype-check`, `enc-connector-review-pre-pcb`

---

## Description

Process prototype PCB manufacturing through JLCPCB:

1: Generate manufacturing pack (gerber, pick & place, LCSC BOM)
2: Global Sourcing Part Order
3: Consignment Parts Order
4: Board Orders (one per board)
5: Receive Boards and Inspect
6: Run Board PAS Testing. Note: CoilCraft samples ordered for CTL T1 (POE600F-12L) — Ref: 153954.

## Notes

No additional notes.
