thepinkmile/Enigma-NG/design/Datasheets/Samtec-QSS-QTS-RA-Characterisation-Test-Report.md

# Report Revision: 12/18/2009

## Source

- **Source PDF:** [Samtec-QSS-QTS-RA-Characterisation-Test-Report.pdf](Samtec-QSS-QTS-RA-Characterisation-Test-Report.pdf)
- **Generated Markdown:** `Samtec-QSS-QTS-RA-Characterisation-Test-Report.md`
- **Page count:** 58
- **Conversion method:** automated local PDF text extraction with pypdf/pdfplumber

## PDF Metadata

| Field | Value |
| :--- | :--- |
| Title | Microsoft Word - hsc-report_qssra-qtsra_final-12-18-2009.doc |
| Author | coreyk |
| Subject |  |
| Creator | PScript5.dll Version 5.2.2 |
| Producer | Acrobat Distiller 8.1.0 (Windows) |

## Extracted Technical Index

This markdown datasheet is meant to reduce the need to reopen the PDF during design work.
It preserves design-relevant extracted snippets first, followed by page-by-page text so the source content remains locally searchable.

### Part number and ordering information

- The test fixtures are composed of 4-layer FR-4 material with 50Ω and100Ω signal trace / and pad configurations designed for the electrical characterization of Samtec Hi-Speed / connector product…
- OH – Optimal Horizontal / HDV – High Density Vertical / PPO – Pin Population Option / S – Static (independent of PCB ground)

### Pin, pad, and connection designations

- 520 Park East Blvd. 1-800-SAMTEC-9 (US & Canada) Fax: 812-948-5047 / New Albany IN 47151-1147 USA <SIG@samtec.com> / Report Revision: 12/18/2009 / ©Samtec, Inc. 2005   All Rights Reserved
- ©Samtec, Inc. 2005   All Rights Reserved / High Speed Characterization Report / QSS-050-01-L-D-RA
- Description: / Micro High Speed Interface, Q Strip, 0.635mm Centerline / Right Angle Socket to Right Angle Terminal Connection / High Speed Characterization Report
- Micro High Speed Interface, Q Strip, 0.635mm Centerline / Right Angle Socket to Right Angle Terminal Connection / High Speed Characterization Report / Series:  QSS-RA/QTS-RA Series
- Series:  QSS-RA/QTS-RA Series / Description: , 0.635mm (0.0250”) Pitch, Two Row, Right Angle to Right Angle Connection / Samtec Inc. WWW.SAMTEC.COM Phone: 812-944-6733
- 520 Park East Blvd. 1-800-SAMTEC-9 (US & Canada) Fax: 812-948-5047 / New Albany IN 47151-1147 USA <SIG@samtec.com> / Report Revision: 12/18/2009 / ©Samtec, Inc. 2005 Page:ii All Rights Reserved
- Connector System Speed Rating .................................................................................... 1 / Frequency Domain Data Summary .............................................…
- Frequency Domain Data Summary ................................................................................. 2 / Table 1 - Single-Ended Signaling System Performance (row 1) ..................…
- Table 1 - Single-Ended Signaling System Performance (row 1) ................................. 2 / Table 2 - Differential Signaling System Performance (row 1).....................................…
- Table 2 - Differential Signaling System Performance (row 1)...................................... 2 / Table 3 - Single-Ended Signaling System Performance (row 2) ................................…
- Characterization Details ................................................................................................ 10 / Differential and Single-Ended Data.................................…
- Differential Application – FEXT Configurations ......................................................... 17 / ROW 2, short path ..................................................................…
- 520 Park East Blvd. 1-800-SAMTEC-9 (US & Canada) Fax: 812-948-5047 / New Albany IN 47151-1147 USA <SIG@samtec.com> / Report Revision: 12/18/2009 / ©Samtec, Inc. 2005 Page:iii All Rights Reserved
- ROW 2, short path .................................................................................................... 36 / Differential Application – Impedance..................................…
- 520 Park East Blvd. 1-800-SAMTEC-9 (US & Canada) Fax: 812-948-5047 / New Albany IN 47151-1147 USA <SIG@samtec.com> / Report Revision: 12/18/2009 / ©Samtec, Inc. 2005 Page:iv All Rights Reserved
- Product Description................................................................................................... 40 / Test System Description ..............................................…
- Test System Description ........................................................................................... 40 / PCB-101620-TST Test Fixtures, Row 1, Longer Terminal Contact ............…
- Far-End Crosstalk (TDT)........................................................................................ 53 / Appendix F – Glossary of Terms...............................................…
- 520 Park East Blvd. 1-800-SAMTEC-9 (US & Canada) Fax: 812-948-5047 / New Albany IN 47151-1147 USA <SIG@samtec.com> / Report Revision: 12/18/2009 / ©Samtec, Inc. 2005 Page:1 All Rights Reserved
- Connector Overview / Micro High Speed Q Strip interfaces (QSS-RA socket & QTS-RA terminal) are available / up to 125 contacts per row.    QSS/QTS series connecters include double row vertical, /…

### Specifications, ratings, and operating conditions

- Samtec connectors are most often designed for generic applications, and can be im- / plemented using various signal and ground pin assignments.  In high speed systems, / provisions must be made …
- ing.  For example, in a single-ended system, a pin-out of “SSSS”, or four adjacent single / ended signals, might be encountered, as opposed to the “GSG” and “GSSG” configura- / tions tested in t…
- Crosstalk or coupled noise data is provided for various signal configurations.  All meas- / urements are single disturber. Crosstalk is calculated as a ratio of the input line voltage / to the c…
- Crosstalk or coupled noise data is provided for various signal configurations.  All meas- / urements are single disturber. Crosstalk is calculated as a ratio of the input line voltage / to the c…
- S-parameter and time domain data is available from all test points.  Data contained / within this report comes from one of the two socket paths measured.  Bandwidth ratings / will sometimes vary…

### Dimensions, package, and mechanical information

- Appendix E - Frequency and Time Domain Measurements / In a two row connector series where terminal geometry and dimensions are equal, only / one row is measured.  The following test procedures a…

### Formulas, equations, and configurable calculations

- Characterization Details ................................................................................................ 10 / Differential and Single-Ended Data.................................…
- Single-Ended Application – Insertion Loss................................................................ 14 / Single-Ended Application – Return Loss.............................................…
- Single-Ended Application – Return Loss................................................................... 14 / Single-Ended Application – NEXT Configurations ....................................…
- Differential Application – Insertion Loss .................................................................... 16 / Differential Application – Return Loss .......................................…
- Differential Application – Return Loss ....................................................................... 16 / Differential Application – NEXT Configurations................................…
- Single-Ended Application – Insertion Loss................................................................ 18 / Single-Ended Application – Return Loss.............................................…
- Single-Ended Application – Return Loss................................................................... 18 / Single-Ended Application – NEXT Configurations ....................................…
- Differential Application – Insertion Loss .................................................................... 20 / Differential Application – Return Loss .......................................…
- Differential Application – Return Loss ....................................................................... 20 / Differential Application – NEXT Configurations................................…
- Single-Ended Application – Impedance .................................................................... 23 / Single-Ended Application – Propagation Delay.......................................…
- Single-Ended Application – Propagation Delay......................................................... 23 / Single-Ended Application – NEXT, “Worst Case” Configuration ...........................…
- Single-Ended Application – NEXT, “Worst Case” Configuration ............................... 24 / Single-Ended Application – FEXT, “Worst Case” Configuration................................ 24 / …
- Single-Ended Application – FEXT, “Worst Case” Configuration................................ 24 / Single-Ended Application – NEXT, “Best Case” Configuration ................................. 25 /…
- Single-Ended Application – NEXT, “Best Case” Configuration ................................. 25 / Single-Ended Application – FEXT, “Best Case” Configuration.................................. 25 …
- Single-Ended Application – FEXT, “Best Case” Configuration.................................. 25 / Single-Ended Application – NEXT, “Row 2 to Row 1” Configuration......................... 26 / Si…
- Differential Application – Impedance......................................................................... 28 / Differential Application – Propagation Delay...................................…
- Differential Application – Propagation Delay............................................................. 28 / Differential Application – NEXT, “Worst Case” Configuration........................…
- Differential Application – NEXT, “Worst Case” Configuration.................................... 28 / Differential Application – FEXT, “Worst Case” Configuration..................................…
- Differential Application – FEXT, “Worst Case” Configuration.................................... 29 / Differential Application – NEXT, “Best Case” Configuration...................................…
- Differential Application – NEXT, “Best Case” Configuration...................................... 30 / Differential Application – FEXT, “Best Case” Configuration .................................…

### Reference designs, applications, and examples

- Appendix A – Frequency Domain Response Graphs.................................................... 14 / ROW 1, long path ..........................................................................…
- ROW 1, long path ..................................................................................................... 14 / Single-Ended Application – Insertion Loss.............................…
- Single-Ended Application – Insertion Loss................................................................ 14 / Single-Ended Application – Return Loss.............................................…
- Single-Ended Application – Return Loss................................................................... 14 / Single-Ended Application – NEXT Configurations ....................................…
- Single-Ended Application – FEXT Configurations..................................................... 15 / ROW 1, long path ........................................................................…
- ROW 1, long path ..................................................................................................... 16 / Differential Application – Insertion Loss ............................…
- Differential Application – Insertion Loss .................................................................... 16 / Differential Application – Return Loss .......................................…
- Differential Application – Return Loss ....................................................................... 16 / Differential Application – NEXT Configurations................................…
- ©Samtec, Inc. 2005 Page:iii All Rights Reserved / Single-Ended Application – Insertion Loss................................................................ 18 / Single-Ended Application – Return…
- Single-Ended Application – Insertion Loss................................................................ 18 / Single-Ended Application – Return Loss.............................................…
- Single-Ended Application – Insertion Loss................................................................ 18 / Single-Ended Application – Return Loss.............................................…
- Single-Ended Application – Return Loss................................................................... 18 / Single-Ended Application – NEXT Configurations ....................................…
- Single-Ended Application – FEXT Configurations..................................................... 19 / Row 2, short path........................................................................…
- Row 2, short path...................................................................................................... 20 / Differential Application – Insertion Loss ...........................…
- Differential Application – Insertion Loss .................................................................... 20 / Differential Application – Return Loss .......................................…
- Differential Application – Return Loss ....................................................................... 20 / Differential Application – NEXT Configurations................................…
- Appendix B – Time Domain Response Graphs............................................................. 22 / ROW 1, long path ......................................................................…
- ROW 1, long path ..................................................................................................... 22 / Single-Ended Application – Input Pulse ...............................…
- Single-Ended Application – Input Pulse .................................................................... 22 / Single-Ended Application – Impedance ............................................…
- Single-Ended Application – Impedance .................................................................... 23 / Single-Ended Application – Propagation Delay.......................................…

## Page-by-Page Extracted Content

### Page 1

```text
Samtec Inc. WWW.SAMTEC.COM Phone: 812-944-6733
520 Park East Blvd. 1-800-SAMTEC-9 (US & Canada) Fax: 812-948-5047
New Albany IN 47151-1147 USA SIG@samtec.com
 Report Revision: 12/18/2009
©Samtec, Inc. 2005   All Rights Reserved

High Speed Characterization Report

QSS-050-01-L-D-RA

Mates with
QTS-050-01-L-D-RA

Description:
Micro High Speed Interface, Q Strip, 0.635mm Centerline
Right Angle Socket to Right Angle Terminal Connection
```

### Page 2

```text
High Speed Characterization Report

Series:  QSS-RA/QTS-RA Series
Description: , 0.635mm (0.0250”) Pitch, Two Row, Right Angle to Right Angle Connection

Samtec Inc. WWW.SAMTEC.COM Phone: 812-944-6733
520 Park East Blvd. 1-800-SAMTEC-9 (US & Canada) Fax: 812-948-5047
New Albany IN 47151-1147 USA SIG@samtec.com
 Report Revision: 12/18/2009
©Samtec, Inc. 2005 Page:ii All Rights Reserved

Table of Contents

Connector Overview........................................................................................................ 1
Connector System Speed Rating .................................................................................... 1
Frequency Domain Data Summary ................................................................................. 2
Table 1 - Single-Ended Signaling System Performance (row 1) ................................. 2
Table 2 - Differential Signaling System Performance (row 1)...................................... 2
Table 3 - Single-Ended Signaling System Performance (row 2) ................................. 3
Table 4- Differential Signaling System Performance (row 2)....................................... 3
Bandwidth Chart – Single-Ended & Differential Insertion Loss ................................... 4
Row 1, long path ...................................................................................................... 4
Row 2, short path..................................................................................................... 4
Time Domain Data Summary .......................................................................................... 5
Table 5 - Single-Ended Impedance (Ω) – (row 1) ....................................................... 5
Table 6 - Differential Impedance (Ω) - (row 1)............................................................. 5
Table 7 - Single-Ended Impedance (Ω) – (row 2) ....................................................... 6
Table 8 - Differential Impedance (Ω) – (row 2)............................................................ 6
Table 9 - Single-Ended Crosstalk (%), row 1 .............................................................. 7
Table 10 - Differential Crosstalk (%) row 1.................................................................. 7
Table 11 - Single-Ended Crosstalk (%), row 2 ............................................................ 8
Table 12 - Differential Crosstalk (%), row 2................................................................. 8
Table 13 - Propagation Delay (row 1) ......................................................................... 9
Table 14 - Propagation Delay (row 2) ......................................................................... 9
Characterization Details ................................................................................................ 10
Differential and Single-Ended Data........................................................................... 10
Connector Signal to Ground Ratio ............................................................................ 10
Frequency Domain Data ........................................................................................... 12
Time Domain Data .................................................................................................... 13
Appendix A – Frequency Domain Response Graphs.................................................... 14
ROW 1, long path ..................................................................................................... 14
Single-Ended Application – Insertion Loss................................................................ 14
Single-Ended Application – Return Loss................................................................... 14
Single-Ended Application – NEXT Configurations .................................................... 15
Single-Ended Application – FEXT Configurations..................................................... 15
ROW 1, long path ..................................................................................................... 16
Differential Application – Insertion Loss .................................................................... 16
Differential Application – Return Loss ....................................................................... 16
Differential Application – NEXT Configurations......................................................... 16
Differential Application – FEXT Configurations ......................................................... 17
ROW 2, short path .................................................................................................... 18
```

### Page 3

```text
High Speed Characterization Report

Series:  QSS-RA/QTS-RA Series
Description: , 0.635mm (0.0250”) Pitch, Two Row, Right Angle to Right Angle Connection

Samtec Inc. WWW.SAMTEC.COM Phone: 812-944-6733
520 Park East Blvd. 1-800-SAMTEC-9 (US & Canada) Fax: 812-948-5047
New Albany IN 47151-1147 USA SIG@samtec.com
 Report Revision: 12/18/2009
©Samtec, Inc. 2005 Page:iii All Rights Reserved

Single-Ended Application – Insertion Loss................................................................ 18
Single-Ended Application – Return Loss................................................................... 18
Single-Ended Application – NEXT Configurations .................................................... 19
Single-Ended Application – FEXT Configurations..................................................... 19
Row 2, short path...................................................................................................... 20
Differential Application – Insertion Loss .................................................................... 20
Differential Application – Return Loss ....................................................................... 20
Differential Application – NEXT Configurations......................................................... 21
Differential Application – FEXT Configurations ......................................................... 21
Appendix B – Time Domain Response Graphs............................................................. 22
ROW 1, long path ..................................................................................................... 22
Single-Ended Application – Input Pulse .................................................................... 22
Single-Ended Application – Impedance .................................................................... 23
Single-Ended Application – Propagation Delay......................................................... 23
Single-Ended Application – NEXT, “Worst Case” Configuration ............................... 24
Single-Ended Application – FEXT, “Worst Case” Configuration................................ 24
Single-Ended Application – NEXT, “Best Case” Configuration ................................. 25
Single-Ended Application – FEXT, “Best Case” Configuration.................................. 25
Single-Ended Application – NEXT, “Row 2 to Row 1” Configuration......................... 26
Single-Ended Application – FEXT, “Row 2 to Row 1” Configuration ......................... 26
Row 1, long path....................................................................................................... 27
Differential Application – Input Pulse ........................................................................ 27
Differential Application – Impedance......................................................................... 28
Differential Application – Propagation Delay............................................................. 28
Differential Application – NEXT, “Worst Case” Configuration.................................... 28
Differential Application – FEXT, “Worst Case” Configuration.................................... 29
Differential Application – NEXT, “Best Case” Configuration...................................... 30
Differential Application – FEXT, “Best Case” Configuration ...................................... 30
Differential Application – NEXT, “Row 2 to Row 1”Configuration.............................. 31
Differential Application – FEXT, “Row 2 to Row 1”Configuration .............................. 31
ROW 2, short path .................................................................................................... 32
Single-Ended Application – Impedance .................................................................... 32
Single-Ended Application – Propagation Delay......................................................... 32
Single-Ended Application – NEXT, “Worst Case” Configuration ............................... 33
Single-Ended Application – FEXT, “Worst Case” Configuration................................ 33
Single-Ended Application – NEXT, “Best Case” Configuration ................................. 34
Single-Ended Application – FEXT, “Best Case” Configuration.................................. 34
Single-Ended Application – NEXT, “Row 2 to Row 1” Configuration......................... 35
Single-Ended Application – FEXT, “Row 2 to Row 1” Configuration ......................... 35
ROW 2, short path .................................................................................................... 36
Differential Application – Impedance......................................................................... 36
```

### Page 4

```text
High Speed Characterization Report

Series:  QSS-RA/QTS-RA Series
Description: , 0.635mm (0.0250”) Pitch, Two Row, Right Angle to Right Angle Connection

Samtec Inc. WWW.SAMTEC.COM Phone: 812-944-6733
520 Park East Blvd. 1-800-SAMTEC-9 (US & Canada) Fax: 812-948-5047
New Albany IN 47151-1147 USA SIG@samtec.com
 Report Revision: 12/18/2009
©Samtec, Inc. 2005 Page:iv All Rights Reserved

Differential Application – Propagation Delay............................................................. 36
Differential Application – NEXT, “Worst Case” Configuration.................................... 37
Differential Application – FEXT, “Worst Case” Configuration.................................... 37
Differential Application – NEXT, “Best Case” Configuration...................................... 38
Differential Application – FEXT, “Best Case” Configuration ...................................... 38
Differential Application – NEXT, “Row 2 to Row 1” Configuration ............................. 39
Differential Application – FEXT, “Row 2 to Row 1” Configuration ............................. 39
Appendix C – Product and Test System Descriptions................................................... 40
Product Description................................................................................................... 40
Test System Description ........................................................................................... 40
PCB-101620-TST Test Fixtures, Row 1, Longer Terminal Contact .......................... 41
PCB-101620-TST- Test Fixtures, Row 2, Shorter Terminal Contact......................... 41
PCB Fixture Set I ...................................................................................................... 42
PCB Fixture Set II ..................................................................................................... 44
PCB101748-TST-99 Calibration Standards .............................................................. 46
Appendix D – Test and Measurement Setup................................................................. 47
CSA8000/TDA IConnect Measurements Capability.................................................. 47
Horizontal Orientation Eight Channel 40 GHz Microprobe Setup.............................. 48
Test Instruments ....................................................................................................... 48
Measurement Station Accessories............................................................................ 48
Test Cables & Adapters ............................................................................................ 48
Appendix E - Frequency and Time Domain Measurements.......................................... 49
Sample Preparation .................................................................................................. 49
Frequency (S-Parameter) Domain Procedures......................................................... 49
CSA8000 Setup ..................................................................................................... 49
Insertion Loss (TDA conversion)............................................................................ 50
Return Loss (TDA conversion)............................................................................... 50
Near-End Crosstalk (TDA conversion)................................................................... 51
Far-End Crosstalk (TDA conversion) ..................................................................... 51
Time Domain Procedures ......................................................................................... 52
Impedance (TDR)................................................................................................... 52
Propagation Delay (TDT) ....................................................................................... 52
Near-End Crosstalk (TDT) ..................................................................................... 52
Far-End Crosstalk (TDT)........................................................................................ 53
Appendix F – Glossary of Terms................................................................................... 54
```

### Page 5

```text
High Speed Characterization Report

Series:  QSS-RA/QTS-RA Series
Description: , 0.635mm (0.0250”) Pitch, Two Row, Right Angle to Right Angle Connection

Samtec Inc. WWW.SAMTEC.COM Phone: 812-944-6733
520 Park East Blvd. 1-800-SAMTEC-9 (US & Canada) Fax: 812-948-5047
New Albany IN 47151-1147 USA SIG@samtec.com
 Report Revision: 12/18/2009
©Samtec, Inc. 2005 Page:1 All Rights Reserved

Connector Overview
Micro High Speed Q Strip interfaces (QSS-RA socket & QTS-RA terminal) are available
up to 125 contacts per row.    QSS/QTS series connecters include double row vertical,
right angle and edge-mount styles.  The data presented in this report is applicable only
to a QSS right angle socket connector mated with a QTS right angle terminal connector.

Connector System Speed Rating

QSS-RA / QTS-RA  Series, 0.635mm (0.0250”) Centerline, QSS right angle socket
mated to a QTS right angle terminal connector

Signaling Speed Rating

Long Path, Row 1 4.5 GHz / 9Gbps
Single-Ended:
Short Path, Row 2 4.0 GHz / 8Gbps

Long Path, Row 1 3.5 GHz / 7Gbps
Differential:
Short Path, Row 2 4.5 GHz / 9Gbps

The Speed Rating is based on the -3 dB insertion loss point of the connector system.
The -3 dB point can be used to estimate usable system bandwidth in a typical, two-level
signaling environment.

To calculate the Speed Rating, the measured -3 dB point is rounded-up to the nearest
half-GHz level.  The up rounding corrects for a portion of the test board’s trace loss,
since trace losses are included in the loss data in this report.  The resulting loss value is
then doubled to determine the approximate maximum data rate in Gigabits per second
(Gbps).

For example, a connector with a -3 dB point of 7.8 GHz would have a Speed Rating of 8
GHz/ 16 Gbps.  A connector with a -3 dB point of 7.2 GHz would have a Speed Rating
of 7.5 GHz/15 Gbps.
```

### Page 6

```text
High Speed Characterization Report

Series:  QSS-RA/QTS-RA Series
Description: , 0.635mm (0.0250”) Pitch, Two Row, Right Angle to Right Angle Connection

Samtec Inc. WWW.SAMTEC.COM Phone: 812-944-6733
520 Park East Blvd. 1-800-SAMTEC-9 (US & Canada) Fax: 812-948-5047
New Albany IN 47151-1147 USA SIG@samtec.com
 Report Revision: 12/18/2009
©Samtec, Inc. 2005 Page:2 All Rights Reserved

Frequency Domain Data Summary
[Reference Appendix C of complete report for full description of test boards]

ROW 1

Table 1 - Single-Ended Signaling System Performance (row 1)
Parameter Conf. Source Victim
Insertion Loss rc3-47il probe 3=QSS-RA_47,
probe 5=QTS-RA_47    -3dB @ 4.2 GHz
Return Loss rc3-47rl probe 3=QSS-RA_47,
probe 5=QTS-RA_47    ≤ -3dB to 4.2 GHz
sp3-43nw41 QSS-RA_43 QSS-RA_41  ≤ -6dB to 4.2 GHz
sp3-47nb43 QSS-RA_47 QSS-RA_43  ≤ -22dB to 4.2 GHz Near-End
Crosstalk
sp3-3nx4 QSS-RA_3 QSS-RA_4  ≤ -32dB to 4.2 GHz
sp3-43fw41 QSS-RA_43 QTS-RA_41  ≤ -12dB to 4.2 GHz
sp3-47fb43 QSS-RA_47 QTS-RA_43  ≤ -15dB to 4.2 GHz Far-End
Crosstalk
sp3-3fx4 QSS-RA_3 QTS-RA_4  ≤ -31dB to 4.2 GHz

Table 2 - Differential Signaling System Performance (row 1)
Parameter Conf. Source Victim
Insertion
Loss rc34-9193il probe34=QSS-RA_91-93,
probe56=QTS-RA_91-93   -3dB @ 3.1 GHz
Return Loss rc34-9193rl probe34=QSS-RA_91-93,
probe56=QTS-RA_91-93   ≤ -5dB to 3.1 GHz
sp34-8789nw8385 QSS-RA_87-89  QSS-RA_83-85 ≤ -19dB to 3.1 GHz
sp34-9193nb8587 QSS-RA_91-93 QSS-RA_85-87 ≤ -40dB to 3.1 GHz Near-End
Crosstalk
sp34-35nx46 QSS-RA _3-5 QSS-RA_4-6 ≤ -47dB to 3.1 GHz
sp34-8789fw8385 QSS-RA_ 87-89  QTS-RA_83-85 ≤ -28dB to 3.1 GHz
sp34-9193fb8587 QSS-RA_91-93 QTS-RA_85-87 ≤ -26dB to 3.1 GHz Far-End
Crosstalk
sp34-35fx46 QSS-RA_3-5 QTS-RA_4-6 ≤ -49dB to 3.1 GHz
```

### Page 7

```text
High Speed Characterization Report

Series:  QSS-RA/QTS-RA Series
Description: , 0.635mm (0.0250”) Pitch, Two Row, Right Angle to Right Angle Connection

Samtec Inc. WWW.SAMTEC.COM Phone: 812-944-6733
520 Park East Blvd. 1-800-SAMTEC-9 (US & Canada) Fax: 812-948-5047
New Albany IN 47151-1147 USA SIG@samtec.com
 Report Revision: 12/18/2009
©Samtec, Inc. 2005 Page:3 All Rights Reserved

ROW 2

Table 3 - Single-Ended Signaling System Performance (row 2)
Parameter Conf. Source Victim
Insertion
Loss rc3-24il probe 3=QSS-RA_24
probe 5=QTS-RA_24   -3dB @ 3.7 GHz
Return Loss rc3-24rl probe 3=QSS-RA_24
probe 5=QTS-RA_24    ≤ -7dB to 3.7 GHz
sp3-24nw22 QSS-RA_24 QSS-RA_22  ≤ -7dB to 3.7 GHz
sp3-24nb20 QSS-RA_24 QSS-RA_20  ≤ -7dB to 3.7 GHz Near-End
Crosstalk
sp3-3nx4 QSS-RA_3 QSS-RA_4  ≤ -32dB to 3.7 GHz
sp3-24fw22 QSS-RA_24 QTS-RA_22  ≤ -10dB to 3.7 GHz
sp3-24fb20 QSS-RA_24 QTS-RA_20  ≤ -8dB to 3.7 GHz Far-End
Crosstalk
sp3-3fx4 QSS-RA_3 QTS-RA_4  ≤ -31dB to 3.7 GHz

Table 4- Differential Signaling System Performance (row 2)
Parameter Conf. Source Victim
Insertion
Loss rc34-7476il probe 34=QSS-RA_74-76
probe 56=QTS-RA_74-76   -3dB @ 4.1 GHz
Return
Loss rc34-7476rl probe 34=QSS-RA_74-76
probe 56=QTS-RA_74-76   ≤ -7dB to 4.1 GHz
sp34-7476nw7072 QSS-RA_74-76 QSS-RA_70-72 ≤ -18dB to 4.1 GHz
sp34-7476nb6870 QSS-RA_74-76 QSS-RA_68-70 ≤ -22dB to 4.1 GHz Near-End
Crosstalk
sp34-35nx46 QSS-RA _3-5 QSS-RA_4-6 ≤ -44dB to 4.1 GHz
sp34-7476fw7072 QSS-RA _74-76 QTS-RA_70-72 ≤ -23dB to 4.1 GHz
sp34-7476fb6870 QSS-RA_74-76 QTS-RA_68-70 ≤ -18dB to 4.1 GHz Far-End
Crosstalk
sp34-35fx46 QSS-RA_3-5 QTS-RA_4-6 ≤ -46dB to 4.1 GHz
```

### Page 8

```text
High Speed Characterization Report

Series:  QSS-RA/QTS-RA Series
Description: , 0.635mm (0.0250”) Pitch, Two Row, Right Angle to Right Angle Connection

Samtec Inc. WWW.SAMTEC.COM Phone: 812-944-6733
520 Park East Blvd. 1-800-SAMTEC-9 (US & Canada) Fax: 812-948-5047
New Albany IN 47151-1147 USA SIG@samtec.com
 Report Revision: 12/18/2009
©Samtec, Inc. 2005 Page:4 All Rights Reserved

Bandwidth Chart – Single-Ended & Differential Insertion Loss

Row 1, long path

PCB/Connector Test System
 Single-Ended & Differential Application
QSS-RA mated to QTS-RA (row  1, long pin )
-9
-8
-7
-6
-5
-4
-3
-2
-1
0
1
012345
Frequency (GHz)
Insertion Loss (dB)
rc3-47il
rc34-9193il

Row 2, short path

P C B/Connector Test System
Single Ended & Differential Application
QSS-RA mated to QTS-RA (row  2, short pin)
-9
-8
-7
-6
-5
-4
-3
-2
-1
0
1
012345
Frequency (GHz)
Insertion Loss (dB)
rc3-24il
rc34-7476il
```

### Page 9

```text
High Speed Characterization Report

Series:  QSS-RA/QTS-RA Series
Description: , 0.635mm (0.0250”) Pitch, Two Row, Right Angle to Right Angle Connection

Samtec Inc. WWW.SAMTEC.COM Phone: 812-944-6733
520 Park East Blvd. 1-800-SAMTEC-9 (US & Canada) Fax: 812-948-5047
New Albany IN 47151-1147 USA SIG@samtec.com
 Report Revision: 12/18/2009
©Samtec, Inc. 2005 Page:5 All Rights Reserved

Time Domain Data Summary
[Reference Appendix C of complete report for full description of test boards]

ROW 1
Table 5 - Single-Ended Impedance (Ω) – (row 1)
Signal Risetime 35±5ps 50 ps 100 ps 250 ps 500 ps 750 ps 1 ns
Maximum
Impedance 60.1 54.9 52.6 51.8 51.2 51.0 50.8
Minimum
Impedance 35.2 37.5 39.5 44.4 46.2 47.4 48.1

Single E nded Application
Impedance vs. Risetime
20
30
40
50
60
70
80
35 50 100 250 500 750 1000
Risetim e (pSec)
 Impedance (ohms)
max imum
minimum

Table 6 - Differential Impedance (Ω) - (row 1)
Signal Risetime 35±5ps 50 ps 100 ps 250 ps 500 ps 750 ps 1 ns
Maximum
Impedance 101.9 101.5 101.0 100.5 100.5 100.4 100.4
Minimum
Impedance 55.8 56.9 60.9 68.7 76.6 82.1 85.7

Differential Application
Impedance vs. Risetime
50
60
70
80
90
100
110
120
35 50 100 250 500 750 1000
Risetim e (pSec)
 Impedance (ohms)
max imum
minimum
```

### Page 10

```text
High Speed Characterization Report

Series:  QSS-RA/QTS-RA Series
Description: , 0.635mm (0.0250”) Pitch, Two Row, Right Angle to Right Angle Connection

Samtec Inc. WWW.SAMTEC.COM Phone: 812-944-6733
520 Park East Blvd. 1-800-SAMTEC-9 (US & Canada) Fax: 812-948-5047
New Albany IN 47151-1147 USA SIG@samtec.com
 Report Revision: 12/18/2009
©Samtec, Inc. 2005 Page:6 All Rights Reserved

ROW 2

Table 7 - Single-Ended Impedance (Ω) – (row 2)
Signal Risetime 35±5ps 50 ps 100 ps 250 ps 500 ps 750 ps 1 ns
Maximum
Impedance 53.4 52.9 52.5 51.6 50.8 50.6 49.8
Minimum
Impedance 28.2 30.8 33.8 38.6 42.1 43.9 45.2

Single E nded Application
Impedance vs. Risetime
20
30
40
50
60
70
80
35 50 100 250 500 750 1000
Risetim e (pSec)
 Impedance (ohms)
max imum
minimum

Table 8 - Differential Impedance (Ω) – (row 2)
Signal Risetime 35±5ps 50 ps 100 ps 250 ps 500 ps 750 ps 1 ns
Maximum
Impedance 103.2 102.9 102.6 102.1 101.5 101.1 101.0
Minimum
Impedance 65.5 71.7 76.3 80.0 85.8 89.6 91.9

Differential Application
Impedance vs. Risetime
50
60
70
80
90
100
110
120
35 50 100 250 500 750 1000
Ris etime (pSec)
 Impedance (ohms)
max imum
minimum
```

### Page 11

```text
High Speed Characterization Report

Series:  QSS-RA/QTS-RA Series
Description: , 0.635mm (0.0250”) Pitch, Two Row, Right Angle to Right Angle Connection

Samtec Inc. WWW.SAMTEC.COM Phone: 812-944-6733
520 Park East Blvd. 1-800-SAMTEC-9 (US & Canada) Fax: 812-948-5047
New Albany IN 47151-1147 USA SIG@samtec.com
 Report Revision: 12/18/2009
©Samtec, Inc. 2005 Page:7 All Rights Reserved

Table 9 - Single-Ended Crosstalk (%), row 1
Input
(tr) Source Victim 35±5ps  50ps  100ps  250ps  500ps  750ps  1ns
SE2
to
SE1
QSS-
RA_43
QSS-
RA_41 21.4 19.7 19.0 16.7 11.4 8.4 6.7
SE4
to
SE3
QSS-
RA_47
QSS-
RA_43 5.2 3.2 2.4 1.8 1. 3 < 1.0% < 1.0%
N
E
X
T
SE6
to
SE5
QSS-
RA_4
QSS-
RA_3 < 1.0% < 1.0% < 1.0% < 1. 0% < 1.0% < 1.0% < 1.0%
SE2
to
SE1
QSS-
RA_43
QTS-
RA_41 7.4 4.6 2.3 2.0 < 1. 0% < 1.0% < 1.0%
SE4
to
SE3
QSS-
RA_47
QTS-
RA_43 6.6 4.7 3.0 1.5 < 1. 0% < 1.0% < 1.0%
F
E
X
T
SE6
to
SE5
QSS-
RA_4
QTS-
RA_3 < 1.0% < 1.0% < 1.0% < 1. 0% < 1.0% < 1.0% < 1.0%

Table 10 - Differential Crosstalk (%) row 1
Input
(tr) Source Victim 35±5ps  50ps  100ps  250ps  500ps  750ps  1ns
DP2
to
DP1
QSS-
RA_87-89
QSS-
RA_83-85 6.1 5.4 5.2 4.7 3.5 2.8 2.2
DP4
to
DP3
QSS-
RA_91-93
QSS-
RA_85-87 1.0 < 1.0% < 1.0% < 1.0%  < 1.0% < 1.0% < 1.0%
N
E
X
T
DP6
to
DP5
QSS-
RA_4-6
QSS-
RA_3-5 < 1.0% < 1.0% < 1.0% < 1. 0% < 1.0% < 1.0% < 1.0%
DP2
to
DP1
QSS-
RA_87-89
QTS-
RA_83-85 4.3 3.2 2.3 1.8 1. 3 < 1.0% < 1.0%
DP4
to
DP3
QSS-
RA_91-93
QTS-
RA_85-87 1.3 < 1.0% < 1.0% < 1.0%  < 1.0% < 1.0% < 1.0%
F
E
X
T DP6
to
DP5
QTS-
RA_4-6
QTS-
RA_3-5 < 1.0% < 1.0% < 1.0% < 1. 0% < 1.0% < 1.0% < 1.0%
```

### Page 12

```text
High Speed Characterization Report

Series:  QSS-RA/QTS-RA Series
Description: , 0.635mm (0.0250”) Pitch, Two Row, Right Angle to Right Angle Connection

Samtec Inc. WWW.SAMTEC.COM Phone: 812-944-6733
520 Park East Blvd. 1-800-SAMTEC-9 (US & Canada) Fax: 812-948-5047
New Albany IN 47151-1147 USA SIG@samtec.com
 Report Revision: 12/18/2009
©Samtec, Inc. 2005 Page:8 All Rights Reserved

   Table 11 - Single-Ended Crosstalk (%), row 2
Input
(tr) Source Victim 35±5ps  50ps  100ps  250ps  500ps  750ps  1ns
SE2
to
SE1
QSS-
RA_24
QSS-
RA_22 18.5 16.5 15.2 12.4 7.7 5.4 4.3
SE4
to
SE3
QSS-
RA_24
QSS-
RA_20 10.8 9.0 6.9 3.5 2.2 1.5 1.2
N
E
X
T
SE6
to
SE5
QSS-
RA_4
QSS-
RA_3 < 1.0% < 1.0% < 1.0% < 1. 0% < 1.0% < 1.0% < 1.0%
SE2
to
SE1
QSS-
RA_24
QTS-
RA_22 12.0 10.1 8.6 8.0 3.7 1.9 1.3
SE4
to
SE3
QSS-
RA_24
QTS-
RA_20 12.6 10.4 7.7 4.9 2.4 1.4 1.0
F
E
X
T
SE6
to
SE5
QSS-
RA_4
QTS-
RA_3 < 1.0% < 1.0% < 1.0% < 1. 0% < 1.0% < 1.0% < 1.0%

Table 12 - Differential Crosstalk (%), row 2
Input
(tr) Source Victim 35±5ps  50ps  100ps  250ps  500ps  750ps  1ns
DP2
to
DP1
QSS-
RA_74-76
QSS-
RA_70-72 6.6 5.0 4.3 3.2 2.0 1.5 1.2
DP4
to
DP3
QSS-
RA_74-76
QSS-
RA_68-70 2.3 1.5 1.0 < 1.0% < 1.0% < 1.0% < 1.0%
N
E
X
T
DP6
to
DP5
QSS-
RA_4-6
QSS-
RA_3-5 < 1.0% < 1.0% < 1.0% < 1. 0% < 1.0% < 1.0% < 1.0%
DP2
to
DP1
QSS-
RA_74-76
QTS-
RA_70-72 5.2 3.5 2.2 1.1 < 1. 0% < 1.0% < 1.0%
DP4
to
DP3
QSS-
RA_74-76
QTS-
RA_68-70 3.9 3.1 2.3 1.1 < 1. 0% < 1.0% < 1.0%
F
E
X
T DP6
to
DP5
QSS-
RA_4-6
QTS-
RA_3-5 < 1.0% < 1.0% < 1.0% < 1. 0% < 1.0% < 1.0% < 1.0%
```

### Page 13

```text
High Speed Characterization Report

Series:  QSS-RA/QTS-RA Series
Description: , 0.635mm (0.0250”) Pitch, Two Row, Right Angle to Right Angle Connection

Samtec Inc. WWW.SAMTEC.COM Phone: 812-944-6733
520 Park East Blvd. 1-800-SAMTEC-9 (US & Canada) Fax: 812-948-5047
New Albany IN 47151-1147 USA SIG@samtec.com
 Report Revision: 12/18/2009
©Samtec, Inc. 2005 Page:9 All Rights Reserved

Table 13 - Propagation Delay (row 1)
Configuration Signal Path (Mated Connector
Only)
Single-Ended SE4 probe 3=QSS-RA_47,
probe 5=QTS-RA_47 162ps
Differential  DP4 probe34=QSS-RA_91-93,
probe56=QTS-RA_91-93 156ps

Table 14 - Propagation Delay (row 2)
Configuration Signal Path (Mated Connector
Only)
Single-Ended SE4 probe 3=QSS-RA_24
probe 5=QTS-RA_24 139ps
Differential  DP4 probe 34=QSS-RA_74-76
probe 56=QTS-RA_74-76 102 ps
```

### Page 14

```text
High Speed Characterization Report

Series:  QSS-RA/QTS-RA Series
Description: , 0.635mm (0.0250”) Pitch, Two Row, Right Angle to Right Angle Connection

Samtec Inc. WWW.SAMTEC.COM Phone: 812-944-6733
520 Park East Blvd. 1-800-SAMTEC-9 (US & Canada) Fax: 812-948-5047
New Albany IN 47151-1147 USA SIG@samtec.com
 Report Revision: 12/18/2009
©Samtec, Inc. 2005 Page:10 All Rights Reserved

Characterization Details
This report presents data that characterizes the signal integrity response of a connector
pair in a controlled printed circuit board (PCB) environment.  All efforts are made to re-
veal typical best-case responses inherent to the system under test (SUT).

In this report, the SUT includes the test PCB from drive side probe tip to receive side
probe tip.  PCB effects are not removed or de-embedded from test data. PCB designs
with impedance mismatch, large losses, skew, cross talk, or similar impairments can
have a significant impact on observed test data.  Therefore, great design effort is put
forth to limit these effects in the PCB utilized in these tests. Some board related effects,
such as pad-to-ground capacitance and trace loss, are included in the data presented in
this report. However, other effects, such as via coupling or stub resonance, are not
evaluated here.  Such effects are addressed and characterized fully by the Samtec
Final Inch®
 products.

Additionally, intermediate test signal connections can mask the connectors’ true per-
formance.   Such connection effects are minimized by using high performance test ca-
bles, adapters, and microwave probes.  Where appropriate, calibration and de-
embedding routines are also used to reduce residual effects.

Differential and Single-Ended Data
Most Samtec connectors can be used successfully in both differential and single-ended
applications. However, electrical performance will differ depending on the signal drive
type.  In this report, data is presented for both differential and single-ended drive sce-
narios.

Connector Signal to Ground Ratio
Samtec connectors are most often designed for generic applications, and can be im-
plemented using various signal and ground pin assignments.  In high speed systems,
provisions must be made in the interconnect for signal return currents. Such paths are
often referred to as “ground”. In some connectors, a ground plane or blade, or an outer
shield is used as the signal return, while in others; connector pins are used as signal
returns.  Various combinations of signal pins, ground blades, and shields can also be
utilized.  Electrical performance can vary significantly depending upon the number and
location of ground pins.

In general, the more pins dedicated to ground, the better electrical performance will be.
But dedicating pins to ground reduces signal density of a connector. So, care must be
taken when choosing signal/ground ratios in cost- or density-sensitive applications.
```

### Page 15

```text
High Speed Characterization Report

Series:  QSS-RA/QTS-RA Series
Description: , 0.635mm (0.0250”) Pitch, Two Row, Right Angle to Right Angle Connection

Samtec Inc. WWW.SAMTEC.COM Phone: 812-944-6733
520 Park East Blvd. 1-800-SAMTEC-9 (US & Canada) Fax: 812-948-5047
New Albany IN 47151-1147 USA SIG@samtec.com
 Report Revision: 12/18/2009
©Samtec, Inc. 2005 Page:11 All Rights Reserved

For this connector, the following array configurations are evaluated:

     open pin field X    grounded pin field

P# signal aggressor or signal victim pins

Single-Ended Impedance:
• Well-referenced line (reference SE4, 1:1),

Single-Ended Crosstalk:
• Well-referenced line; mimics 1:1 S :G ratio (reference SE4, 1:1),
• 2:1 S:G ratio (reference SE2 to SE1),

Only one single-ended signal was driven for crosstalk measurements.

Differential Impedance:

• Well-referenced line (reference DP4, 1:1)
```

### Page 16

```text
High Speed Characterization Report

Series:  QSS-RA/QTS-RA Series
Description: , 0.635mm (0.0250”) Pitch, Two Row, Right Angle to Right Angle Connection

Samtec Inc. WWW.SAMTEC.COM Phone: 812-944-6733
520 Park East Blvd. 1-800-SAMTEC-9 (US & Canada) Fax: 812-948-5047
New Albany IN 47151-1147 USA SIG@samtec.com
 Report Revision: 12/18/2009
©Samtec, Inc. 2005 Page:12 All Rights Reserved

Differential Crosstalk:
• Well-referenced line; mimics 1: 1 S:G ratio (reference DP1)
• Higher Signal Density (reference DP2 to DP1)
• Full-Row Differential (reference DP4 to DP3)

Only one differential pair was driven for crosstalk measurements.

*In all cases where a center ground blade is present in the connector it is always
grounded to the PCB. Only one single-ended signal or differential pair was driven for
crosstalk measurements.

Other configurations can be evaluated upon request. Please contact sig@samtec.com

for more information.

In a real system environment, active signals might be located at the outer edges of the
signal contacts of concern, as opposed to the ground signals utilized in laboratory test-
ing.  For example, in a single-ended system, a pin-out of “SSSS”, or four adjacent single
ended signals, might be encountered, as opposed to the “GSG” and “GSSG” configura-
tions tested in the laboratory.  Electrical characteristics in such applications could vary
slightly from laboratory results. But in most applications, performance can safely be con-
sidered equivalent.

Signal Edge Speed (Rise Time):

In pulse signaling applications, the perceived performance of the interconnect, can vary
significantly depending on the edge rate or rise time of the exciting signal.  For this re-
port, the fastest rise time used was 35 +/-5 ps.  Generally, this should demonstrate
worst case performance.

In many systems, the signal edge rate will be significantly slower at the connector than
at the driver launch point. To estimate interconnect performance at other edge rates,
data is provided for several rise times between 30 ps and 1.0 ns.

For this report, measured rise times were at 10%-90% signal levels.

Frequency Domain Data
Frequency domain parameters are helpful in evaluating the connector system’s signal
loss and crosstalk characteristics across a range of sinusoidal frequencies.  In this re-
port, parameters presented in the frequency domain are insertion loss, return loss, and
near-end and far-end crosstalk. Other parameters or formats, such as VSWR or S-
parameters, may be available upon request. Please contact our Signal Integrity Group
at sig@samtec.com
 for more information.
```

### Page 17

```text
High Speed Characterization Report

Series:  QSS-RA/QTS-RA Series
Description: , 0.635mm (0.0250”) Pitch, Two Row, Right Angle to Right Angle Connection

Samtec Inc. WWW.SAMTEC.COM Phone: 812-944-6733
520 Park East Blvd. 1-800-SAMTEC-9 (US & Canada) Fax: 812-948-5047
New Albany IN 47151-1147 USA SIG@samtec.com
 Report Revision: 12/18/2009
©Samtec, Inc. 2005 Page:13 All Rights Reserved

Frequency performance characteristics for the SUT are generated from time domain
measurements using Fourier Transform calculations. Procedures and methods used in
generating the SUT’s frequency domain data are provided in the frequency domain test
procedures in Appendix E of this report.

Time Domain Data
Time Domain parameters indicate impedance mismatch versus length, signal propaga-
tion time, and crosstalk in a pulsed signal environment.  Time Domain data is provided
in Appendix E of this report. Parameters or formats not included in this report may be
available upon request. Please contact our Signal Integrity Group at sig@samtec.com
for more information.

Reference plane impedance is 50 ohms for single-ended measurements and 100 ohms
for differential measurements.   The fastest risetime signal exciting the SUT is 35 ± 5
picoseconds.

In this report, propagation delay is defined as the signal propagation time through the
PCB connector pads and connector pair. It does not include PCB traces. Delay is
measured at 35 ± 5 picoseconds signal risetime.  Delay is calculated as the difference
in time measured between the 50% amplitude levels of the input and output pulses.

Crosstalk or coupled noise data is provided for various signal configurations.  All meas-
urements are single disturber. Crosstalk is calculated as a ratio of the input line voltage
to the coupled line voltage.  The input line is sometimes described as the active or drive
line. The coupled line is sometimes described as the quiet or victim line.   Crosstalk ratio
is tabulated in this report as a percentage.  Measurements are made at both the near-
end and far-end of the SUT.

Data for other configurations may be available. Please contact our Signal Integrity
Group at sig@samtec.com
 for further information.

As a rule of thumb, 10% crosstalk levels are often used as a general first pass limit for
determining acceptable interconnect performance. But modern system crosstalk toler-
ance can vary greatly.  For advice on connector suitability for specific applications,
please contact our Signal Integrity Group at sig@samtec.com
.

Additional information concerning test conditions and procedures is located in the ap-
pendices of this report.  Further information may be obtained by contacting our Signal
Integrity Group at sig@samtec.com
.
```

### Page 18

```text
High Speed Characterization Report

Series:  QSS-RA/QTS-RA Series
Description: , 0.635mm (0.0250”) Pitch, Two Row, Right Angle to Right Angle Connection

Samtec Inc. WWW.SAMTEC.COM Phone: 812-944-6733
520 Park East Blvd. 1-800-SAMTEC-9 (US & Canada) Fax: 812-948-5047
New Albany IN 47151-1147 USA SIG@samtec.com
 Report Revision: 12/18/2009
©Samtec, Inc. 2005 Page:14 All Rights Reserved

Appendix A – Frequency Domain Response Graphs

ROW 1, long path

Single-Ended Application – Insertion Loss
Configuration: probe 3=QSS-RA_47, probe 5=QTS-RA_47
P C B/Connector Test System
Single Ended Application
QSS-RA mated to QTS-RA (row  1, long pin )
-9
-8
-7
-6
-5
-4
-3
-2
-1
0
1
012345
Frequency (GHz)
Insertion Loss(dB)
rc3-47il

Single-Ended Application – Return Loss
Configuration: probe 3=QSS-RA_47, probe 5=QTS-RA_47
P C B/Connector Test System
Single Ended Application
QSS-RA mated to QTS-RA (row  1, long pin )
-80
-70
-60
-50
-40
-30
-20
-10
0
012345
Frequency (GHz)
Return Loss (dB)
rc3-47rl
```

### Page 19

```text
High Speed Characterization Report

Series:  QSS-RA/QTS-RA Series
Description: , 0.635mm (0.0250”) Pitch, Two Row, Right Angle to Right Angle Connection

Samtec Inc. WWW.SAMTEC.COM Phone: 812-944-6733
520 Park East Blvd. 1-800-SAMTEC-9 (US & Canada) Fax: 812-948-5047
New Albany IN 47151-1147 USA SIG@samtec.com
 Report Revision: 12/18/2009
©Samtec, Inc. 2005 Page:15 All Rights Reserved

Single-Ended Application – NEXT Configurations
worse case QSS-RA_43 QSS-RA_41
best case  QSS-RA_47 QSS-RA_43
row 2 to 1  QSS-RA_4 QSS-RA_3

PCB/Connector Test System
Single Ended Application
QFS-RA mated to QMS-RA (row  1, long pin )
-100
-90
-80
-70
-60
-50
-40
-30
-20
-10
0
0123456
Frequency (GHz)
Near-End Crosstalk (dB)
sp-c3-43-nw -45
sp-c3-43-nb-47
sp-c3-4-nx-3

Single-Ended Application – FEXT Configurations
worse case QSS-RA_43 QTS-RA_41
best case  QSS-RA_47 QTS-RA_43
row 2 to 1  QSS-RA_4 QTS-RA_3
P C B/Connector Test System
Single Ended Application
QSS-RA mated to QTS-RA (row  1, long pin )
-100
-90
-80
-70
-60
-50
-40
-30
-20
-10
0
012345
Frequency (GHz)
Far-End Crosstalk (dB)
sp3-43fw 41
sp3-47fb43
sp3-4fx3
```

### Page 20

```text
High Speed Characterization Report

Series:  QSS-RA/QTS-RA Series
Description: , 0.635mm (0.0250”) Pitch, Two Row, Right Angle to Right Angle Connection

Samtec Inc. WWW.SAMTEC.COM Phone: 812-944-6733
520 Park East Blvd. 1-800-SAMTEC-9 (US & Canada) Fax: 812-948-5047
New Albany IN 47151-1147 USA SIG@samtec.com
 Report Revision: 12/18/2009
©Samtec, Inc. 2005 Page:16 All Rights Reserved

ROW 1, long path

Differential Application – Insertion Loss
Configuration: probe34=QSS-RA_91-93, probe56=QTS-RA_91-93
PCB/Connector Test System
 Differential Application
QSS-RA mated to QTS-RA (row  1, long pin )
-9
-8
-7
-6
-5
-4
-3
-2
-1
0
1
012345
Frequency (GHz)
Insertion Loss (dB)
rc34-9193il

Differential Application – Return Loss
Configuration: probe34=QSS-RA_91-93, probe56=QTS-RA_91-93
P C B/Connector Test System
 Differential Application
QSS-RA mated to QTS-RA (row  1, long pin )
-80
-70
-60
-50
-40
-30
-20
-10
0
012345
Frequency (GHz)
Return Loss (dB)
rc34-9193rl

Differential Application – NEXT Configurations
worse case QSS-RA_87-89  QSS-RA_83-85
```

### Page 21

```text
High Speed Characterization Report

Series:  QSS-RA/QTS-RA Series
Description: , 0.635mm (0.0250”) Pitch, Two Row, Right Angle to Right Angle Connection

Samtec Inc. WWW.SAMTEC.COM Phone: 812-944-6733
520 Park East Blvd. 1-800-SAMTEC-9 (US & Canada) Fax: 812-948-5047
New Albany IN 47151-1147 USA SIG@samtec.com
 Report Revision: 12/18/2009
©Samtec, Inc. 2005 Page:17 All Rights Reserved

best case  QSS-RA_91-93 QSS-RA_85-87
row 2 to 1 QSS-RA_4-6 QSS-RA_3-5
P C B/Connector Test System
 Differential Application
QSS-RA mated to QTS-RA (row  1, long pin )
-100
-90
-80
-70
-60
-50
-40
-30
-20
-10
0
012345
Frequency (GHz)
Near-End Crosstalk (dB)
sp34-8789nw 8385
sp34-9193nb8587
sp34-46nx35

Differential Application – FEXT Configurations
worse case QSS-RA_87-89  QTS-RA_83-85
best case  QSS-RA_91-93 QTS-RA_85-87
row 2 to 1 QSS-RA_4-6 QTS-RA_3-5
P C B/Connector Test System
 Differential Application
QSS-RA mated to QTS-RA (row  1, long pin )
-100
-90
-80
-70
-60
-50
-40
-30
-20
-10
0
012345
Frequency (GHz)
Far-End Crosstalk (dB)
sp34-8789fw 8385
sp34-9193fb8587
sp34-46fx35
```

### Page 22

```text
High Speed Characterization Report

Series:  QSS-RA/QTS-RA Series
Description: , 0.635mm (0.0250”) Pitch, Two Row, Right Angle to Right Angle Connection

Samtec Inc. WWW.SAMTEC.COM Phone: 812-944-6733
520 Park East Blvd. 1-800-SAMTEC-9 (US & Canada) Fax: 812-948-5047
New Albany IN 47151-1147 USA SIG@samtec.com
 Report Revision: 12/18/2009
©Samtec, Inc. 2005 Page:18 All Rights Reserved

ROW 2, short path

Single-Ended Application – Insertion Loss
Configuration probe 3=QSS-RA_24, probe 5=QTS-RA_24
PCB/Connector Test System
Single Ended Application
QSS-RA mated to QTS-RA (row  2, short pin)
-9
-8
-7
-6
-5
-4
-3
-2
-1
0
1
012345
Frequency (GHz)
Insertion Loss(dB)
rc3-24il

Single-Ended Application – Return Loss
Configuration: probe 3=QSS-RA_24, probe 5=QTS-RA_24
P C B/Connector Test System
Single Ended Application
QSS-RA mated to QTS-RA (row  2, short pin)
-80
-70
-60
-50
-40
-30
-20
-10
0
012345
Frequency (GHz)
Return Loss (dB)
rc3-24rl
```

### Page 23

```text
High Speed Characterization Report

Series:  QSS-RA/QTS-RA Series
Description: , 0.635mm (0.0250”) Pitch, Two Row, Right Angle to Right Angle Connection

Samtec Inc. WWW.SAMTEC.COM Phone: 812-944-6733
520 Park East Blvd. 1-800-SAMTEC-9 (US & Canada) Fax: 812-948-5047
New Albany IN 47151-1147 USA SIG@samtec.com
 Report Revision: 12/18/2009
©Samtec, Inc. 2005 Page:19 All Rights Reserved

Single-Ended Application – NEXT Configurations
worse case QSS-RA_24 QSS-RA_22
best case  QSS-RA_24 QSS-RA_20
row 2 to 1 QSS-RA_4 QSS-RA_3
P C B/Connector Test System
Single Ended Application
QSS-RA mated to QTS-RA (row  2, short pin)
-100
-90
-80
-70
-60
-50
-40
-30
-20
-10
0
012345
Frequency (GHz)
Near-End Crosstalk (dB)
sp3-24nw 22
sp3-24nb20
sp3-4nx3

Single-Ended Application – FEXT Configurations
worse case QSS-RA_24 QTS-RA_22
best case  QSS-RA_24 QTS-RA_20
row 2 to 1 QSS-RA_4 QTS-RA_3
PCB/Connector Test System
Single Ended Application
QSS-RA mated to QTS-RA (row  2, short pin)
-100
-90
-80
-70
-60
-50
-40
-30
-20
-10
0
012345
Frequency (GHz)
Far-End Crosstalk (dB)
sp3-24fw 22
sp3-24fb20
sp3-4fx3
```

### Page 24

```text
High Speed Characterization Report

Series:  QSS-RA/QTS-RA Series
Description: , 0.635mm (0.0250”) Pitch, Two Row, Right Angle to Right Angle Connection

Samtec Inc. WWW.SAMTEC.COM Phone: 812-944-6733
520 Park East Blvd. 1-800-SAMTEC-9 (US & Canada) Fax: 812-948-5047
New Albany IN 47151-1147 USA SIG@samtec.com
 Report Revision: 12/18/2009
©Samtec, Inc. 2005 Page:20 All Rights Reserved

Row 2, short path

Differential Application – Insertion Loss
Configuration: probe 34=QSS-RA_74-76, probe 56=QTS-RA_74-76
PCB/Connector Test System
 Differential Application
QSS-RA mated to QTS-RA (row  2, short pin)
-9
-8
-7
-6
-5
-4
-3
-2
-1
0
1
012345
Frequency (GHz)
Insertion Loss (dB)
rc34-7476il

Differential Application – Return Loss
Configuration: probe 34=QSS-RA_74-76, probe 56=QTS-RA_74-76
PCB/Connector Test System
 Differential Application
QSS-RA mated to QTS-RA (row  2, short pin)
-80
-70
-60
-50
-40
-30
-20
-10
0
012345
Frequency (GHz)
Return Loss (dB)
rc34-7476rl
```

### Page 25

```text
High Speed Characterization Report

Series:  QSS-RA/QTS-RA Series
Description: , 0.635mm (0.0250”) Pitch, Two Row, Right Angle to Right Angle Connection

Samtec Inc. WWW.SAMTEC.COM Phone: 812-944-6733
520 Park East Blvd. 1-800-SAMTEC-9 (US & Canada) Fax: 812-948-5047
New Albany IN 47151-1147 USA SIG@samtec.com
 Report Revision: 12/18/2009
©Samtec, Inc. 2005 Page:21 All Rights Reserved

Differential Application – NEXT Configurations
worse case QSS-RA_74-76 QSS-RA_70-72
best case  QSS-RA_74-76 QSS-RA_68-70
row 2 to 1 QSS-RA_4-6 QSS-RA_3-5
P C B/Connector Test System
 Differential Application
QSS-RA mated to QTS-RA (row  2, short pin)
-100
-90
-80
-70
-60
-50
-40
-30
-20
-10
0
012345
Frequency (GHz)
Near-End Crosstalk (dB)
sp34-7476nw 7072
sp34-7476nb6870
sp34-46nx35

Differential Application – FEXT Configurations
worse case QSS-RA_74-76 QTS-RA_70-72
best case  QSS-RA_74-76 QTS-RA_68-70
row 2 to 1 QSS-RA_4-6 QTS-RA_3-5
PCB/Connector Test System
 Differential Application
QSS-RA mated to QTS-RA (row  2, short pin)
-100
-90
-80
-70
-60
-50
-40
-30
-20
-10
0
012345
Frequency (GHz)
Far-End Crosstalk (dB)
sp34-7476fw 7072
sp34-7476fb6870
sp34-46fx35
```

### Page 26

```text
High Speed Characterization Report

Series:  QSS-RA/QTS-RA Series
Description: , 0.635mm (0.0250”) Pitch, Two Row, Right Angle to Right Angle Connection

Samtec Inc. WWW.SAMTEC.COM Phone: 812-944-6733
520 Park East Blvd. 1-800-SAMTEC-9 (US & Canada) Fax: 812-948-5047
New Albany IN 47151-1147 USA SIG@samtec.com
 Report Revision: 12/18/2009
©Samtec, Inc. 2005 Page:22 All Rights Reserved

Appendix B – Time Domain Response Graphs

ROW 1, long path
Single-Ended Application – Input Pulse
```

### Page 27

```text
High Speed Characterization Report

Series:  QSS-RA/QTS-RA Series
Description: , 0.635mm (0.0250”) Pitch, Two Row, Right Angle to Right Angle Connection

Samtec Inc. WWW.SAMTEC.COM Phone: 812-944-6733
520 Park East Blvd. 1-800-SAMTEC-9 (US & Canada) Fax: 812-948-5047
New Albany IN 47151-1147 USA SIG@samtec.com
 Report Revision: 12/18/2009
©Samtec, Inc. 2005 Page:23 All Rights Reserved

Single-Ended Application – Impedance
Configuration: probe 3=QSS-RA_47, probe 5=QTS-RA_47

Single-Ended Application – Propagation Delay
Configuration: port probe 3=QSS-RA_47, probe 5=QTS-RA_47
```

### Page 28

```text
High Speed Characterization Report

Series:  QSS-RA/QTS-RA Series
Description: , 0.635mm (0.0250”) Pitch, Two Row, Right Angle to Right Angle Connection

Samtec Inc. WWW.SAMTEC.COM Phone: 812-944-6733
520 Park East Blvd. 1-800-SAMTEC-9 (US & Canada) Fax: 812-948-5047
New Albany IN 47151-1147 USA SIG@samtec.com
 Report Revision: 12/18/2009
©Samtec, Inc. 2005 Page:24 All Rights Reserved

Single-Ended Application – NEXT, “Worst Case” Configuration
QSS-RA_43 QSS-RA_41

Single-Ended Application – FEXT, “Worst Case” Configuration
QSS-RA_43 QTS-RA_41
```

### Page 29

```text
High Speed Characterization Report

Series:  QSS-RA/QTS-RA Series
Description: , 0.635mm (0.0250”) Pitch, Two Row, Right Angle to Right Angle Connection

Samtec Inc. WWW.SAMTEC.COM Phone: 812-944-6733
520 Park East Blvd. 1-800-SAMTEC-9 (US & Canada) Fax: 812-948-5047
New Albany IN 47151-1147 USA SIG@samtec.com
 Report Revision: 12/18/2009
©Samtec, Inc. 2005 Page:25 All Rights Reserved

Single-Ended Application – NEXT, “Best Case” Configuration
QSS-RA_47 QSS-RA_43

Single-Ended Application – FEXT, “Best Case” Configuration
QSS-RA_47 QTS-RA_43
```

### Page 30

```text
High Speed Characterization Report

Series:  QSS-RA/QTS-RA Series
Description: , 0.635mm (0.0250”) Pitch, Two Row, Right Angle to Right Angle Connection

Samtec Inc. WWW.SAMTEC.COM Phone: 812-944-6733
520 Park East Blvd. 1-800-SAMTEC-9 (US & Canada) Fax: 812-948-5047
New Albany IN 47151-1147 USA SIG@samtec.com
 Report Revision: 12/18/2009
©Samtec, Inc. 2005 Page:26 All Rights Reserved

Single-Ended Application – NEXT, “Row 2 to Row 1” Configuration
QSS-RA_4 QSS-RA_3

Single-Ended Application – FEXT, “Row 2 to Row 1” Configuration
QSS-RA_4 QTS-RA_3
```

### Page 31

```text
High Speed Characterization Report

Series:  QSS-RA/QTS-RA Series
Description: , 0.635mm (0.0250”) Pitch, Two Row, Right Angle to Right Angle Connection

Samtec Inc. WWW.SAMTEC.COM Phone: 812-944-6733
520 Park East Blvd. 1-800-SAMTEC-9 (US & Canada) Fax: 812-948-5047
New Albany IN 47151-1147 USA SIG@samtec.com
 Report Revision: 12/18/2009
©Samtec, Inc. 2005 Page:27 All Rights Reserved

Row 1, long path
Differential Application – Input Pulse
```

### Page 32

```text
High Speed Characterization Report

Series:  QSS-RA/QTS-RA Series
Description: , 0.635mm (0.0250”) Pitch, Two Row, Right Angle to Right Angle Connection

Samtec Inc. WWW.SAMTEC.COM Phone: 812-944-6733
520 Park East Blvd. 1-800-SAMTEC-9 (US & Canada) Fax: 812-948-5047
New Albany IN 47151-1147 USA SIG@samtec.com
 Report Revision: 12/18/2009
©Samtec, Inc. 2005 Page:28 All Rights Reserved

Differential Application – Impedance
Configuration: probe34=QSS-RA_91-93, probe56=QTS-RA_91-93

Differential Application – Propagation Delay
Configuration: probe34=QSS-RA_91-93, probe56=QTS-RA_91-93

Differential Application – NEXT, “Worst Case” Configuration
QSS-RA_87-89  QSS-RA_83-85
```

### Page 33

```text
High Speed Characterization Report

Series:  QSS-RA/QTS-RA Series
Description: , 0.635mm (0.0250”) Pitch, Two Row, Right Angle to Right Angle Connection

Samtec Inc. WWW.SAMTEC.COM Phone: 812-944-6733
520 Park East Blvd. 1-800-SAMTEC-9 (US & Canada) Fax: 812-948-5047
New Albany IN 47151-1147 USA SIG@samtec.com
 Report Revision: 12/18/2009
©Samtec, Inc. 2005 Page:29 All Rights Reserved

Differential Application – FEXT, “Worst Case” Configuration
QSS-RA_87-89  QTS-RA_83-85
```

### Page 34

```text
High Speed Characterization Report

Series:  QSS-RA/QTS-RA Series
Description: , 0.635mm (0.0250”) Pitch, Two Row, Right Angle to Right Angle Connection

Samtec Inc. WWW.SAMTEC.COM Phone: 812-944-6733
520 Park East Blvd. 1-800-SAMTEC-9 (US & Canada) Fax: 812-948-5047
New Albany IN 47151-1147 USA SIG@samtec.com
 Report Revision: 12/18/2009
©Samtec, Inc. 2005 Page:30 All Rights Reserved

Differential Application – NEXT, “Best Case” Configuration
QSS-RA_91-93 QSS-RA_85-87

Differential Application – FEXT, “Best Case” Configuration
QSS-RA_91-93 QTS-RA_85-87
```

### Page 35

```text
High Speed Characterization Report

Series:  QSS-RA/QTS-RA Series
Description: , 0.635mm (0.0250”) Pitch, Two Row, Right Angle to Right Angle Connection

Samtec Inc. WWW.SAMTEC.COM Phone: 812-944-6733
520 Park East Blvd. 1-800-SAMTEC-9 (US & Canada) Fax: 812-948-5047
New Albany IN 47151-1147 USA SIG@samtec.com
 Report Revision: 12/18/2009
©Samtec, Inc. 2005 Page:31 All Rights Reserved

Differential Application – NEXT, “Row 2 to Row 1”Configuration
QSS-RA_4-6 QSS-RA_3-5

Differential Application – FEXT, “Row 2 to Row 1”Configuration
QSS-RA_4-6 QTS-RA_3-5
```

### Page 36

```text
High Speed Characterization Report

Series:  QSS-RA/QTS-RA Series
Description: , 0.635mm (0.0250”) Pitch, Two Row, Right Angle to Right Angle Connection

Samtec Inc. WWW.SAMTEC.COM Phone: 812-944-6733
520 Park East Blvd. 1-800-SAMTEC-9 (US & Canada) Fax: 812-948-5047
New Albany IN 47151-1147 USA SIG@samtec.com
 Report Revision: 12/18/2009
©Samtec, Inc. 2005 Page:32 All Rights Reserved

ROW 2, short path
Single-Ended Application – Impedance
Configuration: probe 3=QSS-RA_24, probe 5=QTS-RA_24

Single-Ended Application – Propagation Delay
Configuration: probe 3=QSS-RA_24, probe 5=QTS-RA_24
```

### Page 37

```text
High Speed Characterization Report

Series:  QSS-RA/QTS-RA Series
Description: , 0.635mm (0.0250”) Pitch, Two Row, Right Angle to Right Angle Connection

Samtec Inc. WWW.SAMTEC.COM Phone: 812-944-6733
520 Park East Blvd. 1-800-SAMTEC-9 (US & Canada) Fax: 812-948-5047
New Albany IN 47151-1147 USA SIG@samtec.com
 Report Revision: 12/18/2009
©Samtec, Inc. 2005 Page:33 All Rights Reserved

Single-Ended Application – NEXT, “Worst Case” Configuration
QSS-RA_74-76 QSS-RA_70-72

Single-Ended Application – FEXT, “Worst Case” Configuration
QSS-RA_74-76 QTS-RA_70-72
```

### Page 38

```text
High Speed Characterization Report

Series:  QSS-RA/QTS-RA Series
Description: , 0.635mm (0.0250”) Pitch, Two Row, Right Angle to Right Angle Connection

Samtec Inc. WWW.SAMTEC.COM Phone: 812-944-6733
520 Park East Blvd. 1-800-SAMTEC-9 (US & Canada) Fax: 812-948-5047
New Albany IN 47151-1147 USA SIG@samtec.com
 Report Revision: 12/18/2009
©Samtec, Inc. 2005 Page:34 All Rights Reserved

Single-Ended Application – NEXT, “Best Case” Configuration
QSS-RA_74-76 QSS-RA_68-70

Single-Ended Application – FEXT, “Best Case” Configuration
QSS-RA_74-76 QTS-RA_68-70
```

### Page 39

```text
High Speed Characterization Report

Series:  QSS-RA/QTS-RA Series
Description: , 0.635mm (0.0250”) Pitch, Two Row, Right Angle to Right Angle Connection

Samtec Inc. WWW.SAMTEC.COM Phone: 812-944-6733
520 Park East Blvd. 1-800-SAMTEC-9 (US & Canada) Fax: 812-948-5047
New Albany IN 47151-1147 USA SIG@samtec.com
 Report Revision: 12/18/2009
©Samtec, Inc. 2005 Page:35 All Rights Reserved

Single-Ended Application – NEXT, “Row 2 to Row 1” Configuration
QSS-RA_4-6 QSS-RA_3-5

Single-Ended Application – FEXT, “Row 2 to Row 1” Configuration
QSS-RA_4-6 QTS-RA_3-5
```

### Page 40

```text
High Speed Characterization Report

Series:  QSS-RA/QTS-RA Series
Description: , 0.635mm (0.0250”) Pitch, Two Row, Right Angle to Right Angle Connection

Samtec Inc. WWW.SAMTEC.COM Phone: 812-944-6733
520 Park East Blvd. 1-800-SAMTEC-9 (US & Canada) Fax: 812-948-5047
New Albany IN 47151-1147 USA SIG@samtec.com
 Report Revision: 12/18/2009
©Samtec, Inc. 2005 Page:36 All Rights Reserved

ROW 2, short path
Differential Application – Impedance
Configuration: probe 34=QSS-RA_74-76, probe 56=QTS-RA_74-76

Differential Application – Propagation Delay
Configuration: probe 34=QSS-RA_74-76, probe 56=QTS-RA_74-76
```

### Page 41

```text
High Speed Characterization Report

Series:  QSS-RA/QTS-RA Series
Description: , 0.635mm (0.0250”) Pitch, Two Row, Right Angle to Right Angle Connection

Samtec Inc. WWW.SAMTEC.COM Phone: 812-944-6733
520 Park East Blvd. 1-800-SAMTEC-9 (US & Canada) Fax: 812-948-5047
New Albany IN 47151-1147 USA SIG@samtec.com
 Report Revision: 12/18/2009
©Samtec, Inc. 2005 Page:37 All Rights Reserved

Differential Application – NEXT, “Worst Case” Configuration
QSS-RA_74-76 QSS-RA_70-72

Differential Application – FEXT, “Worst Case” Configuration
QSS-RA_74-76 QTS-RA_70-72
```

### Page 42

```text
High Speed Characterization Report

Series:  QSS-RA/QTS-RA Series
Description: , 0.635mm (0.0250”) Pitch, Two Row, Right Angle to Right Angle Connection

Samtec Inc. WWW.SAMTEC.COM Phone: 812-944-6733
520 Park East Blvd. 1-800-SAMTEC-9 (US & Canada) Fax: 812-948-5047
New Albany IN 47151-1147 USA SIG@samtec.com
 Report Revision: 12/18/2009
©Samtec, Inc. 2005 Page:38 All Rights Reserved

Differential Application – NEXT, “Best Case” Configuration
QSS-RA_74-76 QSS-RA_68-70

Differential Application – FEXT, “Best Case” Configuration
QSS-RA_74-76 QTS-RA_68-70
```

### Page 43

```text
High Speed Characterization Report

Series:  QSS-RA/QTS-RA Series
Description: , 0.635mm (0.0250”) Pitch, Two Row, Right Angle to Right Angle Connection

Samtec Inc. WWW.SAMTEC.COM Phone: 812-944-6733
520 Park East Blvd. 1-800-SAMTEC-9 (US & Canada) Fax: 812-948-5047
New Albany IN 47151-1147 USA SIG@samtec.com
 Report Revision: 12/18/2009
©Samtec, Inc. 2005 Page:39 All Rights Reserved

Differential Application – NEXT, “Row 2 to Row 1” Configuration
QSS-RA_4-6 QSS-RA_3-5

Differential Application – FEXT, “Row 2 to Row 1” Configuration
QSS-RA_4-6 QTS-RA_3-5
```

### Page 44

```text
High Speed Characterization Report

Series:  QSS-RA/QTS-RA Series
Description: , 0.635mm (0.0250”) Pitch, Two Row, Right Angle to Right Angle Connection

Samtec Inc. WWW.SAMTEC.COM Phone: 812-944-6733
520 Park East Blvd. 1-800-SAMTEC-9 (US & Canada) Fax: 812-948-5047
New Albany IN 47151-1147 USA SIG@samtec.com
 Report Revision: 12/18/2009
©Samtec, Inc. 2005 Page:40 All Rights Reserved

Appendix C – Product and Test System Descriptions

Product Description
Product test samples were Q series right angle socket style QSS-050-01-L-D-RA and
the right angle terminal style QTS-050-01-L-D-RA.   Both right angle style connectors
are PCB surface mount.  The right angle surface mount design forces the top row ter-
minals to have a longer electrical length than those of the bottom row, hence, electrical
characteristics between the short row and longer row do differ.  When mated the con-
nectors are probed co-planar.  Each connector structure consists of two rows of 50 con-
tact terminals.  Contact centerline pitch is 0.635mm (.0250”).

Test System Description
The test fixtures are composed of 4-layer FR-4 material with 50Ω and100Ω signal trace
and pad configurations designed for the electrical characterization of Samtec Hi-Speed
connector products.  Test fixtures are specific to the part numbers described above un-
der Product Description.  Mating test fixtures are specified in the table below.

Printed Circuit Board  Fixture Identification
PCB-101748-TST-11, worst case mates with PCB-101748-TST-12, worst case
PCB-101748-TST-21, best case mates with PCB-101748-TST-22, best case
PCB-101748-TST-31, worst case mates with PCB-101748-TST-32, worst case
PCB-101748-TST-41, best case mates with PCB-101748-TST-42, best case

S-parameter and time domain data is available from all test points.  Data contained
within this report comes from one of the two socket paths measured.  Bandwidth ratings
will sometimes vary between signal paths.  When rating differences occur, worst case
performance characteristics are reported.
Electrical continuity exists between like labeled test points when mated as designated.
Reference plane and calibration standards are specific to PCB101748-TST where each
cal standard on the calibration board marked PCB101748-TST-99 Rev can be found.
Pictured under “Test System Description” are the mated test samples and schematics
for easy identification.
```

### Page 45

```text
High Speed Characterization Report

Series:  QSS-RA/QTS-RA Series
Description: , 0.635mm (0.0250”) Pitch, Two Row, Right Angle to Right Angle Connection

Samtec Inc. WWW.SAMTEC.COM Phone: 812-944-6733
520 Park East Blvd. 1-800-SAMTEC-9 (US & Canada) Fax: 812-948-5047
New Albany IN 47151-1147 USA SIG@samtec.com
 Report Revision: 12/18/2009
©Samtec, Inc. 2005 Page:41 All Rights Reserved

PCB-101620-TST Test Fixtures, Row 1, Longer Terminal Contact

PCB-101620-TST- Test Fixtures, Row 2, Shorter Terminal Contact
```

### Page 46

```text
High Speed Characterization Report

Series:  QSS-RA/QTS-RA Series
Description: , 0.635mm (0.0250”) Pitch, Two Row, Right Angle to Right Angle Connection

Samtec Inc. WWW.SAMTEC.COM Phone: 812-944-6733
520 Park East Blvd. 1-800-SAMTEC-9 (US & Canada) Fax: 812-948-5047
New Albany IN 47151-1147 USA SIG@samtec.com
 Report Revision: 12/18/2009
©Samtec, Inc. 2005 Page:42 All Rights Reserved

PCB Fixture Set I

Fixture Identity - Worst Case, Long Path, Row 1
PCB-101748-TST-11 Rev – QSS-RA
PCB-101748-TST-12 – Rev – QTS-RA

Worst Case In Row & Across Row Crosstalk Test Parameters –
DP2 to DP1, Differential, GAAVVG, 2:1 Signal to Ground Ratio,
Near-End Aggressor: QSS-RA_87-89  Victim; QSS-RA_83-85
Far-End Aggressor: QSS-RA_87-89  Victim; QTS-RA_83-85
SE2 to SE1, Single-Ended, GAVG, 2:1 Signal to Ground Ratio,
Near-End Aggressor: QSS-RA_43 Victim; QSS-RA_41
Far-End Aggressor: QSS-RA_43 Victim; QTS-RA_41
DP6 to DP5, Differential, GAAG/GVVG, 1:1 Signal to Ground Ratio,
Near-End Aggressor: QSS-RA_4-6 Victim; QSS-RA_3-5
Far-End Aggressor: QSS-RA_4-6 Victim; QTS-RA_3-5

Fixture Identity - Best Case, Long Path, Row 1
PCB-101748-TST-21 Rev – QSS-RA
PCB-101748-TST-22 – Rev – QTS-RA

Best Case In Row & Across Row Crosstalk Test Parameters –
DP4 to DP3, Differential, GAAVVG, 2:1 Signal to Ground Ratio,
Near-End Aggressor: QSS-RA_91-93 Victim; QSS-RA_85-87
Far-End Aggressor: QSS-RA_91-93 Victim; QTS-RA_85-87
SE4 to SE3, Single-Ended, GAVG, 2:1 Signal to Ground Ratio,
Near-End Aggressor: QSS-RA_47 Victim; QSS-RA_43
Far-End Aggressor: QSS-RA_47 Victim; QTS-RA_43
SE6 to SE5, Differential, GAAG/GVVG, 1:1 Signal to Ground Ratio,
Near-End Aggressor: QSS-RA_4 Victim; QSS-RA_3
Far-End Aggressor: QSS-RA_4 Victim; QTS-RA_3
Transmission & Reflection Test Parameters
SE4, Single-Ended probe 3=QSS- RA_47, probe 5=QTS-RA_47
DP4, Differential probe34=QSS- RA_91-93, probe56=QTS-RA_91-93
SE3, Single-Ended* probe 2=QSS- RA_43, probe 8=QTS-RA_43
DP3, Differential* probe 12=QSS- RA_85-87, probe 78=QTS-RA_85-87
* not reported
```

### Page 47

```text
High Speed Characterization Report

Series:  QSS-RA/QTS-RA Series
Description: , 0.635mm (0.0250”) Pitch, Two Row, Right Angle to Right Angle Connection

Samtec Inc. WWW.SAMTEC.COM Phone: 812-944-6733
520 Park East Blvd. 1-800-SAMTEC-9 (US & Canada) Fax: 812-948-5047
New Albany IN 47151-1147 USA SIG@samtec.com
 Report Revision: 12/18/2009
©Samtec, Inc. 2005 Page:43 All Rights Reserved

Preparation:  Row One Fixtures
PCB-101748-TST-11, worst case mates with PCB-101748-TST-12, worst case

PCB-101748-TST-21, best case mates with PCB-101748-TST-22, best case
```

### Page 48

```text
High Speed Characterization Report

Series:  QSS-RA/QTS-RA Series
Description: , 0.635mm (0.0250”) Pitch, Two Row, Right Angle to Right Angle Connection

Samtec Inc. WWW.SAMTEC.COM Phone: 812-944-6733
520 Park East Blvd. 1-800-SAMTEC-9 (US & Canada) Fax: 812-948-5047
New Albany IN 47151-1147 USA SIG@samtec.com
 Report Revision: 12/18/2009
©Samtec, Inc. 2005 Page:44 All Rights Reserved

PCB Fixture Set II

Fixture Identity - Worst Case, Short Path, Row 2
PCB-101748-TST-31 Rev – QSS-RA
PCB-101748-TST-32 – Rev – QTS-RA

Worst Case In Row & Across Row Crosstalk Test Parameters –
DP2 to DP1, Differential, GAAVVG, 2:1 Signal to Ground Ratio,
Near-End Aggressor: QSS-RA_74-76 Victim; QSS-RA_70-72
Far-End Aggressor: QSS-RA_74-76 Victim; QTS-RA_70-72
SE2 to SE1, Single-Ended, GAVG, 2:1 Signal to Ground Ratio,
Near-End Aggressor: QSS-RA_24 Victim; QSS-RA_22
Far-End Aggressor: QSS-RA_24 Victim; QTS-RA_22
DP6 to DP5, Differential, GAAG/GVVG, 1:1 Signal to Ground Ratio,
Near-End Aggressor: QSS-RA_4-6 Victim; QSS-RA_3-5
Far-End Aggressor: QSS-RA_4-6 Victim; QTS-RA_3-5

Fixture Identity - Best Case, Short Path, Row 2
PCB-101748-TST-41 Rev – QSS-RA
PCB-101748-TST-42 – Rev – QTS-RA

Best Case In Row & Across Row Crosstalk Test Parameters –
DP4 to DP3, Differential, GAAVVG, 2:1 Signal to Ground Ratio,

Near-End Aggressor: QSS-RA_74-76 Victim; QSS-RA_68-70
Far-End Aggressor: QSS-RA_74-76 Victim; QTS-RA_68-70
SE4 to SE3, Single-Ended, GAVG, 2:1 Signal to Ground Ratio,
Near-End Aggressor: QSS-RA_24 Victim; QSS-RA_20
Far-End Aggressor: QSS-RA_24 Victim; QTS-RA_20
SE6 to SE5, Differential, GAAG/GVVG, 1:1 Signal to Ground Ratio,
Near-End Aggressor: QSS-RA_4 Victim; QSS-RA_3
Far-End Aggressor: QSS-RA_4 Victim; QTS-RA_3
Transmission & Reflection Test Parameters
SE4, Single-Ended probe 3=QSS-RA_24  probe 5=QTS-RA_24
DP4, Differential probe 34=QSS-RA_74-76  probe 56=QTS-RA_74-76
SE3, Single-Ended* probe 2=QSS- RA_20  probe 8=QTS-RA_20
DP3, Differential* probe 12=QSS- RA_68-70  probe 78=QTS-RA_68-70
* not reported
```

### Page 49

```text
High Speed Characterization Report

Series:  QSS-RA/QTS-RA Series
Description: , 0.635mm (0.0250”) Pitch, Two Row, Right Angle to Right Angle Connection

Samtec Inc. WWW.SAMTEC.COM Phone: 812-944-6733
520 Park East Blvd. 1-800-SAMTEC-9 (US & Canada) Fax: 812-948-5047
New Albany IN 47151-1147 USA SIG@samtec.com
 Report Revision: 12/18/2009
©Samtec, Inc. 2005 Page:45 All Rights Reserved

Preparation: Row Two Fixtures
PCB-101748-TST-31, worst case mates with PCB-101748-TST-32, worst case

PCB-101748-TST-41, best case mates with PCB-101748-TST-42, best case
```

### Page 50

```text
High Speed Characterization Report

Series:  QSS-RA/QTS-RA Series
Description: , 0.635mm (0.0250”) Pitch, Two Row, Right Angle to Right Angle Connection

Samtec Inc. WWW.SAMTEC.COM Phone: 812-944-6733
520 Park East Blvd. 1-800-SAMTEC-9 (US & Canada) Fax: 812-948-5047
New Albany IN 47151-1147 USA SIG@samtec.com
 Report Revision: 12/18/2009
©Samtec, Inc. 2005 Page:46 All Rights Reserved

PCB101748-TST-99 Calibration Standards

        Short Path    Long Path

Propagation Delay Reference Length
Single-Ended, Long Path, 1000 mils

Propagation Delay Reference Length
Single-Ended, Short Path, 1748 mils

Propagation Delay Reference Length
Differential, Short Path, 2348 mils

Propagation Delay Reference Length
Differential, Long Path, 2100 mils

TDA Step Waveform
Transmission/Reflection Standard

Note: Open Standards are used for
connector only de-embedding pur-
poses.   All Performance data , with
the exception of propagation delay
include effects of  PCB signal launch
traces.
```

### Page 51

```text
High Speed Characterization Report

Series:  QSS-RA/QTS-RA Series
Description: , 0.635mm (0.0250”) Pitch, Two Row, Right Angle to Right Angle Connection

Samtec Inc. WWW.SAMTEC.COM Phone: 812-944-6733
520 Park East Blvd. 1-800-SAMTEC-9 (US & Canada) Fax: 812-948-5047
New Albany IN 47151-1147 USA SIG@samtec.com
 Report Revision: 12/18/2009
©Samtec, Inc. 2005 Page:47 All Rights Reserved

Appendix D – Test and Measurement Setup

The test instrument is the Tektronix CSA8000 Communication Signal Analyzer Main-
frame.  Four bays of the CSA8000 use four Tektronix 80E04 TDR/Sampling Heads.
Time domain data and graphs are real-time. Post-processed s-parameter data and
graphs extend from a TDR based software tool called I-Connect   Probing uses a video
microscopy system, microprobe positioners, and 40GHz capable probes.  Four hundred
and fifty micron pitch probes are located to PCB launch points with 25X to 175X magni-
fication and XYZ fine positioning adjustments available from both the probe table and
micro-probe positioners.  Electrically the microwave probes rate a < 1.0 dB insertion
loss, a ≥18 dB return loss, and an isolation of 38 dB providing high-bandwidth and low
parasitic measurement results.  Combined, the above technology provides a stable
measurement environment along with the electrical accuracies for obtaining precise
calibrations and signal launch capabilities.

CSA8000/TDA IConnect Measurements Capability
```

### Page 52

```text
High Speed Characterization Report

Series:  QSS-RA/QTS-RA Series
Description: , 0.635mm (0.0250”) Pitch, Two Row, Right Angle to Right Angle Connection

Samtec Inc. WWW.SAMTEC.COM Phone: 812-944-6733
520 Park East Blvd. 1-800-SAMTEC-9 (US & Canada) Fax: 812-948-5047
New Albany IN 47151-1147 USA SIG@samtec.com
 Report Revision: 12/18/2009
©Samtec, Inc. 2005 Page:48 All Rights Reserved

Horizontal Orientation Eight Channel 40 GHz Microprobe Setup

Test Instruments
QTY Description
1 Tektronix CSA8000 Comm unication Signal Analyzer
4 Tektronix 80E04 Dual Channel  20 GHz TDR Sampling Module
1 Tektronix 80E03 Dual Chann el 20 GHz  Sampling Module

Measurement Station Accessories
QTY Description
1 GigaTest Labs Model (GTL3030) Probe Station
4 GTL Micro-Probe Positioners (2)
4 Picoprobe by GGB Ind. Dual Model 40A  GSG-GSG (differential applications)
1 Keyence VH-5910 High Resolution Video Microscope
1 Keyence VH-W100 Fixed Magnification Lens 100 X
1 Keyence VH-Z25 Standard Zoom Lens 25X-175X

Test Cables & Adapters
QTY
 Description
8 Pasternack  Enterprises 2.9mm Semi- Rigid (.086) 6” Cable Assemblies (4)
4 Tektronix 1 Meter Module Extenders (2)
```

### Page 53

```text
High Speed Characterization Report

Series:  QSS-RA/QTS-RA Series
Description: , 0.635mm (0.0250”) Pitch, Two Row, Right Angle to Right Angle Connection

Samtec Inc. WWW.SAMTEC.COM Phone: 812-944-6733
520 Park East Blvd. 1-800-SAMTEC-9 (US & Canada) Fax: 812-948-5047
New Albany IN 47151-1147 USA SIG@samtec.com
 Report Revision: 12/18/2009
©Samtec, Inc. 2005 Page:49 All Rights Reserved

Appendix E - Frequency and Time Domain Measurements

In a two row connector series where terminal geometry and dimensions are equal, only
one row is measured.  The following test procedures are written for same geometry
equal length double row connector series’. In two row connector design where contact
geometry and/or length may differ (right angle terminal) between terminal rows it is nec-
essary to measure SI performance for both rows.  This condition effectively doubles the
number of measurements needed to characterize the connector series.  It is also impor-
tant to note before gathering measurement data that TDA Systems IConnect measure-
ments and CSA8000 measurements are virtually the same measurements using diverse
formats.  This means that the operator being extremely aware, can obtain SI time and
frequency characteristics in an almost simultaneous fashion

Since IConnect setup procedures are specific to the frequency information sought, it is
mandatory that the sample preparation and CSA8000 functional setups be consistent
throughout the waveform gathering process.   If the operators test equipment permits
recall sequencing between the various test parameter setups, it insures IConnect func-
tional setups remain consistent with the TDR/TDT waveforms previously recorded.

Sample Preparation
Determine signal launch and test points by referencing test parameter fixture tables and
schematic layout maps.

Calibration Board, CAL

PCB Fixture Sets I & II

Wherever practical it is a good practice to terminate all non-active signal lines immedi-
ately adjacent to the designated active or quiet signal lines under test.

Frequency (S-Parameter) Domain Procedures
Frequency data extraction involves a two-step process.  The first step creates the TDR
based waveform relationships utilizing a Tektronix CSA8000 time based instrument.
The second step involves the conversion of these time-based waveforms into s-
parameter format using the TDA Systems IConnect software tool. TDA Systems labels
time related conversion waveforms as the Step and DUT waveform references.  This
section establishes the setup procedures for defining the Step and DUT reference for
conversion to frequency s-parameters presented in this report.

CSA8000 Setup

Listed below is the CSA 8000 functional menu setups used for single-ended and differ-
ential frequency response extractions.  Both signal types utilize I-Connect software tools
to generate S-parameter upper and lower frequency boundaries along with the step fre-
```

### Page 54

```text
High Speed Characterization Report

Series:  QSS-RA/QTS-RA Series
Description: , 0.635mm (0.0250”) Pitch, Two Row, Right Angle to Right Angle Connection

Samtec Inc. WWW.SAMTEC.COM Phone: 812-944-6733
520 Park East Blvd. 1-800-SAMTEC-9 (US & Canada) Fax: 812-948-5047
New Albany IN 47151-1147 USA SIG@samtec.com
 Report Revision: 12/18/2009
©Samtec, Inc. 2005 Page:50 All Rights Reserved

quency.  Functional settings such as window length, number of points and averaging
capability determines the instruments frequency boundaries.  Once window length,
number of points and averaging functions are set, maintain the same instrument set-
tings throughout the extraction process.  The single channel pulsed source processes s-
parameters in single-ended format.   A dual channel differential pulsed source proc-
esses s-parameters in differential format.

 Single-Ended Signal
 Differential Signal
Vertical Scale: 100 mV/ Div:  100 mV/ Div:
Offset: Default / Scroll Default / Scroll
Horizontal Scale: 1nSec/ Div = 20 MHz step
frequency
1nSec/ Div = 20 MHz step
frequency
Max. Record Length: 4000 = Min. Resolution 4000 = Min. Resolution
Averages: ≥ 128 ≥ 128

Insertion Loss (TDA conversion)

Step Waveform - determine TD waveform by making a TDT transmission measure-
ment that includes all cables, adapters, and probes connected in the test systems
transmission path.  Complete the transmission path by inserting a negligible length of
transmission standard between the system test probes.  Calibration or waveform refer-
encing utilizes a six pad cal structure for each of the probe touchdowns (ie; se thru = 3
pads or diff thru = 6 pads).  Reference the calibration board CAL
, and use the 1mm
(0.390”) length calibration reflect/transmission structure for TDA step waveform charac-
terization.

DUT Waveform - determine TD waveform by making an active TDT transmission
measurement that includes all cables, adapters, and probes connected in the test sys-
tems transmission path.  Insert the SUT between the probes in place of the reflec-
tion/transmission standard and record the measurement.  The QSS-RA/QTS-RA
 char-
acterization reports one single-ended and one differential insertion loss application. Sin-
gle-ended and differential line measurement possibilities are SE3, SE4, DP3 and DP4.
Reference both PCB fixture set I and fixture set II for an appropriate signal path.

Return Loss (TDA conversion)

Step Waveform – determine TD waveform by making an active TDR reflection meas-
urement that includes all cables, adapters, and probes connected in the test systems
electrical path up to and including an open standard.  Calibration or waveform referenc-
ing utilizes three pads for each probe touchdown (ie; se reflect = 3 pads or diff reflect =
```

### Page 55

```text
High Speed Characterization Report

Series:  QSS-RA/QTS-RA Series
Description: , 0.635mm (0.0250”) Pitch, Two Row, Right Angle to Right Angle Connection

Samtec Inc. WWW.SAMTEC.COM Phone: 812-944-6733
520 Park East Blvd. 1-800-SAMTEC-9 (US & Canada) Fax: 812-948-5047
New Albany IN 47151-1147 USA SIG@samtec.com
 Report Revision: 12/18/2009
©Samtec, Inc. 2005 Page:51 All Rights Reserved

6 pads). Reference CAL calibration board and use the 1mm (0.390”) length calibration
reflect/transmission standard for TDA step waveform characterization.

DUT Waveform – determine waveform by making an active TDR reflection measure-
ment that includes all cables, adapters, and probes connected in the test systems
transmission path.  Insert the SUT between the probes in place of the reflec-
tion/transmission standard and record the measurement.  In this condition cables and
adapters located at the far-end of the inserted SUT function as the systems 50Ω single-
ended and/or 100Ω differential matching impedance.  The QSS-RA/QTS-RA
 characteri-
zation reports one single-ended and one differential return loss application.  Single-
ended and differential line measurement possibilities are SE3 & SE4, and DP3 & DP4.
Reference both PCB fixture set I and fixture set II for an appropriate signal path.

Near-End Crosstalk (TDA conversion)

Step Waveform – Use Return Loss (RL) step waveform.

DUT Waveform - determine waveform by driving specified signal type and monitoring
coupled energy levels at the configurations adjacent near-end signal line.  QSS-
RA/QTS-RA examines three single-ended and three differential near-end XT configura-
tions.  Single-ended crosstalk measurements are SE2 to SE1, SE4 to SE3, and SE6 to
SE5.  Differential crosstalk measurements are DP2 to DP1, DP4 to DP3, and DP6 to
DP5.  Reference both PCB fixture set I and fixture set II for crosstalk configurations.

Far-End Crosstalk (TDA conversion)

Step Waveform - Use Insertion Loss (IL) step waveform.

DUT Waveform - determine waveform by driving specified signal type and monitoring
coupled energy levels at the configurations adjacent far-end signal line.  QSS-RA/QTS-
RA examines three single-ended and three differential far-end XT configurations.  Sin-
gle-ended crosstalk measurements are SE2 to SE1, SE4 to SE3, and SE6 to SE5.  Dif-
ferential crosstalk measurements are DP2 to DP1, DP4 to DP3, and DP6 to DP5.  Ref-
erence both PCB fixture set I and fixture set II for crosstalk configurations.
```

### Page 56

```text
High Speed Characterization Report

Series:  QSS-RA/QTS-RA Series
Description: , 0.635mm (0.0250”) Pitch, Two Row, Right Angle to Right Angle Connection

Samtec Inc. WWW.SAMTEC.COM Phone: 812-944-6733
520 Park East Blvd. 1-800-SAMTEC-9 (US & Canada) Fax: 812-948-5047
New Albany IN 47151-1147 USA SIG@samtec.com
 Report Revision: 12/18/2009
©Samtec, Inc. 2005 Page:52 All Rights Reserved

Time Domain Procedures
Utilize the Time Domain Reflectometer (TDR) or Time Domain Transmission (TDT)
method for digital type pulse measurements.  Impedance and propagation delay charac-
terization utilize TDR measurement methods.  Crosstalk measurements utilize TDT
methods. The Tektronix 80E04 TDR/ Sampling Head provide both the signaling type and
sampling capability necessary to characterize the SUT.

Impedance (TDR)

Energize the SUT’s signal line(s) with a TDR pulse.  The far-end of the energized signal
lines are terminated in the test systems characteristic impedance (e.g.; 50Ω or 100Ω
termination) or use quality cables and adapters located at the far-end of the inserted
SUT function as the systems 50Ω single-ended and/or 100Ω differential matching im-
pedance. The QSS-RA/QTS-RA characterization reports one single-ended and one dif-
ferential impedance application.  Single-ended and differential line measurement possi-
bilities are SE3, SE4, DP3, and DP4.  Reference both PCB fixture set I and fixture set II
for an appropriate signal path.

Propagation Delay (TDT)

This test reports differential or single-ended signal delay as the measured difference of
propagation between a combined electrical length of the input/output signal pads and
signal traces (35 ± 5 ps edge rate) and the device under test (DUT) plus a referenced
electrical length of the signal pads and signal traces (PDpads/traces- PDDUT + PDpads/traces).
The recorded delay is the signal delay of the connector only.  PDpads/traces is the nomen-
clature representing the electrical length of PCB signal pads & traces equal to physical
lengths of PCB pads & traces entering and leaving the device under test (DUT).  The
PDDUT + PDpads/traces variable is the mated DUT fixture.  Measure the risetime of
PDpads/traces waveform & PDDUT + PDpads/traces waveforms. Record the 50% amplitude of
each rising edge.  The distance in time between the rising edges is the propagation de-
lay of the device under test (DUT= mated connector only). Single-ended and differential
line measurement possibilities are SE3, SE4, DP3, and DP4.  Consult the calibration
board CAL for input/output signal line reference traces. Reference both PCB fixture set I
and fixture set II for an appropriate signal path.

Near-End Crosstalk (TDT)

Energize the pre-determined signal line(s) with the appropriate signal type. Monitor the
configurations adjacent quiet signal line at the near-end for magnitudes of coupled en-
ergy.   Terminate adjacent signal lines not under test in the test systems characteristic
impedance.  QSS-RA/QTS-RA examines three single-ended and three differential near-
end XT configurations.  Single-ended crosstalk measurements are SE2 to SE1, SE4 to
SE3, and SE6 to SE5.  Differential crosstalk measurements are DP2 to DP1, DP4 to
```

### Page 57

```text
High Speed Characterization Report

Series:  QSS-RA/QTS-RA Series
Description: , 0.635mm (0.0250”) Pitch, Two Row, Right Angle to Right Angle Connection

Samtec Inc. WWW.SAMTEC.COM Phone: 812-944-6733
520 Park East Blvd. 1-800-SAMTEC-9 (US & Canada) Fax: 812-948-5047
New Albany IN 47151-1147 USA SIG@samtec.com
 Report Revision: 12/18/2009
©Samtec, Inc. 2005 Page:53 All Rights Reserved

DP3, and DP6 to DP5.  Reference both PCB fixture set I and fixture set II for crosstalk
configurations.

Far-End Crosstalk (TDT)

Energize the pre-determined signal line(s) with the appropriate signal type. Monitor the
configurations adjacent quiet signal line at the far-end for magnitudes of coupled en-
ergy.   Terminate adjacent signal lines not under test in the test systems characteristic
impedance.  QSS-RA/QTS-RA examines three single-ended and three differential far-
end XT configurations.  Single-ended crosstalk measurements are SE2 to SE1, SE4 to
SE3, and SE6 to SE5.  Differential crosstalk measurements are DP2 to DP1, DP4 to
DP3, and DP6 to DP5.  Reference both PCB fixture set I and fixture set II for crosstalk
configurations.
```

### Page 58

```text
High Speed Characterization Report

Series:  QSS-RA/QTS-RA Series
Description: , 0.635mm (0.0250”) Pitch, Two Row, Right Angle to Right Angle Connection

Samtec Inc. WWW.SAMTEC.COM Phone: 812-944-6733
520 Park East Blvd. 1-800-SAMTEC-9 (US & Canada) Fax: 812-948-5047
New Albany IN 47151-1147 USA SIG@samtec.com
 Report Revision: 12/18/2009
©Samtec, Inc. 2005 Page:54 All Rights Reserved

Appendix F – Glossary of Terms

TD – Time Domain
FD – Frequency Domain
PD – Propagation Delay
DUT – Device under test, term used for TDA IConnect & Propagation Delay waveforms
EC6 – Edge Card with a .635mm signal pad pitch
FEXT – Far-End Crosstalk
GSG – Ground–Signal-Ground; geometric configuration
GSSG - Ground–Signal-Signal-Ground; geometric configuration
LEC6 – Signal Launch Edge Card with a .635 mm signal pad pitch
NEXT – Near-End Crosstalk
PCB – Printed Circuit Board
SE – Single-Ended
SI – Signal Integrity
SUT – System Under Test
TDR – Time Domain Reflectometry
TDT – Time Domain Transmission
WC – Worst Case crosstalk configuration
BC – Best Case crosstalk configuration
Z – Impedance (expressed in ohms)
OV – Optimal Vertical
OH – Optimal Horizontal
HDV – High Density Vertical
PPO – Pin Population Option
S – Static (independent of PCB ground)
```
