thepinkmile/Enigma-NG/design/Datasheets/Samtec-QSS-QTS-RA-Power-Test-Report.md

# Project Number: Tracking Code: TC0748--1505

## Source

- **Source PDF:** [Samtec-QSS-QTS-RA-Power-Test-Report.pdf](Samtec-QSS-QTS-RA-Power-Test-Report.pdf)
- **Generated Markdown:** `Samtec-QSS-QTS-RA-Power-Test-Report.md`
- **Page count:** 17
- **Conversion method:** automated local PDF text extraction with pypdf/pdfplumber

## PDF Metadata

| Field | Value |
| :--- | :--- |
| Title | Microsoft Word - TC0748--1505Reportrev1.doc |
| Author | shawnd |
| Subject |  |
| Creator | PScript5.dll Version 5.2 |
| Producer | Acrobat Distiller 8.0.0 (Windows) |

## Extracted Technical Index

This markdown datasheet is meant to reduce the need to reopen the PDF during design work.
It preserves design-relevant extracted snippets first, followed by page-by-page text so the source content remains locally searchable.

### Part number and ordering information

- No reliable text snippet was automatically extracted for this category. Review the raw page text below.

### Pin, pad, and connection designations

- Page 1 of 17 / CURRENT CARRYING CAPACITY REPORT / QSS-100-01-L-D-RA-WT/QTS-100-01-L-D-RA-WT
- traceable standards according to IS0 10012-l and ANSI/NCSL 2540-1, as applicable. / All contents contained herein are the property of Samtec. No portion of this report, in part or in full shall …

### Specifications, ratings, and operating conditions

- Project Number:  Tracking Code: TC0748--1505 / Requested by: Mark Shireman Date: 11/28/2007 Product Rev: Current / Part #: QSS-100-01-L-D-RA-WT/QTS-100-01-L-D-RA-WT Lot #: IH Tech: Jerry / Small…
- Page 1 of 17 / CURRENT CARRYING CAPACITY REPORT / QSS-100-01-L-D-RA-WT/QTS-100-01-L-D-RA-WT
- SCOPE / 1. Temperature Rise/Current Carrying Capacity / 1.1. To determine the amount of current the device under test (DUT) can safely carry over the operating / temperature range of the DUT.
- 1. Temperature Rise/Current Carrying Capacity / 1.1. To determine the amount of current the device under test (DUT) can safely carry over the operating / temperature range of the DUT. / 1.2. Con…
- 1.1. To determine the amount of current the device under test (DUT) can safely carry over the operating / temperature range of the DUT. / 1.2. Contact loading will also be addressed in this docu…
- carried as the number of energized contacts is varied. / 2. Current Cycling / 2.1. To determine the performance of the device under test (DUT) when subjected to the power-on/power-off / cycling …
- Standards:  EIA Publication 364-70 Temperature Rise / EIA Publication 364-06 Contact Resistance / EIA Publication 364-55 Current Cycling / TLPM-032 Current Carrying Capacity / TLPM-084 Current C…
- EIA Publication 364-06 Contact Resistance / EIA Publication 364-55 Current Cycling / TLPM-032 Current Carrying Capacity / TLPM-084 Current Cycling
- EIA Publication 364-55 Current Cycling / TLPM-032 Current Carrying Capacity / TLPM-084 Current Cycling / TEST SAMPLES AND PREPARATION
- TEST SAMPLES AND PREPARATION / 1) All materials shall be manufactured in accordance with the applicable product specification. / 2) All test samples shall be identified and encoded to maintain t…
- Page 3 of 17 / 11)  The following loading configurations shall be tested for Temperature Rise/Current Carrying Capacity testing / of single row connector systems: / 11.1.1 One contact energized …
- Indicates thermocouple monitored, energized contacts / 12) The following loading configurations shall be tested for Temperature Rise/Current Carrying Capacity testing / of two row connector syst…
- Test Condition as in 12.1 above / 13 )   For Current Cycling, only 100 % loading will be tested. / Tracking Code: TC0748--1505 Part #: QSS-100-01-L-D-RA-WT/QTS-100-01-L-D-RA-WT / Part descriptio…
- FLOWCHARTS / Current Carrying Capacity - Contacts / TEST GROUP A GROUP B GROUP C GROUP D GROUP E / STEP 3 Mated Assembies 3 Mated Assembies 3 Mated Assembies 3 Mated Assembies 3 Mated Assembies
- POWERED / 01 CCC CCC CCC CCC CCC / Current Carrying Capacity - Ground Planes / TEST GROUP A GROUP B GROUP C GROUP D / STEP 3 Mated Assembies 3 Mated Assembies 3 Mated Assembies 3 Mated Assembies
- 01 CCC CCC CCC CCC / CCC, Temp rise = EIA-364-70 / (GOLD PLATING)  - Tabulate calculated current at RT, 85° C, 95° C and 115° C / after derating 20% and based on 125° C / CCC, Temp rise = EIA-36…
- after derating 20% and based on 125° C / CCC, Temp rise = EIA-364-70 / (GOLD PLATING)  - Tabulate calculated current at RT, 85° C, 95° C and 115° C / after derating 20% and based on 125° C / Tra…
- TEST PROCEDURES / TEMPERATURE RISE (Current Carrying Capacity, CCC): / 13 Thermocouples shall be calibrated in accordance with Samtec documents; TLWI 0003, Thermocouple Welding
- 14 The thermocouples shall be placed at a location to sense the maximum temperature generated during testing. / 15 Temperature stability shall be defined as the temperature at which three succes…
- 16.4 Four contacts energized adjacent to each other / 16.5 All contacts energized / 17 The following loading configurations shall be tested for Temperature Rise/Current Carrying Capacity testing…

### Dimensions, package, and mechanical information

- No reliable text snippet was automatically extracted for this category. Review the raw page text below.

### Formulas, equations, and configurable calculations

- TLPM-084 Current Cycling / TEST SAMPLES AND PREPARATION / 1) All materials shall be manufactured in accordance with the applicable product specification. / 2) All test samples shall be identifie…
- 3) After soldering, the parts to be used shall be cleaned according to TLWI-0001. / 4) All samples shall be visually inspected and cleaned as necessary. / 5) Any additional preparation shall be …
- Page 3 of 17 / 11)  The following loading configurations shall be tested for Temperature Rise/Current Carrying Capacity testing / of single row connector systems: / 11.1.1 One contact energized …
- Indicates thermocouple monitored, energized contacts / 12) The following loading configurations shall be tested for Temperature Rise/Current Carrying Capacity testing / of two row connector syst…
- 01 CCC CCC CCC CCC / CCC, Temp rise = EIA-364-70 / (GOLD PLATING)  - Tabulate calculated current at RT, 85° C, 95° C and 115° C / after derating 20% and based on 125° C / CCC, Temp rise = EIA-36…
- after derating 20% and based on 125° C / CCC, Temp rise = EIA-364-70 / (GOLD PLATING)  - Tabulate calculated current at RT, 85° C, 95° C and 115° C / after derating 20% and based on 125° C / Tra…
- 13 Thermocouples shall be calibrated in accordance with Samtec documents; TLWI 0003, Thermocouple Welding / Procedure and TLWI 0005, Thermocouple Calibration / 14 The thermocouples shall be plac…
- differ not more than 1° C (computer controlled data acquisition). This is the Temperature Rise that the Current / Carrying Capacity and De-rating curves are based on. / 16 The following loading …
- 16.4 Four contacts energized adjacent to each other / 16.5 All contacts energized / 17 The following loading configurations shall be tested for Temperature Rise/Current Carrying Capacity testing…
- 17.4 Two by Four contacts energized adjacent to each other / 17.5 All contacts energized / 18 Three samples shall be tested for each of the above configurations for a total of eighteen assemblie…
- 19 Temperature Rise measurements shall be made at 5 different current levels yielding temperature rises in the 10 to / 70°C range. / 20 The maximum temperature rise data for each current of each…
- Page 17 of 17 / EQUIPMENT AND CALIBRATION SCHEDULES / Equipment #: PS-07

### Reference designs, applications, and examples

- No reliable text snippet was automatically extracted for this category. Review the raw page text below.

## Page-by-Page Extracted Content

### Page 1

```text
Project Number:  Tracking Code: TC0748--1505
Requested by: Mark Shireman Date: 11/28/2007 Product Rev: Current
Part #: QSS-100-01-L-D-RA-WT/QTS-100-01-L-D-RA-WT Lot #: IH Tech: Jerry
Smallwood
Eng: Troy Cook
Part description: QSS/QTS-RA Qty to test: 20
Test Start: 01/14/2008 Test Completed: 1/16/2008

 Page 1 of 17

CURRENT CARRYING CAPACITY REPORT

QSS-100-01-L-D-RA-WT/QTS-100-01-L-D-RA-WT
```

### Page 2

```text
Tracking Code: TC0748--1505 Part #: QSS-100-01-L-D-RA-WT/QTS-100-01-L-D-RA-WT
Part description: QSS/QTS-RA

 Page 2 of 17

CERTIFICATION

All instruments and measuring equipment were calibrated to National Institute for Standards and Technology (NIST)
traceable standards according to IS0 10012-l and ANSI/NCSL 2540-1, as applicable.

All contents contained herein are the property of Samtec. No portion of this report, in part or in full shall be
reproduced without prior written approval of Samtec.

SCOPE

1. Temperature Rise/Current Carrying Capacity
1.1. To determine the amount of current the device under test (DUT) can safely carry over the operating
temperature range of the DUT.
1.2. Contact loading will also be addressed in this document which will determine how much current can be
carried as the number of energized contacts is varied.

2. Current Cycling
2.1. To determine the performance of the device under test (DUT) when subjected to the power-on/power-off
cycling that heats and cools the DUT in normal everyday use.
2.2. Contact loading will set to 100% throughout the test.

APPLICABLE DOCUMENTS
 Standards:  EIA Publication 364-70 Temperature Rise
 EIA Publication 364-06 Contact Resistance
 EIA Publication 364-55 Current Cycling
 TLPM-032 Current Carrying Capacity
 TLPM-084 Current Cycling

TEST SAMPLES AND PREPARATION
1) All materials shall be manufactured in accordance with the applicable product specification.
2) All test samples shall be identified and encoded to maintain traceability throughout the test sequences.
3) After soldering, the parts to be used shall be cleaned according to TLWI-0001.
4) All samples shall be visually inspected and cleaned as necessary.
5) Any additional preparation shall be noted in the individual test sequences.
6) Solder Information: Lead Free
7) Re-Flow Time/Temp: See accompanying profile.
8) All products designed to operate mounted on a printed circuits board shall be tested mounted to test boards in
accordance with EIA-364-70
9) Solder Information: Lead Free
10)  Samtec Test PCBs used: PCB-100992-TST-XX

PREPARED TEST SAMPLE (Typical)
```

### Page 3

```text
Tracking Code: TC0748--1505 Part #: QSS-100-01-L-D-RA-WT/QTS-100-01-L-D-RA-WT
Part description: QSS/QTS-RA

 Page 3 of 17

11)  The following loading configurations shall be tested for Temperature Rise/Current Carrying Capacity testing
of single row connector systems:
11.1.1 One contact energized only
11.1.2 Two contacts energized adjacent to each other
11.1.3 Three contacts energized adjacent to each other
11.1.4 Four contacts energized adjacent to each other
11.1.5 All contacts energized

Test Condition as in 11.1 above

 Indicates energized contacts

 Indicates thermocouple monitored, energized contacts

12) The following loading configurations shall be tested for Temperature Rise/Current Carrying Capacity testing
of two row connector systems:
12.1.1 Two by One contact energized
12.1.2 Two by Two contacts energized adjacent to each other
12.1.3 Two by Three contacts energized adjacent to each other
12.1.4 Two by Four contacts energized adjacent to each other
12.1.5 All contacts energized

Test Condition as in 12.1 above

13 )   For Current Cycling, only 100 % loading will be tested.
```

### Page 4

```text
Tracking Code: TC0748--1505 Part #: QSS-100-01-L-D-RA-WT/QTS-100-01-L-D-RA-WT
Part description: QSS/QTS-RA

 Page 4 of 17

TYPICAL OVEN PROFILE (Soldering Parts to Test Boards)
```

### Page 5

```text
Tracking Code: TC0748--1505 Part #: QSS-100-01-L-D-RA-WT/QTS-100-01-L-D-RA-WT
Part description: QSS/QTS-RA

 Page 5 of 17

FLOWCHARTS

Current Carrying Capacity - Contacts
TEST GROUP A GROUP B GROUP C GROUP D GROUP E
STEP 3 Mated Assembies 3 Mated Assembies 3 Mated Assembies 3 Mated Assembies 3 Mated Assembies
1 CONTACT POWERED
2 CONTACTS
POWERED
3 CONTACTS
POWERED
4 CONTACTS
POWERED
ALL CONTACTS
POWERED
01 CCC CCC CCC CCC CCC
Current Carrying Capacity - Ground Planes
TEST GROUP A GROUP B GROUP C GROUP D
STEP 3 Mated Assembies 3 Mated Assembies 3 Mated Assembies 3 Mated Assembies
1 GROUND PLANE
POWERED
2 GROUND PLANES
POWERED
3 GROUND PLANES
POWERED
4 GROUND PLANES
POWERED
01 CCC CCC CCC CCC
CCC, Temp rise = EIA-364-70
(GOLD PLATING)  - Tabulate calculated current at RT, 85° C, 95° C and 115° C
after derating 20% and based on 125° C
CCC, Temp rise = EIA-364-70
(GOLD PLATING)  - Tabulate calculated current at RT, 85° C, 95° C and 115° C
after derating 20% and based on 125° C
```

### Page 6

```text
Tracking Code: TC0748--1505 Part #: QSS-100-01-L-D-RA-WT/QTS-100-01-L-D-RA-WT
Part description: QSS/QTS-RA

 Page 6 of 17

TEST PROCEDURES

TEMPERATURE RISE (Current Carrying Capacity, CCC):

13 Thermocouples shall be calibrated in accordance with Samtec documents; TLWI 0003, Thermocouple Welding
Procedure and TLWI 0005, Thermocouple Calibration
14 The thermocouples shall be placed at a location to sense the maximum temperature generated during testing.
15 Temperature stability shall be defined as the temperature at which three successive readings, 5 minutes apart,
differ not more than 1° C (computer controlled data acquisition). This is the Temperature Rise that the Current
Carrying Capacity and De-rating curves are based on.
16 The following loading configurations shall be tested (double for two row systems):
16.1 One contact energized only
16.2 Two contacts energized adjacent to each other
16.3 Three contacts energized adjacent to each other
16.4 Four contacts energized adjacent to each other
16.5 All contacts energized
17 The following loading configurations shall be tested for Temperature Rise/Current Carrying Capacity testing of
two row connector systems:
17.1 Two by One contact energized
17.2 Two by Two contacts energized adjacent to each other
17.3 Two by Three contacts energized adjacent to each other
17.4 Two by Four contacts energized adjacent to each other
17.5 All contacts energized
18 Three samples shall be tested for each of the above configurations for a total of eighteen assemblies.
19 Temperature Rise measurements shall be made at 5 different current levels yielding temperature rises in the 10 to
70°C range.
20 The maximum temperature rise data for each current of each loading configuration shall be used to calculate the
Current De-rating curve in accordance with EIA-364-70 and thereby the Current Carrying Capacity versus
ambient temperature of the system under test.

Part No.  Mating Part No.
Sample Size  Technician
Start Date  Complete Date
Room Ambient  Relative Humidity
Equipment ID#:
```

### Page 7

```text
Tracking Code: TC0748--1505 Part #: QSS-100-01-L-D-RA-WT/QTS-100-01-L-D-RA-WT
Part description: QSS/QTS-RA

 Page 7 of 17

RESULTS

CONTACTS POWERED - Temperature Rise, CCC at a 20% de-rating

• CCC for a  30°C Temperature Rise -----------------------2.0 A per contact  with 2 contacts (2 x 1) powered

• CCC for a  30°C Temperature Rise-----------------------1.7 A per contact  with  4 contacts (2 x 2) powered

• CCC for a  30°C Temperature Rise-----------------------1.3 A per contact  with  6 contacts (2 x 3) powered

• CCC for a  30°C Temperature Rise-----------------------1.2 A per contact  with  8 contacts (2 x 4) powered

• CCC for a  30°C Temperature Rise -----------------------0.5  A per contact  with  200 contacts (2 x 100) powered

GROUND PLANES POWERED - Temperature Rise, CCC at a 20% de-rating

• CCC for a  30°C Temperature Rise -----------------------15.7 A per ground plane  with 1 ground plane powered

• CCC for a  30°C Temperature Rise -----------------------12.7 A per ground plane with 2 ground planes powered

• CCC for a  30°C Temperature Rise -----------------------11.8 A per ground plane with 3 ground planes powered

• CCC for a  30°C Temperature Rise -----------------------9.5 A per ground plane with 4 ground planes powered
```

### Page 8

```text
Tracking Code: TC0748--1505 Part #: QSS-100-01-L-D-RA-WT/QTS-100-01-L-D-RA-WT
Part description: QSS/QTS-RA

 Page 8 of 17

CURRENT CARRYING CAPACITY DATA

CONTACT CCC – 2 POWERED (2 X 1)

TC0748--1505
2x1 Contacts Powered
QSS-100-01-L-D-RA-WT / QTS-100-01-L-D-RA-WT
4.674.67
3.743.74
2.912.91
2.332.33
2.512.51
2.012.01
1.421.42
1.141.14
0.0
1.0
2.0
3.0
4.0
5.0
6.0
20 40 60 80 100 120 140
A mbient T emperature,  ° C
Maximum Current, Amp per Contact
Base Curve
Derated 20 %
RT Peak Amp
RT Derated A mp
Measured Current
85 ° C
85  ° C Peak Amp
85  ° C Derated Amp
95  ° C
95  ° C Peak Amp
95  ° C Derated Amp
Limit
115  ° C Peak Amp
115  ° C Derated Amp
115  ° C
Room Temp
125° C
Limit
Useful Range
Room Temp= 24.1 C
30 Deg. Rise / 20% Derated = 2.0 Amps
```

### Page 9

```text
Tracking Code: TC0748--1505 Part #: QSS-100-01-L-D-RA-WT/QTS-100-01-L-D-RA-WT
Part description: QSS/QTS-RA

 Page 9 of 17

CURRENT CARRYING CAPACITY DATA continued

CONTACT CCC – 4 POWERED (2 X 2)

TC0748--1505
2x2 Contacts Powered
QSS-100-01-L-D-RA-WT / QTS-100-01-L-D-RA-WT
3.963.96
3.173.17
2.452.45
1.961.96
2.12.1
1.681.68
1.171.17
0.940.94
0.0
0.5
1.0
1.5
2.0
2.5
3.0
3.5
4.0
4.5
5.0
20 40 60 80 100 120 140
A mbient Temperature,  ° C
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
Accuracy: See Manual Current Carrying Capacity (CCC) Chamber
… Last Cal: 10/25/2007, Next Cal: 10/25/2008

Equipment #: MO-04
Description: Multimeter /Data Acquisition System
Manufacturer:  Keithley
Model:  2700
Serial #:  0798688
Accuracy: See Manual
… Last Cal: 03/8/07, Next Cal: 03/8/08

Equipment #: TC111307-(001 - 017)
Description: CCC Chamber Thermocouples
Manufacturer:  Samtec
Model:
Serial #:  TC111307-(001 - 017)
Accuracy: +/- 1 Deg.
… Last Cal: 11/30/2007, Next Cal: 11/30/2008

…
```
