thepinkmile/Enigma-NG/design/Datasheets/Samtec-QSS-Qualification_test-Report.md

# Project Number: Design Qualification Test Report Tr acking Code: 172626_Report_Rev_3

## Source

- **Source PDF:** [Samtec-QSS-Qualification_test-Report.pdf](Samtec-QSS-Qualification_test-Report.pdf)
- **Generated Markdown:** `Samtec-QSS-Qualification_test-Report.md`
- **Page count:** 35
- **Conversion method:** automated local PDF text extraction with pypdf/pdfplumber

## PDF Metadata

| Field | Value |
| :--- | :--- |
| Title | Microsoft Word - 172626_REPORT_REV_3.doc |
| Author | kasonh |
| Subject |  |
| Creator | PScript5.dll Version 5.2.2 |
| Producer | GPL Ghostscript 8.15 |

## Extracted Technical Index

This markdown datasheet is meant to reduce the need to reopen the PDF during design work.
It preserves design-relevant extracted snippets first, followed by page-by-page text so the source content remains locally searchable.

### Part number and ordering information

- 172626 / 2(2X1) Signal Pins in Series / Part Numbers: QSS-100-01-L-D-A/QTS-100-01-L-D-A / 4.2 4.2 / 3.4 3.4
- 172626 / 4(2X2) Signal Pins in Series / Part Numbers: QSS-100-01-L-D-A/QTS-100-01-L-D-A / 3.4 3.4 / 2.7 2.7
- 172626 / 6(2X3) Signal Pins in Series / Part Numbers: QSS-100-01-L-D-A/QTS-100-01-L-D-A / 2.7 2.7 / 2.2 2.2
- 172626 / 8(2X4) Signal Pins in Series / Part Numbers: QSS-100-01-L-D-A/QTS-100-01-L-D-A / 2.5 2.5 / 2.0 2.0
- 172626 / 200(All) Signal Pins in Series / Part Numbers: QSS-100-01-L-D-A/QTS-100-01-L-D-A / 1.1 1.1 / 0.9 0.9
- 282355 / 1 (1X1) Ground Plane in Series / Part Numbers: QSS-100-01-L-D-A/QTS-100-01-L-D-A / 54.2 54.2 / 43.4 43.4
- 282355 / 2 (1X2) Ground Planes in Series / Part Numbers: QSS-100-01-L-D-A/QTS-100-01-L-D-A / 52.3 52.3 / 41.8 41.8
- 282355 / 3 (1X3) Ground Planes in Series / Part Numbers: QSS-100-01-L-D-A/QTS-100-01-L-D-A / 51.5 51.5 / 41.2 41.2
- 282355 / 4 (All Power) Ground Planes in Series / Part Numbers: QSS-100-01-L-D-A/QTS-100-01-L-D-A / 49.8 49.8 / 39.9 39.9

### Pin, pad, and connection designations

- Project Number: Design Qualification Test Report Tr acking Code: 172626\_Report\_Rev\_3 / Requested by: Eric Mings Date: 12/24/2013 Product R ev: / Part #: QSS-100-01-L-D-A/QTS -100-01-L-D-A Lot…
- Page 1 of 35 / Design Qualification Test Report / QSS/QTS
- QSS/QTS / QSS-100-01-L-D-A/QTS -100-01-L-D-A / Tracking Code: 172626\_Report\_Rev\_3 Part #: QSS-100- 01-L-D-A/QTS -100-01-L-D-A / Part description: QSS/QTS
- 3/6/2013 2 Update the data PC / 12/23/2013 3 Update the CCC data KH / Tracking Code: 172626\_Report\_Rev\_3 Part #: QSS-100- 01-L-D-A/QTS -100-01-L-D-A / Part description: QSS/QTS
- traceable standards according to IS0 10012-l and ANSI/NCSL 2540-1, as applicable. / All contents contained herein are the property of Samtec. No portion of this report, in part or in full shall …
- 8)  Solder Information: Lead free / 9)  Re-Flow Time/Temp: See accompanying profile. / Tracking Code: 172626\_Report\_Rev\_3 Part #: QSS-100- 01-L-D-A/QTS -100-01-L-D-A / Part description: QSS/Q…
- TYPICAL OVEN PROFILE (Soldering Parts to Test Boards) / Tracking Code: 172626\_Report\_Rev\_3 Part #: QSS-100- 01-L-D-A/QTS -100-01-L-D-A / Part description: QSS/QTS
- 20 mV Max, 100 mA Max / Use Keithley 580 or 3706 in 4 wire dry circuit mode / Tracking Code: 172626\_Report\_Rev\_3 Part #: QSS-100- 01-L-D-A/QTS -100-01-L-D-A / Part description: QSS/QTS
- Part # 2 Mated Sets / Break Down / Pin-to-Pin / Break Down / Pin-to-Pin
- Pin-to-Pin / Break Down / Pin-to-Pin / Break Down / Pin-to-Pin Pin-to-Pin
- Pin-to-Pin / Break Down / Pin-to-Pin Pin-to-Pin / 01 DW V/Break Down / Voltage
- (on both mated sets and on each / connector unmated) / Tracking Code: 172626\_Report\_Rev\_3 Part #: QSS-100- 01-L-D-A/QTS -100-01-L-D-A / Part description: QSS/QTS
- Part # 2 Mated Sets / Break Down / Pin-to-Ground / Break Down / Pin-to-Ground
- Pin-to-Ground / Break Down / Pin-to-Ground / Break Down / Pin-to-Ground Pin-to-Ground
- Pin-to-Ground / Break Down / Pin-to-Ground Pin-to-Ground / 01 DW V/Break Down / Voltage
- IR = EIA-364-21 / DWV = EIA-364-20, Test Condition 1 / Tracking Code: 172626\_Report\_Rev\_3 Part #: QSS-100- 01-L-D-A/QTS -100-01-L-D-A / Part description: QSS/QTS
- (TIN PLATING)  - Tabulate calculated current at RT, 65° C, 75° C and 95° C / after derating 20% and based on 105° C / Tracking Code: 172626\_Report\_Rev\_3 Part #: QSS-100- 01-L-D-A/QTS -100-01-…
- a.  Reference document: EIA-364-21, Insulation Resistance Test Procedure for Electrical Connectors . / b.  Test Conditions: / i.  Between Adjacent Contacts or Signal-to-Ground / ii.  Electrifica…
- a.  Reference document: EIA-364-20, Withstanding Voltage Test Procedure for Electrical Connectors . / b.  Test Conditions: / i.  Between Adjacent Contacts or Signal-to-Ground / ii.  Rate of Appl…
- c.  The working voltage shall be recorded as one-third (1/3) of the dielectric withstanding voltage (one- / fourth of the breakdown voltage) / Tracking Code: 172626\_Report\_Rev\_3 Part #: QSS-1…

### Specifications, ratings, and operating conditions

- TEST SAMPLES AND PREPARATION / 1)  All materials were manufactured in accordance with the applicable product specification. / 2)  All test samples were identified and encoded to maintain traceab…
- 13 Contact Gaps / 14 LLCR-2 / 15 Thermal Shock / (Mated and Undisturbed) / 16 LLCR-3
- 18 LLCR-4 / 19 Forces - Mating / Unmating / Thermal Shock = EIA-364-32, Table II, Test Condition I: / -55 oC to +85 oC 1/2 hour dwell, 100 cycles / Humidity = EIA-364-31, Test Condition B (240 H…
- Pin-to-Pin Pin-to-Pin / 01 DW V/Break Down / Voltage / DW V/Break Down / Voltage
- Voltage / DW V/Break Down / Voltage / DW V/Break Down / Voltage
- Voltage / DW V/Break Down / Voltage / IR & DW V at test voltage / (on both mated sets and on each
- DW V/Break Down / Voltage / IR & DW V at test voltage / (on both mated sets and on each / connector unmated)
- (on both mated sets and on each / connector unmated) / 02 Thermal Shock / (Mated and Undisturbed) / 03
- (Mated and Undisturbed) / 03 / IR & DW V at test voltage / (on both mated sets and on each / connector unmated)
- (Mated and Undisturbed) / 05 / IR & DW V at test voltage / (on both mated sets and on each / connector unmated)
- Row-to-Row Row-to-Row / 01 DW V/Break Down / Voltage / DW V/Break Down / Voltage
- Pin-to-Ground Pin-to-Ground / 01 DW V/Break Down / Voltage / DW V/Break Down / Voltage
- connector unmated) / DWV on Group B1 to be performed at Test Voltage / DWV test voltage is equal to 75% of the lowest brea k down voltage from Groups A1, A2 or A3 / Thermal Shock = EIA-364-32, T…
- DWV on Group B1 to be performed at Test Voltage / DWV test voltage is equal to 75% of the lowest brea k down voltage from Groups A1, A2 or A3 / Thermal Shock = EIA-364-32, Table II, Test Conditi…
- DWV on Group B1 to be performed at Test Voltage / DWV test voltage is equal to 75% of the lowest brea k down voltage from Groups A1, A2 or A3 / Thermal Shock = EIA-364-32, Table II, Test Conditi…
- FLOWCHARTS Continued / Current Carrying Capacity - Double Row / TEST GROUP B1 GROUP B2 GROUP B3 GROUP B4 GROUP B5 / STEP 3 Mated Assemblies 3 Mated Assemblies 3 Mated Ass emblies 3 Mated Assembl…
- 2 Contacts Powered 4 Contacts Powered 6 Contacts Powe red 8 Contacts Powered All Contacts Powered / 01 CCC CCC CCC CCC CCC / Current Carrying Capacity - Ground Planes / TEST GROUP C1 GROUP C2 GR…
- 01 CCC CCC CCC CCC / (GOLD PLATING)  - Tabulate calculated current at RT, 85° C, 95° C and 115° C / after derating 20% and based on 125° C / CCC, Temp rise = EIA-364-70
- after derating 20% and based on 125° C / CCC, Temp rise = EIA-364-70 / (TIN PLATING)  - Tabulate calculated current at RT, 65° C, 75° C and 95° C / after derating 20% and based on 105° C / Track…
- ATTRIBUTE DEFINITIONS / The following is a brief, simplified description of attributes. / THERMAL SHOCK: / 1)  EIA-364-32, Thermal Shock (Temperature Cycling) Test Procedure for Electrical Conne…

### Dimensions, package, and mechanical information

- No reliable text snippet was automatically extracted for this category. Review the raw page text below.

### Formulas, equations, and configurable calculations

- Standards: EIA Publication 364 / TEST SAMPLES AND PREPARATION / 1)  All materials were manufactured in accordance with the applicable product specification. / 2)  All test samples were identifie…
- 5)  The automated procedure is used with aqueous compatible soldering materials. / 6)  Parts not intended for testing LLCR and DWV/IR are visually inspected and cleaned if necessary. / 7)  Any a…
- 01 CCC CCC CCC CCC / (GOLD PLATING)  - Tabulate calculated current at RT, 85° C, 95° C and 115° C / after derating 20% and based on 125° C / CCC, Temp rise = EIA-364-70
- after derating 20% and based on 125° C / CCC, Temp rise = EIA-364-70 / (TIN PLATING)  - Tabulate calculated current at RT, 65° C, 75° C and 95° C / after derating 20% and based on 105° C / Track…
- i.  Between Adjacent Contacts or Signal-to-Ground / ii.  Electrification Time 2.0 minutes / iii.  Test Voltage (500 VDC) corresponds to calibration settings for measuring resistances. / 2)  MEAS…
- a.  Self heating (resistive) / b.  Reduction in heat sink capacity affecting the heated contacts / 6)  A de-rating curve, usually 20%, is calculated. / 7)  Calculated de-rated currents at three …
- b.  Reduction in heat sink capacity affecting the heated contacts / 6)  A de-rating curve, usually 20%, is calculated. / 7)  Calculated de-rated currents at three temperature points are reported…
- 8)  Typically, neighboring contacts (in close proximity to maximize heat build up) are energized. / 9)  The thermocouple (or temperature measuring probe) will be positioned at a location to sens…
- than 1° C (computer controlled data acquisition). / 4)  Adjacent contacts were powered: / a.  Linear configuration with 2 adjacent signal conductors/contacts powered / 172626 / 2(2X1) Signal Pin…
- DATA  SUMMARIES Continued / b.  Linear configuration with 4 adjacent signal conductors/contacts powered / 172626 / 4(2X2) Signal Pins in Series
- DATA  SUMMARIES Continued / c.  Linear configuration with 6 adjacent signal conductors/contacts powered / 172626 / 6(2X3) Signal Pins in Series
- DATA  SUMMARIES Continued / d.  Linear configuration with 8 adjacent signal conductors/contacts powered / 172626 / 8(2X4) Signal Pins in Series
- DATA  SUMMARIES Continued / e.  Linear configuration with all adjacent  signal conductors/contacts powered / 172626 / 200(All) Signal Pins in Series
- DATA  SUMMARIES Continued / f.  Linear configuration with 1 adjacent ground conductors/contacts powered / 282355 / 1 (1X1) Ground Plane in Series
- DATA  SUMMARIES Continued / g.  Linear configuration with 2 adjacent ground conductors/contacts powered / 282355 / 2 (1X2) Ground Planes in Series
- DATA  SUMMARIES Continued / h.  Linear configuration with 3 adjacent ground conductors/contacts powered / 282355 / 3 (1X3) Ground Planes in Series
- DATA  SUMMARIES Continued / i.  Linear configuration with all adjacent ground conductors/contacts powered / 282355 / 4 (All Power) Ground Planes in Series
- Page 34 of 35 / EQUIPMENT AND CALIBRATION SCHEDULES / Equipment #: HZ-MO-05
- Page 35 of 35 / EQUIPMENT AND CALIBRATION SCHEDULES / Equipment #: HZ-TSC-01 / Description:  Thermal Shock transmitter

### Reference designs, applications, and examples

- b.  Test Conditions: / i.  Between Adjacent Contacts or Signal-to-Ground / ii.  Rate of Application 500 V/Sec / iii.  Test Voltage (VAC) until breakdown occurs / 2)  MEASUREMENTS/CALCULATIONS

## Page-by-Page Extracted Content

### Page 1

```text
Project Number: Design Qualification Test Report Tr acking Code: 172626_Report_Rev_3
Requested by: Eric Mings Date: 12/24/2013 Product R ev:
Part #: QSS-100-01-L-D-A/QTS -100-01-L-D-A Lot #: N /A Tech: Peter Chen Eng: Vico Zhao
Part description: QSS/QTS Qty to test: 40
Test Start: 02/20/2012 Test Completed: 03/25/2012

                                                                                          Page 1 of 35

Design Qualification Test Report

QSS/QTS
QSS-100-01-L-D-A/QTS -100-01-L-D-A
```

### Page 2

```text
Tracking Code: 172626_Report_Rev_3 Part #: QSS-100- 01-L-D-A/QTS -100-01-L-D-A
Part description: QSS/QTS

                                                                                               Page 2 of 35
REVISION HISTORY

DATA REV.NUM. DESCRIPTION ENG
11/28/2012 1 Initial Issue PC
3/6/2013 2 Update the data PC
12/23/2013 3 Update the CCC data KH
```

### Page 3

```text
Tracking Code: 172626_Report_Rev_3 Part #: QSS-100- 01-L-D-A/QTS -100-01-L-D-A
Part description: QSS/QTS

                                                                                               Page 3 of 35

CERTIFICATION

All instruments and measuring equipment were calibrated to National Institute for Standards and Technology (NIST)
traceable standards according to IS0 10012-l and ANSI/NCSL 2540-1, as applicable.

All contents contained herein are the property of Samtec. No portion of this report, in part or in full shall be
reproduced without prior written approval of Samtec.

SCOPE
 To perform the following tests: Design Qualificati on Test, Please see test plan.

APPLICABLE DOCUMENTS
 Standards: EIA Publication 364

TEST SAMPLES AND PREPARATION
1)  All materials were manufactured in accordance with the applicable product specification.
2)  All test samples were identified and encoded to maintain traceability throughout the test sequences.
3)  After soldering, the parts to be used for LLCR and DWV/IR testing were cleaned according to TLWI-0001.
4)  Either an automated cleaning procedure or an ultrasonic cleaning procedure may be used.
5)  The automated procedure is used with aqueous compatible soldering materials.
6)  Parts not intended for testing LLCR and DWV/IR are visually inspected and cleaned if necessary.
7)  Any additional preparation will be noted in the individual test sequences.
8)  Solder Information: Lead free
9)  Re-Flow Time/Temp: See accompanying profile.
```

### Page 4

```text
Tracking Code: 172626_Report_Rev_3 Part #: QSS-100- 01-L-D-A/QTS -100-01-L-D-A
Part description: QSS/QTS

                                                                                               Page 4 of 35

TYPICAL OVEN PROFILE (Soldering Parts to Test Boards)
```

### Page 5

```text
Tracking Code: 172626_Report_Rev_3 Part #: QSS-100- 01-L-D-A/QTS -100-01-L-D-A
Part description: QSS/QTS

                                                                                               Page 5 of 35
FLOWCHARTS
Durability/Mating/Unmating/Gaps
TEST GROUP B1 GROUP B2 GROUP B3 GROUP B4
STEP 8 Boards
(4 Bank)
8 Boards
(3 Bank)
8 Boards
(2 Bank)
8 Boards
(1 Bank)
01 Contact Gaps Contact Gaps Contact Gaps Contact Gaps
02 LLCR-1 Forces - Mating / Unmating Forces - Mating / U nmating Forces - Mating / Unmating
03 Forces - Mating / Unmating 25 Cycles 25 Cycles 25 Cycl es
04 25 Cycles Forces - Mating / Unmating Forces - Mating / Unmating Forces - Mating / Unmating
05 Forces - Mating / Unmating 25 Cycles (50 Total) 25 Cy cles (50 Total) 25 Cycles (50 Total)
06 25 Cycles (50 Total) Forces - Mating / Unmating Force s - Mating / Unmating Forces - Mating / Unmating
07 Forces - Mating / Unmating 25 Cycles (75 Total) 25 Cy cles (75 Total) 25 Cycles (75 Total)
08 25 Cycles (75 Total) Forces - Mating / Unmating Force s - Mating / Unmating Forces - Mating / Unmating
09 Forces - Mating / Unmating 25 Cycles (100 Total) 25 C ycles (100 Total) 25 Cycles (100 Total)
10 25 Cycles (100 Total) Forces - Mating / Unmating Forc es - Mating / Unmating Forces - Mating / Unmating
11 Forces - Mating / Unmating
12 Clean w/Compressed Air
13 Contact Gaps
14 LLCR-2
15 Thermal Shock
(Mated and Undisturbed)
16 LLCR-3
17 Cyclic Humidity
(Mated and Undisturbed)
18 LLCR-4
19 Forces - Mating / Unmating
Thermal Shock = EIA-364-32, Table II, Test Condition I:
-55 oC to +85 oC 1/2 hour dwell, 100 cycles
Humidity = EIA-364-31, Test Condition B (240 Hours)
and Method III (+25° C to +65° C @  90% RH to 98% RH)
ambient pre-condition and delete steps 7a and 7b
Mating / Unmating Forces = EIA-364-13
Contact Gaps / Height - No standard method.  Usually measured optically.
Gaps to be taken on a minimum of 20% of each part tested
LLCR = EIA-364-23, LLCR
20 mV Max, 100 mA Max
Use Keithley 580 or 3706 in 4 wire dry circuit mode
```

### Page 6

```text
Tracking Code: 172626_Report_Rev_3 Part #: QSS-100- 01-L-D-A/QTS -100-01-L-D-A
Part description: QSS/QTS

                                                                                               Page 6 of 35
FLOWCHARTS Continued
IR & DWV
TEST GROUP A1 GROUP A2 GROUP A3 GROUP B1
STEP 2 Mated Sets 2 Unmated of Part #
Being Tested
2 Unmated of Mating
Part # 2 Mated Sets
Break Down
Pin-to-Pin
Break Down
Pin-to-Pin
Break Down
Pin-to-Pin Pin-to-Pin
01 DW V/Break Down
Voltage
DW V/Break Down
Voltage
DW V/Break Down
Voltage
IR & DW V at test voltage
(on both mated sets and on each
connector unmated)
02 Thermal Shock
(Mated and Undisturbed)
03
IR & DW V at test voltage
(on both mated sets and on each
connector unmated)
04 Cyclic Humidity
(Mated and Undisturbed)
05
IR & DW V at test voltage
(on both mated sets and on each
connector unmated)

TEST GROUP C1 GROUP C2 GROUP C3 GROUP D1
STEP 2 Mated Sets 2 Unmated of Part #
Being Tested
2 Unmated of Mating
Part # 2 Mated Sets
Break Down
Row-to-Row
Break Down
Row-to-Row
Break Down
Row-to-Row Row-to-Row
01 DW V/Break Down
Voltage
DW V/Break Down
Voltage
DW V/Break Down
Voltage
IR & DW V at test voltage
(on both mated sets and on each
connector unmated)
02 Thermal Shock
(Mated and Undisturbed)
03
IR & DW V at test voltage
(on both mated sets and on each
connector unmated)
04 Cyclic Humidity
(Mated and Undisturbed)
05
IR & DW V at test voltage
(on both mated sets and on each
connector unmated)
```

### Page 7

```text
Tracking Code: 172626_Report_Rev_3 Part #: QSS-100- 01-L-D-A/QTS -100-01-L-D-A
Part description: QSS/QTS

                                                                                               Page 7 of 35
FLOWCHARTS Continued

TEST GROUP E1 GROUP E2 GROUP E3 GROUP F1
STEP 2 Mated Sets 2 Unmatedof Part #
Being Tested
2 Unmated of Mating
Part # 2 Mated Sets
Break Down
Pin-to-Ground
Break Down
Pin-to-Ground
Break Down
Pin-to-Ground Pin-to-Ground
01 DW V/Break Down
Voltage
DW V/Break Down
Voltage
DW V/Break Down
Voltage
IR & DW V at test voltage
(on both mated sets and on each
connector unmated)
02 Thermal Shock
(Mated and Undisturbed)
03
IR & DW V at test voltage
(on both mated sets and on each
connector unmated)
04 Cyclic Humidity
(Mated and Undisturbed)
05
IR & DW V at test voltage
(on both mated sets and on each
connector unmated)

DWV on Group B1 to be performed at Test Voltage
DWV test voltage is equal to 75% of the lowest brea k down voltage from Groups A1, A2 or A3
Thermal Shock = EIA-364-32, Table II, Test Condition I:
-55 oC to +85 oC 1/2 hour dwell, 100 cycles
Humidity = EIA-364-31, Test Condition B (240 Hours)
and Method III (+25° C to +65° C @  90% RH to 98% RH)
ambient pre-condition and delete steps 7a and 7b
IR = EIA-364-21
DWV = EIA-364-20, Test Condition 1
```

### Page 8

```text
Tracking Code: 172626_Report_Rev_3 Part #: QSS-100- 01-L-D-A/QTS -100-01-L-D-A
Part description: QSS/QTS

                                                                                               Page 8 of 35
FLOWCHARTS Continued

Current Carrying Capacity - Double Row
TEST GROUP B1 GROUP B2 GROUP B3 GROUP B4 GROUP B5
STEP 3 Mated Assemblies 3 Mated Assemblies 3 Mated Ass emblies 3 Mated Assemblies 3 Mated Assemblies
2 Contacts Powered 4 Contacts Powered 6 Contacts Powe red 8 Contacts Powered All Contacts Powered
01 CCC CCC CCC CCC CCC
Current Carrying Capacity - Ground Planes
TEST GROUP C1 GROUP C2 GROUP C3 GROUP C4
STEP 3 Mated Assemblies 3 Mated Assemblies 3 Mated Ass emblies 3 Mated Assemblies
1 Ground Plane
Powered
2 Ground Planes
Powered
3 Ground Planes
Powered
4 Ground Planes
Powered
01 CCC CCC CCC CCC

(GOLD PLATING)  - Tabulate calculated current at RT, 85° C, 95° C and 115° C
after derating 20% and based on 125° C
CCC, Temp rise = EIA-364-70
(TIN PLATING)  - Tabulate calculated current at RT, 65° C, 75° C and 95° C
after derating 20% and based on 105° C
```

### Page 9

```text
Tracking Code: 172626_Report_Rev_3 Part #: QSS-100- 01-L-D-A/QTS -100-01-L-D-A
Part description: QSS/QTS

                                                                                               Page 9 of 35
ATTRIBUTE DEFINITIONS
The following is a brief, simplified description of attributes.
THERMAL SHOCK:
1)  EIA-364-32, Thermal Shock (Temperature Cycling) Test Procedure for Electrical Connectors.
2)  Test Condition 1:  -55° C to +85°C
3)  Test Time:  ½ hour dwell at each temperature extreme
4)  Number of Cycles:  100
5)  All test samples are pre-conditioned at ambient.
6)  All test samples are exposed to environmental stressing in the mated condition.

HUMIDITY:
1)  Reference document: EIA-364-31, Humidity Test Procedure for Electrical Connectors.
2)  Test Condition B, 240 Hours.
3)  Method III, +25° C to + 65° C, 90% to 98% Relative Humidity excluding sub-cycles 7a and 7b.
4)  All samples are pre-conditioned at ambient.
5)  All test samples are exposed to environmental stressing in the mated condition.

MATING/UNMATING:
1)  Reference document: EIA-364-13, Mating and Unmating Forces Test Procedure for Electrical Connectors .
2)  The full insertion position was to within 0.003” to 0.004” of the plug bottoming out in the receptacle to
prevent damage to the system under test.
3)  One of the mating parts is secured to a floating X-Y table to prevent damage during cycling.

INSULATION RESISTANCE (IR):
To determine the resistance of insulation materials to leakage of current through or on the surface of these
materials when a DC potential is applied.
1)  PROCEDURE:
a.  Reference document: EIA-364-21, Insulation Resistance Test Procedure for Electrical Connectors .
b.  Test Conditions:
i.  Between Adjacent Contacts or Signal-to-Ground
ii.  Electrification Time 2.0 minutes
iii.  Test Voltage (500 VDC) corresponds to calibration settings for measuring resistances.
2)  MEASUREMENTS:
3)  When the specified test voltage is applied (VDC), the insulation resistance shall not be less than 5000
megohms.

DIELECTRIC WITHSTANDING VOLTAGE (DWV):
To determine if the sockets can operate at its rated voltage and withstand momentary over potentials due to
switching, surges, and other similar phenomenon.  Separate samples are used to evaluate the effect of
environmental stresses so not to influence the readings from arcing that occurs during the measurement
process.
1)  PROCEDURE:
a.  Reference document: EIA-364-20, Withstanding Voltage Test Procedure for Electrical Connectors .
b.  Test Conditions:
i.  Between Adjacent Contacts or Signal-to-Ground
ii.  Rate of Application 500 V/Sec
iii.  Test Voltage (VAC) until breakdown occurs
2)  MEASUREMENTS/CALCULATIONS
a.  The breakdown voltage shall be measured and recorded.
b.  The dielectric withstanding voltage shall be recorded as 75% of the minimum breakdown voltage.
c.  The working voltage shall be recorded as one-third (1/3) of the dielectric withstanding voltage (one-
fourth of the breakdown voltage)
```

### Page 10

```text
Tracking Code: 172626_Report_Rev_3 Part #: QSS-100- 01-L-D-A/QTS -100-01-L-D-A
Part description: QSS/QTS

                                                                                               Page 10 of 35

ATTRIBUTE DEFINITIONS
The following is a brief, simplified description of attributes.

TEMPERATURE RISE (Current Carrying Capacity, CCC):
1)  EIA-364-70, Temperature Rise versus Current Test Procedure for Electrical Connectors and Sockets .
2)   When current passes through a contact, the temperature of the contact increases as a result of I2R (resistive)
heating.
3)  The number of contacts being investigated plays a significant part in power dissipation and therefore
temperature rise.
4)  The size of the temperature probe can affect the measured temperature.
5)  Copper traces on PC boards will contribute to temperature rise:
a.  Self heating (resistive)
b.  Reduction in heat sink capacity affecting the heated contacts
6)  A de-rating curve, usually 20%, is calculated.
7)  Calculated de-rated currents at three temperature points are reported:
a.  Ambient
b.  85о C
c.  95 о C
d.  115 о C
8)  Typically, neighboring contacts (in close proximity to maximize heat build up) are energized.
9)  The thermocouple (or temperature measuring probe) will be positioned at a location to sense the maximum
temperature in the vicinity of the heat generation area.
10)  A computer program, TR 803.exe , ensures accurate stability for data acquisition.
11)  Hook-up wire cross section is larger than the cross section of any connector leads/PC board traces, jumpers,
etc.
12)  Hook-up wire length is longer than the minimum specified in the referencing standard.

LLCR:
1)  EIA-364-23, Low Level Contact Resistance  Test Procedure for Electrical Connectors and Sockets .
2)  A computer program, LLCR 221.exe , ensures repeatability for data acquisition.
3)  The following guidelines are used to categorize the changes in LLCR as a result from stressing
a.  <= +5.0 mOhms: ----------------------------- Stable
b.  +5.1 to +10.0 mOhms: ---------------------- Minor
c.  +10.1 to +15.0 mOhms: -------------------- Acceptable
d.  +15.1 to +50.0 mOhms: -------------------- Marginal
e.  +50.1 to +2000 mOhms: ------------------- Unstable
f.  >+2000 mOhms: ----------------------------- Open Failure
```

### Page 11

```text
Tracking Code: 172626_Report_Rev_3 Part #: QSS-100- 01-L-D-A/QTS -100-01-L-D-A
Part description: QSS/QTS

                                                                                               Page 11 of 35
RESULTS
Temperature Rise, CCC at a 20% de-rating
• CCC for a  30°C Temperature Rise --------------- 1.8 A per contact  with 2 adjacent signal contacts powered
• CCC for a  30°C Temperature Rise --------------- 1.4 A per contact  with 4 adjacent signal contacts powered
• CCC for a  30°C Temperature Rise --------------- 1.2 A per contact  with 6 adjacent signal contacts powered
• CCC for a  30°C Temperature Rise --------------- 1.1 A per contact  with 8 adjacent signal contacts powered
• CCC for a  30°C Temperature Rise --------------- 0.5 A per contact  with all adjacent signal contacts  powered
• CCC for a  30°C Temperature Rise --------------- 23.1 A per contact  with 1 adjacent ground contacts p owered
• CCC for a  30°C Temperature Rise --------------- 22.1 A per contact  with 2 adjacent ground contacts p owered
• CCC for a  30°C Temperature Rise --------------- 21.7 A per contact  with 3 adjacent ground contacts p owered
• CCC for a  30°C Temperature Rise --------------- 21.2 A per contact  with 4 adjacent ground contacts p owered

Mating /unmating force
Mating&Unmating durability (QSS-100-01-L-D-A/QTS -1 00-01-L-D-A):
• Initial
o Mating
/square4 Min -------------------------------------- 11.79 Lbs
/square4 Max -------------------------------------- 14.03 Lbs
o Unmating
/square4 Min --------------------------------------- 7.31 Lbs
/square4 Max --------------------------------------- 9.82  Lbs
• After 25 Cycles
o Mating
/square4 Min -------------------------------------- 12.80 Lbs
/square4 Max -------------------------------------- 15.13 Lbs
o Unmating
/square4 Min --------------------------------------- 8.21 Lbs
/square4 Max -------------------------------------- 11.07 Lbs
• After 50 Cycles
o Mating
/square4 Min -------------------------------------- 13.41 Lbs
/square4 Max -------------------------------------- 16.19 Lbs
o Unmating
/square4 Min --------------------------------------- 9.13 Lbs
/square4 Max -------------------------------------- 12.14 Lbs
• After 75 Cycles
o Mating
/square4 Min -------------------------------------- 13.97 Lbs
/square4 Max -------------------------------------- 16.84 Lbs
o Unmating
/square4 Min -------------------------------------- 10.08 Lbs
/square4 Max -------------------------------------- 13.24 Lbs
• After 100 Cycles
o Mating
/square4 Min -------------------------------------- 14.41 Lbs
/square4 Max -------------------------------------- 17.75 Lbs
o Unmating
/square4 Min -------------------------------------- 10.93 Lbs
/square4 Max -------------------------------------- 13.91 Lb
• After Humidity
o Mating
/square4 Min --------------------------------------- 9.65 Lbs
/square4 Max -------------------------------------- 13.36 Lbs
o Unmating
/square4 Min --------------------------------------- 9.65 Lbs
/square4 Max -------------------------------------- 11.69 Lbs
```

### Page 12

```text
Tracking Code: 172626_Report_Rev_3 Part #: QSS-100- 01-L-D-A/QTS -100-01-L-D-A
Part description: QSS/QTS

                                                                                               Page 12 of 35
RESULTS Continued
Mating/Unmating basic (QSS-075-01-L-D-A/QTS -075-01 -L-D-A):
• Initial
o Mating
/square4 Min --------------------------------------- 8.96 Lbs
/square4 Max -------------------------------------- 11.00 Lbs
o Unmating
/square4 Min --------------------------------------- 7.29 Lbs
/square4 Max --------------------------------------- 8.86  Lbs
• After 25 Cycles
o Mating
/square4 Min -------------------------------------- 10.32 Lbs
/square4 Max -------------------------------------- 12.72 Lbs
o Unmating
/square4 Min --------------------------------------- 8.66 Lbs
/square4 Max -------------------------------------- 10.77 Lbs
• After 50 Cycles
o Mating
/square4 Min -------------------------------------- 11.17 Lbs
/square4 Max -------------------------------------- 14.99 Lbs
o Unmating
/square4 Min --------------------------------------- 9.18 Lbs
/square4 Max -------------------------------------- 11.80 Lbs
• After 75 Cycles
o Mating
/square4 Min -------------------------------------- 11.13 Lbs
/square4 Max -------------------------------------- 15.64 Lbs
o Unmating
/square4 Min --------------------------------------- 9.11 Lbs
/square4 Max -------------------------------------- 12.47 Lbs
• After 100 Cycles
o Mating
/square4 Min -------------------------------------- 11.86 Lbs
/square4 Max -------------------------------------- 16.36 Lbs
o Unmating
/square4 Min --------------------------------------- 9.86 Lbs
/square4 Max -------------------------------------- 12.96 Lbs
```

### Page 13

```text
Tracking Code: 172626_Report_Rev_3 Part #: QSS-100- 01-L-D-A/QTS -100-01-L-D-A
Part description: QSS/QTS

                                                                                               Page 13 of 35
RESULTS Continued
Mating/Unmating basic (QSS-050-01-L-D-A/QTS -050-01 -L-D-A):
• Initial
o Mating
/square4 Min --------------------------------------- 5.50 Lbs
/square4 Max --------------------------------------- 6.02 Lbs
o Unmating
/square4 Min --------------------------------------- 3.58 Lbs
/square4 Max --------------------------------------- 5.68  Lbs
• After 25 Cycles
o Mating
/square4 Min --------------------------------------- 6.36 Lbs
/square4 Max --------------------------------------- 6.88 Lbs
o Unmating
/square4 Min --------------------------------------- 4.42 Lbs
/square4 Max --------------------------------------- 6.78 Lbs
• After 50 Cycles
o Mating
/square4 Min --------------------------------------- 6.79 Lbs
/square4 Max --------------------------------------- 7.64 Lbs
o Unmating
/square4 Min --------------------------------------- 4.93 Lbs
/square4 Max --------------------------------------- 7.36 Lbs
• After 75 Cycles
o Mating
/square4 Min --------------------------------------- 7.04 Lbs
/square4 Max --------------------------------------- 7.89 Lbs
o Unmating
/square4 Min --------------------------------------- 5.16 Lbs
/square4 Max --------------------------------------- 7.84 Lbs
• After 100 Cycles
o Mating
/square4 Min --------------------------------------- 7.30 Lbs
/square4 Max --------------------------------------- 8.20 Lbs
o Unmating
/square4 Min --------------------------------------- 5.34 Lbs
/square4 Max --------------------------------------- 7.98 Lbs
```

### Page 14

```text
Tracking Code: 172626_Report_Rev_3 Part #: QSS-100- 01-L-D-A/QTS -100-01-L-D-A
Part description: QSS/QTS

                                                                                               Page 14 of 35
RESULTS Continued
Mating/Unmating basic (QSS-025-01-L-D-A/QTS -025-01 -L-D-A):
• Initial
o Mating
/square4 Min --------------------------------------- 2.90 Lbs
/square4 Max --------------------------------------- 4.22 Lbs
o Unmating
/square4 Min --------------------------------------- 3.10 Lbs
/square4 Max --------------------------------------- 3.95  Lbs
• After 25 Cycles
o Mating
/square4 Min --------------------------------------- 3.47 Lbs
/square4 Max --------------------------------------- 4.13 Lbs
o Unmating
/square4 Min --------------------------------------- 3.23 Lbs
/square4 Max --------------------------------------- 4.04 Lbs
• After 50 Cycles
o Mating
/square4 Min --------------------------------------- 3.61 Lbs
/square4 Max --------------------------------------- 4.33 Lbs
o Unmating
/square4 Min --------------------------------------- 3.54 Lbs
/square4 Max --------------------------------------- 4.33 Lbs
• After 75 Cycles
o Mating
/square4 Min --------------------------------------- 3.63 Lbs
/square4 Max --------------------------------------- 4.41 Lbs
o Unmating
/square4 Min --------------------------------------- 3.70 Lbs
/square4 Max --------------------------------------- 4.68 Lbs
• After 100 Cycles
o Mating
/square4 Min --------------------------------------- 3.82 Lbs
/square4 Max --------------------------------------- 4.56 Lbs
o Unmating
/square4 Min --------------------------------------- 3.72 Lbs
/square4 Max --------------------------------------- 4.90 Lbs
```

### Page 15

```text
Tracking Code: 172626_Report_Rev_3 Part #: QSS-100- 01-L-D-A/QTS -100-01-L-D-A
Part description: QSS/QTS

                                                                                               Page 15 of 35
RESULTS Continued
LLCR Durability (192 pin include 176 signal and 16 ground LLCR test points)
    Signal pin:
• Initial ------------------------------------------- -------------------- 29.73 mOhms Max
• After 100 Cycles
o <= +5.0 mOhms  ---------------------------------- 169 Points ------------------------- Stable
o +5.1 to +10.0 mOhms ----------------------------------- 7 Points ------------------------- Minor
o +10.1 to +15.0 mOhms ------------------------------ --- 0 Points ------------------------- Acceptable
o +15.1 to +50.0 mOhms ------------------------------ --- 0 Points ------------------------- Marginal
o +50.1 to +2000 mOhms --------------------------------- 0 Points ------------------------- Unstable
o >+2000 mOhms ------------------------------------------ 0 Points ------------------------- Open Failure
• After thermal shock
o <= +5.0 mOhms  ---------------------------------- 156 Points ------------------------- Stable
o +5.1 to +10.0 mOhms --------------------------------- 20 Points ------------------------- Minor
o +10.1 to +15.0 mOhms ------------------------------ --- 0 Points ------------------------- Acceptable
o +15.1 to +50.0 mOhms ------------------------------ --- 0 Points ------------------------- Marginal
o +50.1 to +2000 mOhms --------------------------------- 0 Points ------------------------- Unstable
o >+2000 mOhms ------------------------------------------ 0 Points ------------------------- Open Failure
• After humidity
o <= +5.0 mOhms  ---------------------------------- 160 Points ------------------------- Stable
o +5.1 to +10.0 mOhms --------------------------------- 16 Points ------------------------- Minor
o +10.1 to +15.0 mOhms ------------------------------ --- 0 Points ------------------------- Acceptable
o +15.1 to +50.0 mOhms ------------------------------ --- 0 Points ------------------------- Marginal
o +50.1 to +2000 mOhms --------------------------------- 0 Points ------------------------- Unstable
o >+2000 mOhms ------------------------------------------ 0 Points ------------------------- Open Failure
Ground pin:
• Initial ------------------------------------------- ---------------------- 3.05 mOhms Max
• After 100 Cycles
o <= +5.0 mOhms  ------------------------------------ 16 Points ------------------------- Stable
o +5.1 to +10.0 mOhms ----------------------------------- 0 Points ------------------------- Minor
o +10.1 to +15.0 mOhms ------------------------------ --- 0 Points ------------------------- Acceptable
o +15.1 to +50.0 mOhms ------------------------------ --- 0 Points ------------------------- Marginal
o +50.1 to +2000 mOhms --------------------------------- 0 Points ------------------------- Unstable
o >+2000 mOhms ------------------------------------------ 0 Points ------------------------- Open Failure
• After thermal shock
o <= +5.0 mOhms  ------------------------------------ 16 Points ------------------------- Stable
o +5.1 to +10.0 mOhms ----------------------------------- 0 Points ------------------------- Minor
o +10.1 to +15.0 mOhms ------------------------------ --- 0 Points ------------------------- Acceptable
o +15.1 to +50.0 mOhms ------------------------------ --- 0 Points ------------------------- Marginal
o +50.1 to +2000 mOhms --------------------------------- 0 Points ------------------------- Unstable
o >+2000 mOhms ------------------------------------------ 0 Points ------------------------- Open Failure
• After humidity
o <= +5.0 mOhms  ------------------------------------ 16 Points ------------------------- Stable
o +5.1 to +10.0 mOhms ----------------------------------- 0 Points ------------------------- Minor
o +10.1 to +15.0 mOhms ------------------------------ --- 0 Points ------------------------- Acceptable
o +15.1 to +50.0 mOhms ------------------------------ --- 0 Points ------------------------- Marginal
o +50.1 to +2000 mOhms --------------------------------- 0 Points ------------------------- Unstable
o >+2000 mOhms ------------------------------------------ 0 Points ------------------------- Open Failure
```

### Page 16

```text
Tracking Code: 172626_Report_Rev_3 Part #: QSS-100- 01-L-D-A/QTS -100-01-L-D-A
Part description: QSS/QTS

                                                                                               Page 16 of 35
RESULTS Continued
Insulation Resistance minimums, IR
Pin-Pin
• Initial
o Mated ------------------------------------------------ 10000Meg Ω ------------------------- Pass
o Unmated ------------------------------------------- - 10000Meg Ω  ------------------------ Pass
• Thermal
o Mated ------------------------------------------------ 10000Meg Ω  ------------------------ Pass
o Unmated ------------------------------------------- - 10000Meg Ω  ------------------------ Pass
• Humidity
o Mated ------------------------------------------------ 10000Meg Ω  ------------------------ Pass
o Unmated ------------------------------------------- - 10000Meg Ω  ------------------------ Pass
Row-Row
• Initial
o Mated ------------------------------------------------ 10000Meg Ω ------------------------- Pass
o Unmated ------------------------------------------- - 10000Meg Ω  ------------------------ Pass
• Thermal
o Mated ------------------------------------------------ 10000Meg Ω  ------------------------ Pass
o Unmated ------------------------------------------- - 10000Meg Ω  ------------------------ Pass
• Humidity
o Mated ------------------------------------------------ 10000Meg Ω  ------------------------ Pass
o Unmated ------------------------------------------- - 10000Meg Ω  ------------------------ Pass
Pin-Ground
• Initial
o Mated ------------------------------------------------ 10000Meg Ω ------------------------- Pass
o Unmated ------------------------------------------- - 10000Meg Ω  ------------------------ Pass
• Thermal
o Mated ------------------------------------------------ 10000Meg Ω  ------------------------ Pass
o Unmated ------------------------------------------- - 10000Meg Ω  ------------------------ Pass
• Humidity
o Mated ------------------------------------------------ 10000Meg Ω  ------------------------ Pass
o Unmated ------------------------------------------- - 10000Meg Ω  ------------------------ Pass

Dielectric Withstanding Voltage minimums, DWV
• Minimums
o Breakdown Voltage -------------------------------- 1000 VAC
o Test Voltage -------------------------------------- ----- 750 VAC
o Working Voltage ----------------------------------- -- 250 VAC
Pin - pin
• Initial DWV --------------------------------------- ----------- Passed
• Thermal DWV ----------------------------------------------- Passed
• Humidity DWV ---------------------------------------------- Passed
Row-Row
• Initial DWV --------------------------------------- ----------- Passed
• Thermal DWV ----------------------------------------------- Passed
• Humidity DWV ---------------------------------------------- Passed
Pin-Ground
• Initial DWV --------------------------------------- ----------- Passed
• Thermal DWV ----------------------------------------------- Passed
• Humidity DWV ---------------------------------------------- Passed
```

### Page 17

```text
Tracking Code: 172626_Report_Rev_3 Part #: QSS-100- 01-L-D-A/QTS -100-01-L-D-A
Part description: QSS/QTS

                                                                                               Page 17 of 35
DATA  SUMMARIES
TEMPERATURE RISE (Current Carrying Capacity, CCC):
1)  High quality thermocouples whose temperature slopes track one another were used for temperature
monitoring.
2)  The thermocouples were placed at a location to sense the maximum temperature generated during testing.
3)  Temperature readings recorded are those for which three successive readings, 15 minutes apart, differ less
than 1° C (computer controlled data acquisition).
4)  Adjacent contacts were powered:
a.  Linear configuration with 2 adjacent signal conductors/contacts powered
172626
2(2X1) Signal Pins in Series
Part Numbers: QSS-100-01-L-D-A/QTS-100-01-L-D-A
4.2 4.2
3.4 3.4
2.6
2.1 2.1
2.2
1.8 1.3 1.3
1.0
0.0
1.0
2.0
3.0
4.0
5.0
15 25 35 45 55 65 75 85 95 105 115 125 135
Ambient Temperature (° C)
Maximum Current, Amps per Contact
Base Curve Derated 20 % Measured Current RT Peak Amp RT Derated Amp 85° C Peak Amp
85° C Derated Amp 95° C Peak Amp 95° C Derated Amp 115° C Peak Amp 115° C Derated Amp Limit
125° C
Limit
Room Temp= 19.6° C
Current Rating per Contact (30 Deg. Rise, 20% Derated)  = 1.8 Amps
```

### Page 18

```text
Tracking Code: 172626_Report_Rev_3 Part #: QSS-100- 01-L-D-A/QTS -100-01-L-D-A
Part description: QSS/QTS

                                                                                               Page 18 of 35

DATA  SUMMARIES Continued

b.  Linear configuration with 4 adjacent signal conductors/contacts powered
172626
4(2X2) Signal Pins in Series
Part Numbers: QSS-100-01-L-D-A/QTS-100-01-L-D-A
3.4 3.4
2.7 2.7
2.1
1.7 1.7
1.8
1.4 1.0 1.0
0.8
0.0
1.0
2.0
3.0
4.0
15 25 35 45 55 65 75 85 95 105 115 125 135
Ambient Temperature (° C)
Maximum Current, Amps per Contact
Base Curve Derated 20 % Measured Current RT Peak Amp RT Derated Amp 85° C Peak Amp
85° C Derated Amp 95° C Peak Amp 95° C Derated Amp 115° C Peak Amp 115° C Derated Amp Limit
125° C
Limit
Room Temp= 20.3° C
Current Rating per Contact (30 Deg. Rise, 20% Derated)  = 1.4 Amps
```

### Page 19

```text
Tracking Code: 172626_Report_Rev_3 Part #: QSS-100- 01-L-D-A/QTS -100-01-L-D-A
Part description: QSS/QTS

                                                                                               Page 19 of 35

DATA  SUMMARIES Continued

c.  Linear configuration with 6 adjacent signal conductors/contacts powered
172626
6(2X3) Signal Pins in Series
Part Numbers: QSS-100-01-L-D-A/QTS-100-01-L-D-A
2.7 2.7
2.2 2.2
1.7
1.3 1.3
1.4
1.2 0.8 0.8
0.7
0.0
0.5
1.0
1.5
2.0
2.5
3.0
3.5
15 25 35 45 55 65 75 85 95 105 115 125 135
Ambient Temperature (° C)
Maximum Current, Amps per Contact
Base Curve Derated 20 % Measured Current RT Peak Amp RT Derated Amp 85° C Peak Amp
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
```

### Page 24

```text
Tracking Code: 172626_Report_Rev_3 Part #: QSS-100- 01-L-D-A/QTS -100-01-L-D-A
Part description: QSS/QTS

                                                                                               Page 24 of 35

DATA  SUMMARIES Continued

h.  Linear configuration with 3 adjacent ground conductors/contacts powered
282355
3 (1X3) Ground Planes in Series
Part Numbers: QSS-100-01-L-D-A/QTS-100-01-L-D-A
51.5 51.5
41.2 41.2
31.5
25.2 25.2
27.1
21.7 15.0 15.0
12.0
0.0
10.0
20.0
30.0
40.0
50.0
60.0
70.0
20 40 60 80 100 120 140
Ambient Temperature (° C)
Maximum Current, Amps per Contact
Base Curve Derated 20 % Measured Current RT Peak Amp RT Derated Amp 85° C Peak Amp
85° C Derated Amp 95° C Peak Amp 95° C Derated Amp 115° C Peak Amp 115° C Derated Amp Limit
125° C
Limit
Room Temp= 22.5° C
Current Rating per Contact (30 Deg. Rise, 20% Derated)  = 21.7 Amps
```

### Page 25

```text
Tracking Code: 172626_Report_Rev_3 Part #: QSS-100- 01-L-D-A/QTS -100-01-L-D-A
Part description: QSS/QTS

                                                                                               Page 25 of 35

DATA  SUMMARIES Continued

i.  Linear configuration with all adjacent ground conductors/contacts powered
282355
4 (All Power) Ground Planes in Series
Part Numbers: QSS-100-01-L-D-A/QTS-100-01-L-D-A
49.8 49.8
39.9 39.9
30.8
24.6 24.6
26.5
21.2 14.9 14.9
11.9
0.0
10.0
20.0
30.0
40.0
50.0
60.0
20 40 60 80 100 120 140
Ambient Temperature (° C)
Maximum Current, Amps per Contact
Base Curve Derated 20 % Measured Current RT Peak Amp RT Derated Amp 85° C Peak Amp
85° C Derated Amp 95° C Peak Amp 95° C Derated Amp 115° C Peak Amp 115° C Derated Amp Limit
125° C
Limit
Room Temp= 23.1° C
Current Rating per Contact (30 Deg. Rise, 20% Derated)  = 21.2 Amps
```

### Page 26

```text
Tracking Code: 172626_Report_Rev_3 Part #: QSS-100- 01-L-D-A/QTS -100-01-L-D-A
Part description: QSS/QTS

                                                                                               Page 26 of 35

DATA  SUMMARIES Continued

MATING/UNMATING FORCE:
Mating/Unmating durability (QSS-100-01-L-D-A/QTS -100-01-L-D-A):
 Initial After 25 Cycles
 Mating  Unmating Mating  Unmating
 Newtons Force (Lbs) Newtons Force (Lbs) Newtons For ce (Lbs) Newtons Force (Lbs)
Minimum 52.44 11.79 32.51 7.31 56.93 12.80 36.52 8.21
Maximum 62.41 14.03 43.68 9.82 67.30 15.13 49.24 11.07
Average 57.36 12.90 39.35 8.85 60.98 13.71 43.38 9.75
St Dev 3.66 0.82 3.85 0.86 2.99 0.67 3.88 0.87
Count 8 8 8 8 8 8 8 8
 After 50 Cycles After 75 Cycles
 Mating  Unmating Mating  Unmating
 Newtons Force (Lbs) Newtons Force (Lbs) Newtons For ce (Lbs) Newtons Force (Lbs)
Minimum 59.65 13.41 40.61 9.13 62.14 13.97 44.84 10.08
Maximum 72.01 16.19 54.00 12.14 74.90 16.84 58.89 13.24
Average 63.33 14.24 45.76 10.29 66.24 14.89 49.13 11.05
St Dev 3.80 0.85 4.02 0.90 4.05 0.91 4.21 0.95
Count 8 8 8 8 8 8 8 8
 After 100 Cycles After Humidity
 Mating  Unmating Mating  Unmating
 Newtons Force (Lbs) Newtons Force (Lbs) Newtons Fo rce (Lbs) Newtons Force (Lbs)
Minimum 64.10 14.41 48.62 10.93 42.92 9.65 42.92 9.65
Maximum 78.95 17.75 61.87 13.91 59.43 13.36 52.00 11.69
Average 68.60 15.42 51.71 11.63 51.83 11.65 47.45 10.67
St Dev 4.87 1.09 4.34 0.97 5.52 1.24 3.12 0.70
Count 8 8 8 8 8 8 8 8
```

### Page 27

```text
Tracking Code: 172626_Report_Rev_3 Part #: QSS-100- 01-L-D-A/QTS -100-01-L-D-A
Part description: QSS/QTS

                                                                                               Page 27 of 35
DATA  SUMMARIES Continued

Mating/Unmating basic (QSS-075-01-L-D-A/QTS -075-01-L-D-A):
 Initial After 25 Cycles
 Mating  Unmating Mating  Unmating
 Newtons Force (Lbs) Newtons Force (Lbs) Newtons For ce (Lbs) Newtons Force (Lbs)
Minimum 39.85 8.96 32.43 7.29 45.90 10.32 38.52 8.66
Maximum 48.93 11.00 39.41 8.86 56.58 12.72 47.90 10.77
Average 44.51 10.01 35.80 8.05 50.50 11.35 41.88 9.42
St Dev 2.86 0.64 2.71 0.61 3.86 0.87 3.10 0.70
Count 8 8 8 8 8 8 8 8
 After 50 Cycles After 75 Cycles
 Mating  Unmating Mating  Unmating
 Newtons Force (Lbs) Newtons Force (Lbs) Newtons For ce (Lbs) Newtons Force (Lbs)
Minimum 49.68 11.17 40.83 9.18 49.51 11.13 40.52 9.11
Maximum 66.68 14.99 52.49 11.80 69.57 15.64 55.47 12.47
Average 55.24 12.42 46.25 10.40 57.89 13.01 49.03 11.02
St Dev 5.60 1.26 4.11 0.93 6.01 1.35 4.84 1.09
Count 8 8 8 8 8 8 8 8
 After 100 Cycles
 Mating  Unmating
 Newtons Force (Lbs) Newtons Force (Lbs)
Minimum 52.75 11.86 43.86 9.86
Maximum 72.77 16.36 57.65 12.96
Average 60.42 13.58 51.61 11.60
St Dev 6.17 1.39 4.09 0.92
Count 8 8 8 8
```

### Page 28

```text
Tracking Code: 172626_Report_Rev_3 Part #: QSS-100- 01-L-D-A/QTS -100-01-L-D-A
Part description: QSS/QTS

                                                                                               Page 28 of 35
DATA  SUMMARIES Continued

Mating/Unmating basic (QSS-050-01-L-D-A/QTS -050-01-L-D-A):
 Initial After 25 Cycles
 Mating  Unmating Mating  Unmating
 Newtons Force (Lbs) Newtons Force (Lbs) Newtons For ce (Lbs) Newtons Force (Lbs)
Minimum 24.46 5.50 15.92 3.58 28.29 6.36 19.66 4.42
Maximum 26.78 6.02 25.18 5.66 30.60 6.88 30.16 6.78
Average 25.69 5.78 21.47 4.83 29.73 6.68 25.74 5.79
St Dev 0.82 0.18 3.40 0.76 0.82 0.18 3.79 0.85
Count 8 8 8 8 8 8 8 8
 After 50 Cycles After 75 Cycles
 Mating  Unmating Mating  Unmating
 Newtons Force (Lbs) Newtons Force (Lbs) Newtons For ce (Lbs) Newtons Force (Lbs)
Minimum 30.20 6.79 21.93 4.93 31.31 7.04 22.95 5.16
Maximum 33.98 7.64 32.74 7.36 35.09 7.89 34.87 7.84
Average 32.13 7.22 28.16 6.33 33.82 7.60 29.79 6.70
St Dev 1.45 0.33 3.78 0.85 1.28 0.29 3.82 0.86
Count 8 8 8 8 8 8 8 8
 After 100 Cycles
 Mating  Unmating
 Newtons Force (Lbs) Newtons Force (Lbs)
Minimum 32.47 7.30 23.75 5.34
Maximum 36.47 8.20 35.50 7.98
Average 35.29 7.93 31.02 6.98
St Dev 1.41 0.32 3.77 0.85
Count 8 8 8 8
```

### Page 29

```text
Tracking Code: 172626_Report_Rev_3 Part #: QSS-100- 01-L-D-A/QTS -100-01-L-D-A
Part description: QSS/QTS

                                                                                               Page 29 of 35
DATA  SUMMARIES Continued

Mating/Unmating basic (QSS-025-01-L-D-A/QTS -025-01-L-D-A):
 Initial After 25 Cycles
 Mating  Unmating Mating  Unmating
 Newtons Force (Lbs) Newtons Force (Lbs) Newtons For ce (Lbs) Newtons Force (Lbs)
Minimum 12.90 2.90 13.79 3.10 15.43 3.47 14.37 3.23
Maximum 18.77 4.22 17.57 3.95 18.37 4.13 17.97 4.04
Average 16.07 3.61 16.15 3.63 16.86 3.79 16.48 3.71
St Dev 1.74 0.39 1.56 0.35 1.05 0.24 1.34 0.30
Count 8 8 8 8 8 8 8 8
 After 50 Cycles After 75 Cycles
 Mating  Unmating Mating  Unmating
 Newtons Force (Lbs) Newtons Force (Lbs) Newtons For ce (Lbs) Newtons Force (Lbs)
Minimum 16.06 3.61 15.75 3.54 16.15 3.63 16.46 3.70
Maximum 19.26 4.33 19.26 4.33 19.62 4.41 20.82 4.68
Average 17.85 4.01 17.30 3.89 18.34 4.12 18.15 4.08
St Dev 1.07 0.24 1.28 0.29 1.32 0.30 1.43 0.32
Count 8 8 8 8 8 8 8 8
 After 100 Cycles
 Mating  Unmating
 Newtons Force (Lbs) Newtons Force (Lbs)
Minimum 16.99 3.82 16.55 3.72
Maximum 20.28 4.56 21.80 4.90
Average 19.00 4.27 18.76 4.22
St Dev 1.25 0.28 1.72 0.39
Count 8 8 8 8
```

### Page 30

```text
Tracking Code: 172626_Report_Rev_3 Part #: QSS-100- 01-L-D-A/QTS -100-01-L-D-A
Part description: QSS/QTS

                                                                                               Page 30 of 35
DATA  SUMMARIES Continued
Mating/Unmating Data for 25, 50, 75and 100 Position QSS-QTS
0.00
2.00
4.00
6.00
8.00
10.00
12.00
14.00
16.00
18.00
25 Pos. 50 Pos. 75 Pos. 100 Pos.
Number of Terminals per Row
Force (lbs)
Mating (Initial) Unmating (Initial) Mating (100 Cycles) Unmating (100 Cycles)
```

### Page 31

```text
Tracking Code: 172626_Report_Rev_3 Part #: QSS-100- 01-L-D-A/QTS -100-01-L-D-A
Part description: QSS/QTS

                                                                                               Page 31 of 35
DATA  SUMMARIES Continued

INSULATION RESISTANCE (IR):
 Pin to Pin
 Mated Unmated Unmated
Minimum QSS/QTS QSS QTS
Initial 10000 10000 10000
Thermal 10000 10000 10000
Humidity 10000 10000 10000

 Pin to Ground
 Mated Unmated Unmated
Minimum QSS/QTS QSS QTS
Initial 10000 10000 10000
Thermal 10000 10000 10000
Humidity 10000 10000 10000

 Row to Row
 Mated Unmated Unmated
Minimum QSS/QTS QSS QTS
Initial 10000 10000 10000
Thermal 10000 10000 10000
Humidity 10000 10000 10000
```

### Page 32

```text
Tracking Code: 172626_Report_Rev_3 Part #: QSS-100- 01-L-D-A/QTS -100-01-L-D-A
Part description: QSS/QTS

                                                                                               Page 32 of 35
DATA  SUMMARIES Continued

DIELECTRIC WITHSTANDING VOLTAGE (DWV):

Voltage Rating Summary
Minimum QSS/QTS
Break Down Voltage 1000
Test Voltage 750
Working Voltage 250

Pin to Pin
Initial Test Voltage Passed
After Thermal Test Voltage Passed
After Humidity Test Voltage Passed

Row to Row
Initial Test Voltage Passed
After Thermal Test Voltage Passed
After Humidity Test Voltage Passed

Pin to Ground
Initial Test Voltage Passed
After Thermal Test Voltage Passed
After Humidity Test Voltage Passed
```

### Page 33

```text
Tracking Code: 172626_Report_Rev_3 Part #: QSS-100- 01-L-D-A/QTS -100-01-L-D-A
Part description: QSS/QTS

                                                                                               Page 33 of 35
DATA  SUMMARIES Continued
LLCR Durabiltiy:
1)  A total of 192 points were measured.
2)  EIA-364-23, Low Level Contact Resistance  Test Procedure for Electrical Connectors and Sockets.
3)  A computer program, LLCR 221.exe , ensures repeatability for data acquisition.
4)  The following guidelines are used to categorize the changes in LLCR as a result from stressing.
a.  <= +5.0 mOhms: ----------------------------- Stable
b.  +5.1 to +10.0 mOhms: ---------------------- Minor
c.  +10.1 to +15.0 mOhms: -------------------- Acceptable
d.  +15.1 to +50.0 mOhms: -------------------- Marginal
e.  +50.1 to +2000 mOhms -------------------- Unstable
f.  >+2000 mOhms: ----------------------------- Open Failure

 LLCR Measurement Summaries by Pin Type
Date 2/20/2012 2/22/2012 2/27/2012 3/9/2012
Room Temp (Deg C) 20 21 20 21
Rel Humidity (%) 45 53 54 54
Technician Peter  Chen  Peter  Chen  Peter  Chen
Peter
Chen
mOhm values Actual Delta Delta Delta
  Initial 100 Cycles Therm Shck Humidity
 Pin Type 1: Signal
Average 24.27 2.01 2.22 2.22
St. Dev. 1.99 1.57 1.80 1.78
Min 21.05 0.01 0.03 0.02
Max 29.73 6.71 7.12 7.27
Summary Count 176 176 176 176
Total Count 176 176 176 176
 Pin Type 2: Ground
Average 2.50 0.29 0.27 0.30
St. Dev. 0.20 0.14 0.10 0.13
Min 2.23 0.01 0.01 0.01
Max 3.05 0.50 0.34 0.49
Summary Count 16 16 16 16
Total Count 16 16 16 16

LLCR Delta Count by Category
  Stable  Minor Acceptable  Marginal Unstable Open
mOhms  <=5
>5 &
<=10 >10 & <=15 >15 & <=50  >50 & <=1000 >1000
100 Cycles  185  7 0 0 0 0
Therm Shck  172  20  0 0 0 0
Humidity  176  16  0 0 0 0
```

### Page 34

```text
Tracking Code: 172626_Report_Rev_3 Part #: QSS-100- 01-L-D-A/QTS -100-01-L-D-A
Part description: QSS/QTS

                                                                                               Page 34 of 35
EQUIPMENT AND CALIBRATION SCHEDULES

Equipment #: HZ-MO-05
Description:  Digital Multimeter
Manufacturer:   Keithley
Model:   3706
Serial #:   1285188
Accuracy:   Last Cal: 2012/8/18, Next Cal: 2013/8/18

Equipment #: HZ-TCT-01
Description:  Normal force analyzer
Manufacturer:   Mecmesin Multitester
Model:   Mecmesin Multitester 2.5-i
Serial #:   08-1049-04
Accuracy:  Last Cal: 2012/4/28, Next Cal: 2013/4/27

Equipment #: HZ-THC-01
Description:  Humidity transmitter
Manufacturer:   Thermtron
Model:   HMM30C
Serial #:   D0240037
Accuracy:  Last Cal: 2013/3/3, Next Cal: 2014/3/2

Equipment #: HZ-HPM-01
Description:  IR/DWV Tester
Manufacturer:   AN9636H
Model:   AN9636H
Serial #:   089601091
Accuracy:  Last Cal: 2012/7/6, Next Cal: 2013/7/5

Equipment #: HZ-MO-01
Description:  Micro-ohmmeter
Manufacturer:   Keithley
Model:   2700
Serial #:   1199807
Accuracy:  Last Cal: 2012/4/28, Next Cal: 2013/4/27

Equipment #: HZ-PS-01
Description:  Power Supply
Manufacturer:   Agilent
Model:   6031A
Serial #:   MY41000982
Accuracy:  Last Cal: 2012/4/28, Next Cal: 2013/4/27
```

### Page 35

```text
Tracking Code: 172626_Report_Rev_3 Part #: QSS-100- 01-L-D-A/QTS -100-01-L-D-A
Part description: QSS/QTS

                                                                                               Page 35 of 35
EQUIPMENT AND CALIBRATION SCHEDULES
Equipment #: HZ-TSC-01
Description:  Thermal Shock transmitter
Manufacturer:   CSZ
Model:   10-VT14994
Serial #:   VTS-3-6-6-SC/AC
Accuracy:  Last Cal: 2012/11/1, Next Cal: 2013/11/1
```
