thepinkmile/Enigma-NG/.copilot/checkpoints/044-electronics-agent-tested-review-cycle-defined.md

# Checkpoint 044 — Electronics agent tested successfully, review cycle process formalized
## Date
2026-04-15
## Session
<sanitized-session-id>
## Overview
This checkpoint captures the successful direct invocation of the new **Electronics review engineer** 
custom agent and the formalization of the review cycle process in plan.md. The agent was tested on 
the Settings Board design files and performed exactly as intended: hardware-focused, 
manufacturing-aware, and free of software/style drift.
## Work Done
### Electronics review engineer agent — direct invocation test ✅
- **Agent type**: Electronics review engineer (custom agent from `.github/agents/electronics-review-engineer.agent.md`)
- **Test scope**: Settings Board Design_Spec.md and Board_Layout.md
- **Result**: Agent completed successfully with detailed technical findings
- **Finding categories**:
  - 3 CRITICAL issues (I²C pin ambiguity, base resistor naming, missing datasheets)
  - 6 SIGNIFICANT issues (PNP drive calc, R_LED_ANODE TBD, switch MPN TBD, etc.)
  - 2 CLARITY issues (base resistor package size, decoupling cap nomenclature)
- **Behavior**: Exactly as designed — focused on sourcing feasibility, electrical topology, BOM 
  accuracy, and manufacturing realism. No software/style drift detected.
- **Conclusion**: Agent is production-ready for review cycles
### Review cycle process formalized in plan.md
Updated `.copilot/plan.md` with new comprehensive "Review Cycle Process" section:
- Defines tools: markdownlint + Electronics review engineer agent
- States 2 consecutive clean passes rule explicitly
- Clarifies that **material technical issues count as findings** (all CRITICAL, SIGNIFICANT, 
  CLARITY issues require investigation/resolution)
- Documents that **fixes trigger new review** with clean-pass counter reset to 0
- Provides agent invocation guidance and review scope definition
- Includes visual workflow diagram showing review cycle logic
### Session state synced
All changes written to repository `.copilot/` folder for persistence across sessions.
## Commits
None. `.copilot/` remains local-only session state and is intentionally uncommitted.
## Key Technical Notes
### Electronics agent findings (Settings Board review)
The agent identified legitimate issues that align with the components-todo.md work:
- Switch MPN still TBD (Marquardt 1800 series — variant must be locked)
- R_LED_ANODE value TBD (blocked on switch LED specs)
- JST J_I2C JLCPCB PN unconfirmed (C131342 is 3-pin, need 4-pin)
- Missing datasheets: MCP23017, MMBT3906, switches, connectors
- Base resistor nomenclature mismatch (R_BASE1–4 vs R_BASE1_G/R/2_G/R)
- I²C pin assignment ambiguity in mapping table (GPB[7] on two different ICs)

All findings are **sourcing/documentation completeness** issues, not fundamental design flaws. 
Design topology confirmed sound.
### Review cycle process now canonical
The new Review Cycle Process section in plan.md is now the authoritative definition. Key points:
- Material technical issues from electronics agent **always** count as findings
- Clean = both lint AND electronics review return no issues
- Fixes reset counter; 2 consecutive clean runs required
- Agent focus: component specs, electrical topology, BOM accuracy, datasheets, sourcing/manufacturing
## Next Steps
1. **Components-todo.md verification** — work through the 30-row re-verification table
   - Rows 1–5: High-priority TBD parts (switches, connectors, R_LED_ANODE)
   - Rows 6–30: Candidate MPN verification (datasheets, sourcing, specifications)
2. **Address Settings Board findings** — after component verification, apply fixes and re-run 
   review cycle (expect 1–2 rounds to achieve 2 clean passes)
3. **KiCad schematic phase** — when all TBD parts are locked
## Files Updated
- `.copilot/plan.md` — added comprehensive Review Cycle Process section
- `.copilot/checkpoints/044-electronics-agent-tested-review-cycle-defined.md` — this checkpoint
- `.copilot/checkpoints/index.md` — updated with this checkpoint entry
