thepinkmile/Enigma-NG/.copilot/checkpoints/001-r26-fixes-dec-020-rib-bond-2-3.md

2×3 change agent running. Now writing the session summary.

---

<overview>
This session continues the Enigma-NG electronics design documentation review cycle. The primary goals are: (1) close the ongoing multi-round content review cycle by achieving two consecutive clean passes, (2) resolve open design question QUE-001 (supercap rib clearway ENIG bonding), and (3) apply the user's decision to expand the supercapacitor bank from 2×2 to 2×3 layout. The approach is to use background review agents for deep-dive passes, filter false positives carefully, and apply fixes via background fix agents — committing only verified, genuine changes.
</overview>

<history>
1. **Session start — alignment with previous state**
   - Read previous session plan (aaf32e5c) and checkpoint 011
   - Previous session ran R15–R25; R23 was first clean pass but R24 (3 findings) and R25 (6 findings) reset the counter
   - Need two consecutive clean passes (R26 + R27) to close the review cycle
   - Set up plan.md and SQL todos for this session; marked `review-cycle-close` in_progress
2. **R26 deep-dive review launched** (background agent)
   - Covered all 25 design documents against stale values list and cross-document consistency rules
   - While R26 ran, user initiated discussion on QUE-001 (supercap rib clearway ENIG bonding)
3. **QUE-001 / DEC-020 discussion**
   - Reviewed Design_Log QUE-001 and DEC-020 placeholder; checked Cert_Evidence §2.2 (single-point GND_CHASSIS rule)
   - Confirmed rib bonding does NOT violate single-point rule (enclosure↔GND_CHASSIS bonds, not signal GND crossings)
   - User confirmed: YES to ENIG strips; YES to Kapton tape (min 2-mil/50µm polyimide); YES to conductive elastomer gasket; Faraday cage intent noted
   - Gasket: specify type/properties only, defer part selection to mechanical design phase
   - Other boards deferred — Controller uses 3D-printed prototype chassis; Stator/Encoder/Rotor mechanical docs not yet written
4. **R26 results received — 20 claimed findings, 14 were FALSE POSITIVES**
   - Findings 1–14: Agent tried to revert TPS259804ONRGER → TPS259807ONRGER
   - **Critical:** TPS259807ONRGER is on the stale values list; TPS259804ONRGER is the current correct eFuse (silicon-fixed 16.9V OVLO). These were correctly discarded.
   - Genuine findings: #15–20 (6 findings)
5. **R26 fixes + DEC-020 applied** (commit `ab7452f`)
   - Fix 15: CTL Design_Spec §9.2 L6 label corrected
   - Fix 16: CTL Board_Layout §9 stackup summary L6 label corrected
   - Fix 17: CTL Board_Layout trace table GND row note L1→L6 for JTAG CI reference
   - Fix 18: Design_Log INC-22 TPD4E05U06DQAR→DRYR
   - Fix 19+20: PM Design_Spec D3/D4/D5 DBVR/DQAR→DRYR (U-DFN-10 correct suffix)
   - DEC-020 fully written in Design_Log; QUE-001 closed; PM Design_Spec §4 and PM Board_Layout updated with Kapton/gasket/ENIG/Faraday cage specs
6. **Supercap count discrepancy found**
   - User believed layout was 2×3; docs showed 2×2 everywhere (consistent but wrong per user's intent)
   - Calculated: 2S3P (6 cells) → 33F at 5.4V, ≥21.8s hold-up @ 5W (vs current ≥14.5s)
   - Block footprint: 28×42mm; shadow keepout 32×46mm; 2 rib clearways per row
   - LTC3350 supports 2S3P; voltage unchanged; board space not a constraint
   - User confirmed: change to 2×3 2S3P across all docs
7. **2×3 change agent launched** (background, currently running)
   - Will update 7 files; create DEC-021; commit as single clean commit
</history>

<work_done>
Files modified this session:

- `design/Electronics/Controller/Design_Spec.md` — L6 label fix (§9.2)
- `design/Electronics/Controller/Board_Layout.md` — L6 label fix (§9 stackup), GND trace table note L1→L6
- `design/Design_Log.md` — INC-22 suffix fix; QUE-001 closed; DEC-020 fully written; DEC-021 pending (in-flight agent)
- `design/Electronics/Power_Module/Design_Spec.md` — D3/D4/D5 TPD4E05U06 suffix fix; DEC-020 Kapton/ENIG/gasket bullet; 2×3 change pending
- `design/Electronics/Power_Module/Board_Layout.md` — DEC-020 rib clearway bond zone note; 2×3 change pending
- `design/Electronics/Consolidated_BOM.md` — 2×3 change pending
- `design/Standards/Certification_Evidence.md` — 2×3 change pending
- `design/Guides/User_Manual.md` — 2×3 change pending
- `design/Software/Linux_OS/Power_Management.md` — 2×3 change pending

Commits this session:
- `ab7452f` — R26 fixes (6 findings) + DEC-020 decision
- DEC-021 / 2×3 supercap change — **in-flight** (background agent `supercap-2x3-change`)

Tasks:
- [x] R26 review run and filtered
- [x] R26 genuine fixes applied
- [x] DEC-020 written (QUE-001 closed)
- [ ] 2×3 supercap change across 7 files (in-flight)
- [ ] R27 review (must be clean for cycle to close)
- [ ] Encoder detailed design review cycle
- [ ] Rotor detailed design review
- [ ] KiCad setup docs
</work_done>

<technical_details>
**eFuse — CRITICAL: TPS259804ONRGER is correct, TPS259807ONRGER is STALE**
- TPS259804ONRGER: silicon-fixed 16.9V OVLO, VQFN-24 — this is correct and must not be changed
- TPS259807ONRGER: listed on stale values list (must never reappear) — R26 agent incorrectly tried to reinstate it; all 14 such findings were false positives
- R3 = R_ILIM = 210Ω ERA-3ARB2100V (correct); R1/R2 = OVLO divider

**TPD4E05U06 package suffix — DRYR is correct for U-DFN-10**
- DRYR = U-DFN-10 (10-pin, correct for 4-channel ESD array)
- DBVR = SOT-23-5 (5-pin, wrong package for D3/D4/D5)
- DQAR = also incorrect; was introduced during a previous partial fix
- JLCPCB C123462 applies to DRYR

**Review cycle lint method: ide-get_diagnostics ONLY**
- Node.js is NOT on system PATH — npx/markdownlint CLI will fail
- ide-get_diagnostics returning [] = lint clean
- Two consecutive clean passes required (content + lint) to close a design phase

**Review agent false positive pattern**
- The eFuse cluster (TPS259804→TPS259807) is the main false positive pattern
- Agents without stale values context will try to reintroduce stale values
- Always cross-reference stale values master list before applying any eFuse-related findings

**GND_CHASSIS single-point rule (Cert_Evidence §2.2)**
- Single point = signal GND connects to GND_CHASSIS at exactly one point
- Rib ENIG bonds are enclosure↔GND_CHASSIS (both chassis domain) — do NOT violate the rule
- Mounting screws also do this; rib bonds are additive HF bonding, same principle

**Supercap 2×3 2S3P change**
- 6 × Tecate TPLH-2R7/22WR12X31 (22F/2.7V each)
- Effective: 33F at 5.4V (2 in series × 3 in parallel)
- Hold-up: ≥21.8s @ 5W (up from ≥14.5s)
- Block: 28×42mm; shadow keepout: 32×46mm
- 2 rib clearways per row (3 columns → 2 gaps between them)
- LTC3350 supports this natively; no topology change
- Charge time: ~3 min from depleted

**CTL Board_Layout layer assignment**
- L6 = JTAG/Data Plate (Signal/Copper Pour) — correct label
- JTAG CI traces on L6 over L5 GND plane (50Ω, 0.127mm/5mil)
- L2 GND plane is for L1 signals; L5 GND plane is for L6 signals

**Supercap mounting orientation**
- Vertical (upright) is implied but NOT yet explicitly documented
- Retention/clamp for vibration resistance not yet specified
- Should be addressed as part of DEC-020 or a new decision when mechanical design is finalised

**DEC-020 rib clearway specs**
- ENIG strip: min 1.0mm wide × full rib depth, L1, GND_CHASSIS net
- Kapton tape: min 2-mil (50µm) polyimide, wrapped around supercap bodies
- Conductive gasket: ≤2mm wide, self-adhesive elastomer/foam, part TBD at mechanical design phase
- Other boards deferred (Controller = 3D-printed prototype; Stator/Encoder/Rotor undocumented)
</technical_details>

<important_files>
- `design/Design_Log.md`
  - Master log of all decisions (DEC-xxx), incidents (INC-xxx), and questions (QUE-xxx)
  - Modified: INC-22 suffix fix; QUE-001 closed; DEC-020 written; DEC-021 will be added by in-flight agent
  - Key sections: DEC-020 (~line 690), QUE-001 (~line 828), INC-22 (~line 963)
- `design/Electronics/Power_Module/Design_Spec.md`
  - Core PM spec; most supercap, eFuse, and layout details live here
  - Modified: D3/D4/D5 TPD4E05U06 suffix; DEC-020 Kapton/ENIG bullet in §4; 2×3 change in-flight
  - Key: DR-PM-07 (supercap spec), §4 (supercap block), BOM (C_SC1–x rows, D3/D4/D5 rows)
- `design/Electronics/Power_Module/Board_Layout.md`
  - PM PCB layout description and ASCII diagrams
  - Modified: DEC-020 rib clearway zone note; 2×3 ASCII diagram update in-flight
- `design/Electronics/Consolidated_BOM.md`
  - System-wide parts list; supercap count update in-flight
- `design/Standards/Certification_Evidence.md`
  - EMC/safety rationale; §2.2 single-point GND_CHASSIS rule; supercap hold-up specs in-flight
- `design/Electronics/Controller/Design_Spec.md`
  - Modified: L6 label fix in §9.2 (this session)
- `design/Electronics/Controller/Board_Layout.md`
  - Modified: L6 label fix in stackup summary; GND trace table note corrected (this session)
- `%USERPROFILE%\.copilot\session-state\<session-id>\plan.md`
  - Current session plan with todos and technical notes
</important_files>

<next_steps>
**Immediate (in-flight):**
- Agent `supercap-2x3-change` running — will update 7 files and commit DEC-021
- Read results when complete, verify commit

**After 2×3 agent completes:**
1. **Launch R27** — deep-dive review across all docs. Must be clean. If clean → review cycle closes (R26 was clean [6 fixes applied], R27 must also be clean). Note: R26 had 6 genuine findings so technically R27 is the first pass since last fix commit — need R27 clean + R28 clean for two consecutive.
   - Actually re-check: the two-consecutive rule requires two rounds with ZERO findings. R26 had findings (fixed in ab7452f). So R27 is the next round — needs to be clean, then R28 clean.
2. **After review cycle closes:** Begin Encoder detailed design review cycle (OBS-001 to OBS-018 already applied; run review agent until 2 clean passes)
3. **After Encoder closes:** Rotor detailed design
4. **KiCad setup docs** — lowest priority, no details defined yet

**Open design questions to address eventually:**
- Supercap mounting orientation (vertical implied but not documented; retention clip for vibration)
- Controller Board rib clearway (needs metal chassis to be finalised first)
- OWI-001: Test coupons per board
- OWI-002: PAS definitions per board
- OWI-003: VHDL pseudo-code for CPLDs
- OWI-018: ENIG rib clearway bonding pad (now DEC-020, closed for PM; other boards deferred)
- SW1 vintage switch selection (open item in PM Design_Spec)
- ERA-3ARB2672V/ERA-3ARB1002V MOQ issue for R14/R15 LTC3350 BACKUP divider
</next_steps>
