thepinkmile/Enigma-NG/.copilot/checkpoints/003-r28-r32-fixes-session-state-in.md

<overview>
This session continued the Enigma-NG electronics design documentation review cycle with three parallel goals: (1) close the ongoing multi-round content review cycle by achieving two consecutive clean passes, (2) establish a canonical `.copilot/` folder in the repo root for persistent session state, and (3) complete the Encoder detailed design by applying architecture clarifications and running review cycles until clean. The approach used background review agents (R28–R32) with careful false-positive filtering, direct surgical fixes for small changes, and background fix agents for larger batches.
</overview>

<history>
1. **Session resumed** — user approved the plan to fix R27 findings and run R28+R29 clean passes.
   - R27 fix agent (`r27-fixes`) launched: 16 findings (DEC renumber cascade + TPD4E05U06 DBVR/DQNR→DRYR). Committed `2ffb8f1`.
   - `encoder-stator-fix` agent completed: §1/§3/§4/§9 + BOM rewrites for Encoder, J4/J5/J6 plugboard context for Stator. Committed `b1487ec`.
2. **User requested canonical `.copilot/` session state in repo root** — so session state persists across sessions without UUID path issues.
   - Created repo-local `.copilot\` with `README.md`, `plan.md`, `checkpoints/index.md`, and both checkpoint files copied from the user-profile session folder.
   - Added `.copilot/` to `.gitignore`. Committed `b35b43d`.
   - Stored memory: canonical session state lives at `.copilot/` in repo root; instruct with "Please read `.copilot/plan.md` and all files in `.copilot/checkpoints/` to align yourself..."
3. **User went to bed; requested fully autonomous continuation.**
4. **R28 launched and completed** — 10 genuine findings:
   - Consolidated_BOM §4a: jack Sleeve→GND (wrong), BT65–128 described as INT detect, BT129–256 rows still present, notes still described 4-row architecture
   - Consolidated_BOM usage summary: ENC cap count 144→80, pull-up count 132→68, blade terminal count 256→128
   - Power_Management.md: CSS2H total build qty 2→3
   - Cert_Evidence §4.4: TPD2E2U06 package SON-6→SOT-553 (DRL)
   - Fixed by `r28-fixes` agent. Committed.
5. **R29 launched and completed** — 10 claimed findings, 8 were FALSE POSITIVES:
   - Findings 2–10: Agent claimed R_ILIM should be ERA-3ARB2100V (0.1% thin-film). Verified against actual docs — ERJ-3EKF2100V (1% thick-film) is confirmed correct per closed OA-01 in Cert_Evidence §8. FALSE POSITIVES discarded.
   - 2 genuine findings: Design_Log DEC-016 table `DEC-023`→`DEC-024`; Consolidated_BOM §4a `Keystone 1285`→`1285-ST` with corrected P/Ns (534-1285-ST, 36-1285-ST-ND, C5370868).
   - Applied directly. Committed `6107d50`.
6. **R30 launched and completed** — 2 genuine findings:
   - Stator Design_Spec BOM R1: CSS2H ordinal "second and third" → "first and second" (PM R12=1st, PM R23=2nd, Stator R1=3rd)
   - User_Manual §2: ML2032 listed as interchangeable RTC battery with CR2032 — safety error; ML2032 requires D1 removal. Removed ML2032 reference.
   - Applied directly. Committed `62ce9fa`.
7. **R31 launched and completed** — 4 genuine findings:
   - User_Manual §3.1 Battery row: 11–16.8V → 11–16.4V (prohibited 4.2V/cell)
   - Cert_Evidence §3.1 code block: Battery 11–16.8V → 11–16.4V
   - Controller Design_Spec §2 + §7: `(DEC-024 candidate)` × 2 → `(DEC-TBD — new decision required)`
   - Encoder Design_Spec §8: removed stale ESD bullet (TPD4E001 not in BOM; Micro-Fit doesn't exist on Encoder)
   - Applied directly. Committed `7d885db`.
8. **R32 launched and completed** — 5 genuine findings:
   - PM Design_Spec §3.2: Battery (11–16.8V) → (11–16.4V)
   - PM Design_Spec §1 rib clearway: strip width 1.0mm → 1.5mm (DEC-020 specifies 1.5mm)
   - User_Manual §3.1: OVLO threshold `above 17V` → `above 16.9V`
   - User_Manual §3.5: eFuse window `11–17V` → `11–16.9V`
   - Power_Management.md shutdown timing: `~50ms` → `≤510ms` (POLL_HZ=2 = 500ms period)
   - Applied directly. Committed `2b9a33a`. **R32 had findings — clean counter resets.**
9. **R33 not yet launched** — need two consecutive clean passes; R32 had 5 findings so must continue.
</history>

<work_done>
Files modified this session:

- `design/Design_Log.md` — DEC-016 table: `DEC-023`→`DEC-024`
- `design/Electronics/Consolidated_BOM.md` — §4a jack table fixed (Sleeve→BT65–128, Switch N/C, removed BT129–256, fixed notes); usage summary ENC counts updated (cap 144→80, pull-up 132→68, blade 256→128); Keystone 1285→1285-ST with correct P/Ns throughout
- `design/Electronics/Power_Module/Design_Spec.md` — rib clearway strip width 1.0mm→1.5mm; battery max 16.8V→16.4V in startup sequence
- `design/Electronics/Controller/Design_Spec.md` — `(DEC-024 candidate)` → `(DEC-TBD)` ×2
- `design/Electronics/Encoder/Design_Spec.md` — removed stale ESD bullet (TPD4E001/Micro-Fit)
- `design/Electronics/Stator/Design_Spec.md` — CSS2H ordinal "second and third" → "first and second"
- `design/Guides/User_Manual.md` — ML2032 removed as RTC battery option; battery max 16.8V→16.4V; OVLO threshold 17V→16.9V ×2
- `design/Software/Linux_OS/Power_Management.md` — CSS2H total 2→3; shutdown daemon latency ~50ms→≤510ms
- `design/Standards/Certification_Evidence.md` — TPD2E2U06 package SON-6→SOT-553; battery 16.8V→16.4V in §3.1 code block
- `.gitignore` — added `.copilot/` entry
- `.copilot/README.md` — created (session state instructions)
- `.copilot/plan.md` — created (canonical session plan)
- `.copilot/checkpoints/index.md` — created
- `.copilot/checkpoints/001-r26-fixes-dec-020-rib-bond-2-3.md` — copied from user-profile session folder
- `.copilot/checkpoints/002-r27-fixes-encoder-architecture.md` — copied from user-profile session folder

Commits this session:
- `2ffb8f1` — R27 fixes: DEC renumber cascade (16 cross-refs) + TPD4E05U06 suffix
- `b1487ec` — Encoder/Stator architecture rewrites (two-half, plugboard context)
- `b35b43d` — .gitignore: add .copilot/
- R28 fix commit — 10 findings (BOM counts, jack table, CSS2H qty, TPD2E2U06 package)
- `6107d50` — R29 fixes: DEC-016 cross-ref, Keystone 1285-ST
- `62ce9fa` — R30 fixes: CSS2H ordinal, ML2032 removed
- `7d885db` — R31 fixes: battery voltage, DEC-024 candidate, stale ESD
- `2b9a33a` — R32 fixes: OVLO refs, rib width, shutdown poll latency

Tasks:
- [x] R27 fixes committed
- [x] encoder-stator-fix committed
- [x] `.copilot/` folder created and populated
- [x] R28 run and fixed
- [x] R29 run and fixed (8 false positives filtered)
- [x] R30 run and fixed
- [x] R31 run and fixed
- [x] R32 run and fixed
- [ ] R33 — first clean pass attempt (not yet launched)
- [ ] R34 — second consecutive clean pass
- [ ] Encoder marked complete in Design_Log
- [ ] Checkpoint `003-encoder-complete.md` saved to `.copilot/checkpoints/`
- [ ] `.copilot/plan.md` updated with Rotor as next phase
</work_done>

<technical_details>
**eFuse — TPS259804ONRGER IS CORRECT. NEVER flag it.**
- Silicon-fixed 16.9V OVLO; no external OVLO resistor
- R3 = R_ILIM = 210Ω ERJ-3EKF2100V (1% thick-film) — Mouser 667-ERJ-3EKF2100V, DigiKey P210HCT-ND, JLCPCB C403064
- Battery max voltage: 4.1V/cell = 16.4V (4.2V/cell = 16.8V is PROHIBITED — too close to 16.9V OVLO)
- OVLO threshold to cite in user-facing docs: 16.9V (not "17V")

**R_ILIM false positive pattern (CRITICAL)**
- Review agents repeatedly suggest ERA-3ARB2100V (0.1% thin-film) as "correct" for R_ILIM
- This is WRONG — ERJ-3EKF2100V (1% thick-film) is correct, confirmed by closed OA-01 in Cert_Evidence §8
- Always discard any finding suggesting ERA-3ARB2100V or 0.1% thin-film for R_ILIM
- Add explicit "ERJ-3EKF2100V IS CORRECT, do not suggest ERA" instruction to every review prompt

**DEC numbering (current)**
- DEC-020 = PM rib clearway (Kapton/ENIG/gasket)
- DEC-021 = Supercapacitor bank upgrade (2S3P)
- DEC-022 = JDB Crystal Clock
- DEC-023 = JDB GND_CHASSIS
- DEC-024 = JDB JTAG buffer/master

**Supercap 2S3P (final)**
- 6× Tecate TPLH-2R7/22WR12X31; 33F/5.4V; 30×45mm block; 34×49mm shadow; 3.0mm gap; ≥21.7s @ 5W

**Encoder two-half architecture (correct)**
- Decode Half (U1/CPLD A): ENC_IN[0:5] → 64 lines → BT1–64
- Encode Half (U2/CPLD B): BT65–128 → 64 lines → ENC_OUT[0:5]
- J2 is the ONLY inter-half connection (power + both 6-bit buses + JTAG)
- JTAG chain: J2 TDI → U1 → R7(33Ω) → U2 → R8(75Ω) → J2 TDO
- Pull-ups R9–R72 (64×, Encode Half only); RC caps C22–C85 (64×, Encode Half only)
- Keystone 1285-ST: Mouser 534-1285-ST, DigiKey 36-1285-ST-ND, JLCPCB C5370868
- Jack: Tip+Switch → BT1–64; Sleeve → BT65–128; crossover cable = reciprocal substitution; max 32 cables
- BT129–256 DO NOT EXIST; no TPD4E001; no Micro-Fit connector on Encoder

**Stator plugboard routing**
- J4=HID, J5=Plugboard Pass A, J6=Plugboard Pass B (configurable via CPLD)
- FR-STA-05 expanded; plugboard routing section added

**CSS2H-2512R-R010ELF instances**
- PM R12 = 1st (LTC3350 RSENSE)
- PM R23 = 2nd (INA219 U12 at 0x40)
- Stator R1 = 3rd (INA219 U2 at 0x45)
- Total build qty = 3

**DEC-020 rib clearway (correct values)**
- ENIG strip: min 1.5mm wide (NOT 1.0mm) × full rib depth, L1, GND_CHASSIS net
- Kapton tape: min 2-mil (50µm) polyimide
- Conductive gasket: ≤3mm wide

**Shutdown timing**
- POLL_HZ = 2 (500ms period); daemon latency after BACKUP asserts = ≤510ms worst-case (NOT ~50ms)

**RTC battery**
- CR2032 only. ML2032 requires D1 removal — NOT a direct substitute.

**3V3_ENIG tap decoupling on Controller**
- Annotated `(DEC-TBD — new decision required)` — was incorrectly `(DEC-024 candidate)`

**Canonical session state**
- Lives at repo-local `.copilot\`
- Resume phrase: "Please read `.copilot/plan.md` and all files in `.copilot/checkpoints/` to align yourself with the current project state, then continue from where we left off."

**Review cycle lint method**
- `ide-get_diagnostics` ONLY — Node.js not on PATH, npx/markdownlint CLI fails
- `[]` return = lint clean
- Two consecutive clean passes required to close design phase

**False positive patterns to always filter**
- TPS259804ONRGER → never flag (correct eFuse)
- ERJ-3EKF2100V / 1% thick-film for R_ILIM → never flag (correct)
- ERA-3ARB2100V / 0.1% thin-film for R_ILIM → always discard
</technical_details>

<important_files>
- `design/Design_Log.md`
  - Master log of DEC/INC/QUE entries; cross-reference source of truth
  - DEC-016 table footnote updated: DEC-023→DEC-024
- `design/Electronics/Consolidated_BOM.md`
  - System-wide BOM and component usage summary
  - §4a Encoder jack/terminal table fully corrected; Keystone 1285→1285-ST throughout; usage summary ENC counts updated
- `design/Electronics/Power_Module/Design_Spec.md`
  - Core PM spec; supercap, eFuse, DEC-020 details
  - Rib clearway width 1.0mm→1.5mm; battery voltage 16.8V→16.4V in startup sequence
- `design/Electronics/Encoder/Design_Spec.md`
  - Fully rewritten this session (two-half architecture, §1/§3/§4/§9, BOM)
  - Stale ESD bullet removed in §8
- `design/Electronics/Stator/Design_Spec.md`
  - FR-STA-05 expanded; J4/J5/J6 plugboard routing section added; CSS2H ordinal fixed
- `design/Electronics/Controller/Design_Spec.md`
  - `(DEC-024 candidate)` → `(DEC-TBD)` ×2 in §2 and §7
- `design/Guides/User_Manual.md`
  - ML2032 removed; battery 16.8V→16.4V; OVLO threshold 17V→16.9V ×2
- `design/Software/Linux_OS/Power_Management.md`
  - CSS2H total 2→3; shutdown latency ~50ms→≤510ms
- `design/Standards/Certification_Evidence.md`
  - TPD2E2U06 package SON-6→SOT-553; battery 16.8V→16.4V in §3.1
- `.copilot/plan.md`
  - Canonical session plan (in repo root, gitignored)
  - Needs updating after R33/R34 clean and checkpoint save
- `.copilot/checkpoints/` (index + 001 + 002)
  - Checkpoint history; needs `003-encoder-complete.md` added after clean passes
</important_files>

<next_steps>
Remaining work:

1. **Launch R33** — first clean pass attempt. Must include explicit instruction: "ERJ-3EKF2100V IS CORRECT for R_ILIM — do NOT suggest ERA-3ARB2100V."
2. **If R33 clean → launch R34** (second consecutive clean pass)
3. **If R33 has findings** → fix, then R34+R35 until two consecutive clean
4. **After two consecutive clean passes:**
   - Add Design_Log entry marking Encoder detailed design complete (new DEC entry or status note)
   - Update `.copilot/plan.md`: Encoder → ✅ Complete, next phase = Rotor
   - Save checkpoint `003-encoder-complete.md` to `.copilot/checkpoints/`
   - Update `.copilot/checkpoints/index.md`
5. **Rotor detailed design review** — next major phase

Open questions for user (none blocking — keeping list):
- Shutdown daemon latency: changed ~50ms→≤510ms autonomously; confirm this matches user's expectation for the power management spec. If faster response needed, POLL_HZ could be increased.
</next_steps>
