thepinkmile/Enigma-NG/.copilot/checkpoints/006-r43-r47-fixes-review-cycle-con.md

<overview>
This session continued the Enigma-NG electronics design documentation review cycle, targeting two consecutive clean deep-dive review passes to formally close the Encoder detailed design phase. The approach was to fix each round's findings, commit, then re-run until two successive passes returned zero findings. The session ran rounds R43 through R47, applying fixes after each non-clean pass.
</overview>

<history>
1. **Session resumed — R43 agent was already running at compaction**
   - Read R43 results: 2 findings
     - Finding 1/1a: Extension board stale U1 = SN74LVC2G125DCUR buffer present in Design_Spec.md (FR-EXT-01/02, DR-EXT-04/05/06, §1, §2, §4, §6 BOM) and Board_Layout.md ASCII art — contradicts Consolidated_BOM EXT=dash and JTAG_Integrity §7.4
     - Finding 2/2a/2b: RC τ unit error — 82.0kΩ × 22nF = 1.804ms (not µs) in Cert_Evidence §3.3.3, PM BOM C29/R26, and PM §6 notes
   - Applied all fixes (complex multi-edit to Extension Design_Spec.md and Board_Layout.md; 4 µs→ms fixes)
   - Ran markdownlint --fix (auto-fixed MD004/MD032 in Encoder/Design_Spec.md and others)
   - Committed `1155015`
   - Launched R44
2. **R44 completed — 1 finding**
   - Finding: Encoder/Design_Spec.md §3 signal flow code block referenced "Stator J2" (which is the Power connector, not ENC data). Should be "Stator J4/J5/J6, via J2 pin 2–7" / "Stator J4/J5/J6, via J2 pin 19–24"
   - Fixed and committed `c6daedb`
   - Launched R45
3. **R45 completed — 3 findings**
   - Finding 1: Design_Log OWI-003 listed "Reflector (×1)" as a CPLD-owning board — Reflector is fully passive (no CPLD)
   - Finding 2: Design_Log DEC-017 stated Controller Board is the "sole exception" to the 4-layer rule — Power Module also uses JLC06161H-2116 (6-layer)
   - Finding 3: Cert_Evidence §3.4 load budget still had stale "Extension buffers (10mA)" row item (Extension board is passive); sum wrong (2,117mA → should be 2,107mA / 2.11A / 70.4%)
   - All three fixed and committed `fb8e3b9`
   - Launched R46
4. **R46 completed — 1 finding**
   - Finding: Consolidated_BOM 0.1µF X7R 0402 decoupling cap row: EXT=1, Total=508 — stale from before C6 (U1 bypass) was deleted from Extension board
   - Fixed: EXT=—, Total=507
   - Committed `a68d373`
   - Launched R47
5. **R47 completed — 2 findings** (session is mid-fix at compaction)
   - Finding 1: Cert_Evidence §3.5 peak load budget arithmetic error — rows sum to 8.76A (with corrected LDO) but total stated as 9.05A
   - Finding 2: Cert_Evidence §3.5 component utilisation table LDO row shows 2.20A/73.3% — stale; §3.4 (known-correct) gives 2.11A/70.4%
   - Fix in progress: need to update §3.5 peak load table, component utilisation table, LMQ † note, and eFuse calculation note with recalculated figures
</history>

<work_done>
Files modified this session:

- `design/Electronics/Extension/Design_Spec.md` — §1 overview rewritten (no buffer); FR-EXT-01 updated, FR-EXT-02 deleted; DR-EXT-04/DR-EXT-06 deleted, DR-EXT-05 renamed; §2 JTAG buffering section replaced with pass-through note; §4 U1 bypass note removed; BOM rows C6 and U1 deleted; trace width table U1 VCC row deleted
- `design/Electronics/Extension/Board_Layout.md` — JTAG BUFFER (U1) removed from ASCII art; U1 VCC trace width row deleted from §9
- `design/Standards/Certification_Evidence.md` — §3.3.3: 1.804µs→1.804ms with clarifying note; §3.4 load budget: Extension buffers (10mA) row removed, sum corrected to 2,107mA/2.11A/70.4%
- `design/Electronics/Power_Module/Design_Spec.md` — BOM C29/R26 annotations: 1.804µs→1.804ms; §6 notes: 1.804µs→1.804ms
- `design/Electronics/Encoder/Design_Spec.md` — §3 signal flow: "Stator J2" → "Stator J4/J5/J6, via J2 pin 2–7/19–24"; markdownlint --fix applied (asterisks→dashes, blank lines around lists)
- `design/Design_Log.md` — OWI-003: Reflector removed from CPLD boards list; DEC-017: Controller+PM both named as 6-layer exceptions; DEC-017 "already compliant" table: PM row added; markdownlint blank-line fix
- `design/Electronics/Consolidated_BOM.md` — 0.1µF X7R 0402 row: EXT 1→—, Total 508→507
- `design/Software/Linux_OS/Power_Management.md` — markdownlint blank-line fix (minor)
- `.copilot/agent-prompts/r44-review-prompt.txt` through `r47-review-prompt.txt` — created

Commits this session:
- `1155015` — R43 fixes (Extension U1 buffer removed, RC τ µs→ms)
- `c6daedb` — R44 fix (Encoder signal flow connector reference)
- `fb8e3b9` — R45 fixes (OWI-003 Reflector, DEC-017 PM exception, Cert load budget)
- `a68d373` — R46 fix (Consolidated BOM 0.1µF EXT count)

Work completed:
- [x] R43 findings fixed
- [x] R44 finding fixed
- [x] R45 findings fixed
- [x] R46 finding fixed
- [ ] R47 findings to fix — IN PROGRESS
- [ ] R48 second consecutive clean pass — pending
- [ ] Encoder marked complete in Design_Log
- [ ] Checkpoint saved to `.copilot/checkpoints/`
- [ ] `.copilot/plan.md` updated
- [ ] Begin Rotor detailed design review
</work_done>

<technical_details>
**R47 findings — fix required before R48:**

Finding 1+2 are both in `design/Standards/Certification_Evidence.md §3.5` (lines ~249–278).

Correct recalculated values (using 2.11A LDO, rows sum properly):
- LDO input row (line 256): `2.20A` → `2.11A`; note: `2,117mA → 2.20A` → `2,107mA → 2.11A`
- Total peak row (line 257): `9.05A` → `8.76A`; `75.4%` → `73.0%` (of 12A Buck)
- LMQ utilisation row (line 263): `9.05A` → `8.76A`; `75.4% ✓ †` → `73.0% ✓` (within policy — remove †)
- LDO utilisation row (line 264): `2.20A` → `2.11A`; `73.3%` → `70.4%`
- eFuse row (line 265): `4.82A*` → `4.67A*`; `68.9%` → `66.7%`
- † note (lines 269–271): Remove exceedance note entirely — 73.0% is within ≤75% policy
- * eFuse footnote (lines 273–275): Recalculate with 8.76A base:
  - Worst case (12V PoE, with supercap charge 1A): (8.76+1)×5 / (0.87×12) = 48.8W/10.44 = **4.67A** → 4.67/7 = **66.7%**
  - Steady state: 8.76×5/(0.87×12) = 43.8/10.44 = **4.20A** → 4.20/7 = **60.0%**
  - At 15V USB-C: 48.8W/15 = **3.25A** → 3.25/7 = **46.4%** (or recalc: 56.1W/15 = 3.74A → 53.4%)
- Line 277–278 (PoE peak supercap charge note): `9.05A` → `8.76A`; recalculate 9.55A → 9.26A; 54.9W → 53.2W; 54.9/72 → 53.2/72 = 73.9%

**Key architectural facts (verified/corrected this session):**
- Extension board: fully passive pass-through — NO U1 buffer, NO C6, FR-EXT-02 deleted, DR-EXT-04/DR-EXT-06 deleted
- RC delay τ: 82.0kΩ × 22nF = 1.804ms (confirmed; previous µs annotation was 1000× error)
- DEC-017 exceptions: BOTH Controller (high-speed) AND Power Module (high-current) use JLC06161H-2116 6-layer
- CPLD boards: Encoder (×2), Stator (×1), Rotor (×30) = 37 total. Reflector has NO CPLD.
- 0.1µF X7R 0402 system total: 507 (not 508; C6 deleted from Extension)
- Cert_Evidence §3.4 3V3_ENIG load: 2,107mA → 2.11A → 70.4% (KNOWN CORRECT since R45)
- Cert_Evidence §3.5 still has stale 2.20A/9.05A values — R47 fix pending

**Session state location:** repo-local `.copilot\`
**Resume phrase:** "Please read `.copilot/plan.md` and all files in `.copilot/checkpoints/` to align yourself with the current project state, then continue from where we left off."

**markdownlint toolchain:**
- Requires PATH refresh: `$env:PATH = [System.Environment]::GetEnvironmentVariable("PATH","Machine")+";"+[System.Environment]::GetEnvironmentVariable("PATH","User")`
- Run: `.\node_modules\.bin\markdownlint.cmd --fix "design/**/*.md"` then re-run without `--fix`
- Remaining pre-existing MD013/line-length errors (can't be auto-fixed, in long bullet/blockquote lines, not from our edits): Consolidated_BOM lines 195–196, PM Design_Spec line 489, User_Manual line 134, Power_Management line 215, Global_Routing_Spec line 72

**Agent prompt files:**
- Backtick characters in task agent prompts cause "Unterminated string in JSON" — save prompts to `.copilot/agent-prompts/*.txt` and reference by path
- R47 prompt: `.copilot/agent-prompts/r47-review-prompt.txt`
- R48 prompt: needs to be created based on r47 prompt with R47 known-correct items added
</technical_details>

<important_files>
- `design/Standards/Certification_Evidence.md`
  - Central certification evidence document; §3.3.3, §3.4, §3.5 all modified this session
  - **NEEDS FURTHER EDIT (R47 fix):** §3.5 lines 249–278: update LDO row (2.20A→2.11A), total (9.05A→8.76A), LMQ utilisation (75.4%→73.0%), eFuse row (4.82A/68.9%→4.67A/66.7%), remove † exceedance note, recalculate * eFuse footnote with 8.76A base, recalculate PoE supercap charge note
  - Lines 249–278 are the focus of R47 fixes
- `design/Electronics/Extension/Design_Spec.md`
  - Extension board specification; fully cleaned of U1 buffer references this session
  - All stale FR/DR/BOM/§2/§4 U1 content removed; board correctly documented as passive pass-through
- `design/Electronics/Extension/Board_Layout.md`
  - U1 JTAG BUFFER removed from ASCII art and trace width table
- `design/Design_Log.md`
  - Master decision log; DEC-001–DEC-025 all use canonical format
  - OWI-003 corrected (no Reflector); DEC-017 updated (PM added as 6-layer exception)
- `design/Electronics/Consolidated_BOM.md`
  - System-wide component count table; 0.1µF row corrected to EXT=—, Total=507
- `design/Electronics/Encoder/Design_Spec.md`
  - §3 signal flow code block fixed; markdownlint style fixes applied (asterisks→dashes)
- `.copilot/agent-prompts/r47-review-prompt.txt`
  - Contains full KNOWN CORRECT list through R46 fixes; base for R48 prompt
- `.copilot/plan.md`
  - Session plan (may need update after cycle closes)
</important_files>

<next_steps>
**Immediate — R47 fixes (in progress):**

Fix `design/Standards/Certification_Evidence.md §3.5` lines 249–278:

1. LDO input row (line 256): `2.20A` → `2.11A`; note `2,117mA → 2.20A` → `2,107mA → 2.11A`
2. Total peak row (line 257): `**9.05A**` → `**8.76A**`; `**75.4%**` → `**73.0%**`
3. LMQ utilisation row (line 263): `9.05A` → `8.76A`; `**75.4%** ✓ †` → `**73.0%** ✓`
4. LDO utilisation row (line 264): `2.20A` → `2.11A`; `**73.3%**` → `**70.4%**`
5. eFuse utilisation row (line 265): `4.82A*` → `4.67A*`; `**68.9%**` → `**66.7%**`
6. Lines 269–271: Remove † exceedance note (73.0% is within ≤75% policy)
7. Lines 273–275 (* eFuse footnote): Replace 9.05A with 8.76A throughout; recalculated values:
   - Worst case (12V PoE + 1A supercap): (8.76+1)×5/(0.87×12) = 48.8/10.44 = **4.67A** → **66.7%**
   - Steady state: 8.76×5/(0.87×12) = 43.8/10.44 = **4.20A** → **60.0%**
   - At USB-C 15V: 48.8/15 = **3.25A** → **46.4%**
8. Lines 277–278 (PoE supercap charge note): `9.05A` → `8.76A`; `9.55A` → `9.26A`; `9.55A × 5V / 0.87 = 54.9W` → `9.26A × 5V / 0.87 = 53.2W`; `54.9W / 72W = 76.2%` → `53.2W / 72W = 73.9%`

Then: lint, commit, create R48 prompt (add R47 fixes to KNOWN CORRECT), launch R48.

**After two consecutive clean passes:**
1. Add INC entry to Design_Log.md marking Encoder detailed design phase complete
2. Update `.copilot/plan.md`: Encoder → complete, next = Rotor detailed design review
3. Save checkpoint 006 to `.copilot/checkpoints/006-encoder-review-complete.md`
4. Update `.copilot/checkpoints/index.md`
5. Begin Rotor detailed design review
</next_steps>
