thepinkmile/Enigma-NG/.copilot/checkpoints/012-controller-sanity-enc-in-fix.md

# Checkpoint 012 — Controller Sanity Check, ENC_IN Direction Fix
**Date:** 2026-04-10
**Session:** Prior session (stub — original file not committed to repo)

---
## Overview
Controller Board sanity check complete. ENC_IN signal direction corrected (was described as
output, is input). GPIO mapping confirmed: GPIO 20=SW_LED_CTRL, GPIO 24=POE_STAT (active-low).
No other issues found during Controller review. Board marked complete.
## Key Decisions
- ENC_IN on Controller is input (receives from Keyboard CPLD) — direction bug corrected
- GPIO 20/24 assignment confirmed correct and propagated to all files
