thepinkmile/Enigma-NG/.copilot/checkpoints/051-final-review-fixes-locked-and-rerun.md

# Checkpoint 051 — Final review fixes locked and rerun prepared
## Date
2026-04-18
## Overview
This checkpoint locks the small final cleanup batch that followed the second deep-design rerun. The
remaining active-doc inconsistencies were corrected so the live design state now consistently reflects
the clarified grounding policy, the grouped-power LINK-BETA allocation, and the `5V_MAIN` naming used
for the Settings/Stator harness power feed.

This checkpoint also records that the two redundant local datasheets flagged by the audit were removed
from `design/Datasheets/`, while the remaining missing local datasheets are unchanged and already
tracked in `.copilot/components-todo.md`.
## Work Done
### Final active-doc consistency fixes
- Updated `Stator/Board_Layout.md` and `Settings_Board/Board_Layout.md` so harness pin 3 is described
  as **logic return only** and explicitly **not** a local `GND_CHASSIS` bond
- Replaced the lingering `5V_LED` wording in `Consolidated_BOM.md` with `5V_MAIN`
- Corrected the high-level LINK-BETA summary in `Controller/Design_Spec.md` so it now describes the
  actual interface: **JTAG, I2C-1 extension, grouped `5V_MAIN`, and `3V3_ENIG`**
- Corrected `Controller/Board_Layout.md` so the LINK-BETA pass-through note matches the active
  **11-pin `3V3_ENIG`** grouping rather than the stale 8-pin wording
### Datasheet tracking state synced
- Confirmed the latest datasheet-rerun "missing local datasheets" list is the same list already tracked
  in `.copilot/components-todo.md`
- Captured the removal of the now-redundant local PDFs:
  - `design/Datasheets/B4B-PH-datasheet.pdf`
  - `design/Datasheets/TE-1-1452688-2-datasheet.pdf`
### Repo-local handoff synced
- Updated `.copilot/plan.md` to reflect the current locked state after the final review-fix batch
- Added this checkpoint and indexed it in `.copilot/checkpoints/index.md`
- Preserved the earlier superseded `.copilot/files/...` notes as historical-only artifacts rather than
  active design truth
## Validation
- `markdownlint` run completed clean on the touched active docs
- Targeted text sweep found no remaining matches for the stale phrases fixed in this batch
## Commits
- Pending at checkpoint write time; the next commit locks this checkpoint plus the synced repo-local
  handoff and datasheet removals
## Key Technical Notes
### Grounding rule applied consistently
The Settings/Stator harness `GND` pins are logic returns only. They must not be described as local
`GND_CHASSIS` tie points because the only galvanic `GND` ↔ `GND_CHASSIS` bond remains on the Power
Module near system power entry.
### LINK-BETA summary now matches the detailed pin map
Future sessions should treat the high-level Controller narrative and the detailed Board Layout table as
aligned:

1. `5V_MAIN` grouped on pins **14–17**
2. `GND` on **18** and **22–24**
3. additional `3V3_ENIG` on **19–21**
4. upper data block and JTAG mapping unchanged
## Next Steps
1. Create the locking commit for this cleanup batch and synced repo-local handoff
2. Re-run the two one-off review agents from this frozen state
3. Review any remaining findings before deciding whether another fix batch is needed
## Files Updated
- `.copilot/checkpoints/index.md`
- `.copilot/checkpoints/051-final-review-fixes-locked-and-rerun.md`
- `.copilot/plan.md`
- `design/Datasheets/B4B-PH-datasheet.pdf` (removed)
- `design/Datasheets/TE-1-1452688-2-datasheet.pdf` (removed)
- `design/Electronics/Consolidated_BOM.md`
- `design/Electronics/Controller/Board_Layout.md`
- `design/Electronics/Controller/Design_Spec.md`
- `design/Electronics/Settings_Board/Board_Layout.md`
- `design/Electronics/Stator/Board_Layout.md`
