thepinkmile/Enigma-NG/.copilot/checkpoints/068-copilot-markdown-lint-fixes.md

# Checkpoint 068 — Markdown lint fixes for .copilot/ and Stator spec

## Summary

Completed markdown lint cleanup for all .copilot/ files, following the
Category A deep-review commit (959757a).

## What was done

- .copilot/review-report.md: fixed ~80 MD036 violations (emphasis-only
  paragraphs converted to ####  headings), wrapped ~51 MD013 long lines at
  200-char boundary, and removed trailing . from the converted #### Not clean
  / #### Clean headings (MD026).
- .copilot/checkpoints/index.md: fixed MD060 table separator row — added
  spaces around dashes (| --- | ------- | ------ |).
- .copilot/handoff.md and checkpoints/067-*.md: already auto-fixed in the
  prior session run; staged and committed here.
- design/Electronics/Stator/Design_Spec.md: user-applied manual lint fix
  included in the same commit.

## Commit

7b8f775 — Fix markdown lint errors in .copilot/ and Stator design spec

## Workaround note

.markdownlintignore contains .copilot/**. To lint .copilot/ files, use:

    .\node_modules\.bin\markdownlint.cmd --ignore-path ".\tmp_empty_ignore.txt" --dot ".copilot/file.md"

where 	mp_empty_ignore.txt is a temporary empty file (delete after use).

## Status

All .copilot/ markdown files now lint-clean. Temp files cleaned up.
